femtoduino/femto-beacon/Eagle_Files/FemtoBeacon_r2.0.0/femto-beacon-picture.jpg

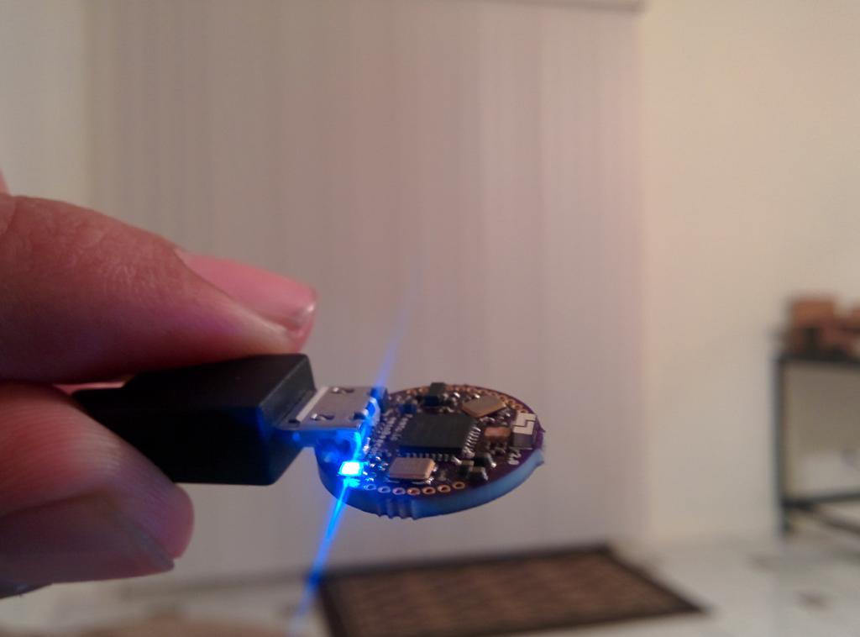
Eagle_Files/FemtoBeacon_r2.0.0/femto-beacon-picture.jpg
