femtoduino/femto-beacon/Blender3d_Files/femtoBeacon_r2.0.3_MolexAnt.png

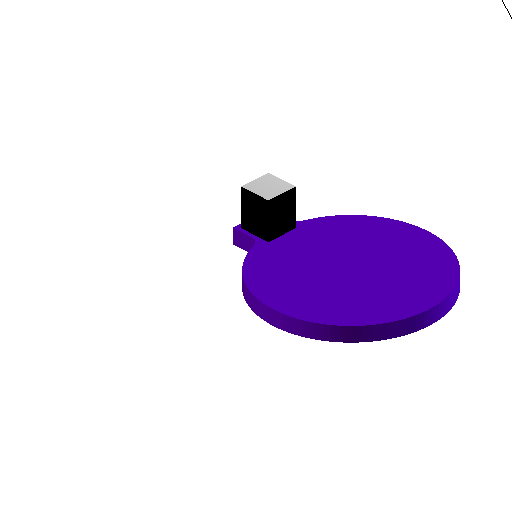
Blender3d_Files/femtoBeacon_r2.0.3_MolexAnt.png
