femtoduino/femto-beacon/Blender3d_Files/MolexAnt_Texture.png

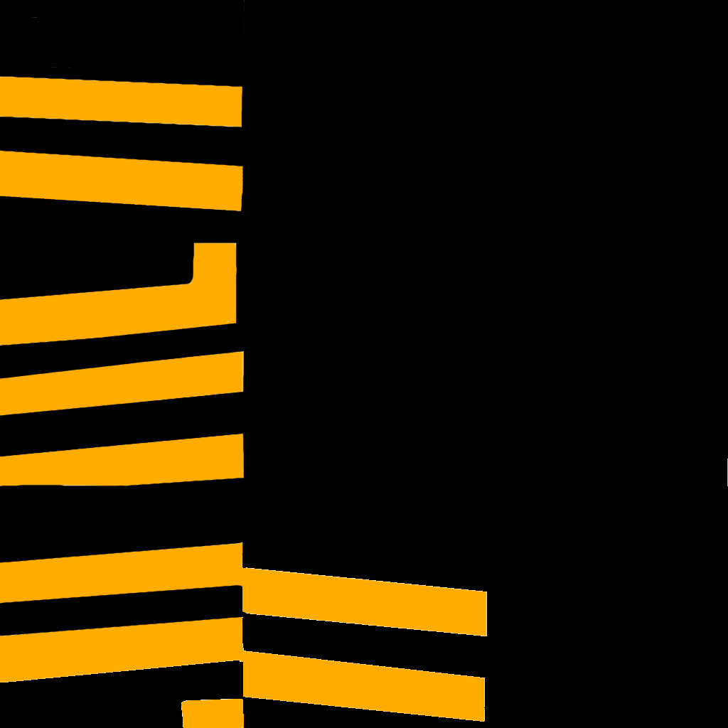
Blender3d_Files/MolexAnt_Texture.png
