femtoduino/femto-beacon/Eagle_Files/FemtoBeacon_BLE_r1.0.0/femtoBeacon_BT_art0.png

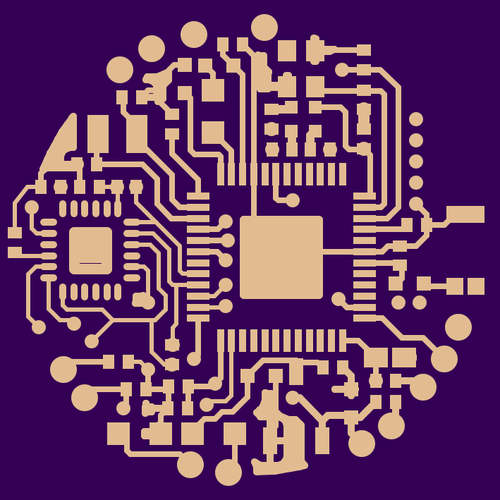
Eagle_Files/FemtoBeacon_BLE_r1.0.0/femtoBeacon_BT_art0.png
