femtoduino/femto-beacon/Eagle_Files/FemtoBeacon_BLE_r1.0.0/FemtoBeacon_coin_nRF52832_BT4.2_r1.0.0_top.png

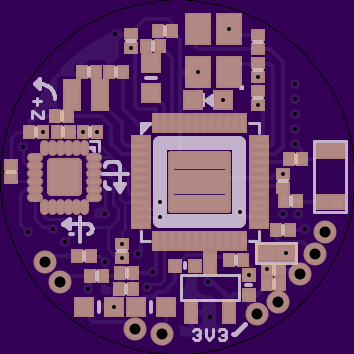
Eagle_Files/FemtoBeacon_BLE_r1.0.0/FemtoBeacon_coin_nRF52832_BT4.2_r1.0.0_top.png
