femtoduino/femto-beacon/Eagle_Files/FemtoBeacon_BT5_r1.0.0/FemtoBeacon_BT5_r1.0.1-top.png

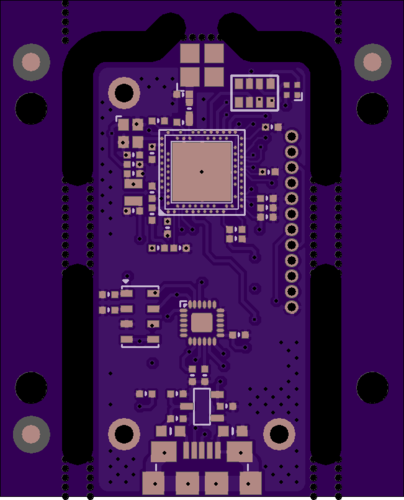
Eagle_Files/FemtoBeacon_BT5_r1.0.0/FemtoBeacon_BT5_r1.0.1-top.png
