femtoduino/femto-beacon/Eagle_Files/FemtoBeacon_r2.0.0/femtoBeacon_dongle_r2.0.6_RGB_PANELIZED-top.png

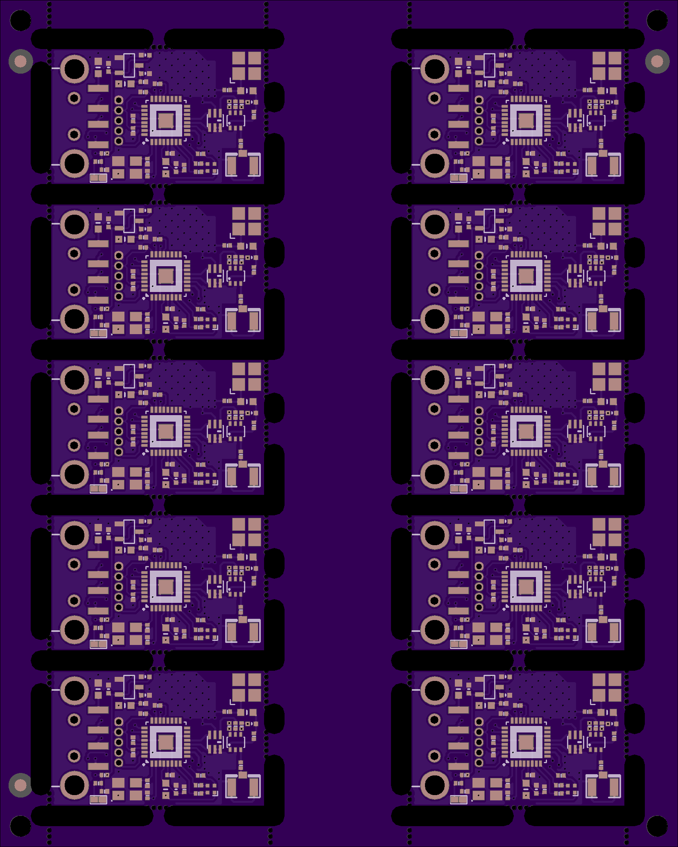
Eagle_Files/FemtoBeacon_r2.0.0/femtoBeacon_dongle_r2.0.6_RGB_PANELIZED-top.png
