femtoduino/femto-beacon/Eagle_Files/FemtoBeacon_r2.0.0/femtoBeacon_PRO_r3.0.0-top.png

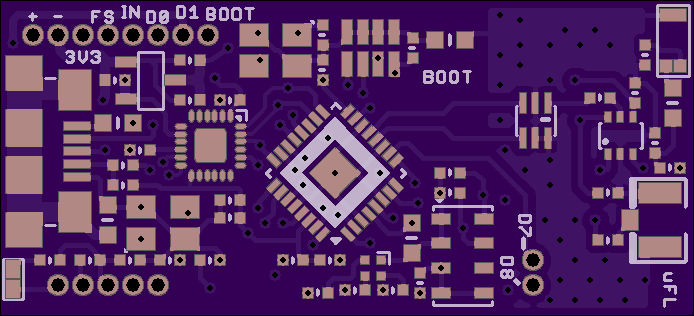
Eagle_Files/FemtoBeacon_r2.0.0/femtoBeacon_PRO_r3.0.0-top.png
