femtoduino/femto-beacon/Eagle_Files/FemtoBeacon_r2.0.0/femtoBeacon_r2.0.0-bottom.png

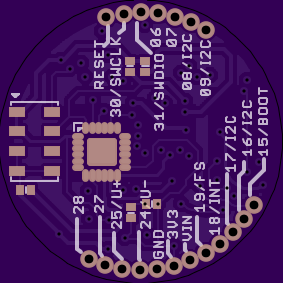
Eagle_Files/FemtoBeacon_r2.0.0/femtoBeacon_r2.0.0-bottom.png
