femtoduino/femto-beacon/Eagle_Files/FemtoBeacon_r2.0.0/femtoBeacon_r2.0.0-top.png

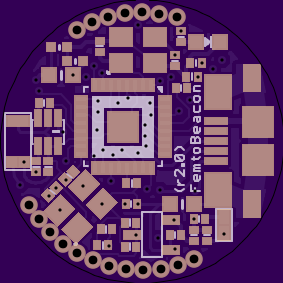
Eagle_Files/FemtoBeacon_r2.0.0/femtoBeacon_r2.0.0-top.png
