femtoduino/femto-beacon/Eagle_Files/FemtoBeacon_r2.0.0/femtoBeacon_r2.0.7_RGB_OTG_PANELIZED-top.png

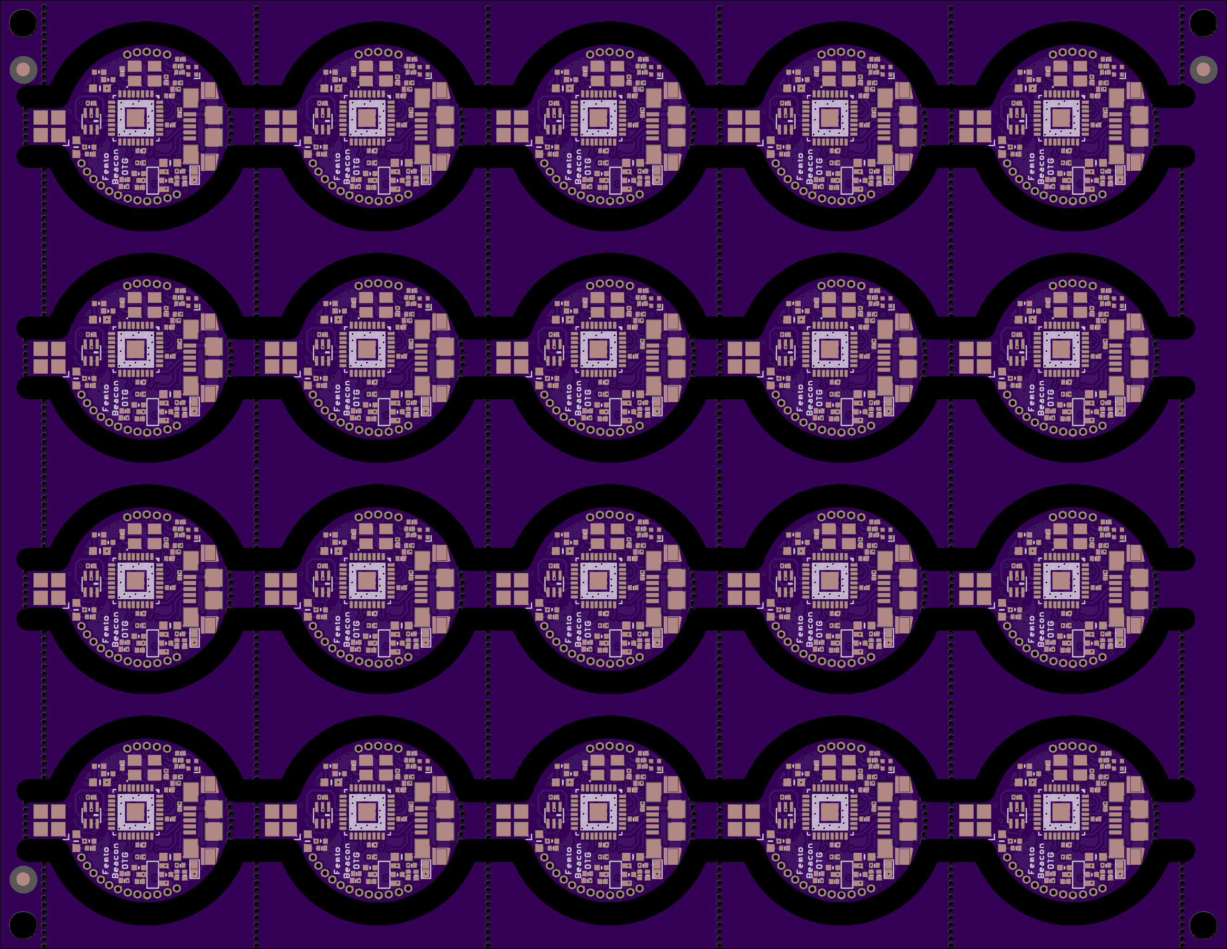
Eagle_Files/FemtoBeacon_r2.0.0/femtoBeacon_r2.0.7_RGB_OTG_PANELIZED-top.png
