femtoduino/femto-beacon/examples/sam-r21-blink/sam0/drivers/dac/docimg/dac_block_diagram_saml.gif

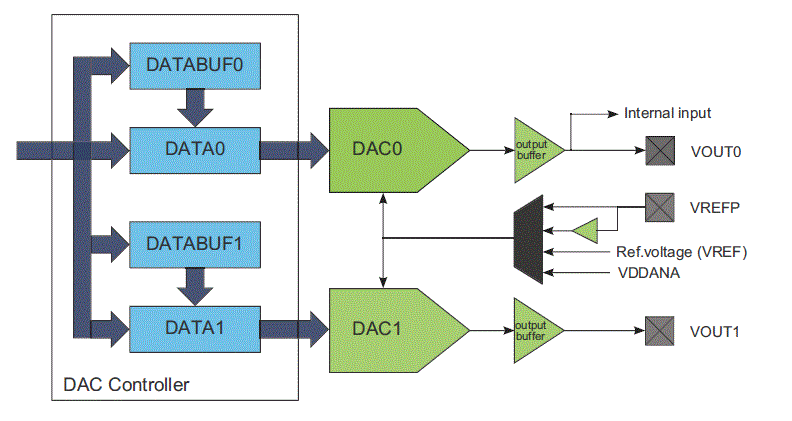
examples/sam-r21-blink/sam0/drivers/dac/docimg/dac_block_diagram_saml.gif
