femtoduino/femto-beacon/Nordic_Files/nRF52 Preview Development Kit - Hardware files 1_1_0/PCA10036-nRF52832 Bluetooth Smart,ANT,2.4GHz RF Preview Development Board 1_1_0/Production files/BOM/PCA10036_BOM.xls

Bill of material
PCB: | PCA10036
Version: | 1.1.0
Designator | Value | Description | Footprint Doc | Manufacturer | Manufacturer Part Number
Bat1 | Bat Holder CR2032 | Bat Holder CR2032 SMD | CR2032_HOLDER_SMD | Keystone | 3002
C1, C2, C11, C12 | 12pF | Capacitor, NP0, ±2% | 0402
C3 | 0.8pF | Capacitor, NP0, ±5% | 0402
C4, C5, C8, C18, C19, C21, C24, C25, C26, C27, C28, C29, C32, C34, C35, C36, C38, C39, C40, C41, C44, C45, C46, C47 | 100nF | Capacitor, X7R, ±10% | 0402
C6, C13 | N.C. | Not mounted | 0402
C7 | 100pF | Capacitor, NP0, ±5% | 0402
C9 | 4.7µF | Capacitor, X5R, ±10% | 0603
C10, C16, C17 | 1.0µF | Capacitor, X7R, ±10% | 0603
C15 | 1.2pF | Capacitor, NP0, ±0.1pF | 0402
C20, C31, C33 | 10µF | Capacitor, X5R, ±20% | 0603
C22, C23 | 18pF | Capacitor, NP0, ±5% | 0402
C30 | 10nF | Capacitor, X7R, ±10% | 0402
C37 | 10pF | Capacitor, NP0, ±2% | 0402
C42, C43 | 130pF | Capacitor, NP0, ±5% | 0402
C48, C49, C50, C51 | 1.0µF | Capacitor, X5R, ±5% | 0402
D1 | SD103ATW-7-F | Surface Mount Schottky Barrier Diode Array | SOT-363 | Diodes Incorporated | SD103ATW-7-F
D2 | PRTR5V0U2X | Ultra low capacitance double rail-to-rail ESD protection diode | SOT-143B | NXP | PRTR5V0U2X
D3, D4, D5, D6 | 1PS79SB30.115 | Diode Schottky Vf=0.38, Vr=40V, If=200mA, Ir=500nA | SOD-523 | NXP | 1PS79SB30.115
J1 | MM8130-2600 | Coaxial Connector with Switch | COAXIAL-SWF | Murata | MM8130-2600
J2 | MicroUSB-B | MicroUSB-B-SMT | FCI_10118193-0001LF | FCI | 10118193-0001LF
L1 | 3.9nH | Inductor, 170mA, ±0.1nH | 0402 | Murata | LQP15MN3N9B02D
L2 | 10µH | Inductor, 80mA, ±10% | 0603 | Taiyo Yuden | LBMF1608T100K
L3 | 15nH | Inductor, 320mA, ±5% | 0402 | Taiyo Yuden | HK100515NJ-T
LD5 | LTST-C195KGJRKT | Ultra bright AlInGaP Bi-Color LED | LED_DUAL_0606 | Lite-On Inc | LTST-C195KGJRKT
LED1, LED2, LED3, LED4 | L0603G | LED 0603, EL19-21SYGC | 0603 | Everlight | 19-21SYGC/S530-E1/TR8
P1, P3 | Socket 1x8 | Socket 1x8, 2.54mm (100mil), SMD | SOCKET_1x8_SMD | Samtec | SSM-108-F-SV-P-TR
P2 | Socket 1x6 | Socket 1x6, 2.54mm (100mil), SMD | SOCKET_1x6_SMD | Samtec | SSM-106-F-SV-P-TR
P4 | Socket 1x10 | Socket 1x10, 2.54mm (100mil), SMD | SOCKET_1x10_SMD | Samtec | SSM-110-F-SV-P-TR
P5 | Pin Hdr 2x3 | Pin Header 2x3, 2.54mm (100mil) SMD | Molex 15-91-2060 | Molex | 15-91-2060
P6 | Socket 1x9 | Socket 1x9, 2.54mm (100mil), SMD | SOCKET_1x9_SMD | Samtec | SSM-109-L-SV
P7, P9, P20 | Pin List 1x8 | Pin List 1x8, 2.54mm (100mil), SMD | LIST_1x8_SMD
P8 | Pin List 1x6 | Pin List 1x6, 2.54mm (100mil), SMD | LIST_1x6_SMD
P10 | Pin List 1x10 | Pin List 1x10, 2.54mm (100mil), SMD | LIST_1x10_SMD
P11 | Socket 2x3 | Socket 2x3, 2.54mm (100mil), SMD | SOCKET_2x3_SMD-2.54mm-bottom | Samtec | SSM-103-F-DV-P-TR
P12 | Pin List 1x9 | Pin List 1x9, 2.54mm (100mil), SMD | LIST_1x9_SMD
P13, P15 | Pin Header 2x8 | Pin Header 2x8, 2.54mm (100mil) | HDR_2x8
P14 | Pin Header 2x6 | Pin Header 2x6, 2.54mm (100mil) | HDR_2x6
P16 | Pin Header 2x10 | Pin Header 2x10, 2.54mm (100mil) | HDR_2x10
P17 | Pin Header 2x9 | Pin Header 2x9, 2.54mm (100mil) | HDR_2x9
P18, P19 | FTSH-105 | SAMTEC - CONN HEADER 10POS DUAL .05" SMD KEYING SHROUD | FTSH-105 | Samtec | FTSH-105-01-F-DV-K
P21, P22 | Pin List 1x2, Angled | Pin List 1x2, 2.54mm (100mil), Right Angled, SMD | LIST_ANG_1x2-SMD-2.54MM
P23 | Pin List 1x2, Angled | Pin List 1x2, 2.00mm, Right Angled, SMD | LIST_ANG_1x2-SMD-2.00MM
Q1, Q2 | FDG6321C | Fairchild, FDG6321C, Dual N & P Channel Digital FET | SC70-6 | Fairchild | FDG6321C
R1, R2, R3, R4, R19, R20 | 220R | Resistor, ±1%, 0.063W | 0402
R5, R8, R9, R10, R11, R12 | 10k | Resistor, ±1%, 0.063W | 0402
R6, R27, R28, R37 | N.C. | Not mounted | 0402
R7 | 47k | Resistor, ±1%, 0.063W | 0402
R13, R14 | 39R | Resistor, ±1%, 0.063W | 0402
R15, R16 | 150R | Resistor, ±1%, 0.063W | 0402
R17 | 6k8 | Resistor, ±1%, 0.063W | 0402
R18 | 1k | Resistor, ±1%, 0.063W | 0402
R21, R22, R23, R24, R29, R30 | 4k7 | Resistor, ±1%, 0.063W | 0402
R25, R26, R38 | 0R | Resistor, ±5%, 0.063W | 0402
R31, R32 | 12k | Resistor, ±1%, 0.063W | 0402
R33, R34, R35, R36 | 100k | Resistor, ±1%, 0.063W | 0402
R39 | 1M0 | Resistor, ±1%, 0.063W | 0402
R40, R41, R42, R43 | 18k | Resistor, ±1%, 0.063W | 0402
SW1, SW2, SW3, SW4, SW5 | PB SW | ALPS - SKHUALE010 - Tactile Switch, SPNO, SMD, 6.5x6.2x2.5mm | ALPS_SKHUxxx010_WO_GND | Alps | SKHUALE010
SW6 | Switch | SMD slide Switch (ON-ON) | JS202011SCQN | C&K Components | JS202011SCQN
U1 | nRF52832-QFAA | Multi-protocol Bluetooth Low Energy and 2.4GHz proprietary system-on-chip | QFN-48 | Nordic Semiconductor | nRF52832-QFAA
U2 | ATSAM3U2CA-AU | IC MCU 32bit 128kB flash 100LQFP | LQFP-100 | Atmel | ATSAM3U2CA-AU
U3 | AP7333-33SAG-7 | 300mA, Low Quiescent Current, Fast Transient Low Dropout Linear Regulator | SOT-23-3 | Diodes Incorporated | AP7333-33SAG-7
U4, U5, U6 | NX3DV2567 | Low-ohmic four-pole double-throw analog switch | XQFN-16 | NXP Semiconductors | NX3DV2567GU
U7 | PCAL6408A | 8-bit I2C-bus I/O expander with interrupt output | XQFN-16 | NXP Semiconductors | PCAL6408AHK
X1 | 32MHz | XTAL SMD 2016, 32MHz, Cl=8pF, Tol: ±10ppm, Stab: ±10ppm | XTAL_2016 | Epson Toyocom | Q22FA12800025
X2 | 32.768kHz | EPSON TOYOCOM - FC-135 32.768KHZ ±20PPM,9.0PF - CRYSTAL, SM, WATCH | XTAL_3215 | Epson Toyocom | FC-135 32.768KHZ ±20PPM,9.0PF
X3 | 12MHz | XTAL SMD 3225, 12MHz, 18pF, ±30ppm | BT-XTAL_3225 | TXC Corporation | 7M-12.000MAAJ-T
