femtoduino/femto-beacon/examples/sam-r21-blink/sam0/drivers/system/docimg/performance_level_transition.gif

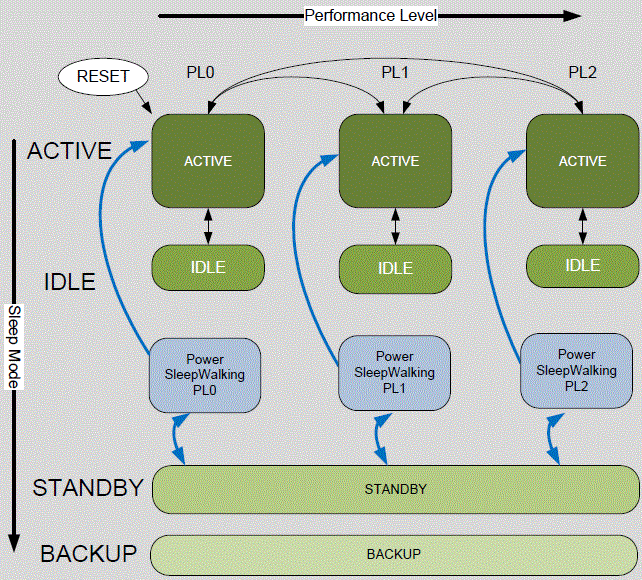
examples/sam-r21-blink/sam0/drivers/system/docimg/performance_level_transition.gif
