femtoduino/femto-beacon/Eagle_Files/FemtoBeacon_BLE_r1.0.0/femtoBeacon_board_nRF52832_BT4.2_r1.0.0.brd

## EAGLE design Eagle_Files/FemtoBeacon_BLE_r1.0.0/femtoBeacon_board_nRF52832_BT4.2_r1.0.0.brd (2018-01-04)

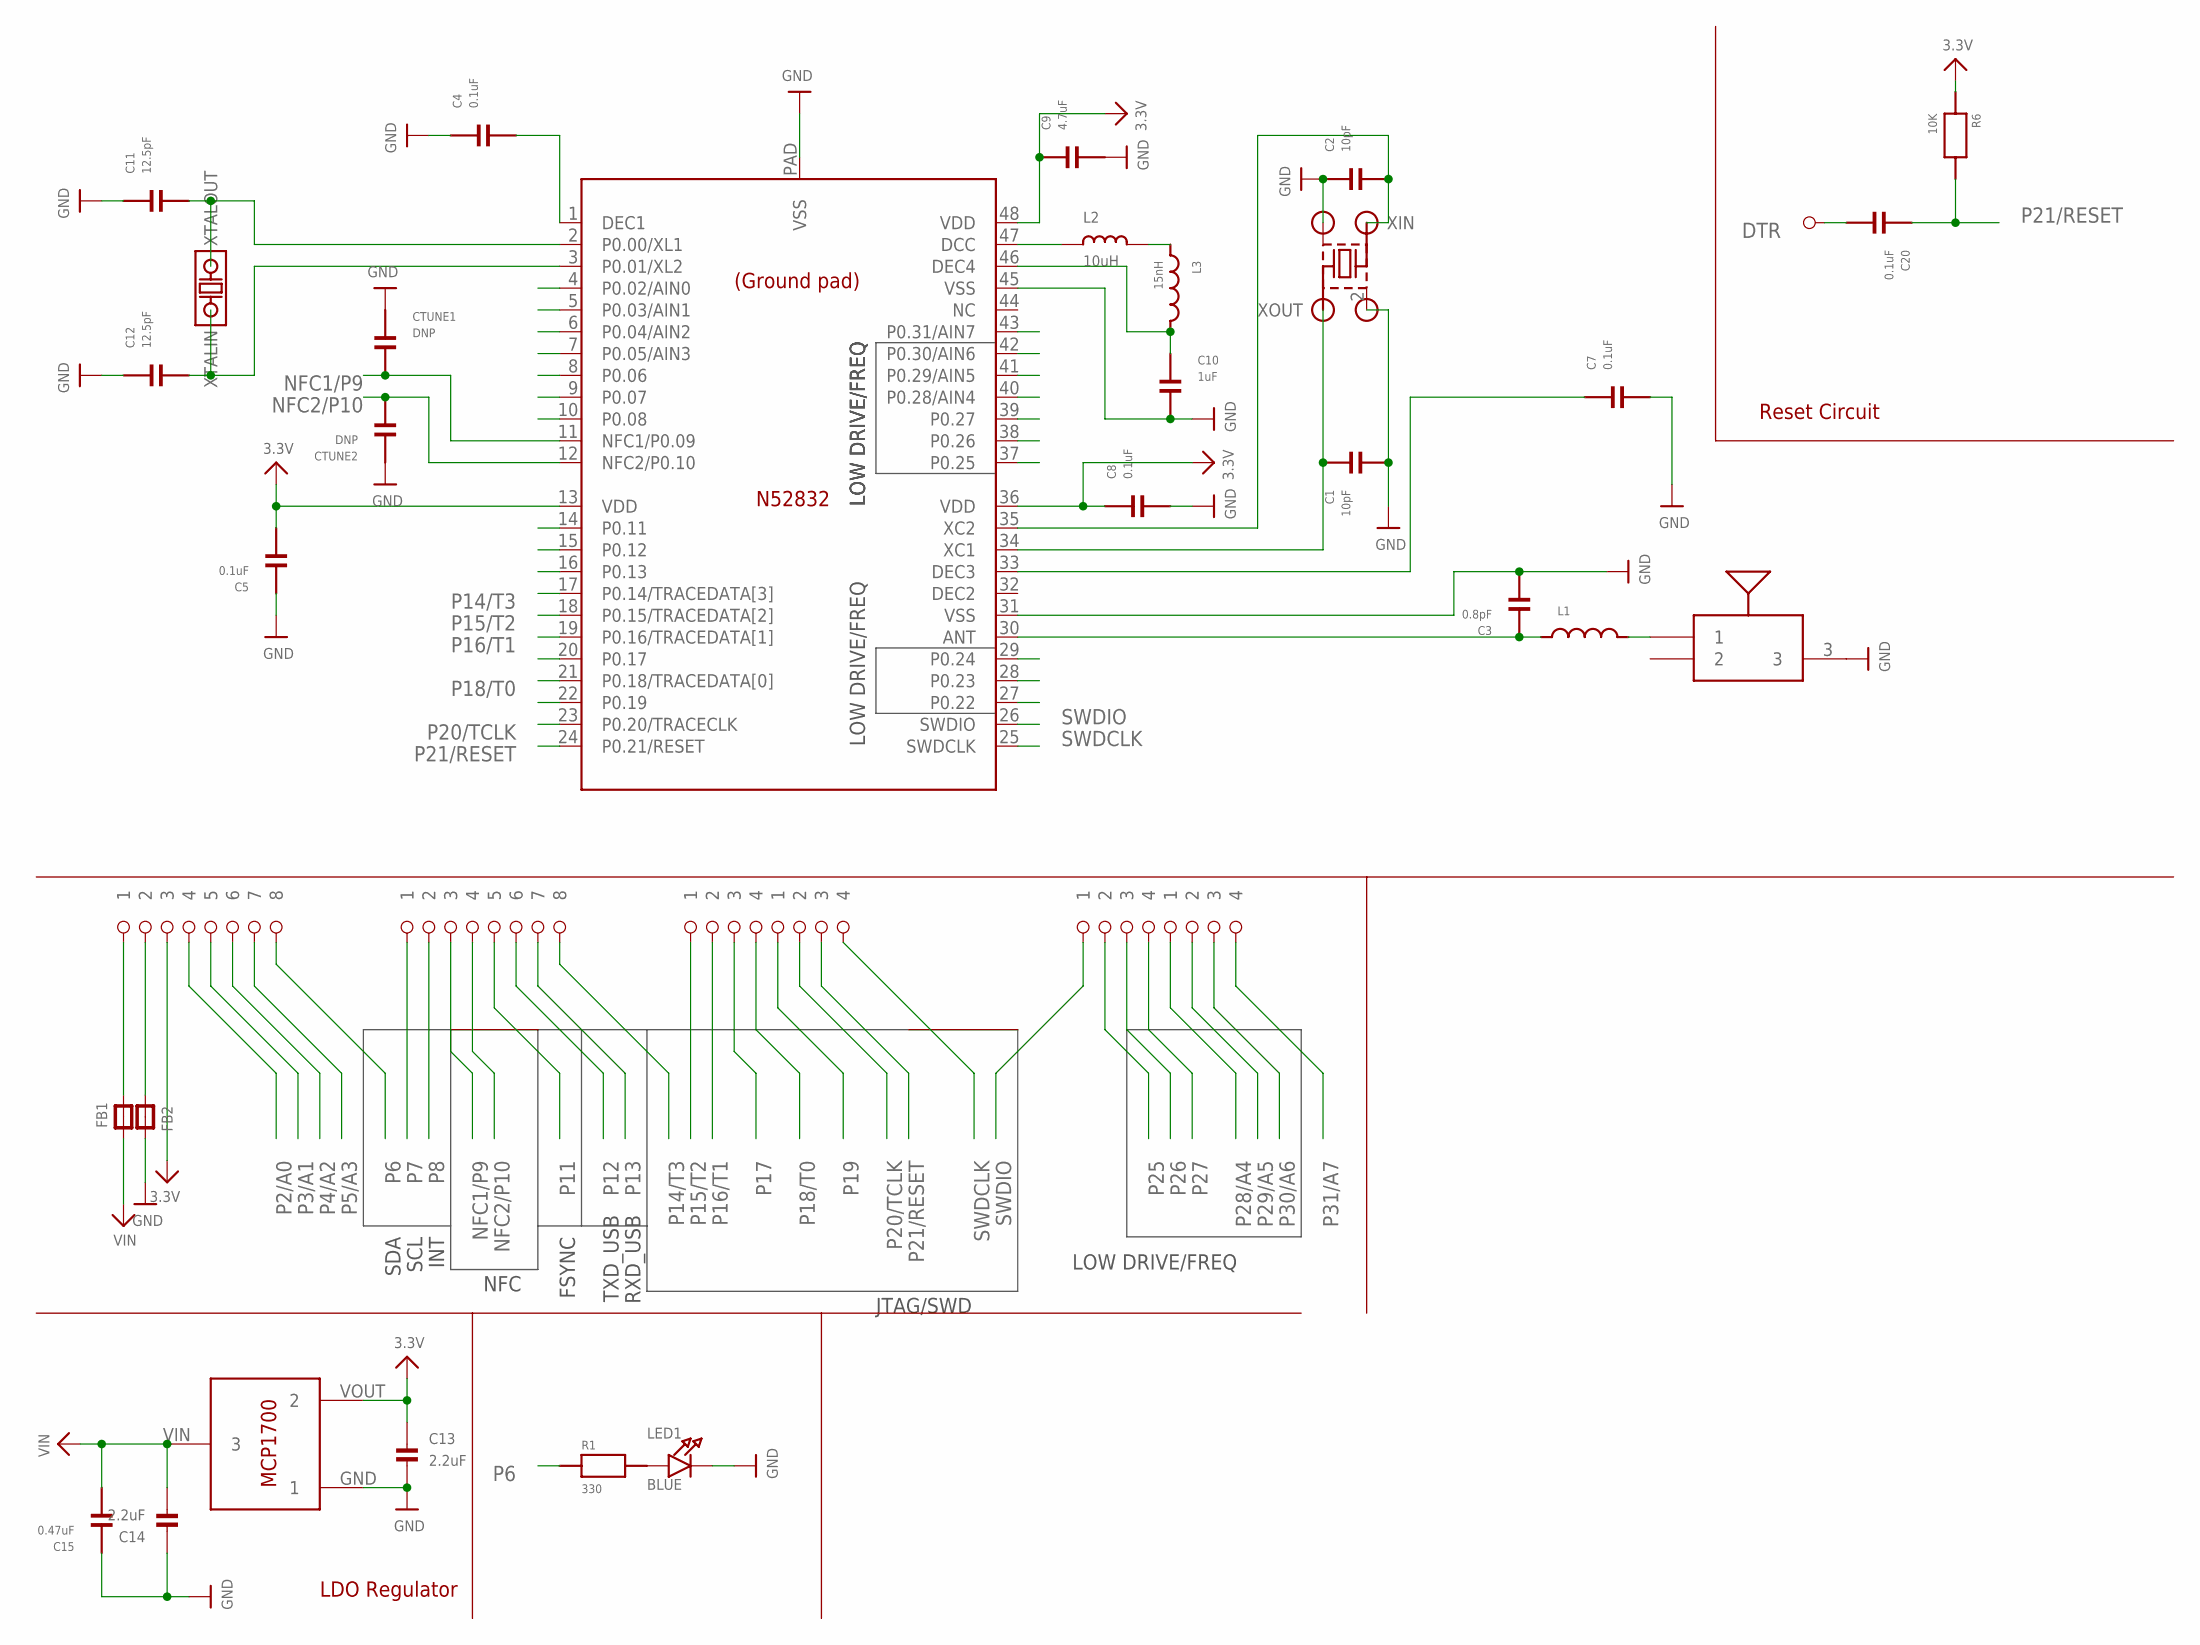
[picture p57: schematic femtoBeacon_board_nRF52832_BT4.2_r1.0.0.sch, sheet 1]

Parts:
ANTBAR: PULSE_ANT_2.4GHZ; ANT_BAR
C1, C2: 10pF; PART
C3: 0.8pF; PART
C4, C5, C7, C8, C20: 0.1uF; PART
C9: 4.7uF; PART
C10: 1uF; PART
C11, C12: 12.5pF; PART
C13, C14: 2.2uF; _0402MP
C15: 0.47uF; PART
CTUNE1, CTUNE2: DNP; PART
FB1, FB2: FERRITE_0603MP; _0603MP
IC1: NRF52832_QFN48; QFN48
L1: INDUCTOR_FIXED_0201; PART
L2: 10uH; _0603MP
L3: 15nH; PART
LED1: BLUE; CHIPLED_0603_NOOUTLINE
PIN4: 1X1_ROUND
PINS1, PINS2: 1X8_ROUND
PINS3A, PINS3B, PINS4A, PINS4B: 1X4_ROUND
R1: 330; PART
R6: 10K; PART
U$4: MCP1700T-3302E/TT
U$53: ABS06-107-32.768KHZ-T
XTAL: 32MHz; ABM11

Connections:
3.3V: C5.2, C8.1, C9.1, C13.1, IC1.13 (VDD), IC1.36 (VDD), IC1.48 (VDD), PINS1.P$3 (3), R6.1, U$4.VOUT (2); also elsewhere on the board
DTR: C20.2, PIN4.P$1
GND: ANTBAR.3, C1.2, C2.1, C3.2, C4.1, C5.1, C7.2, C8.2, C9.2, C10.2, C11.1, C12.1, C13.2, C14.1, C15.1, CTUNE1.1, CTUNE2.1, FB2.2, IC1.31 (VSS), IC1.45 (VSS), IC1.PAD (VSS), LED1.C, U$4.GND (1), XTAL.2 (GND), XTAL.4 (GND); also elsewhere on the board
unnamed: C4.2, IC1.1 (DEC1)
unnamed: L2.2, L3.1
unnamed: IC1.47 (DCC), L2.1
unnamed: C7.1, IC1.33 (DEC3)
unnamed: FB2.1, PINS1.P$2 (2)
unnamed: C10.1, IC1.46 (DEC4), L3.2
unnamed: LED1.A, R1.2
unnamed: FB1.2, PINS1.P$1 (1)
unnamed: C3.1, IC1.30 (ANT), L1.1
NFC1/P9: CTUNE1.2, IC1.11 (NFC1/P0.09), PINS2.P$3 (3)
NFC2/P10: CTUNE2.2, IC1.12 (NFC2/P0.10), PINS2.P$4 (4)
P0/XIN32: C11.2, IC1.2 (P0.00/XL1), U$53.2 (XTALOUT)
P1/XOUT32: C12.2, IC1.3 (P0.01/XL2), U$53.1 (XTALIN)
P2/A0: IC1.4 (P0.02/AIN0), PINS1.P$4 (4)
P3/A1: IC1.5 (P0.03/AIN1), PINS1.P$5 (5)
P4/A2: IC1.6 (P0.04/AIN2), PINS1.P$6 (6)
P5/A3: IC1.7 (P0.05/AIN3), PINS1.P$7 (7)
P6: IC1.8 (P0.06), PINS1.P$8 (8), R1.1; also elsewhere on the board
P7: IC1.9 (P0.07), PINS2.P$1 (1); also elsewhere on the board
P8: IC1.10 (P0.08), PINS2.P$2 (2); also elsewhere on the board
P11: IC1.14 (P0.11), PINS2.P$5 (5); also elsewhere on the board
P12: IC1.15 (P0.12), PINS2.P$6 (6)
P13: IC1.16 (P0.13), PINS2.P$7 (7)
P14/T3: IC1.17 (P0.14/TRACEDATA[3]), PINS2.P$8 (8)
P15/T2: IC1.18 (P0.15/TRACEDATA[2]), PINS3A.P$1 (1)
P16/T1: IC1.19 (P0.16/TRACEDATA[1]), PINS3A.P$2 (2)
P17: IC1.20 (P0.17), PINS3A.P$3 (3)
P18/T0: IC1.21 (P0.18/TRACEDATA[0]), PINS3A.P$4 (4)
P19: IC1.22 (P0.19), PINS3B.P$1 (1)
P20/TCLK: IC1.23 (P0.20/TRACECLK), PINS3B.P$2 (2)
P21/RESET: C20.1, IC1.24 (P0.21/RESET), PINS3B.P$3 (3), R6.2
P22: IC1.27 (P0.22)
P23: IC1.28 (P0.23)
P24: IC1.29 (P0.24)
P25: IC1.37 (P0.25), PINS4A.P$2 (2)
P26: IC1.38 (P0.26), PINS4A.P$3 (3)
P27: IC1.39 (P0.27), PINS4A.P$4 (4)
P28/A4: IC1.40 (P0.28/AIN4), PINS4B.P$1 (1)
P29/A5: IC1.41 (P0.29/AIN5), PINS4B.P$2 (2)
P30/A6: IC1.42 (P0.30/AIN6), PINS4B.P$3 (3)
P31/A7: IC1.43 (P0.31/AIN7), PINS4B.P$4 (4)
RF: ANTBAR.1, L1.2
SWDCLK: IC1.25 (SWDCLK), PINS3B.P$4 (4)
SWDIO: IC1.26 (SWDIO), PINS4A.P$1 (1)
VIN: C14.2, C15.2, FB1.1, U$4.VIN (3)
XIN: C1.1, IC1.34 (XC1), XTAL.3 (XOUT)
XOUT: C2.2, IC1.35 (XC2), XTAL.1 (XIN)

Notes on the sheet:
LOW DRIVE/FREQ
SDA
SCL
INT
FSYNC
TXD_USB
RXD_USB
Reset Circuit
LDO Regulator
JTAG/SWD
NFC
