femtoduino/femto-beacon/Eagle_Files/FemtoBeacon_BLE_r1.0.0/femtoBeacon_board_nRF52832_BT4.2_r1.0.0.brd

## EAGLE design Eagle_Files/FemtoBeacon_BLE_r1.0.0/femtoBeacon_board_nRF52832_BT4.2_r1.0.0.brd (continued)

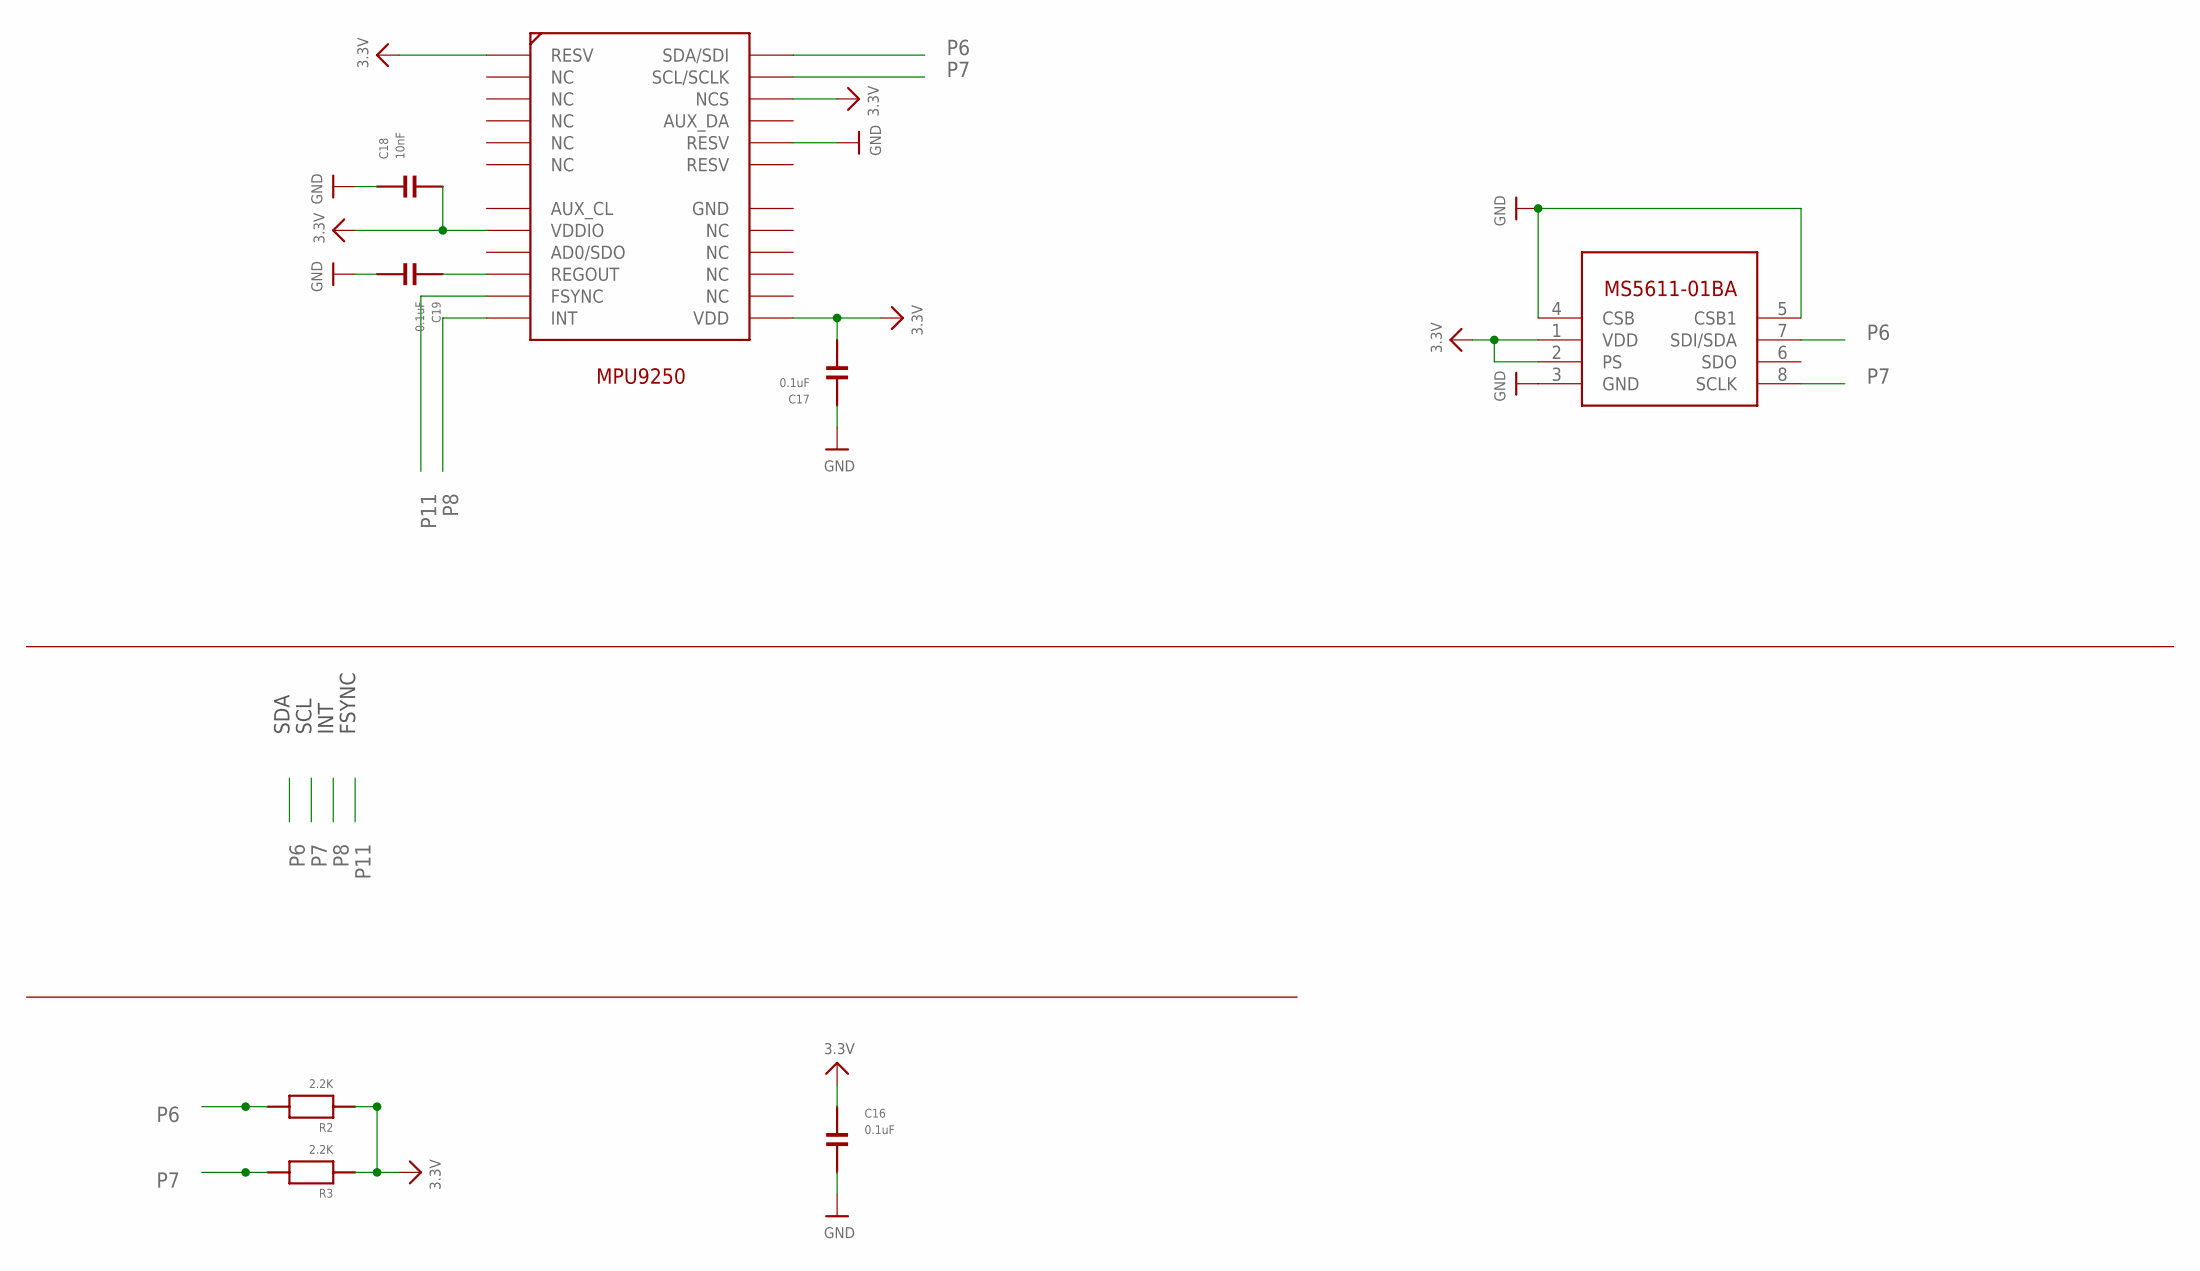
[picture p58: schematic femtoBeacon_board_nRF52832_BT4.2_r1.0.0.sch, sheet 2]

Parts:
BARO1: MS5611-01BA03
C16, C17, C19: 0.1uF; PART
C18: 10nF; PART
IMU1: MPU-9250; QFN_3X3MM
R2, R3: 2.2K; PART

Connections:
3.3V: BARO1.1 (VDD), BARO1.2 (PS), C16.1, C17.2, C18.2, IMU1.P$1 (RESV), IMU1.P$8 (VDDIO), IMU1.P$13 (VDD), IMU1.P$22 (NCS), R2.1, R3.1; also elsewhere on the board
GND: BARO1.3 (GND), BARO1.4 (CSB), BARO1.5 (CSB1), C16.2, C17.1, C18.1, C19.2, IMU1.P$20 (RESV); also elsewhere on the board
P6: BARO1.7 (SDI/SDA), IMU1.P$24 (SDA/SDI), R2.2; also elsewhere on the board
P7: BARO1.8 (SCLK), IMU1.P$23 (SCL/SCLK), R3.2; also elsewhere on the board
P8: IMU1.P$12 (INT); also elsewhere on the board
P11: IMU1.P$11 (FSYNC); also elsewhere on the board
REGOUT: C19.1, IMU1.P$10 (REGOUT)

Notes on the sheet:
MPU9250
SDA
SCL
INT
FSYNC

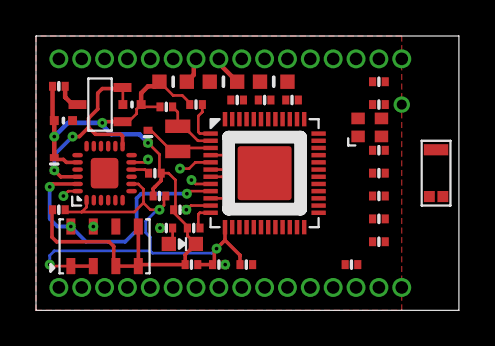
[picture p59: board femtoBeacon_board_nRF52832_BT4.2_r1.0.0.brd from above]

Board: 4 copper layers, 23.5 x 15.2 mm, 45 parts (0 on the bottom side), 48 nets.
