femtoduino/femto-beacon/Eagle_Files/FemtoBeacon_r2.0.0/femtoBeacon_dongle_r2.0.0.brd

## EAGLE design Eagle_Files/FemtoBeacon_r2.0.0/femtoBeacon_dongle_r2.0.0.brd (2017-01-18)

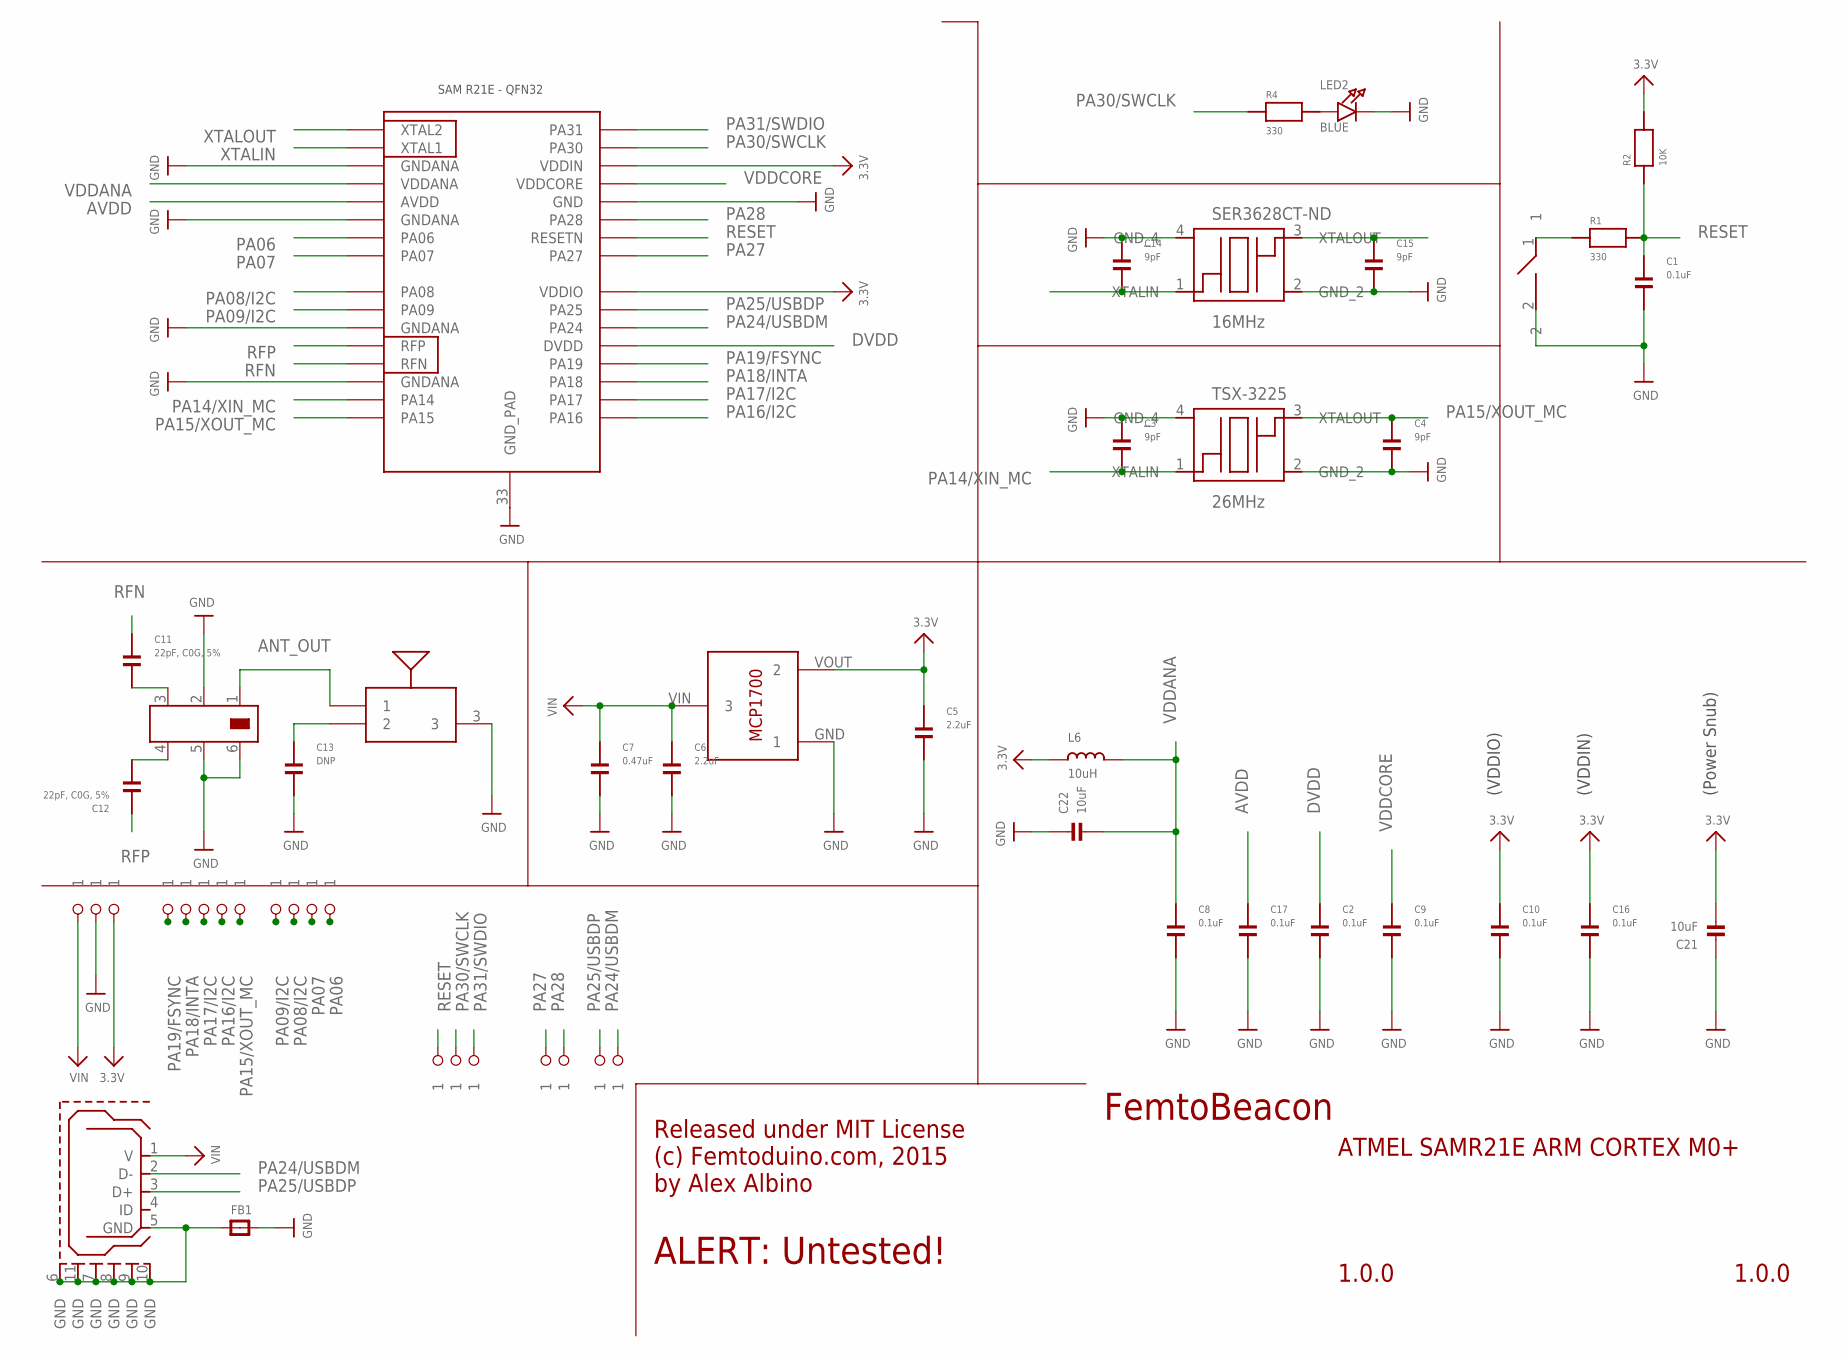
[picture p60: schematic femtoBeacon_dongle_r2.0.0.sch]

Parts:
ANT1: PULSE_ANT_2.4GHZ; ANT_BAR
BTN: DNP; SPST_SMD
C1, C8, C9, C10, C16, C17: 0.1uF; PART; DIGIKEY_PART 490-3194-1-ND
C2: 0.1uF; PART
C3, C4, C14, C15: 9pF; PART; DIGIKEY_PART 490-3194-1-ND
C5, C6: 2.2uF; PART
C7: 0.47uF; PART
C11, C12: 22pF, C0G, 5%; PART; DIGIKEY_PART 490-3194-1-ND
C13: DNP; PART; DIGIKEY_PART 490-3194-1-ND
C21, C22: 10uF; _0402MP
FB1: FERRITE_0603MP; _0603MP
L6: 10uH; _0603MP
LDO_VREG: MCP1700T-3302E/TT
LED2: BLUE; CHIPLED_0603_NOOUTLINE
R1, R4: 330; PART
R2: 10K; PART
SER3628CT-ND: 16MHz; TSX-3225
TSX-3225: 26MHz; TSX-3225
U$1, U$2, U$5, U$7, U$9, U$10, U$35, U$36, U$37, U$38, U$39, U$41, U$42, U$43, U$45, U$46, U$47, U$48, U$54: 1X1_ROUND
U$8: USB_MICROB; USB_MICROB_PACKAGE
U$12: JOHANSON_2450BM15A0015E; 0805_BALUN
U$76: ATSAMR21E18A-MUT; QFN32

Connections:
3.3V: C5.1, C10.1, C16.1, C21.2, L6.1, LDO_VREG.VOUT (2), R2.2, U$5.P$1, U$76.24 (VDDIO), U$76.30 (VDDIN)
ANT_OUT: ANT1.1, U$12.1
AVDD: C17.1, U$76.5 (AVDD)
DVDD: C2.1, U$76.21 (DVDD)
GND: ANT1.3, BTN.2, C1.2, C2.2, C3.1, C4.2, C5.2, C6.2, C7.2, C8.2, C9.2, C10.2, C13.2, C14.1, C15.2, C16.2, C17.2, C21.1, C22.1, FB1.2, LDO_VREG.GND (1), LED2.C, SER3628CT-ND.2 (GND_2), SER3628CT-ND.4 (GND_4), TSX-3225.2 (GND_2), TSX-3225.4 (GND_4), U$2.P$1, U$12.2, U$12.5, U$12.6, U$76.3 (GNDANA), U$76.6 (GNDANA), U$76.11 (GNDANA), U$76.14 (GNDANA), U$76.28 (GND), U$76.33 (GND_PAD)
unnamed: C11.2, U$12.3
unnamed: ANT1.2, C13.1
unnamed: C12.2, U$12.4
unnamed: FB1.1, U$8.5 (GND), U$8.6 (GND), U$8.7 (GND), U$8.8 (GND), U$8.9 (GND), U$8.10 (GND), U$8.11 (GND)
unnamed: LED2.A, R4.2
unnamed: BTN.1, R1.1
PA06: U$54.P$1, U$76.7 (PA06)
PA07: U$43.P$1, U$76.8 (PA07)
PA08/I2C: U$42.P$1, U$76.9 (PA08)
PA09/I2C: U$41.P$1, U$76.10 (PA09)
PA14/XIN_MC: C3.2, TSX-3225.1 (XTALIN), U$76.15 (PA14)
PA15/XOUT_MC: C4.1, TSX-3225.3 (XTALOUT), U$39.P$1, U$76.16 (PA15)
PA16/I2C: U$38.P$1, U$76.17 (PA16)
PA17/I2C: U$37.P$1, U$76.18 (PA17)
PA18/INTA: U$36.P$1, U$76.19 (PA18)
PA19/FSYNC: U$35.P$1, U$76.20 (PA19)
PA24/USBDM: U$8.2 (D-), U$9.P$1, U$76.22 (PA24)
PA25/USBDP: U$8.3 (D+), U$10.P$1, U$76.23 (PA25)
PA27: U$7.P$1, U$76.25 (PA27)
PA28: U$48.P$1, U$76.27 (PA28)
PA30/SWCLK: R4.1, U$46.P$1, U$76.31 (PA30)
PA31/SWDIO: U$47.P$1, U$76.32 (PA31)
RESET: C1.1, R1.2, R2.1, U$45.P$1, U$76.26 (RESETN)
RFN: C11.1, U$76.13 (RFN)
RFP: C12.1, U$76.12 (RFP)
VDDANA: C8.1, C22.2, L6.2, U$76.4 (VDDANA)
VDDCORE: C9.1, U$76.29 (VDDCORE)
VIN: C6.1, C7.1, LDO_VREG.VIN (3), U$1.P$1, U$8.1 (V)
XTALIN: C14.2, SER3628CT-ND.1 (XTALIN), U$76.2 (XTAL1)
XTALOUT: C15.1, SER3628CT-ND.3 (XTALOUT), U$76.1 (XTAL2)

Notes on the sheet:
FemtoBeacon
1.0.0
ATMEL SAMR21E ARM CORTEX M0+
Released under MIT License (c) Femtoduino.com, 2015 by Alex Albino
ALERT: Untested!
(Power Snub)
(VDDIO)
(VDDIN)

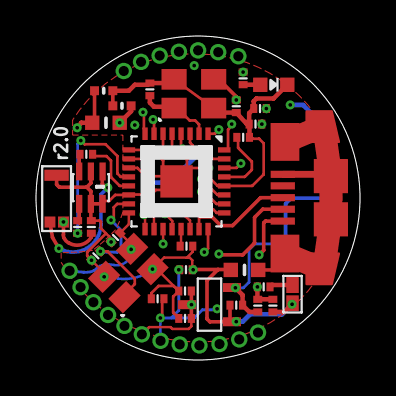
[picture p61: board femtoBeacon_dongle_r2.0.0.brd from above]

Board: 4 copper layers, 18.0 x 18.0 mm, 52 parts (0 on the bottom side), 35 nets.
