femtoduino/femto-beacon/Eagle_Files/FemtoBeacon_r2.0.0/femtoBeacon_r2.0.7_RGB_OTG_PANELIZED.brd

## EAGLE design Eagle_Files/FemtoBeacon_r2.0.0/femtoBeacon_r2.0.7_RGB_OTG_PANELIZED.brd (2018-01-12)

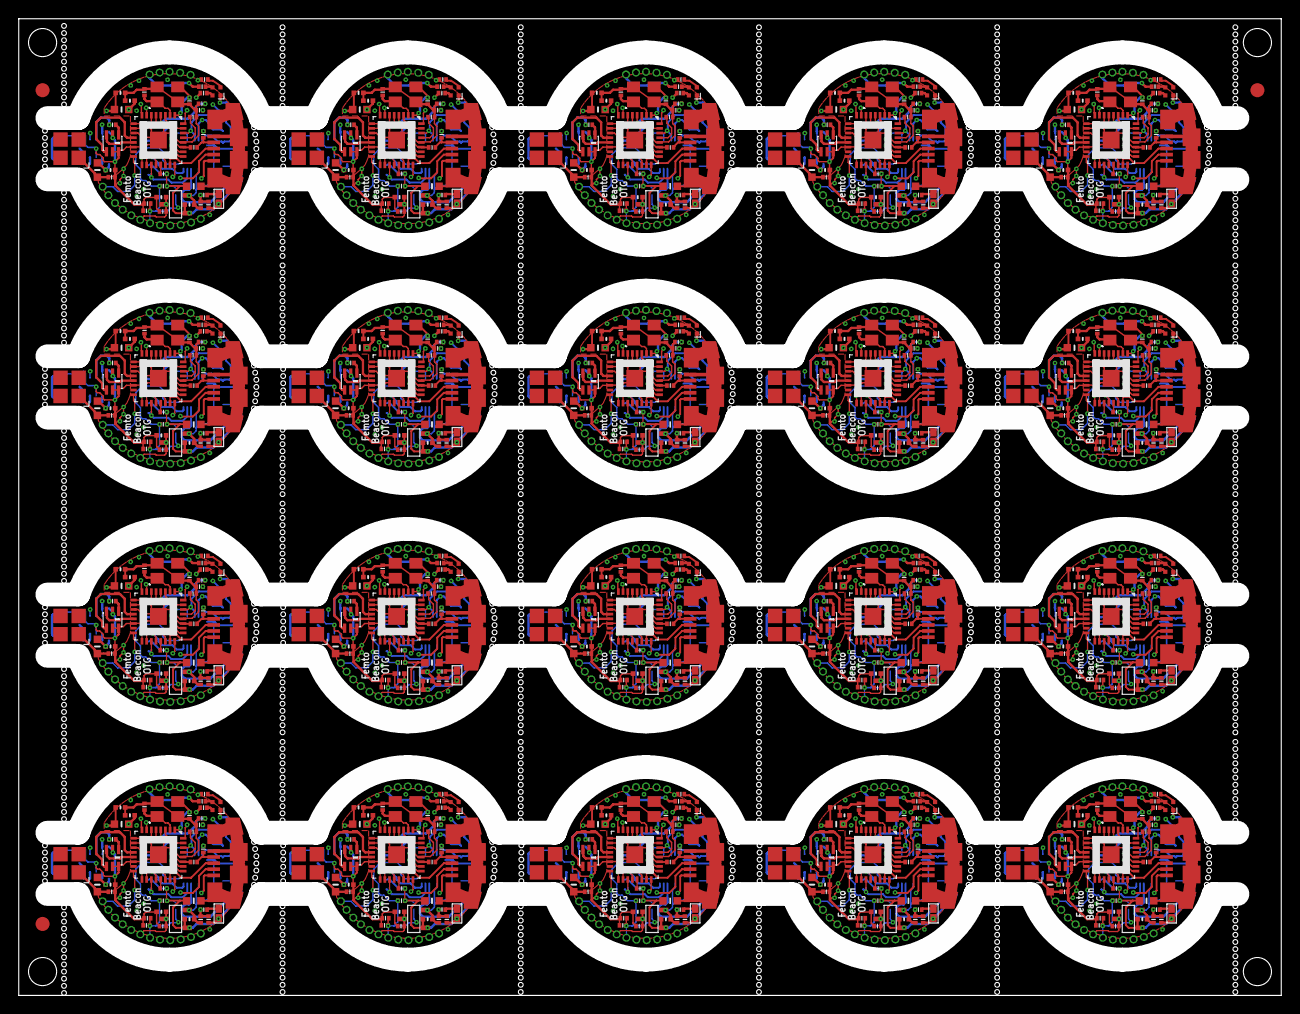
[picture p62: board femtoBeacon_r2.0.7_RGB_OTG_PANELIZED.brd from above]

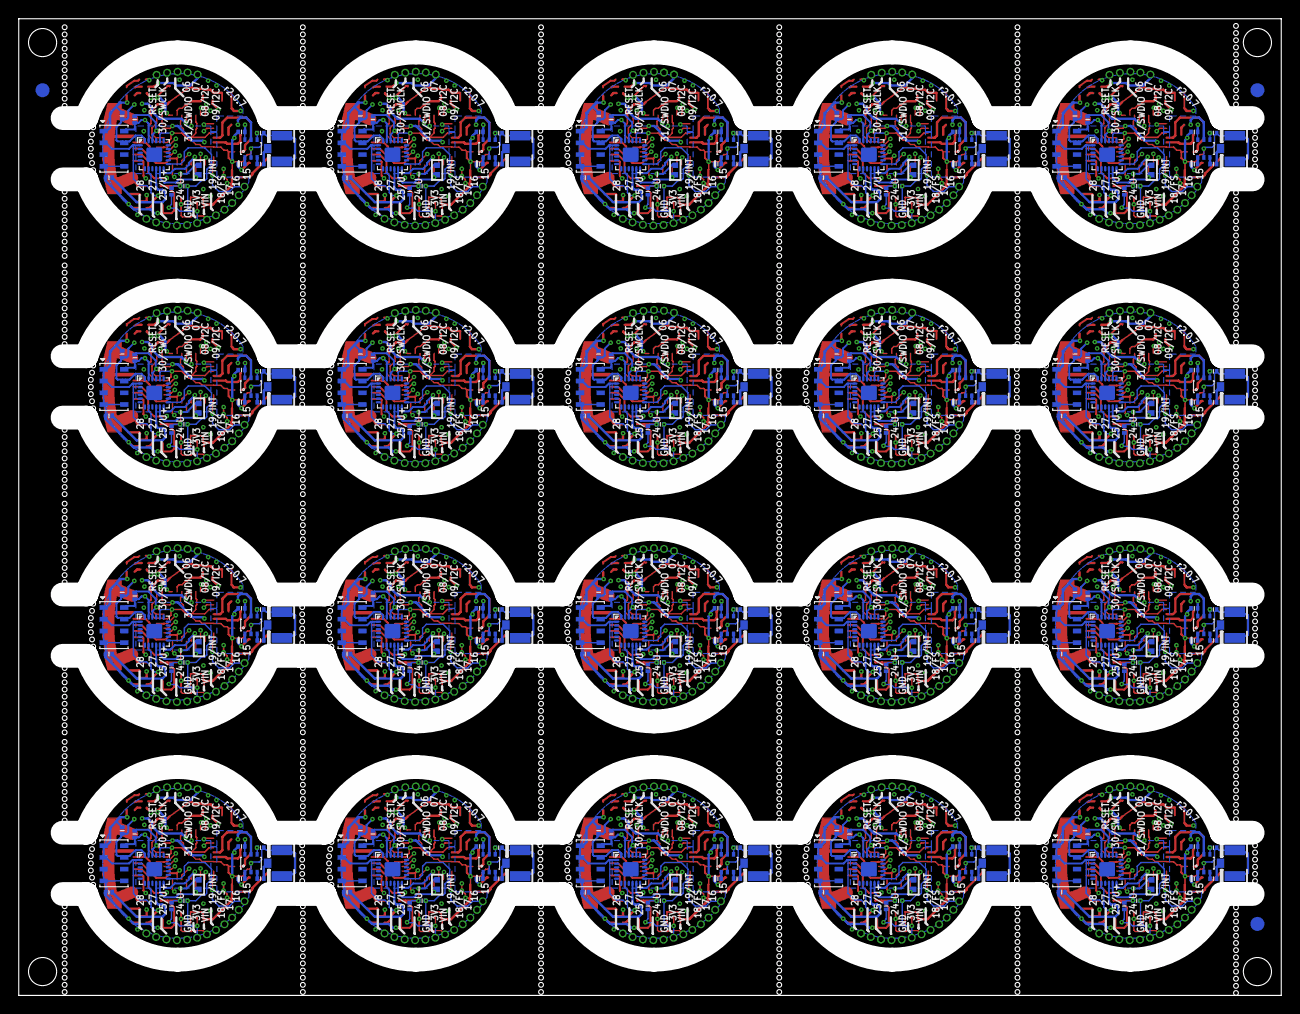
[picture p63: board femtoBeacon_r2.0.7_RGB_OTG_PANELIZED.brd from below]

Board: 4 copper layers, 134.6 x 104.1 mm, 1346 parts (283 on the bottom side), 820 nets.

Parts:
ANT_SMD, ANT_SMD1, ANT_SMD2, ANT_SMD3, ANT_SMD4, ANT_SMD5, ANT_SMD6, ANT_SMD7, ANT_SMD8, ANT_SMD9, ANT_SMD10, ANT_SMD11, ANT_SMD12, ANT_SMD13, ANT_SMD14, ANT_SMD15, ANT_SMD16, ANT_SMD17, ANT_SMD18, ANT_SMD19: 0479480001
ASWITCH, ASWITCH1, ASWITCH2, ASWITCH3, ASWITCH4, ASWITCH5, ASWITCH6, ASWITCH7, ASWITCH8, ASWITCH9, ASWITCH10, ASWITCH11, ASWITCH12, ASWITCH13, ASWITCH14, ASWITCH15, ASWITCH16, ASWITCH17, ASWITCH18, ASWITCH19: AS222-92LF
BALUN, BALUN1, BALUN2, BALUN3, BALUN4, BALUN5, BALUN6, BALUN7, BALUN8, BALUN9, BALUN10, BALUN11, BALUN12, BALUN13, BALUN14, BALUN15, BALUN16, BALUN17, BALUN18, BALUN19: JOHANSON_2450BM15A0015E; 0805_BALUN
BARO, BARO1, BARO2, BARO3, BARO4, BARO5, BARO6, BARO7, BARO8, BARO9, BARO10, BARO11, BARO12, BARO13, BARO14, BARO15, BARO16, BARO17, BARO18, BARO19: MS5611-01BA03
BTN, BTN1, BTN2, BTN3, BTN4, BTN5, BTN6, BTN7, BTN8, BTN9, BTN10, BTN11, BTN12, BTN13, BTN14, BTN15, BTN16, BTN17, BTN18, BTN19: DNP; SPST_SMD
C1, C2, C3, C4, C8, C9, C10, C16, C17, C27, C28, C29, C30, C32, C33, C34, C35, C38, C42, C43, C51, C52, C56, C57, C58, C59, C60, C63, C67, C68, C76, C77, C81, C82, C83, C84, C85, C88, C92, C93, C101, C102, C106, C107, C108, C109, C110, C113, C117, C118, C126, C127, C131, C132, C133, C134, C135, C138, C142, C143, C151, C152, C156, C157, C158, C159, C160, C163, C167, C168, C176, C177, C181, C182, C183, C184, C185, C188, C192, C193, C201, C202, C206, C207, C208, C209, C210, C213, C217, C218, C226, C227, C231, C232, C233, C234, C235, C238, C242, C243, C251, C252, C256, C257, C258, C259, C260, C263, C267, C268, C276, C277, C281, C282, C283, C284, C285, C288, C292, C293, C301, C302, C306, C307, C308, C309, C310, C313, C317, C318, C326, C327, C331, C332, C333, C334, C335, C338, C342, C343, C351, C352, C356, C357, C358, C359, C360, C363, C367, C368, C376, C377, C381, C382, C383, C384, C385, C388, C392, C393, C401, C402, C406, C407, C408, C409, C410, C413, C417, C418, C426, C427, C431, C432, C433, C434, C435, C438, C442, C443, C451, C452, C456, C457, C458, C459, C460, C463, C467, C468, C476, C477, C481, C482, C483, C484, C485, C488, C492, C493: 0.1uF; PART
C5, C6, C24, C25, C53, C54, C78, C79, C103, C104, C128, C129, C153, C154, C178, C179, C203, C204, C228, C229, C253, C254, C278, C279, C303, C304, C328, C329, C353, C354, C378, C379, C403, C404, C428, C429, C453, C454, C478, C479: 2.2uF; _0402MP
C7, C26, C55, C80, C105, C130, C155, C180, C205, C230, C255, C280, C305, C330, C355, C380, C405, C430, C455, C480: 0.47uF; PART
C11, C45, C70, C95, C120, C145, C170, C195, C220, C245, C270, C295, C320, C345, C370, C395, C420, C445, C470, C495: 1.2pF; _0402MP
C12, C18, C19, C20, C23, C46, C47, C48, C49, C50, C71, C72, C73, C74, C75, C96, C97, C98, C99, C100, C121, C122, C123, C124, C125, C146, C147, C148, C149, C150, C171, C172, C173, C174, C175, C196, C197, C198, C199, C200, C221, C222, C223, C224, C225, C246, C247, C248, C249, C250, C271, C272, C273, C274, C275, C296, C297, C298, C299, C300, C321, C322, C323, C324, C325, C346, C347, C348, C349, C350, C371, C372, C373, C374, C375, C396, C397, C398, C399, C400, C421, C422, C423, C424, C425, C446, C447, C448, C449, C450, C471, C472, C473, C474, C475, C496, C497, C498, C499, C500: 22pF; PART
C13, C44, C69, C94, C119, C144, C169, C194, C219, C244, C269, C294, C319, C344, C369, C394, C419, C444, C469, C494: DNP; PART
C14, C15, C39, C40, C64, C65, C89, C90, C114, C115, C139, C140, C164, C165, C189, C190, C214, C215, C239, C240, C264, C265, C289, C290, C314, C315, C339, C340, C364, C365, C389, C390, C414, C415, C439, C440, C464, C465, C489, C490: 9pF; PART
C21, C22, C36, C37, C61, C62, C86, C87, C111, C112, C136, C137, C161, C162, C186, C187, C211, C212, C236, C237, C261, C262, C286, C287, C311, C312, C336, C337, C361, C362, C386, C387, C411, C412, C436, C437, C461, C462, C486, C487: 10uF; _0402MP
C31, C41, C66, C91, C116, C141, C166, C191, C216, C241, C266, C291, C316, C341, C366, C391, C416, C441, C466, C491: 10nF; PART
FB1, FB2, FB3, FB4, FB5, FB6, FB7, FB8, FB9, FB10, FB11, FB12, FB13, FB14, FB15, FB16, FB17, FB18, FB19, FB20: Ferrite; _0603MP
FID1, FID2, FID3, FID4, FID5, FID6: FIDUCIAL; FIDUCIAL_1MM
IC, IC1, IC2, IC3, IC4, IC5, IC6, IC7, IC8, IC9, IC10, IC11, IC12, IC13, IC14, IC15, IC16, IC17, IC18, IC19: ATSAMR21E18A-MUT; QFN32
IMU, IMU1, IMU2, IMU3, IMU4, IMU5, IMU6, IMU7, IMU8, IMU9, IMU10, IMU11, IMU12, IMU13, IMU14, IMU15, IMU16, IMU17, IMU18, IMU19: MPU-9250; QFN_3X3MM
L1, L3, L5, L8, L10, L12, L14, L16, L18, L20, L22, L24, L26, L28, L30, L32, L34, L36, L38, L40: 1.8nH; _0603MP
L2, L4, L6, L7, L9, L11, L13, L15, L17, L19, L21, L23, L25, L27, L29, L31, L33, L35, L37, L39: 10uH; _0603MP
LDO_VREG, LDO_VREG1, LDO_VREG2, LDO_VREG3, LDO_VREG4, LDO_VREG5, LDO_VREG6, LDO_VREG7, LDO_VREG8, LDO_VREG9, LDO_VREG10, LDO_VREG11, LDO_VREG12, LDO_VREG13, LDO_VREG14, LDO_VREG15, LDO_VREG16, LDO_VREG17, LDO_VREG18, LDO_VREG19: MCP1700T-3302E/TT
R1, R4, R5, R6, R7, R11, R16, R17, R18, R19, R21, R26, R27, R28, R29, R31, R36, R37, R38, R39, R41, R46, R47, R48, R49, R51, R56, R57, R58, R59, R61, R66, R67, R68, R69, R71, R76, R77, R78, R79, R81, R86, R87, R88, R89, R91, R96, R97, R98, R99, R101, R106, R107, R108, R109, R111, R116, R117, R118, R119, R121, R126, R127, R128, R129, R131, R136, R137, R138, R139, R141, R146, R147, R148, R149, R151, R156, R157, R158, R159, R161, R166, R167, R168, R169, R171, R176, R177, R178, R179, R181, R186, R187, R188, R189, R191, R196, R197, R198, R199: 330; PART
R2, R12, R22, R32, R42, R52, R62, R72, R82, R92, R102, R112, R122, R132, R142, R152, R162, R172, R182, R192: 10K; PART
R3, R15, R25, R35, R45, R55, R65, R75, R85, R95, R105, R115, R125, R135, R145, R155, R165, R175, R185, R195: 330; _0402
R8, R9, R13, R14, R23, R24, R33, R34, R43, R44, R53, R54, R63, R64, R73, R74, R83, R84, R93, R94, R103, R104, R113, R114, R123, R124, R133, R134, R143, R144, R153, R154, R163, R164, R173, R174, R183, R184, R193, R194: 2.2K; PART
R10, R20, R30, R40, R50, R60, R70, R80, R90, R100, R110, R120, R130, R140, R150, R160, R170, R180, R190, R200: 100K; PART
RGBLED, RGBLED1, RGBLED2, RGBLED3, RGBLED4, RGBLED5, RGBLED6, RGBLED7, RGBLED8, RGBLED9, RGBLED10, RGBLED11, RGBLED12, RGBLED13, RGBLED14, RGBLED15, RGBLED16, RGBLED17, RGBLED18, RGBLED19: LRTB_R48G
U$1, U$2, U$3, U$4, U$5, U$6, U$7, U$8, U$9, U$10, U$11, U$12, U$13, U$14, U$15, U$16, U$17, U$18, U$19, U$20, U$21, U$22, U$23, U$24, U$25, U$26, U$27, U$28, U$29, U$30, U$31, U$32, U$33, U$34, U$35, U$36, U$37, U$38, U$39, U$40, U$41, U$42, U$43, U$44, U$45, U$46, U$47, U$48, U$49, U$50, U$51, U$52, U$53, U$54, U$55, U$56, U$57, U$58, U$59, U$60, U$61, U$62, U$63, U$64, U$65, U$66, U$67, U$68, U$69, U$70, U$71, U$72, U$73, U$74, U$75, U$76, U$77, U$78, U$79, U$80, U$81, U$82, U$83, U$84, U$85, U$86, U$87, U$88, U$89, U$90, U$91, U$92, U$93, U$94, U$95, U$96, U$97, U$98, U$99, U$100, U$101, U$102, U$103, U$104, U$105, U$106, U$107, U$108, U$109, U$110, U$111, U$112, U$113, U$114, U$115, U$116, U$117, U$118, U$119, U$120, U$121, U$122, U$123, U$124, U$125, U$126, U$127, U$128, U$129, U$130, U$131, U$132, U$133, U$134, U$135, U$136, U$137, U$138, U$139, U$140, U$141, U$142, U$143, U$144, U$145, U$146, U$147, U$148, U$149, U$150, U$151, U$152, U$153, U$154, U$155, U$156, U$157, U$158, U$159, U$160, U$161, U$162, U$163, U$164, U$165, U$166, U$167, U$168, U$169, U$170, U$171, U$172, U$173, U$174, U$175, U$176, U$177, U$178, U$179, U$180, U$181, U$182, U$183, U$184, U$185, U$186, U$187, U$188, U$189, U$190, U$191, U$192, U$193, U$194, U$195, U$196, U$197, U$198, U$199, U$200, U$201, U$202, U$203, U$204, U$205, U$206, U$207, U$208, U$209, U$210, U$211, U$212, U$213, U$214, U$215, U$216, U$217, U$218, U$219, U$220, U$221, U$222, U$223, U$224, U$225, U$226, U$227, U$228, U$229, U$230, U$231, U$232, U$233, U$234, U$235, U$236, U$237, U$238, U$239, U$240, U$241, U$242, U$243, U$244, U$245, U$246, U$247, U$248, U$249, U$250, U$251, U$252, U$253, U$254, U$255, U$256, U$257, U$258, U$259, U$260, U$261, U$262, U$263, U$264, U$265, U$266, U$267, U$268, U$269, U$270, U$271, U$272, U$273, U$274, U$275, U$276, U$277, U$278, U$279, U$280, U$281, U$282, U$283, U$284, U$285, U$286, U$287, U$288, U$289, U$290, U$291, U$292, U$293, U$294, U$295, U$296, U$297, U$298, U$299, U$300, U$301, U$302, U$303, U$304, U$305, U$306, U$307, U$308, U$309, U$310, U$311, U$312, U$313, U$314, U$315, U$316, U$317, U$318, U$319, U$320, U$321, U$322, U$323, U$324, U$325, U$326, U$327, U$328, U$329, U$330, U$331, U$332, U$333, U$334, U$335, U$336, U$337, U$338, U$339, U$340: 1X1_ROUND
UFLANT, UFLANT1, UFLANT2, UFLANT3, UFLANT4, UFLANT5, UFLANT6, UFLANT7, UFLANT8, UFLANT9, UFLANT10, UFLANT11, UFLANT12, UFLANT13, UFLANT14, UFLANT15, UFLANT16, UFLANT17, UFLANT18, UFLANT19: uFL; U.FL
USB, USB1, USB2, USB3, USB4, USB5, USB6, USB7, USB8, USB9, USB10, USB11, USB12, USB13, USB14, USB15, USB16, USB17, USB18, USB19: USB_MICROB; USB_MICROB_PACKAGE
XOSCRF, XOSCRF1, XOSCRF2, XOSCRF3, XOSCRF4, XOSCRF5, XOSCRF6, XOSCRF7, XOSCRF8, XOSCRF9, XOSCRF10, XOSCRF11, XOSCRF12, XOSCRF13, XOSCRF14, XOSCRF15, XOSCRF16, XOSCRF17, XOSCRF18, XOSCRF19: 16MHz; TSX-3225

Connections:
3.3V: BARO.1, BARO.2, C5.1, C10.1, C16.1, C21.2, C29.1, C30.2, C31.2, IC.24, IC.30, IMU.P$1, IMU.P$8, IMU.P$13, IMU.P$22, L6.1, LDO_VREG.VOUT, R2.2, R8.2, R9.2, R10.2, RGBLED.1, U$5.P$1
3.3V1: BARO1.1, BARO1.2, C24.1, C27.1, C34.1, C36.2, C38.1, C41.2, C42.2, IC1.24, IC1.30, IMU1.P$1, IMU1.P$8, IMU1.P$13, IMU1.P$22, L2.1, LDO_VREG1.VOUT, R12.2, R13.2, R14.2, R20.2, RGBLED1.1, U$6.P$1
3.3V2: BARO2.1, BARO2.2, C53.1, C56.1, C59.1, C61.2, C63.1, C66.2, C67.2, IC2.24, IC2.30, IMU2.P$1, IMU2.P$8, IMU2.P$13, IMU2.P$22, L4.1, LDO_VREG2.VOUT, R22.2, R23.2, R24.2, R30.2, RGBLED2.1, U$26.P$1
3.3V3: BARO3.1, BARO3.2, C78.1, C81.1, C84.1, C86.2, C88.1, C91.2, C92.2, IC3.24, IC3.30, IMU3.P$1, IMU3.P$8, IMU3.P$13, IMU3.P$22, L7.1, LDO_VREG3.VOUT, R32.2, R33.2, R34.2, R40.2, RGBLED3.1, U$53.P$1
3.3V4: BARO4.1, BARO4.2, C103.1, C106.1, C109.1, C111.2, C113.1, C116.2, C117.2, IC4.24, IC4.30, IMU4.P$1, IMU4.P$8, IMU4.P$13, IMU4.P$22, L9.1, LDO_VREG4.VOUT, R42.2, R43.2, R44.2, R50.2, RGBLED4.1, U$71.P$1
3.3V5: BARO5.1, BARO5.2, C128.1, C131.1, C134.1, C136.2, C138.1, C141.2, C142.2, IC5.24, IC5.30, IMU5.P$1, IMU5.P$8, IMU5.P$13, IMU5.P$22, L11.1, LDO_VREG5.VOUT, R52.2, R53.2, R54.2, R60.2, RGBLED5.1, U$88.P$1
3.3V6: BARO6.1, BARO6.2, C153.1, C156.1, C159.1, C161.2, C163.1, C166.2, C167.2, IC6.24, IC6.30, IMU6.P$1, IMU6.P$8, IMU6.P$13, IMU6.P$22, L13.1, LDO_VREG6.VOUT, R62.2, R63.2, R64.2, R70.2, RGBLED6.1, U$105.P$1
3.3V7: BARO7.1, BARO7.2, C178.1, C181.1, C184.1, C186.2, C188.1, C191.2, C192.2, IC7.24, IC7.30, IMU7.P$1, IMU7.P$8, IMU7.P$13, IMU7.P$22, L15.1, LDO_VREG7.VOUT, R72.2, R73.2, R74.2, R80.2, RGBLED7.1, U$122.P$1
3.3V8: BARO8.1, BARO8.2, C203.1, C206.1, C209.1, C211.2, C213.1, C216.2, C217.2, IC8.24, IC8.30, IMU8.P$1, IMU8.P$8, IMU8.P$13, IMU8.P$22, L17.1, LDO_VREG8.VOUT, R82.2, R83.2, R84.2, R90.2, RGBLED8.1, U$139.P$1
3.3V9: BARO9.1, BARO9.2, C228.1, C231.1, C234.1, C236.2, C238.1, C241.2, C242.2, IC9.24, IC9.30, IMU9.P$1, IMU9.P$8, IMU9.P$13, IMU9.P$22, L19.1, LDO_VREG9.VOUT, R92.2, R93.2, R94.2, R100.2, RGBLED9.1, U$156.P$1
3.3V10: BARO10.1, BARO10.2, C253.1, C256.1, C259.1, C261.2, C263.1, C266.2, C267.2, IC10.24, IC10.30, IMU10.P$1, IMU10.P$8, IMU10.P$13, IMU10.P$22, L21.1, LDO_VREG10.VOUT, R102.2, R103.2, R104.2, R110.2, RGBLED10.1, U$173.P$1
3.3V11: BARO11.1, BARO11.2, C278.1, C281.1, C284.1, C286.2, C288.1, C291.2, C292.2, IC11.24, IC11.30, IMU11.P$1, IMU11.P$8, IMU11.P$13, IMU11.P$22, L23.1, LDO_VREG11.VOUT, R112.2, R113.2, R114.2, R120.2, RGBLED11.1, U$190.P$1
3.3V12: BARO12.1, BARO12.2, C303.1, C306.1, C309.1, C311.2, C313.1, C316.2, C317.2, IC12.24, IC12.30, IMU12.P$1, IMU12.P$8, IMU12.P$13, IMU12.P$22, L25.1, LDO_VREG12.VOUT, R122.2, R123.2, R124.2, R130.2, RGBLED12.1, U$207.P$1
3.3V13: BARO13.1, BARO13.2, C328.1, C331.1, C334.1, C336.2, C338.1, C341.2, C342.2, IC13.24, IC13.30, IMU13.P$1, IMU13.P$8, IMU13.P$13, IMU13.P$22, L27.1, LDO_VREG13.VOUT, R132.2, R133.2, R134.2, R140.2, RGBLED13.1, U$224.P$1
3.3V14: BARO14.1, BARO14.2, C353.1, C356.1, C359.1, C361.2, C363.1, C366.2, C367.2, IC14.24, IC14.30, IMU14.P$1, IMU14.P$8, IMU14.P$13, IMU14.P$22, L29.1, LDO_VREG14.VOUT, R142.2, R143.2, R144.2, R150.2, RGBLED14.1, U$241.P$1
3.3V15: BARO15.1, BARO15.2, C378.1, C381.1, C384.1, C386.2, C388.1, C391.2, C392.2, IC15.24, IC15.30, IMU15.P$1, IMU15.P$8, IMU15.P$13, IMU15.P$22, L31.1, LDO_VREG15.VOUT, R152.2, R153.2, R154.2, R160.2, RGBLED15.1, U$258.P$1
3.3V16: BARO16.1, BARO16.2, C403.1, C406.1, C409.1, C411.2, C413.1, C416.2, C417.2, IC16.24, IC16.30, IMU16.P$1, IMU16.P$8, IMU16.P$13, IMU16.P$22, L33.1, LDO_VREG16.VOUT, R162.2, R163.2, R164.2, R170.2, RGBLED16.1, U$275.P$1
3.3V17: BARO17.1, BARO17.2, C428.1, C431.1, C434.1, C436.2, C438.1, C441.2, C442.2, IC17.24, IC17.30, IMU17.P$1, IMU17.P$8, IMU17.P$13, IMU17.P$22, L35.1, LDO_VREG17.VOUT, R172.2, R173.2, R174.2, R180.2, RGBLED17.1, U$292.P$1
3.3V18: BARO18.1, BARO18.2, C453.1, C456.1, C459.1, C461.2, C463.1, C466.2, C467.2, IC18.24, IC18.30, IMU18.P$1, IMU18.P$8, IMU18.P$13, IMU18.P$22, L37.1, LDO_VREG18.VOUT, R182.2, R183.2, R184.2, R190.2, RGBLED18.1, U$309.P$1
3.3V19: BARO19.1, BARO19.2, C478.1, C481.1, C484.1, C486.2, C488.1, C491.2, C492.2, IC19.24, IC19.30, IMU19.P$1, IMU19.P$8, IMU19.P$13, IMU19.P$22, L39.1, LDO_VREG19.VOUT, R192.2, R193.2, R194.2, R200.2, RGBLED19.1, U$326.P$1
ANT_LINE: ANT_SMD.ANT, C13.1, L1.2
ANT_LINE1: ANT_SMD1.ANT, C44.1, L3.2
ANT_LINE2: ANT_SMD2.ANT, C69.1, L5.2
ANT_LINE3: ANT_SMD3.ANT, C94.1, L8.2
ANT_LINE4: ANT_SMD4.ANT, C119.1, L10.2
ANT_LINE5: ANT_SMD5.ANT, C144.1, L12.2
ANT_LINE6: ANT_SMD6.ANT, C169.1, L14.2
ANT_LINE7: ANT_SMD7.ANT, C194.1, L16.2
ANT_LINE8: ANT_SMD8.ANT, C219.1, L18.2
ANT_LINE9: ANT_SMD9.ANT, C244.1, L20.2
ANT_LINE10: ANT_SMD10.ANT, C269.1, L22.2
ANT_LINE11: ANT_SMD11.ANT, C294.1, L24.2
ANT_LINE12: ANT_SMD12.ANT, C319.1, L26.2
ANT_LINE13: ANT_SMD13.ANT, C344.1, L28.2
ANT_LINE14: ANT_SMD14.ANT, C369.1, L30.2
ANT_LINE15: ANT_SMD15.ANT, C394.1, L32.2
ANT_LINE16: ANT_SMD16.ANT, C419.1, L34.2
ANT_LINE17: ANT_SMD17.ANT, C444.1, L36.2
ANT_LINE18: ANT_SMD18.ANT, C469.1, L38.2
ANT_LINE19: ANT_SMD19.ANT, C494.1, L40.2
ANT_OUT: BALUN.1, C12.1
ANT_OUT1: BALUN1.1, C46.1
ANT_OUT2: BALUN2.1, C71.1
ANT_OUT3: BALUN3.1, C96.1
ANT_OUT4: BALUN4.1, C121.1
ANT_OUT5: BALUN5.1, C146.1
ANT_OUT6: BALUN6.1, C171.1
ANT_OUT7: BALUN7.1, C196.1
ANT_OUT8: BALUN8.1, C221.1
ANT_OUT9: BALUN9.1, C246.1
ANT_OUT10: BALUN10.1, C271.1
ANT_OUT11: BALUN11.1, C296.1
ANT_OUT12: BALUN12.1, C321.1
ANT_OUT13: BALUN13.1, C346.1
ANT_OUT14: BALUN14.1, C371.1
ANT_OUT15: BALUN15.1, C396.1
ANT_OUT16: BALUN16.1, C421.1
ANT_OUT17: BALUN17.1, C446.1
ANT_OUT18: BALUN18.1, C471.1
ANT_OUT19: BALUN19.1, C496.1
ANT_SMD: C11.1, C23.2, L1.1
ANT_SMD1: C45.1, C50.2, L3.1
ANT_SMD2: C70.1, C75.2, L5.1
ANT_SMD3: C95.1, C100.2, L8.1
ANT_SMD4: C120.1, C125.2, L10.1
ANT_SMD5: C145.1, C150.2, L12.1
ANT_SMD6: C170.1, C175.2, L14.1
ANT_SMD7: C195.1, C200.2, L16.1
ANT_SMD8: C220.1, C225.2, L18.1
ANT_SMD9: C245.1, C250.2, L20.1
ANT_SMD10: C270.1, C275.2, L22.1
ANT_SMD11: C295.1, C300.2, L24.1
ANT_SMD12: C320.1, C325.2, L26.1
ANT_SMD13: C345.1, C350.2, L28.1
ANT_SMD14: C370.1, C375.2, L30.1
ANT_SMD15: C395.1, C400.2, L32.1
ANT_SMD16: C420.1, C425.2, L34.1
ANT_SMD17: C445.1, C450.2, L36.1
ANT_SMD18: C470.1, C475.2, L38.1
ANT_SMD19: C495.1, C500.2, L40.1
ANT_UFL: C20.1, UFLANT.3
ANT_UFL1: C49.1, UFLANT1.3
ANT_UFL2: C74.1, UFLANT2.3
ANT_UFL3: C99.1, UFLANT3.3
ANT_UFL4: C124.1, UFLANT4.3
ANT_UFL5: C149.1, UFLANT5.3
ANT_UFL6: C174.1, UFLANT6.3
ANT_UFL7: C199.1, UFLANT7.3
ANT_UFL8: C224.1, UFLANT8.3
ANT_UFL9: C249.1, UFLANT9.3
ANT_UFL10: C274.1, UFLANT10.3
ANT_UFL11: C299.1, UFLANT11.3
ANT_UFL12: C324.1, UFLANT12.3
ANT_UFL13: C349.1, UFLANT13.3
ANT_UFL14: C374.1, UFLANT14.3
ANT_UFL15: C399.1, UFLANT15.3
ANT_UFL16: C424.1, UFLANT16.3
ANT_UFL17: C449.1, UFLANT17.3
ANT_UFL18: C474.1, UFLANT18.3
ANT_UFL19: C499.1, UFLANT19.3
AVDD: C17.1, IC.5
AVDD1: C35.1, IC1.5
AVDD2: C60.1, IC2.5
AVDD3: C85.1, IC3.5
AVDD4: C110.1, IC4.5
AVDD5: C135.1, IC5.5
AVDD6: C160.1, IC6.5
AVDD7: C185.1, IC7.5
AVDD8: C210.1, IC8.5
AVDD9: C235.1, IC9.5
AVDD10: C260.1, IC10.5
AVDD11: C285.1, IC11.5
AVDD12: C310.1, IC12.5
AVDD13: C335.1, IC13.5
AVDD14: C360.1, IC14.5
AVDD15: C385.1, IC15.5
AVDD16: C410.1, IC16.5
AVDD17: C435.1, IC17.5
AVDD18: C460.1, IC18.5
AVDD19: C485.1, IC19.5
DVDD: C2.1, IC.21
DVDD1: C4.1, IC1.21
DVDD2: C52.1, IC2.21
DVDD3: C77.1, IC3.21
DVDD4: C102.1, IC4.21
DVDD5: C127.1, IC5.21
DVDD6: C152.1, IC6.21
DVDD7: C177.1, IC7.21
DVDD8: C202.1, IC8.21
DVDD9: C227.1, IC9.21
DVDD10: C252.1, IC10.21
DVDD11: C277.1, IC11.21
DVDD12: C302.1, IC12.21
DVDD13: C327.1, IC13.21
DVDD14: C352.1, IC14.21
DVDD15: C377.1, IC15.21
DVDD16: C402.1, IC16.21
DVDD17: C427.1, IC17.21
DVDD18: C452.1, IC18.21
DVDD19: C477.1, IC19.21
GND: ASWITCH.PIN2, BALUN.2, BALUN.5, BALUN.6, BARO.3, BARO.4, BARO.5, BTN.2, C1.2, C2.2, C5.2, C6.2, C7.2, C8.2, C9.2, C10.2, C11.2, C13.2, C14.1, C15.2, C16.2, C17.2, C18.1, C19.2, C21.1, C22.1, C29.2, C30.1, C31.1, C32.2, FB1.2, IC.3, IC.6, IC.11, IC.14, IC.28, IC.33, IMU.P$20, LDO_VREG.GND, R3.1, U$2.P$1, UFLANT.1, UFLANT.2, XOSCRF.2, XOSCRF.4
GND1: ASWITCH1.PIN2, BALUN1.2, BALUN1.5, BALUN1.6, BARO1.3, BARO1.4, BARO1.5, BTN1.2, C3.2, C4.2, C24.2, C25.2, C26.2, C27.2, C28.2, C33.2, C34.2, C35.2, C36.1, C37.1, C38.2, C39.1, C40.2, C41.1, C42.1, C43.2, C44.2, C45.2, C47.1, C48.2, FB2.2, IC1.3, IC1.6, IC1.11, IC1.14, IC1.28, IC1.33, IMU1.P$20, LDO_VREG1.GND, R15.1, U$4.P$1, UFLANT1.1, UFLANT1.2, XOSCRF1.2, XOSCRF1.4
GND2: ASWITCH2.PIN2, BALUN2.2, BALUN2.5, BALUN2.6, BARO2.3, BARO2.4, BARO2.5, BTN2.2, C51.2, C52.2, C53.2, C54.2, C55.2, C56.2, C57.2, C58.2, C59.2, C60.2, C61.1, C62.1, C63.2, C64.1, C65.2, C66.1, C67.1, C68.2, C69.2, C70.2, C72.1, C73.2, FB3.2, IC2.3, IC2.6, IC2.11, IC2.14, IC2.28, IC2.33, IMU2.P$20, LDO_VREG2.GND, R25.1, U$25.P$1, UFLANT2.1, UFLANT2.2, XOSCRF2.2, XOSCRF2.4
GND3: ASWITCH3.PIN2, BALUN3.2, BALUN3.5, BALUN3.6, BARO3.3, BARO3.4, BARO3.5, BTN3.2, C76.2, C77.2, C78.2, C79.2, C80.2, C81.2, C82.2, C83.2, C84.2, C85.2, C86.1, C87.1, C88.2, C89.1, C90.2, C91.1, C92.1, C93.2, C94.2, C95.2, C97.1, C98.2, FB4.2, IC3.3, IC3.6, IC3.11, IC3.14, IC3.28, IC3.33, IMU3.P$20, LDO_VREG3.GND, R35.1, U$52.P$1, UFLANT3.1, UFLANT3.2, XOSCRF3.2, XOSCRF3.4
GND4: ASWITCH4.PIN2, BALUN4.2, BALUN4.5, BALUN4.6, BARO4.3, BARO4.4, BARO4.5, BTN4.2, C101.2, C102.2, C103.2, C104.2, C105.2, C106.2, C107.2, C108.2, C109.2, C110.2, C111.1, C112.1, C113.2, C114.1, C115.2, C116.1, C117.1, C118.2, C119.2, C120.2, C122.1, C123.2, FB5.2, IC4.3, IC4.6, IC4.11, IC4.14, IC4.28, IC4.33, IMU4.P$20, LDO_VREG4.GND, R45.1, U$70.P$1, UFLANT4.1, UFLANT4.2, XOSCRF4.2, XOSCRF4.4
GND5: ASWITCH5.PIN2, BALUN5.2, BALUN5.5, BALUN5.6, BARO5.3, BARO5.4, BARO5.5, BTN5.2, C126.2, C127.2, C128.2, C129.2, C130.2, C131.2, C132.2, C133.2, C134.2, C135.2, C136.1, C137.1, C138.2, C139.1, C140.2, C141.1, C142.1, C143.2, C144.2, C145.2, C147.1, C148.2, FB6.2, IC5.3, IC5.6, IC5.11, IC5.14, IC5.28, IC5.33, IMU5.P$20, LDO_VREG5.GND, R55.1, U$87.P$1, UFLANT5.1, UFLANT5.2, XOSCRF5.2, XOSCRF5.4
GND6: ASWITCH6.PIN2, BALUN6.2, BALUN6.5, BALUN6.6, BARO6.3, BARO6.4, BARO6.5, BTN6.2, C151.2, C152.2, C153.2, C154.2, C155.2, C156.2, C157.2, C158.2, C159.2, C160.2, C161.1, C162.1, C163.2, C164.1, C165.2, C166.1, C167.1, C168.2, C169.2, C170.2, C172.1, C173.2, FB7.2, IC6.3, IC6.6, IC6.11, IC6.14, IC6.28, IC6.33, IMU6.P$20, LDO_VREG6.GND, R65.1, U$104.P$1, UFLANT6.1, UFLANT6.2, XOSCRF6.2, XOSCRF6.4
GND7: ASWITCH7.PIN2, BALUN7.2, BALUN7.5, BALUN7.6, BARO7.3, BARO7.4, BARO7.5, BTN7.2, C176.2, C177.2, C178.2, C179.2, C180.2, C181.2, C182.2, C183.2, C184.2, C185.2, C186.1, C187.1, C188.2, C189.1, C190.2, C191.1, C192.1, C193.2, C194.2, C195.2, C197.1, C198.2, FB8.2, IC7.3, IC7.6, IC7.11, IC7.14, IC7.28, IC7.33, IMU7.P$20, LDO_VREG7.GND, R75.1, U$121.P$1, UFLANT7.1, UFLANT7.2, XOSCRF7.2, XOSCRF7.4
GND8: ASWITCH8.PIN2, BALUN8.2, BALUN8.5, BALUN8.6, BARO8.3, BARO8.4, BARO8.5, BTN8.2, C201.2, C202.2, C203.2, C204.2, C205.2, C206.2, C207.2, C208.2, C209.2, C210.2, C211.1, C212.1, C213.2, C214.1, C215.2, C216.1, C217.1, C218.2, C219.2, C220.2, C222.1, C223.2, FB9.2, IC8.3, IC8.6, IC8.11, IC8.14, IC8.28, IC8.33, IMU8.P$20, LDO_VREG8.GND, R85.1, U$138.P$1, UFLANT8.1, UFLANT8.2, XOSCRF8.2, XOSCRF8.4
GND9: ASWITCH9.PIN2, BALUN9.2, BALUN9.5, BALUN9.6, BARO9.3, BARO9.4, BARO9.5, BTN9.2, C226.2, C227.2, C228.2, C229.2, C230.2, C231.2, C232.2, C233.2, C234.2, C235.2, C236.1, C237.1, C238.2, C239.1, C240.2, C241.1, C242.1, C243.2, C244.2, C245.2, C247.1, C248.2, FB10.2, IC9.3, IC9.6, IC9.11, IC9.14, IC9.28, IC9.33, IMU9.P$20, LDO_VREG9.GND, R95.1, U$155.P$1, UFLANT9.1, UFLANT9.2, XOSCRF9.2, XOSCRF9.4
GND10: ASWITCH10.PIN2, BALUN10.2, BALUN10.5, BALUN10.6, BARO10.3, BARO10.4, BARO10.5, BTN10.2, C251.2, C252.2, C253.2, C254.2, C255.2, C256.2, C257.2, C258.2, C259.2, C260.2, C261.1, C262.1, C263.2, C264.1, C265.2, C266.1, C267.1, C268.2, C269.2, C270.2, C272.1, C273.2, FB11.2, IC10.3, IC10.6, IC10.11, IC10.14, IC10.28, IC10.33, IMU10.P$20, LDO_VREG10.GND, R105.1, U$172.P$1, UFLANT10.1, UFLANT10.2, XOSCRF10.2, XOSCRF10.4
GND11: ASWITCH11.PIN2, BALUN11.2, BALUN11.5, BALUN11.6, BARO11.3, BARO11.4, BARO11.5, BTN11.2, C276.2, C277.2, C278.2, C279.2, C280.2, C281.2, C282.2, C283.2, C284.2, C285.2, C286.1, C287.1, C288.2, C289.1, C290.2, C291.1, C292.1, C293.2, C294.2, C295.2, C297.1, C298.2, FB12.2, IC11.3, IC11.6, IC11.11, IC11.14, IC11.28, IC11.33, IMU11.P$20, LDO_VREG11.GND, R115.1, U$189.P$1, UFLANT11.1, UFLANT11.2, XOSCRF11.2, XOSCRF11.4
GND12: ASWITCH12.PIN2, BALUN12.2, BALUN12.5, BALUN12.6, BARO12.3, BARO12.4, BARO12.5, BTN12.2, C301.2, C302.2, C303.2, C304.2, C305.2, C306.2, C307.2, C308.2, C309.2, C310.2, C311.1, C312.1, C313.2, C314.1, C315.2, C316.1, C317.1, C318.2, C319.2, C320.2, C322.1, C323.2, FB13.2, IC12.3, IC12.6, IC12.11, IC12.14, IC12.28, IC12.33, IMU12.P$20, LDO_VREG12.GND, R125.1, U$206.P$1, UFLANT12.1, UFLANT12.2, XOSCRF12.2, XOSCRF12.4
GND13: ASWITCH13.PIN2, BALUN13.2, BALUN13.5, BALUN13.6, BARO13.3, BARO13.4, BARO13.5, BTN13.2, C326.2, C327.2, C328.2, C329.2, C330.2, C331.2, C332.2, C333.2, C334.2, C335.2, C336.1, C337.1, C338.2, C339.1, C340.2, C341.1, C342.1, C343.2, C344.2, C345.2, C347.1, C348.2, FB14.2, IC13.3, IC13.6, IC13.11, IC13.14, IC13.28, IC13.33, IMU13.P$20, LDO_VREG13.GND, R135.1, U$223.P$1, UFLANT13.1, UFLANT13.2, XOSCRF13.2, XOSCRF13.4
GND14: ASWITCH14.PIN2, BALUN14.2, BALUN14.5, BALUN14.6, BARO14.3, BARO14.4, BARO14.5, BTN14.2, C351.2, C352.2, C353.2, C354.2, C355.2, C356.2, C357.2, C358.2, C359.2, C360.2, C361.1, C362.1, C363.2, C364.1, C365.2, C366.1, C367.1, C368.2, C369.2, C370.2, C372.1, C373.2, FB15.2, IC14.3, IC14.6, IC14.11, IC14.14, IC14.28, IC14.33, IMU14.P$20, LDO_VREG14.GND, R145.1, U$240.P$1, UFLANT14.1, UFLANT14.2, XOSCRF14.2, XOSCRF14.4
GND15: ASWITCH15.PIN2, BALUN15.2, BALUN15.5, BALUN15.6, BARO15.3, BARO15.4, BARO15.5, BTN15.2, C376.2, C377.2, C378.2, C379.2, C380.2, C381.2, C382.2, C383.2, C384.2, C385.2, C386.1, C387.1, C388.2, C389.1, C390.2, C391.1, C392.1, C393.2, C394.2, C395.2, C397.1, C398.2, FB16.2, IC15.3, IC15.6, IC15.11, IC15.14, IC15.28, IC15.33, IMU15.P$20, LDO_VREG15.GND, R155.1, U$257.P$1, UFLANT15.1, UFLANT15.2, XOSCRF15.2, XOSCRF15.4
GND16: ASWITCH16.PIN2, BALUN16.2, BALUN16.5, BALUN16.6, BARO16.3, BARO16.4, BARO16.5, BTN16.2, C401.2, C402.2, C403.2, C404.2, C405.2, C406.2, C407.2, C408.2, C409.2, C410.2, C411.1, C412.1, C413.2, C414.1, C415.2, C416.1, C417.1, C418.2, C419.2, C420.2, C422.1, C423.2, FB17.2, IC16.3, IC16.6, IC16.11, IC16.14, IC16.28, IC16.33, IMU16.P$20, LDO_VREG16.GND, R165.1, U$274.P$1, UFLANT16.1, UFLANT16.2, XOSCRF16.2, XOSCRF16.4
GND17: ASWITCH17.PIN2, BALUN17.2, BALUN17.5, BALUN17.6, BARO17.3, BARO17.4, BARO17.5, BTN17.2, C426.2, C427.2, C428.2, C429.2, C430.2, C431.2, C432.2, C433.2, C434.2, C435.2, C436.1, C437.1, C438.2, C439.1, C440.2, C441.1, C442.1, C443.2, C444.2, C445.2, C447.1, C448.2, FB18.2, IC17.3, IC17.6, IC17.11, IC17.14, IC17.28, IC17.33, IMU17.P$20, LDO_VREG17.GND, R175.1, U$291.P$1, UFLANT17.1, UFLANT17.2, XOSCRF17.2, XOSCRF17.4
GND18: ASWITCH18.PIN2, BALUN18.2, BALUN18.5, BALUN18.6, BARO18.3, BARO18.4, BARO18.5, BTN18.2, C451.2, C452.2, C453.2, C454.2, C455.2, C456.2, C457.2, C458.2, C459.2, C460.2, C461.1, C462.1, C463.2, C464.1, C465.2, C466.1, C467.1, C468.2, C469.2, C470.2, C472.1, C473.2, FB19.2, IC18.3, IC18.6, IC18.11, IC18.14, IC18.28, IC18.33, IMU18.P$20, LDO_VREG18.GND, R185.1, U$308.P$1, UFLANT18.1, UFLANT18.2, XOSCRF18.2, XOSCRF18.4
GND19: ASWITCH19.PIN2, BALUN19.2, BALUN19.5, BALUN19.6, BARO19.3, BARO19.4, BARO19.5, BTN19.2, C476.2, C477.2, C478.2, C479.2, C480.2, C481.2, C482.2, C483.2, C484.2, C485.2, C486.1, C487.1, C488.2, C489.1, C490.2, C491.1, C492.1, C493.2, C494.2, C495.2, C497.1, C498.2, FB20.2, IC19.3, IC19.6, IC19.11, IC19.14, IC19.28, IC19.33, IMU19.P$20, LDO_VREG19.GND, R195.1, U$325.P$1, UFLANT19.1, UFLANT19.2, XOSCRF19.2, XOSCRF19.4
unnamed: R5.2, R10.1, USB.4
unnamed: BTN1.1, R11.1
unnamed: C43.1, IMU1.P$10
unnamed: C32.1, IMU.P$10
unnamed: FB1.1, USB.5, USB.6, USB.7, USB.8, USB.9, USB.10, USB.11
unnamed: FB2.1, USB1.5, USB1.6, USB1.7, USB1.8, USB1.9, USB1.10, USB1.11
unnamed: R16.2, RGBLED1.2
unnamed: R6.2, RGBLED.3
unnamed: R7.2, RGBLED.4
unnamed: R17.2, RGBLED1.3
unnamed: R18.2, RGBLED1.4
unnamed: R19.2, R20.1, USB1.4
unnamed: R4.2, RGBLED.2
unnamed: BTN2.1, R21.1
unnamed: C68.1, IMU2.P$10
unnamed: FB3.1, USB2.5, USB2.6, USB2.7, USB2.8, USB2.9, USB2.10, USB2.11
unnamed: R26.2, RGBLED2.2
unnamed: R27.2, RGBLED2.3
unnamed: R28.2, RGBLED2.4
unnamed: R29.2, R30.1, USB2.4
unnamed: BTN3.1, R31.1
unnamed: C93.1, IMU3.P$10
unnamed: FB4.1, USB3.5, USB3.6, USB3.7, USB3.8, USB3.9, USB3.10, USB3.11
unnamed: R36.2, RGBLED3.2
unnamed: R37.2, RGBLED3.3
unnamed: BTN.1, R1.1
unnamed: R38.2, RGBLED3.4
unnamed: R39.2, R40.1, USB3.4
unnamed: BTN4.1, R41.1
unnamed: C118.1, IMU4.P$10
unnamed: FB5.1, USB4.5, USB4.6, USB4.7, USB4.8, USB4.9, USB4.10, USB4.11
unnamed: R46.2, RGBLED4.2
unnamed: R47.2, RGBLED4.3
unnamed: R48.2, RGBLED4.4
unnamed: R49.2, R50.1, USB4.4
unnamed: BTN5.1, R51.1
unnamed: C143.1, IMU5.P$10
unnamed: FB6.1, USB5.5, USB5.6, USB5.7, USB5.8, USB5.9, USB5.10, USB5.11
unnamed: R56.2, RGBLED5.2
unnamed: R57.2, RGBLED5.3
unnamed: R58.2, RGBLED5.4
unnamed: R59.2, R60.1, USB5.4
unnamed: BTN6.1, R61.1
unnamed: C168.1, IMU6.P$10
unnamed: FB7.1, USB6.5, USB6.6, USB6.7, USB6.8, USB6.9, USB6.10, USB6.11
unnamed: R66.2, RGBLED6.2
unnamed: R67.2, RGBLED6.3
unnamed: R68.2, RGBLED6.4
unnamed: R69.2, R70.1, USB6.4
unnamed: BTN7.1, R71.1
unnamed: C193.1, IMU7.P$10
unnamed: FB8.1, USB7.5, USB7.6, USB7.7, USB7.8, USB7.9, USB7.10, USB7.11
unnamed: R76.2, RGBLED7.2
unnamed: R77.2, RGBLED7.3
unnamed: R78.2, RGBLED7.4
unnamed: R79.2, R80.1, USB7.4
unnamed: BTN8.1, R81.1
unnamed: C218.1, IMU8.P$10
unnamed: FB9.1, USB8.5, USB8.6, USB8.7, USB8.8, USB8.9, USB8.10, USB8.11
unnamed: R86.2, RGBLED8.2
unnamed: R87.2, RGBLED8.3
unnamed: R88.2, RGBLED8.4
unnamed: R89.2, R90.1, USB8.4
unnamed: BTN9.1, R91.1
unnamed: C243.1, IMU9.P$10
unnamed: FB10.1, USB9.5, USB9.6, USB9.7, USB9.8, USB9.9, USB9.10, USB9.11
unnamed: R96.2, RGBLED9.2
unnamed: R97.2, RGBLED9.3
unnamed: R98.2, RGBLED9.4
unnamed: R99.2, R100.1, USB9.4
unnamed: BTN10.1, R101.1
unnamed: C268.1, IMU10.P$10
unnamed: FB11.1, USB10.5, USB10.6, USB10.7, USB10.8, USB10.9, USB10.10, USB10.11
unnamed: R106.2, RGBLED10.2
unnamed: R107.2, RGBLED10.3
unnamed: R108.2, RGBLED10.4
unnamed: R109.2, R110.1, USB10.4
unnamed: BTN11.1, R111.1
unnamed: C293.1, IMU11.P$10
unnamed: FB12.1, USB11.5, USB11.6, USB11.7, USB11.8, USB11.9, USB11.10, USB11.11
unnamed: R116.2, RGBLED11.2
unnamed: R117.2, RGBLED11.3
unnamed: R118.2, RGBLED11.4
unnamed: R119.2, R120.1, USB11.4
unnamed: BTN12.1, R121.1
unnamed: C318.1, IMU12.P$10
unnamed: FB13.1, USB12.5, USB12.6, USB12.7, USB12.8, USB12.9, USB12.10, USB12.11
unnamed: R126.2, RGBLED12.2
unnamed: R127.2, RGBLED12.3
unnamed: R128.2, RGBLED12.4
unnamed: R129.2, R130.1, USB12.4
unnamed: BTN13.1, R131.1
unnamed: C343.1, IMU13.P$10
unnamed: FB14.1, USB13.5, USB13.6, USB13.7, USB13.8, USB13.9, USB13.10, USB13.11
unnamed: R136.2, RGBLED13.2
unnamed: R137.2, RGBLED13.3
unnamed: R138.2, RGBLED13.4
unnamed: R139.2, R140.1, USB13.4
unnamed: BTN14.1, R141.1
unnamed: C368.1, IMU14.P$10
unnamed: FB15.1, USB14.5, USB14.6, USB14.7, USB14.8, USB14.9, USB14.10, USB14.11
unnamed: R146.2, RGBLED14.2
unnamed: R147.2, RGBLED14.3
unnamed: R148.2, RGBLED14.4
unnamed: R149.2, R150.1, USB14.4
unnamed: BTN15.1, R151.1
unnamed: C393.1, IMU15.P$10
unnamed: FB16.1, USB15.5, USB15.6, USB15.7, USB15.8, USB15.9, USB15.10, USB15.11
unnamed: R156.2, RGBLED15.2
unnamed: R157.2, RGBLED15.3
unnamed: R158.2, RGBLED15.4
unnamed: R159.2, R160.1, USB15.4
unnamed: BTN16.1, R161.1
unnamed: C418.1, IMU16.P$10
unnamed: FB17.1, USB16.5, USB16.6, USB16.7, USB16.8, USB16.9, USB16.10, USB16.11
unnamed: R166.2, RGBLED16.2
unnamed: R167.2, RGBLED16.3
unnamed: R168.2, RGBLED16.4
unnamed: R169.2, R170.1, USB16.4
unnamed: BTN17.1, R171.1
unnamed: C443.1, IMU17.P$10
unnamed: FB18.1, USB17.5, USB17.6, USB17.7, USB17.8, USB17.9, USB17.10, USB17.11
unnamed: R176.2, RGBLED17.2
unnamed: R177.2, RGBLED17.3
unnamed: R178.2, RGBLED17.4
unnamed: R179.2, R180.1, USB17.4
unnamed: BTN18.1, R181.1
unnamed: C468.1, IMU18.P$10
unnamed: FB19.1, USB18.5, USB18.6, USB18.7, USB18.8, USB18.9, USB18.10, USB18.11
unnamed: R186.2, RGBLED18.2
unnamed: R187.2, RGBLED18.3
unnamed: R188.2, RGBLED18.4
unnamed: R189.2, R190.1, USB18.4
unnamed: BTN19.1, R191.1
unnamed: C493.1, IMU19.P$10
unnamed: FB20.1, USB19.5, USB19.6, USB19.7, USB19.8, USB19.9, USB19.10, USB19.11
unnamed: R196.2, RGBLED19.2
unnamed: R197.2, RGBLED19.3
unnamed: R198.2, RGBLED19.4
unnamed: R199.2, R200.1, USB19.4
PA1: IC1.27, R19.1, U$20.P$1
PA2: IC2.27, R29.1, U$42.P$1
PA3: IC3.27, R39.1, U$65.P$1
PA4: IC4.27, R49.1, U$82.P$1
PA5: IC5.27, R59.1, U$99.P$1
PA6: IC6.27, R69.1, U$116.P$1
PA06(R): IC.7, R4.1, U$54.P$1
PA06(R)1: IC1.7, R16.1, U$21.P$1
PA06(R)2: IC2.7, R26.1, U$44.P$1
PA06(R)3: IC3.7, R36.1, U$66.P$1
PA06(R)4: IC4.7, R46.1, U$83.P$1
PA06(R)5: IC5.7, R56.1, U$100.P$1
PA06(R)6: IC6.7, R66.1, U$117.P$1
PA06(R)7: IC7.7, R76.1, U$134.P$1
PA06(R)8: IC8.7, R86.1, U$151.P$1
PA06(R)9: IC9.7, R96.1, U$168.P$1
PA06(R)10: IC10.7, R106.1, U$185.P$1
PA06(R)11: IC11.7, R116.1, U$202.P$1
PA06(R)12: IC12.7, R126.1, U$219.P$1
PA06(R)13: IC13.7, R136.1, U$236.P$1
PA06(R)14: IC14.7, R146.1, U$253.P$1
PA06(R)15: IC15.7, R156.1, U$270.P$1
PA06(R)16: IC16.7, R166.1, U$287.P$1
PA06(R)17: IC17.7, R176.1, U$304.P$1
PA06(R)18: IC18.7, R186.1, U$321.P$1
PA06(R)19: IC19.7, R196.1, U$338.P$1
PA7: IC7.27, R79.1, U$133.P$1
PA07(G): IC.8, R6.1, U$43.P$1
PA07(G)1: IC1.8, R17.1, U$15.P$1
PA07(G)2: IC2.8, R27.1, U$32.P$1
PA07(G)3: IC3.8, R37.1, U$60.P$1
PA07(G)4: IC4.8, R47.1, U$77.P$1
PA07(G)5: IC5.8, R57.1, U$94.P$1
PA07(G)6: IC6.8, R67.1, U$111.P$1
PA07(G)7: IC7.8, R77.1, U$128.P$1
PA07(G)8: IC8.8, R87.1, U$145.P$1
PA07(G)9: IC9.8, R97.1, U$162.P$1
PA07(G)10: IC10.8, R107.1, U$179.P$1
PA07(G)11: IC11.8, R117.1, U$196.P$1
PA07(G)12: IC12.8, R127.1, U$213.P$1
PA07(G)13: IC13.8, R137.1, U$230.P$1
PA07(G)14: IC14.8, R147.1, U$247.P$1
PA07(G)15: IC15.8, R157.1, U$264.P$1
PA07(G)16: IC16.8, R167.1, U$281.P$1
PA07(G)17: IC17.8, R177.1, U$298.P$1
PA07(G)18: IC18.8, R187.1, U$315.P$1
PA07(G)19: IC19.8, R197.1, U$332.P$1
PA8: IC8.27, R89.1, U$150.P$1
PA08/I2C/SDA: ASWITCH.PIN6, C19.1, IC.9
PA08/I2C/SDA1: ASWITCH1.PIN6, C48.1, IC1.9
PA08/I2C/SDA2: ASWITCH2.PIN6, C73.1, IC2.9
PA08/I2C/SDA3: ASWITCH3.PIN6, C98.1, IC3.9
PA08/I2C/SDA4: ASWITCH4.PIN6, C123.1, IC4.9
PA08/I2C/SDA5: ASWITCH5.PIN6, C148.1, IC5.9
PA08/I2C/SDA6: ASWITCH6.PIN6, C173.1, IC6.9
PA08/I2C/SDA7: ASWITCH7.PIN6, C198.1, IC7.9
PA08/I2C/SDA8: ASWITCH8.PIN6, C223.1, IC8.9
PA08/I2C/SDA9: ASWITCH9.PIN6, C248.1, IC9.9
PA08/I2C/SDA10: ASWITCH10.PIN6, C273.1, IC10.9
PA08/I2C/SDA11: ASWITCH11.PIN6, C298.1, IC11.9
PA08/I2C/SDA12: ASWITCH12.PIN6, C323.1, IC12.9
PA08/I2C/SDA13: ASWITCH13.PIN6, C348.1, IC13.9
PA08/I2C/SDA14: ASWITCH14.PIN6, C373.1, IC14.9
PA08/I2C/SDA15: ASWITCH15.PIN6, C398.1, IC15.9
PA08/I2C/SDA16: ASWITCH16.PIN6, C423.1, IC16.9
PA08/I2C/SDA17: ASWITCH17.PIN6, C448.1, IC17.9
PA08/I2C/SDA18: ASWITCH18.PIN6, C473.1, IC18.9
PA08/I2C/SDA19: ASWITCH19.PIN6, C498.1, IC19.9
PA9: IC9.27, R99.1, U$167.P$1
PA09/I2C/SCL: ASWITCH.PIN4, C18.2, IC.10
PA09/I2C/SCL1: ASWITCH1.PIN4, C47.2, IC1.10
PA09/I2C/SCL2: ASWITCH2.PIN4, C72.2, IC2.10
PA09/I2C/SCL3: ASWITCH3.PIN4, C97.2, IC3.10
PA09/I2C/SCL4: ASWITCH4.PIN4, C122.2, IC4.10
PA09/I2C/SCL5: ASWITCH5.PIN4, C147.2, IC5.10
PA09/I2C/SCL6: ASWITCH6.PIN4, C172.2, IC6.10
PA09/I2C/SCL7: ASWITCH7.PIN4, C197.2, IC7.10
PA09/I2C/SCL8: ASWITCH8.PIN4, C222.2, IC8.10
PA09/I2C/SCL9: ASWITCH9.PIN4, C247.2, IC9.10
PA09/I2C/SCL10: ASWITCH10.PIN4, C272.2, IC10.10
PA09/I2C/SCL11: ASWITCH11.PIN4, C297.2, IC11.10
PA09/I2C/SCL12: ASWITCH12.PIN4, C322.2, IC12.10
PA09/I2C/SCL13: ASWITCH13.PIN4, C347.2, IC13.10
PA09/I2C/SCL14: ASWITCH14.PIN4, C372.2, IC14.10
PA09/I2C/SCL15: ASWITCH15.PIN4, C397.2, IC15.10
PA09/I2C/SCL16: ASWITCH16.PIN4, C422.2, IC16.10
PA09/I2C/SCL17: ASWITCH17.PIN4, C447.2, IC17.10
PA09/I2C/SCL18: ASWITCH18.PIN4, C472.2, IC18.10
PA09/I2C/SCL19: ASWITCH19.PIN4, C497.2, IC19.10
PA10: IC10.27, R109.1, U$184.P$1
PA11: IC11.27, R119.1, U$201.P$1
PA12: IC12.27, R129.1, U$218.P$1
PA13: IC13.27, R139.1, U$235.P$1
PA14: IC14.27, R149.1, U$252.P$1
PA15: IC15.27, R159.1, U$269.P$1
PA15/XOUT_MC/TX: IC.16, U$39.P$1
PA15/XOUT_MC/TX1: IC1.16, U$14.P$1
PA15/XOUT_MC/TX2: IC2.16, U$31.P$1
PA15/XOUT_MC/TX3: IC3.16, U$59.P$1
PA15/XOUT_MC/TX4: IC4.16, U$76.P$1
PA15/XOUT_MC/TX5: IC5.16, U$93.P$1
PA15/XOUT_MC/TX6: IC6.16, U$110.P$1
PA15/XOUT_MC/TX7: IC7.16, U$127.P$1
PA15/XOUT_MC/TX8: IC8.16, U$144.P$1
PA15/XOUT_MC/TX9: IC9.16, U$161.P$1
PA15/XOUT_MC/TX10: IC10.16, U$178.P$1
PA15/XOUT_MC/TX11: IC11.16, U$195.P$1
PA15/XOUT_MC/TX12: IC12.16, U$212.P$1
PA15/XOUT_MC/TX13: IC13.16, U$229.P$1
PA15/XOUT_MC/TX14: IC14.16, U$246.P$1
PA15/XOUT_MC/TX15: IC15.16, U$263.P$1
PA15/XOUT_MC/TX16: IC16.16, U$280.P$1
PA15/XOUT_MC/TX17: IC17.16, U$297.P$1
PA15/XOUT_MC/TX18: IC18.16, U$314.P$1
PA15/XOUT_MC/TX19: IC19.16, U$331.P$1
PA16: IC16.27, R169.1, U$286.P$1
PA16/I2C: BARO.7, IC.17, IMU.P$24, R8.1, U$38.P$1
PA16/I2C1: BARO1.7, IC1.17, IMU1.P$24, R13.1, U$13.P$1
PA16/I2C2: BARO2.7, IC2.17, IMU2.P$24, R23.1, U$30.P$1
PA16/I2C3: BARO3.7, IC3.17, IMU3.P$24, R33.1, U$58.P$1
PA16/I2C4: BARO4.7, IC4.17, IMU4.P$24, R43.1, U$75.P$1
PA16/I2C5: BARO5.7, IC5.17, IMU5.P$24, R53.1, U$92.P$1
PA16/I2C6: BARO6.7, IC6.17, IMU6.P$24, R63.1, U$109.P$1
PA16/I2C7: BARO7.7, IC7.17, IMU7.P$24, R73.1, U$126.P$1
PA16/I2C8: BARO8.7, IC8.17, IMU8.P$24, R83.1, U$143.P$1
PA16/I2C9: BARO9.7, IC9.17, IMU9.P$24, R93.1, U$160.P$1
PA16/I2C10: BARO10.7, IC10.17, IMU10.P$24, R103.1, U$177.P$1
PA16/I2C11: BARO11.7, IC11.17, IMU11.P$24, R113.1, U$194.P$1
PA16/I2C12: BARO12.7, IC12.17, IMU12.P$24, R123.1, U$211.P$1
PA16/I2C13: BARO13.7, IC13.17, IMU13.P$24, R133.1, U$228.P$1
PA16/I2C14: BARO14.7, IC14.17, IMU14.P$24, R143.1, U$245.P$1
PA16/I2C15: BARO15.7, IC15.17, IMU15.P$24, R153.1, U$262.P$1
PA16/I2C16: BARO16.7, IC16.17, IMU16.P$24, R163.1, U$279.P$1
PA16/I2C17: BARO17.7, IC17.17, IMU17.P$24, R173.1, U$296.P$1
PA16/I2C18: BARO18.7, IC18.17, IMU18.P$24, R183.1, U$313.P$1
PA16/I2C19: BARO19.7, IC19.17, IMU19.P$24, R193.1, U$330.P$1
PA17: IC17.27, R179.1, U$303.P$1
PA17/I2C: BARO.8, IC.18, IMU.P$23, R9.1, U$37.P$1
PA17/I2C1: BARO1.8, IC1.18, IMU1.P$23, R14.1, U$12.P$1
PA17/I2C2: BARO2.8, IC2.18, IMU2.P$23, R24.1, U$29.P$1
PA17/I2C3: BARO3.8, IC3.18, IMU3.P$23, R34.1, U$57.P$1
PA17/I2C4: BARO4.8, IC4.18, IMU4.P$23, R44.1, U$74.P$1
PA17/I2C5: BARO5.8, IC5.18, IMU5.P$23, R54.1, U$91.P$1
PA17/I2C6: BARO6.8, IC6.18, IMU6.P$23, R64.1, U$108.P$1
PA17/I2C7: BARO7.8, IC7.18, IMU7.P$23, R74.1, U$125.P$1
PA17/I2C8: BARO8.8, IC8.18, IMU8.P$23, R84.1, U$142.P$1
PA17/I2C9: BARO9.8, IC9.18, IMU9.P$23, R94.1, U$159.P$1
PA17/I2C10: BARO10.8, IC10.18, IMU10.P$23, R104.1, U$176.P$1
PA17/I2C11: BARO11.8, IC11.18, IMU11.P$23, R114.1, U$193.P$1
PA17/I2C12: BARO12.8, IC12.18, IMU12.P$23, R124.1, U$210.P$1
PA17/I2C13: BARO13.8, IC13.18, IMU13.P$23, R134.1, U$227.P$1
PA17/I2C14: BARO14.8, IC14.18, IMU14.P$23, R144.1, U$244.P$1
PA17/I2C15: BARO15.8, IC15.18, IMU15.P$23, R154.1, U$261.P$1
PA17/I2C16: BARO16.8, IC16.18, IMU16.P$23, R164.1, U$278.P$1
PA17/I2C17: BARO17.8, IC17.18, IMU17.P$23, R174.1, U$295.P$1
PA17/I2C18: BARO18.8, IC18.18, IMU18.P$23, R184.1, U$312.P$1
PA17/I2C19: BARO19.8, IC19.18, IMU19.P$23, R194.1, U$329.P$1
PA18: IC18.27, R189.1, U$320.P$1
PA18/FSYNC: IC.19, IMU.P$11, R3.2, U$36.P$1
PA18/FSYNC1: IC1.19, IMU1.P$11, R15.2, U$11.P$1
PA18/FSYNC2: IC2.19, IMU2.P$11, R25.2, U$28.P$1
PA18/FSYNC3: IC3.19, IMU3.P$11, R35.2, U$56.P$1
PA18/FSYNC4: IC4.19, IMU4.P$11, R45.2, U$73.P$1
PA18/FSYNC5: IC5.19, IMU5.P$11, R55.2, U$90.P$1
PA18/FSYNC6: IC6.19, IMU6.P$11, R65.2, U$107.P$1
PA18/FSYNC7: IC7.19, IMU7.P$11, R75.2, U$124.P$1
PA18/FSYNC8: IC8.19, IMU8.P$11, R85.2, U$141.P$1
PA18/FSYNC9: IC9.19, IMU9.P$11, R95.2, U$158.P$1
PA18/FSYNC10: IC10.19, IMU10.P$11, R105.2, U$175.P$1
PA18/FSYNC11: IC11.19, IMU11.P$11, R115.2, U$192.P$1
PA18/FSYNC12: IC12.19, IMU12.P$11, R125.2, U$209.P$1
PA18/FSYNC13: IC13.19, IMU13.P$11, R135.2, U$226.P$1
PA18/FSYNC14: IC14.19, IMU14.P$11, R145.2, U$243.P$1
PA18/FSYNC15: IC15.19, IMU15.P$11, R155.2, U$260.P$1
PA18/FSYNC16: IC16.19, IMU16.P$11, R165.2, U$277.P$1
PA18/FSYNC17: IC17.19, IMU17.P$11, R175.2, U$294.P$1
PA18/FSYNC18: IC18.19, IMU18.P$11, R185.2, U$311.P$1
PA18/FSYNC19: IC19.19, IMU19.P$11, R195.2, U$328.P$1
PA19: IC19.27, R199.1, U$337.P$1
PA19/INTA: IC.20, IMU.P$12, U$35.P$1
PA19/INTA1: IC1.20, IMU1.P$12, U$8.P$1
PA19/INTA2: IC2.20, IMU2.P$12, U$27.P$1
PA19/INTA3: IC3.20, IMU3.P$12, U$55.P$1
PA19/INTA4: IC4.20, IMU4.P$12, U$72.P$1
PA19/INTA5: IC5.20, IMU5.P$12, U$89.P$1
PA19/INTA6: IC6.20, IMU6.P$12, U$106.P$1
PA19/INTA7: IC7.20, IMU7.P$12, U$123.P$1
PA19/INTA8: IC8.20, IMU8.P$12, U$140.P$1
PA19/INTA9: IC9.20, IMU9.P$12, U$157.P$1
PA19/INTA10: IC10.20, IMU10.P$12, U$174.P$1
PA19/INTA11: IC11.20, IMU11.P$12, U$191.P$1
PA19/INTA12: IC12.20, IMU12.P$12, U$208.P$1
PA19/INTA13: IC13.20, IMU13.P$12, U$225.P$1
PA19/INTA14: IC14.20, IMU14.P$12, U$242.P$1
PA19/INTA15: IC15.20, IMU15.P$12, U$259.P$1
PA19/INTA16: IC16.20, IMU16.P$12, U$276.P$1
PA19/INTA17: IC17.20, IMU17.P$12, U$293.P$1
PA19/INTA18: IC18.20, IMU18.P$12, U$310.P$1
PA19/INTA19: IC19.20, IMU19.P$12, U$327.P$1
PA24/USBDM: IC.22, U$9.P$1, USB.2
PA24/USBDM1: IC1.22, U$22.P$1, USB1.2
PA24/USBDM2: IC2.22, U$49.P$1, USB2.2
PA24/USBDM3: IC3.22, U$67.P$1, USB3.2
PA24/USBDM4: IC4.22, U$84.P$1, USB4.2
PA24/USBDM5: IC5.22, U$101.P$1, USB5.2
PA24/USBDM6: IC6.22, U$118.P$1, USB6.2
PA24/USBDM7: IC7.22, U$135.P$1, USB7.2
PA24/USBDM8: IC8.22, U$152.P$1, USB8.2
PA24/USBDM9: IC9.22, U$169.P$1, USB9.2
PA24/USBDM10: IC10.22, U$186.P$1, USB10.2
PA24/USBDM11: IC11.22, U$203.P$1, USB11.2
PA24/USBDM12: IC12.22, U$220.P$1, USB12.2
PA24/USBDM13: IC13.22, U$237.P$1, USB13.2
PA24/USBDM14: IC14.22, U$254.P$1, USB14.2
PA24/USBDM15: IC15.22, U$271.P$1, USB15.2
PA24/USBDM16: IC16.22, U$288.P$1, USB16.2
PA24/USBDM17: IC17.22, U$305.P$1, USB17.2
PA24/USBDM18: IC18.22, U$322.P$1, USB18.2
PA24/USBDM19: IC19.22, U$339.P$1, USB19.2
PA25/USBDP: IC.23, U$10.P$1, USB.3
PA25/USBDP1: IC1.23, U$23.P$1, USB1.3
PA25/USBDP2: IC2.23, U$50.P$1, USB2.3
PA25/USBDP3: IC3.23, U$68.P$1, USB3.3
PA25/USBDP4: IC4.23, U$85.P$1, USB4.3
PA25/USBDP5: IC5.23, U$102.P$1, USB5.3
PA25/USBDP6: IC6.23, U$119.P$1, USB6.3
PA25/USBDP7: IC7.23, U$136.P$1, USB7.3
PA25/USBDP8: IC8.23, U$153.P$1, USB8.3
PA25/USBDP9: IC9.23, U$170.P$1, USB9.3
PA25/USBDP10: IC10.23, U$187.P$1, USB10.3
PA25/USBDP11: IC11.23, U$204.P$1, USB11.3
PA25/USBDP12: IC12.23, U$221.P$1, USB12.3
PA25/USBDP13: IC13.23, U$238.P$1, USB13.3
PA25/USBDP14: IC14.23, U$255.P$1, USB14.3
PA25/USBDP15: IC15.23, U$272.P$1, USB15.3
PA25/USBDP16: IC16.23, U$289.P$1, USB16.3
PA25/USBDP17: IC17.23, U$306.P$1, USB17.3
PA25/USBDP18: IC18.23, U$323.P$1, USB18.3
PA25/USBDP19: IC19.23, U$340.P$1, USB19.3
PA27(B): IC.25, R7.1, U$7.P$1
PA27(B)1: IC1.25, R18.1, U$19.P$1
PA27(B)2: IC2.25, R28.1, U$41.P$1
PA27(B)3: IC3.25, R38.1, U$64.P$1
PA27(B)4: IC4.25, R48.1, U$81.P$1
PA27(B)5: IC5.25, R58.1, U$98.P$1
PA27(B)6: IC6.25, R68.1, U$115.P$1
PA27(B)7: IC7.25, R78.1, U$132.P$1
PA27(B)8: IC8.25, R88.1, U$149.P$1
PA27(B)9: IC9.25, R98.1, U$166.P$1
PA27(B)10: IC10.25, R108.1, U$183.P$1
PA27(B)11: IC11.25, R118.1, U$200.P$1
PA27(B)12: IC12.25, R128.1, U$217.P$1
PA27(B)13: IC13.25, R138.1, U$234.P$1
PA27(B)14: IC14.25, R148.1, U$251.P$1
PA27(B)15: IC15.25, R158.1, U$268.P$1
PA27(B)16: IC16.25, R168.1, U$285.P$1
PA27(B)17: IC17.25, R178.1, U$302.P$1
PA27(B)18: IC18.25, R188.1, U$319.P$1
PA27(B)19: IC19.25, R198.1, U$336.P$1
PA28: IC.27, R5.1, U$48.P$1
PA30/SWCLK: IC.31, U$46.P$1
PA30/SWCLK1: IC1.31, U$17.P$1
PA30/SWCLK2: IC2.31, U$34.P$1
PA30/SWCLK3: IC3.31, U$62.P$1
PA30/SWCLK4: IC4.31, U$79.P$1
PA30/SWCLK5: IC5.31, U$96.P$1
PA30/SWCLK6: IC6.31, U$113.P$1
PA30/SWCLK7: IC7.31, U$130.P$1
PA30/SWCLK8: IC8.31, U$147.P$1
PA30/SWCLK9: IC9.31, U$164.P$1
PA30/SWCLK10: IC10.31, U$181.P$1
PA30/SWCLK11: IC11.31, U$198.P$1
PA30/SWCLK12: IC12.31, U$215.P$1
PA30/SWCLK13: IC13.31, U$232.P$1
PA30/SWCLK14: IC14.31, U$249.P$1
PA30/SWCLK15: IC15.31, U$266.P$1
PA30/SWCLK16: IC16.31, U$283.P$1
PA30/SWCLK17: IC17.31, U$300.P$1
PA30/SWCLK18: IC18.31, U$317.P$1
PA30/SWCLK19: IC19.31, U$334.P$1
PA31/SWDIO: IC.32, U$47.P$1
PA31/SWDIO1: IC1.32, U$18.P$1
PA31/SWDIO2: IC2.32, U$40.P$1
PA31/SWDIO3: IC3.32, U$63.P$1
PA31/SWDIO4: IC4.32, U$80.P$1
PA31/SWDIO5: IC5.32, U$97.P$1
PA31/SWDIO6: IC6.32, U$114.P$1
PA31/SWDIO7: IC7.32, U$131.P$1
PA31/SWDIO8: IC8.32, U$148.P$1
PA31/SWDIO9: IC9.32, U$165.P$1
PA31/SWDIO10: IC10.32, U$182.P$1
PA31/SWDIO11: IC11.32, U$199.P$1
PA31/SWDIO12: IC12.32, U$216.P$1
PA31/SWDIO13: IC13.32, U$233.P$1
PA31/SWDIO14: IC14.32, U$250.P$1
PA31/SWDIO15: IC15.32, U$267.P$1
PA31/SWDIO16: IC16.32, U$284.P$1
PA31/SWDIO17: IC17.32, U$301.P$1
PA31/SWDIO18: IC18.32, U$318.P$1
PA31/SWDIO19: IC19.32, U$335.P$1
RESET: C1.1, IC.26, R1.2, R2.1, U$45.P$1
RESET1: C3.1, IC1.26, R11.2, R12.1, U$16.P$1
RESET2: C51.1, IC2.26, R21.2, R22.1, U$33.P$1
RESET3: C76.1, IC3.26, R31.2, R32.1, U$61.P$1
RESET4: C101.1, IC4.26, R41.2, R42.1, U$78.P$1
RESET5: C126.1, IC5.26, R51.2, R52.1, U$95.P$1
RESET6: C151.1, IC6.26, R61.2, R62.1, U$112.P$1
RESET7: C176.1, IC7.26, R71.2, R72.1, U$129.P$1
RESET8: C201.1, IC8.26, R81.2, R82.1, U$146.P$1
RESET9: C226.1, IC9.26, R91.2, R92.1, U$163.P$1
RESET10: C251.1, IC10.26, R101.2, R102.1, U$180.P$1
RESET11: C276.1, IC11.26, R111.2, R112.1, U$197.P$1
RESET12: C301.1, IC12.26, R121.2, R122.1, U$214.P$1
RESET13: C326.1, IC13.26, R131.2, R132.1, U$231.P$1
RESET14: C351.1, IC14.26, R141.2, R142.1, U$248.P$1
RESET15: C376.1, IC15.26, R151.2, R152.1, U$265.P$1
RESET16: C401.1, IC16.26, R161.2, R162.1, U$282.P$1
RESET17: C426.1, IC17.26, R171.2, R172.1, U$299.P$1
RESET18: C451.1, IC18.26, R181.2, R182.1, U$316.P$1
RESET19: C476.1, IC19.26, R191.2, R192.1, U$333.P$1
RFN: BALUN.3, IC.13
RFN1: BALUN1.3, IC1.13
RFN2: BALUN2.3, IC2.13
RFN3: BALUN3.3, IC3.13
RFN4: BALUN4.3, IC4.13
RFN5: BALUN5.3, IC5.13
RFN6: BALUN6.3, IC6.13
RFN7: BALUN7.3, IC7.13
RFN8: BALUN8.3, IC8.13
RFN9: BALUN9.3, IC9.13
RFN10: BALUN10.3, IC10.13
RFN11: BALUN11.3, IC11.13
RFN12: BALUN12.3, IC12.13
RFN13: BALUN13.3, IC13.13
RFN14: BALUN14.3, IC14.13
RFN15: BALUN15.3, IC15.13
RFN16: BALUN16.3, IC16.13
RFN17: BALUN17.3, IC17.13
RFN18: BALUN18.3, IC18.13
RFN19: BALUN19.3, IC19.13
RFP: BALUN.4, IC.12
RFP1: BALUN1.4, IC1.12
RFP2: BALUN2.4, IC2.12
RFP3: BALUN3.4, IC3.12
RFP4: BALUN4.4, IC4.12
RFP5: BALUN5.4, IC5.12
RFP6: BALUN6.4, IC6.12
RFP7: BALUN7.4, IC7.12
RFP8: BALUN8.4, IC8.12
RFP9: BALUN9.4, IC9.12
RFP10: BALUN10.4, IC10.12
RFP11: BALUN11.4, IC11.12
RFP12: BALUN12.4, IC12.12
RFP13: BALUN13.4, IC13.12
RFP14: BALUN14.4, IC14.12
RFP15: BALUN15.4, IC15.12
RFP16: BALUN16.4, IC16.12
RFP17: BALUN17.4, IC17.12
RFP18: BALUN18.4, IC18.12
RFP19: BALUN19.4, IC19.12
RFSWITCH_PIN1: ASWITCH.PIN1, C23.1
RFSWITCH_PIN2: ASWITCH1.PIN1, C50.1
RFSWITCH_PIN3: ASWITCH.PIN3, C20.2
RFSWITCH_PIN4: ASWITCH1.PIN5, C46.2
RFSWITCH_PIN5: ASWITCH.PIN5, C12.2
RFSWITCH_PIN6: ASWITCH1.PIN3, C49.2
RFSWITCH_PIN7: ASWITCH2.PIN1, C75.1
RFSWITCH_PIN8: ASWITCH2.PIN5, C71.2
RFSWITCH_PIN9: ASWITCH2.PIN3, C74.2
RFSWITCH_PIN10: ASWITCH3.PIN1, C100.1
RFSWITCH_PIN11: ASWITCH3.PIN5, C96.2
RFSWITCH_PIN12: ASWITCH3.PIN3, C99.2
RFSWITCH_PIN13: ASWITCH4.PIN1, C125.1
RFSWITCH_PIN14: ASWITCH4.PIN5, C121.2
RFSWITCH_PIN15: ASWITCH4.PIN3, C124.2
RFSWITCH_PIN16: ASWITCH5.PIN1, C150.1
RFSWITCH_PIN17: ASWITCH5.PIN5, C146.2
RFSWITCH_PIN18: ASWITCH5.PIN3, C149.2
RFSWITCH_PIN19: ASWITCH6.PIN1, C175.1
RFSWITCH_PIN20: ASWITCH6.PIN5, C171.2
RFSWITCH_PIN21: ASWITCH6.PIN3, C174.2
RFSWITCH_PIN22: ASWITCH7.PIN1, C200.1
RFSWITCH_PIN23: ASWITCH7.PIN5, C196.2
RFSWITCH_PIN24: ASWITCH7.PIN3, C199.2
RFSWITCH_PIN25: ASWITCH8.PIN1, C225.1
RFSWITCH_PIN26: ASWITCH8.PIN5, C221.2
RFSWITCH_PIN27: ASWITCH8.PIN3, C224.2
RFSWITCH_PIN28: ASWITCH9.PIN1, C250.1
RFSWITCH_PIN29: ASWITCH9.PIN5, C246.2
RFSWITCH_PIN30: ASWITCH9.PIN3, C249.2
RFSWITCH_PIN31: ASWITCH10.PIN1, C275.1
RFSWITCH_PIN32: ASWITCH10.PIN5, C271.2
RFSWITCH_PIN33: ASWITCH10.PIN3, C274.2
RFSWITCH_PIN34: ASWITCH11.PIN1, C300.1
RFSWITCH_PIN35: ASWITCH11.PIN5, C296.2
RFSWITCH_PIN36: ASWITCH11.PIN3, C299.2
RFSWITCH_PIN37: ASWITCH12.PIN1, C325.1
RFSWITCH_PIN38: ASWITCH12.PIN5, C321.2
RFSWITCH_PIN39: ASWITCH12.PIN3, C324.2
RFSWITCH_PIN40: ASWITCH13.PIN1, C350.1
RFSWITCH_PIN41: ASWITCH13.PIN5, C346.2
RFSWITCH_PIN42: ASWITCH13.PIN3, C349.2
RFSWITCH_PIN43: ASWITCH14.PIN1, C375.1
RFSWITCH_PIN44: ASWITCH14.PIN5, C371.2
RFSWITCH_PIN45: ASWITCH14.PIN3, C374.2
RFSWITCH_PIN46: ASWITCH15.PIN1, C400.1
RFSWITCH_PIN47: ASWITCH15.PIN5, C396.2
RFSWITCH_PIN48: ASWITCH15.PIN3, C399.2
RFSWITCH_PIN49: ASWITCH16.PIN1, C425.1
RFSWITCH_PIN50: ASWITCH16.PIN5, C421.2
RFSWITCH_PIN51: ASWITCH16.PIN3, C424.2
RFSWITCH_PIN52: ASWITCH17.PIN1, C450.1
RFSWITCH_PIN53: ASWITCH17.PIN5, C446.2
RFSWITCH_PIN54: ASWITCH17.PIN3, C449.2
RFSWITCH_PIN55: ASWITCH18.PIN1, C475.1
RFSWITCH_PIN56: ASWITCH18.PIN5, C471.2
RFSWITCH_PIN57: ASWITCH18.PIN3, C474.2
RFSWITCH_PIN58: ASWITCH19.PIN1, C500.1
RFSWITCH_PIN59: ASWITCH19.PIN5, C496.2
RFSWITCH_PIN60: ASWITCH19.PIN3, C499.2
VDDANA: C8.1, C22.2, IC.4, L6.2
VDDANA1: C28.1, C37.2, IC1.4, L2.2
VDDANA2: C57.1, C62.2, IC2.4, L4.2
VDDANA3: C82.1, C87.2, IC3.4, L7.2
VDDANA4: C107.1, C112.2, IC4.4, L9.2
VDDANA5: C132.1, C137.2, IC5.4, L11.2
VDDANA6: C157.1, C162.2, IC6.4, L13.2
VDDANA7: C182.1, C187.2, IC7.4, L15.2
VDDANA8: C207.1, C212.2, IC8.4, L17.2
VDDANA9: C232.1, C237.2, IC9.4, L19.2
VDDANA10: C257.1, C262.2, IC10.4, L21.2
VDDANA11: C282.1, C287.2, IC11.4, L23.2
VDDANA12: C307.1, C312.2, IC12.4, L25.2
VDDANA13: C332.1, C337.2, IC13.4, L27.2
VDDANA14: C357.1, C362.2, IC14.4, L29.2
VDDANA15: C382.1, C387.2, IC15.4, L31.2
VDDANA16: C407.1, C412.2, IC16.4, L33.2
VDDANA17: C432.1, C437.2, IC17.4, L35.2
VDDANA18: C457.1, C462.2, IC18.4, L37.2
VDDANA19: C482.1, C487.2, IC19.4, L39.2
VDDCORE: C9.1, IC.29
VDDCORE1: C33.1, IC1.29
VDDCORE2: C58.1, IC2.29
VDDCORE3: C83.1, IC3.29
VDDCORE4: C108.1, IC4.29
VDDCORE5: C133.1, IC5.29
VDDCORE6: C158.1, IC6.29
VDDCORE7: C183.1, IC7.29
VDDCORE8: C208.1, IC8.29
VDDCORE9: C233.1, IC9.29
VDDCORE10: C258.1, IC10.29
VDDCORE11: C283.1, IC11.29
VDDCORE12: C308.1, IC12.29
VDDCORE13: C333.1, IC13.29
VDDCORE14: C358.1, IC14.29
VDDCORE15: C383.1, IC15.29
VDDCORE16: C408.1, IC16.29
VDDCORE17: C433.1, IC17.29
VDDCORE18: C458.1, IC18.29
VDDCORE19: C483.1, IC19.29
VIN: C6.1, C7.1, LDO_VREG.VIN, U$1.P$1, USB.1
VIN1: C25.1, C26.1, LDO_VREG1.VIN, U$3.P$1, USB1.1
VIN2: C54.1, C55.1, LDO_VREG2.VIN, U$24.P$1, USB2.1
VIN3: C79.1, C80.1, LDO_VREG3.VIN, U$51.P$1, USB3.1
VIN4: C104.1, C105.1, LDO_VREG4.VIN, U$69.P$1, USB4.1
VIN5: C129.1, C130.1, LDO_VREG5.VIN, U$86.P$1, USB5.1
VIN6: C154.1, C155.1, LDO_VREG6.VIN, U$103.P$1, USB6.1
VIN7: C179.1, C180.1, LDO_VREG7.VIN, U$120.P$1, USB7.1
VIN8: C204.1, C205.1, LDO_VREG8.VIN, U$137.P$1, USB8.1
VIN9: C229.1, C230.1, LDO_VREG9.VIN, U$154.P$1, USB9.1
VIN10: C254.1, C255.1, LDO_VREG10.VIN, U$171.P$1, USB10.1
VIN11: C279.1, C280.1, LDO_VREG11.VIN, U$188.P$1, USB11.1
VIN12: C304.1, C305.1, LDO_VREG12.VIN, U$205.P$1, USB12.1
VIN13: C329.1, C330.1, LDO_VREG13.VIN, U$222.P$1, USB13.1
VIN14: C354.1, C355.1, LDO_VREG14.VIN, U$239.P$1, USB14.1
VIN15: C379.1, C380.1, LDO_VREG15.VIN, U$256.P$1, USB15.1
VIN16: C404.1, C405.1, LDO_VREG16.VIN, U$273.P$1, USB16.1
VIN17: C429.1, C430.1, LDO_VREG17.VIN, U$290.P$1, USB17.1
VIN18: C454.1, C455.1, LDO_VREG18.VIN, U$307.P$1, USB18.1
VIN19: C479.1, C480.1, LDO_VREG19.VIN, U$324.P$1, USB19.1
XTALIN: C14.2, IC.2, XOSCRF.1
XTALIN1: C39.2, IC1.2, XOSCRF1.1
XTALIN2: C64.2, IC2.2, XOSCRF2.1
XTALIN3: C89.2, IC3.2, XOSCRF3.1
XTALIN4: C114.2, IC4.2, XOSCRF4.1
XTALIN5: C139.2, IC5.2, XOSCRF5.1
XTALIN6: C164.2, IC6.2, XOSCRF6.1
XTALIN7: C189.2, IC7.2, XOSCRF7.1
XTALIN8: C214.2, IC8.2, XOSCRF8.1
XTALIN9: C239.2, IC9.2, XOSCRF9.1
XTALIN10: C264.2, IC10.2, XOSCRF10.1
XTALIN11: C289.2, IC11.2, XOSCRF11.1
XTALIN12: C314.2, IC12.2, XOSCRF12.1
XTALIN13: C339.2, IC13.2, XOSCRF13.1
XTALIN14: C364.2, IC14.2, XOSCRF14.1
XTALIN15: C389.2, IC15.2, XOSCRF15.1
XTALIN16: C414.2, IC16.2, XOSCRF16.1
XTALIN17: C439.2, IC17.2, XOSCRF17.1
XTALIN18: C464.2, IC18.2, XOSCRF18.1
XTALIN19: C489.2, IC19.2, XOSCRF19.1
XTALOUT: C15.1, IC.1, XOSCRF.3
XTALOUT1: C40.1, IC1.1, XOSCRF1.3
XTALOUT2: C65.1, IC2.1, XOSCRF2.3
XTALOUT3: C90.1, IC3.1, XOSCRF3.3
XTALOUT4: C115.1, IC4.1, XOSCRF4.3
XTALOUT5: C140.1, IC5.1, XOSCRF5.3
XTALOUT6: C165.1, IC6.1, XOSCRF6.3
XTALOUT7: C190.1, IC7.1, XOSCRF7.3
XTALOUT8: C215.1, IC8.1, XOSCRF8.3
XTALOUT9: C240.1, IC9.1, XOSCRF9.3
XTALOUT10: C265.1, IC10.1, XOSCRF10.3
XTALOUT11: C290.1, IC11.1, XOSCRF11.3
XTALOUT12: C315.1, IC12.1, XOSCRF12.3
XTALOUT13: C340.1, IC13.1, XOSCRF13.3
XTALOUT14: C365.1, IC14.1, XOSCRF14.3
XTALOUT15: C390.1, IC15.1, XOSCRF15.3
XTALOUT16: C415.1, IC16.1, XOSCRF16.3
XTALOUT17: C440.1, IC17.1, XOSCRF17.3
XTALOUT18: C465.1, IC18.1, XOSCRF18.3
XTALOUT19: C490.1, IC19.1, XOSCRF19.3
