femtoduino/femto-beacon/Eagle_Files/FemtoBeacon_r2.0.0/femtoBeacon_PRO_r3.0.1_single_sided_PANELIZED_1x5.brd

## EAGLE design Eagle_Files/FemtoBeacon_r2.0.0/femtoBeacon_PRO_r3.0.1_single_sided_PANELIZED_1x5.brd (2018-01-04)

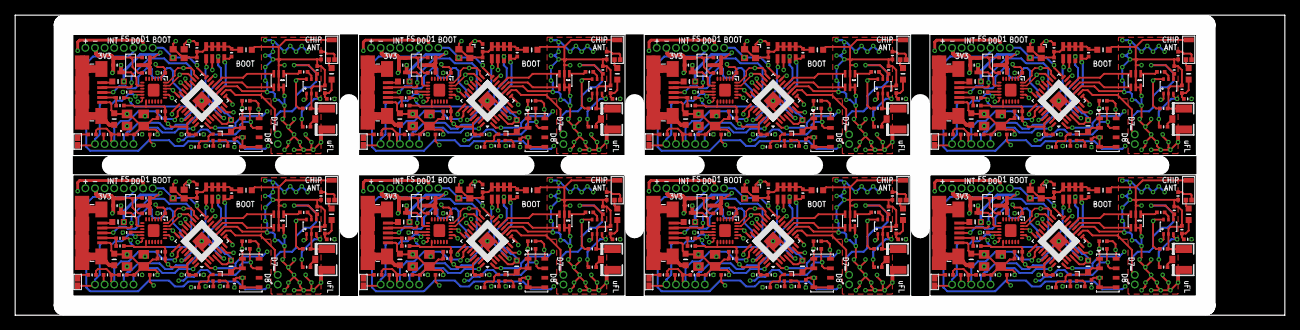
[picture p64: board femtoBeacon_PRO_r3.0.1_single_sided_PANELIZED_1x5.brd from above]

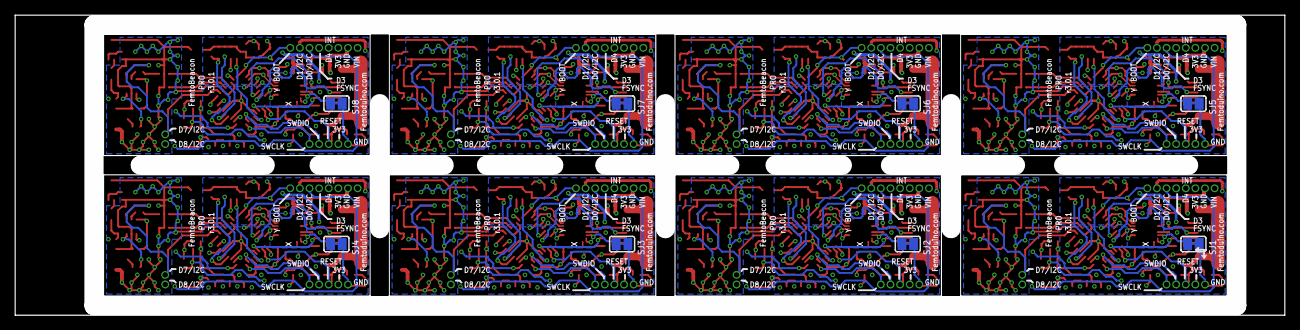
[picture p65: board femtoBeacon_PRO_r3.0.1_single_sided_PANELIZED_1x5.brd from below]

Board: 4 copper layers, 167.6 x 39.6 mm, 440 parts (8 on the bottom side), 352 nets.

Parts:
ASWITCH, ASWITCH1, ASWITCH2, ASWITCH3, ASWITCH4, ASWITCH5, ASWITCH6, ASWITCH7: AS222-92LF
BALUN, BALUN1, BALUN2, BALUN3, BALUN4, BALUN5, BALUN6, BALUN7: JOHANSON_2450BM15A0015E; 0805_BALUN
BARO, BARO1, BARO2, BARO3, BARO4, BARO5, BARO6, BARO7: MS5611-01BA03
BTN_RESET, BTN_RESET1, BTN_RESET2, BTN_RESET3, BTN_RESET4, BTN_RESET5, BTN_RESET6, BTN_RESET7: DNP; SPST_SMD
C1, C10, C16, C18, C24, C25, C28, C29, C30, C32, C39, C40, C47, C51, C52, C55, C62, C63, C70, C74, C75, C78, C85, C86, C93, C97, C98, C101, C108, C109, C116, C120, C121, C124, C131, C132, C139, C143, C144, C147, C154, C155, C162, C166, C167, C170, C177, C178: 0.1uF; _0402MP
C2, C8, C9, C11, C12, C41, C42, C43, C44, C45, C64, C65, C66, C67, C68, C87, C88, C89, C90, C91, C110, C111, C112, C113, C114, C133, C134, C135, C136, C137, C156, C157, C158, C159, C160, C179, C180, C181, C182, C183: 22pF, C0G, 5%; _0402MP
C3, C4, C33, C34, C56, C57, C79, C80, C102, C103, C125, C126, C148, C149, C171, C172: 10pF; _0402MP
C5, C6, C19, C20, C48, C49, C71, C72, C94, C95, C117, C118, C140, C141, C163, C164: 2.2uF; _0402MP
C7, C23, C50, C73, C96, C119, C142, C165: 0.47uF; _0402MP
C13, C35, C58, C81, C104, C127, C150, C173: DNP; _0402MP
C14, C15, C36, C37, C59, C60, C82, C83, C105, C106, C128, C129, C151, C152, C174, C175: 9pF; _0402MP
C17, C46, C69, C92, C115, C138, C161, C184: 1.2pF; _0402MP
C21, C22, C26, C27, C53, C54, C76, C77, C99, C100, C122, C123, C145, C146, C168, C169: 10uF; _0402MP
C31, C38, C61, C84, C107, C130, C153, C176: 10000pF; _0402MP
C_ARR, C_ARR1, C_ARR2, C_ARR3, C_ARR4, C_ARR5, C_ARR6, C_ARR7: 0.1uF; CAPACITOR_ARRAY_1206_MONO_1X4
FB1, FB2, FB3, FB4, FB5, FB6, FB7, FB8, FB9, FB10, FB11, FB12, FB13, FB14, FB15, FB16, FB17, FB18, FB19, FB20, FB21, FB22, FB23, FB24: _0603MP
IC, IC1, IC2, IC3, IC4, IC5, IC6, IC7: ATSAMR21E18A-MUT; QFN32
IMU, IMU1, IMU2, IMU3, IMU4, IMU5, IMU6, IMU7: MPU-9250; QFN_3X3MM
L1, L3, L5, L8, L10, L12, L14, L16: 1.8nH; _0603MP
L2, L4, L6, L7, L9, L11, L13, L15: 10uH; _0603MP
LDO_VREG, LDO_VREG1, LDO_VREG2, LDO_VREG3, LDO_VREG4, LDO_VREG5, LDO_VREG6, LDO_VREG7: MCP1700T-3302E/TT
R1, R3, R4, R6, R7, R10, R12, R15, R17, R18, R19, R21, R24, R26, R27, R28, R30, R33, R35, R36, R37, R39, R42, R44, R45, R46, R48, R51, R53, R54, R55, R57, R60, R62, R63, R64, R66, R69, R71, R72: 330; _0402MP
R2, R11, R20, R29, R38, R47, R56, R65: 10K; _0402MP
R5, R16, R25, R34, R43, R52, R61, R70: 100K; _0402MP
R8, R9, R13, R14, R22, R23, R31, R32, R40, R41, R49, R50, R58, R59, R67, R68: 2.2K; _0402MP
RGBLED, RGBLED1, RGBLED2, RGBLED3, RGBLED4, RGBLED5, RGBLED6, RGBLED7: LRTB_R48G
SJ1, SJ2, SJ3, SJ4, SJ5, SJ6, SJ7, SJ8: SOLDERJUMPER_CLOSEDWIRE
SMDANT, SMDANT1, SMDANT2, SMDANT3, SMDANT4, SMDANT5, SMDANT6, SMDANT7: PULSE_ANT_2.4GHZ; ANT_BAR
U$1, U$4, U$5, U$8, U$13, U$16, U$19, U$22: 1X8_ROUND
U$2, U$6, U$10, U$11, U$14, U$17, U$20, U$23: 1X5_ROUND
U$3, U$7, U$9, U$12, U$15, U$18, U$21, U$24: 1X2_ROUND
UFLANT, UFLANT1, UFLANT2, UFLANT3, UFLANT4, UFLANT5, UFLANT6, UFLANT7: U.FL
USB, USB1, USB2, USB3, USB4, USB5, USB6, USB7: USB_MICROB; USB_MICROB_PACKAGE
XTAL_BOARD, XTAL_BOARD1, XTAL_BOARD2, XTAL_BOARD3, XTAL_BOARD4, XTAL_BOARD5, XTAL_BOARD6, XTAL_BOARD7: 32MHz; FA-128
XTAL_RF, XTAL_RF1, XTAL_RF2, XTAL_RF3, XTAL_RF4, XTAL_RF5, XTAL_RF6, XTAL_RF7: 16MHz; TSX-3225

Connections:
3.3V: BARO.1, BARO.2, C5.1, C10.1, C16.1, C21.2, C29.1, C30.2, C31.2, IC.24, IC.30, IMU.P$1, IMU.P$8, IMU.P$13, IMU.P$22, L6.1, LDO_VREG.VOUT, R2.1, R5.2, R8.2, R9.2, RGBLED.1, U$5.P$3, U$10.P$2
3.3V1: BARO1.1, BARO1.2, C19.1, C24.1, C25.1, C26.2, C28.1, C38.2, C39.2, IC1.24, IC1.30, IMU1.P$1, IMU1.P$8, IMU1.P$13, IMU1.P$22, L2.1, LDO_VREG1.VOUT, R11.1, R13.2, R14.2, R16.2, RGBLED1.1, U$1.P$3, U$2.P$2
3.3V2: BARO2.1, BARO2.2, C48.1, C51.1, C52.1, C53.2, C55.1, C61.2, C62.2, IC2.24, IC2.30, IMU2.P$1, IMU2.P$8, IMU2.P$13, IMU2.P$22, L4.1, LDO_VREG2.VOUT, R20.1, R22.2, R23.2, R25.2, RGBLED2.1, U$4.P$3, U$6.P$2
3.3V3: BARO3.1, BARO3.2, C71.1, C74.1, C75.1, C76.2, C78.1, C84.2, C85.2, IC3.24, IC3.30, IMU3.P$1, IMU3.P$8, IMU3.P$13, IMU3.P$22, L7.1, LDO_VREG3.VOUT, R29.1, R31.2, R32.2, R34.2, RGBLED3.1, U$8.P$3, U$11.P$2
3.3V4: BARO4.1, BARO4.2, C94.1, C97.1, C98.1, C99.2, C101.1, C107.2, C108.2, IC4.24, IC4.30, IMU4.P$1, IMU4.P$8, IMU4.P$13, IMU4.P$22, L9.1, LDO_VREG4.VOUT, R38.1, R40.2, R41.2, R43.2, RGBLED4.1, U$13.P$3, U$14.P$2
3.3V5: BARO5.1, BARO5.2, C117.1, C120.1, C121.1, C122.2, C124.1, C130.2, C131.2, IC5.24, IC5.30, IMU5.P$1, IMU5.P$8, IMU5.P$13, IMU5.P$22, L11.1, LDO_VREG5.VOUT, R47.1, R49.2, R50.2, R52.2, RGBLED5.1, U$16.P$3, U$17.P$2
3.3V6: BARO6.1, BARO6.2, C140.1, C143.1, C144.1, C145.2, C147.1, C153.2, C154.2, IC6.24, IC6.30, IMU6.P$1, IMU6.P$8, IMU6.P$13, IMU6.P$22, L13.1, LDO_VREG6.VOUT, R56.1, R58.2, R59.2, R61.2, RGBLED6.1, U$19.P$3, U$20.P$2
3.3V7: BARO7.1, BARO7.2, C163.1, C166.1, C167.1, C168.2, C170.1, C176.2, C177.2, IC7.24, IC7.30, IMU7.P$1, IMU7.P$8, IMU7.P$13, IMU7.P$22, L15.1, LDO_VREG7.VOUT, R65.1, R67.2, R68.2, R70.2, RGBLED7.1, U$22.P$3, U$23.P$2
ANT_OUT: BALUN.1, C2.1
ANT_OUT1: BALUN1.1, C41.1
ANT_OUT2: BALUN2.1, C64.1
ANT_OUT3: BALUN3.1, C87.1
ANT_OUT4: BALUN4.1, C110.1
ANT_OUT5: BALUN5.1, C133.1
ANT_OUT6: BALUN6.1, C156.1
ANT_OUT7: BALUN7.1, C179.1
ANT_SMD: C12.2, C17.1, L1.1
ANT_SMD1: C45.2, C46.1, L3.1
ANT_SMD2: C68.2, C69.1, L5.1
ANT_SMD3: C91.2, C92.1, L8.1
ANT_SMD4: C114.2, C115.1, L10.1
ANT_SMD5: C137.2, C138.1, L12.1
ANT_SMD6: C160.2, C161.1, L14.1
ANT_SMD7: C183.2, C184.1, L16.1
ANT_UFL: C11.2, UFLANT.3
ANT_UFL1: C44.2, UFLANT1.3
ANT_UFL2: C67.2, UFLANT2.3
ANT_UFL3: C90.2, UFLANT3.3
ANT_UFL4: C113.2, UFLANT4.3
ANT_UFL5: C136.2, UFLANT5.3
ANT_UFL6: C159.2, UFLANT6.3
ANT_UFL7: C182.2, UFLANT7.3
AVDD: C_ARR.3, IC.5
AVDD1: C_ARR1.3, IC1.5
AVDD2: C_ARR2.3, IC2.5
AVDD3: C_ARR3.3, IC3.5
AVDD4: C_ARR4.3, IC4.5
AVDD5: C_ARR5.3, IC5.5
AVDD6: C_ARR6.3, IC6.5
AVDD7: C_ARR7.3, IC7.5
DVDD: C_ARR.5, IC.21
DVDD1: C_ARR1.5, IC1.21
DVDD2: C_ARR2.5, IC2.21
DVDD3: C_ARR3.5, IC3.21
DVDD4: C_ARR4.5, IC4.21
DVDD5: C_ARR5.5, IC5.21
DVDD6: C_ARR6.5, IC6.21
DVDD7: C_ARR7.5, IC7.21
GND: ASWITCH.PIN2, BALUN.2, BALUN.5, BALUN.6, BARO.3, BARO.4, BARO.5, BTN_RESET.2, C1.2, C3.1, C4.2, C5.2, C6.2, C7.2, C8.2, C9.2, C10.2, C13.2, C14.1, C15.2, C16.2, C17.2, C21.1, C22.1, C29.2, C30.1, C31.1, C32.2, C_ARR.2, C_ARR.4, C_ARR.6, C_ARR.8, FB1.2, FB3.1, FB3.2, IC.3, IC.6, IC.11, IC.14, IC.28, IC.33, IMU.P$20, LDO_VREG.GND, SJ1.1, SMDANT.3, U$5.P$2, U$10.P$1, UFLANT.1, UFLANT.2, USB.5, XTAL_BOARD.2, XTAL_BOARD.4, XTAL_RF.2, XTAL_RF.4
GND1: ASWITCH1.PIN2, BALUN1.2, BALUN1.5, BALUN1.6, BARO1.3, BARO1.4, BARO1.5, BTN_RESET1.2, C18.2, C19.2, C20.2, C23.2, C24.2, C25.2, C26.1, C27.1, C28.2, C33.1, C34.2, C35.2, C36.1, C37.2, C38.1, C39.1, C40.2, C42.2, C43.2, C46.2, C_ARR1.2, C_ARR1.4, C_ARR1.6, C_ARR1.8, FB4.2, FB6.1, FB6.2, IC1.3, IC1.6, IC1.11, IC1.14, IC1.28, IC1.33, IMU1.P$20, LDO_VREG1.GND, SJ2.1, SMDANT1.3, U$1.P$2, U$2.P$1, UFLANT1.1, UFLANT1.2, USB1.5, XTAL_BOARD1.2, XTAL_BOARD1.4, XTAL_RF1.2, XTAL_RF1.4
GND2: ASWITCH2.PIN2, BALUN2.2, BALUN2.5, BALUN2.6, BARO2.3, BARO2.4, BARO2.5, BTN_RESET2.2, C47.2, C48.2, C49.2, C50.2, C51.2, C52.2, C53.1, C54.1, C55.2, C56.1, C57.2, C58.2, C59.1, C60.2, C61.1, C62.1, C63.2, C65.2, C66.2, C69.2, C_ARR2.2, C_ARR2.4, C_ARR2.6, C_ARR2.8, FB7.2, FB9.1, FB9.2, IC2.3, IC2.6, IC2.11, IC2.14, IC2.28, IC2.33, IMU2.P$20, LDO_VREG2.GND, SJ3.1, SMDANT2.3, U$4.P$2, U$6.P$1, UFLANT2.1, UFLANT2.2, USB2.5, XTAL_BOARD2.2, XTAL_BOARD2.4, XTAL_RF2.2, XTAL_RF2.4
GND3: ASWITCH3.PIN2, BALUN3.2, BALUN3.5, BALUN3.6, BARO3.3, BARO3.4, BARO3.5, BTN_RESET3.2, C70.2, C71.2, C72.2, C73.2, C74.2, C75.2, C76.1, C77.1, C78.2, C79.1, C80.2, C81.2, C82.1, C83.2, C84.1, C85.1, C86.2, C88.2, C89.2, C92.2, C_ARR3.2, C_ARR3.4, C_ARR3.6, C_ARR3.8, FB10.2, FB12.1, FB12.2, IC3.3, IC3.6, IC3.11, IC3.14, IC3.28, IC3.33, IMU3.P$20, LDO_VREG3.GND, SJ4.1, SMDANT3.3, U$8.P$2, U$11.P$1, UFLANT3.1, UFLANT3.2, USB3.5, XTAL_BOARD3.2, XTAL_BOARD3.4, XTAL_RF3.2, XTAL_RF3.4
GND4: ASWITCH4.PIN2, BALUN4.2, BALUN4.5, BALUN4.6, BARO4.3, BARO4.4, BARO4.5, BTN_RESET4.2, C93.2, C94.2, C95.2, C96.2, C97.2, C98.2, C99.1, C100.1, C101.2, C102.1, C103.2, C104.2, C105.1, C106.2, C107.1, C108.1, C109.2, C111.2, C112.2, C115.2, C_ARR4.2, C_ARR4.4, C_ARR4.6, C_ARR4.8, FB13.2, FB15.1, FB15.2, IC4.3, IC4.6, IC4.11, IC4.14, IC4.28, IC4.33, IMU4.P$20, LDO_VREG4.GND, SJ5.1, SMDANT4.3, U$13.P$2, U$14.P$1, UFLANT4.1, UFLANT4.2, USB4.5, XTAL_BOARD4.2, XTAL_BOARD4.4, XTAL_RF4.2, XTAL_RF4.4
GND5: ASWITCH5.PIN2, BALUN5.2, BALUN5.5, BALUN5.6, BARO5.3, BARO5.4, BARO5.5, BTN_RESET5.2, C116.2, C117.2, C118.2, C119.2, C120.2, C121.2, C122.1, C123.1, C124.2, C125.1, C126.2, C127.2, C128.1, C129.2, C130.1, C131.1, C132.2, C134.2, C135.2, C138.2, C_ARR5.2, C_ARR5.4, C_ARR5.6, C_ARR5.8, FB16.2, FB18.1, FB18.2, IC5.3, IC5.6, IC5.11, IC5.14, IC5.28, IC5.33, IMU5.P$20, LDO_VREG5.GND, SJ6.1, SMDANT5.3, U$16.P$2, U$17.P$1, UFLANT5.1, UFLANT5.2, USB5.5, XTAL_BOARD5.2, XTAL_BOARD5.4, XTAL_RF5.2, XTAL_RF5.4
GND6: ASWITCH6.PIN2, BALUN6.2, BALUN6.5, BALUN6.6, BARO6.3, BARO6.4, BARO6.5, BTN_RESET6.2, C139.2, C140.2, C141.2, C142.2, C143.2, C144.2, C145.1, C146.1, C147.2, C148.1, C149.2, C150.2, C151.1, C152.2, C153.1, C154.1, C155.2, C157.2, C158.2, C161.2, C_ARR6.2, C_ARR6.4, C_ARR6.6, C_ARR6.8, FB19.2, FB21.1, FB21.2, IC6.3, IC6.6, IC6.11, IC6.14, IC6.28, IC6.33, IMU6.P$20, LDO_VREG6.GND, SJ7.1, SMDANT6.3, U$19.P$2, U$20.P$1, UFLANT6.1, UFLANT6.2, USB6.5, XTAL_BOARD6.2, XTAL_BOARD6.4, XTAL_RF6.2, XTAL_RF6.4
GND7: ASWITCH7.PIN2, BALUN7.2, BALUN7.5, BALUN7.6, BARO7.3, BARO7.4, BARO7.5, BTN_RESET7.2, C162.2, C163.2, C164.2, C165.2, C166.2, C167.2, C168.1, C169.1, C170.2, C171.1, C172.2, C173.2, C174.1, C175.2, C176.1, C177.1, C178.2, C180.2, C181.2, C184.2, C_ARR7.2, C_ARR7.4, C_ARR7.6, C_ARR7.8, FB22.2, FB24.1, FB24.2, IC7.3, IC7.6, IC7.11, IC7.14, IC7.28, IC7.33, IMU7.P$20, LDO_VREG7.GND, SJ8.1, SMDANT7.3, U$22.P$2, U$23.P$1, UFLANT7.1, UFLANT7.2, USB7.5, XTAL_BOARD7.2, XTAL_BOARD7.4, XTAL_RF7.2, XTAL_RF7.4
unnamed: L1.2, SMDANT.1
unnamed: C13.1, SMDANT.2
unnamed: ASWITCH.PIN5, C2.2
unnamed: C32.1, IMU.P$10
unnamed: FB1.1, USB.6, USB.7, USB.8, USB.9, USB.10, USB.11
unnamed: R3.1, R5.1, USB.4
unnamed: FB2.1, USB.1
unnamed: R6.2, RGBLED.3
unnamed: R7.2, RGBLED.4
unnamed: ASWITCH.PIN3, C11.1
unnamed: ASWITCH.PIN1, C12.1
unnamed: BTN_RESET1.1, R10.1
unnamed: R4.2, RGBLED.2
unnamed: R12.2, RGBLED1.2
unnamed: C35.1, SMDANT1.2
unnamed: C40.1, IMU1.P$10
unnamed: FB4.1, USB1.6, USB1.7, USB1.8, USB1.9, USB1.10, USB1.11
unnamed: R15.1, R16.1, USB1.4
unnamed: R17.2, RGBLED1.3
unnamed: R18.2, RGBLED1.4
unnamed: FB5.1, USB1.1
unnamed: ASWITCH1.PIN3, C44.1
unnamed: ASWITCH1.PIN1, C45.1
unnamed: ASWITCH1.PIN5, C41.2
unnamed: L3.2, SMDANT1.1
unnamed: BTN_RESET.1, R1.1
unnamed: BTN_RESET2.1, R19.1
unnamed: R21.2, RGBLED2.2
unnamed: C58.1, SMDANT2.2
unnamed: C63.1, IMU2.P$10
unnamed: FB7.1, USB2.6, USB2.7, USB2.8, USB2.9, USB2.10, USB2.11
unnamed: R24.1, R25.1, USB2.4
unnamed: R26.2, RGBLED2.3
unnamed: R27.2, RGBLED2.4
unnamed: FB8.1, USB2.1
unnamed: ASWITCH2.PIN3, C67.1
unnamed: ASWITCH2.PIN1, C68.1
unnamed: ASWITCH2.PIN5, C64.2
unnamed: L5.2, SMDANT2.1
unnamed: BTN_RESET3.1, R28.1
unnamed: R30.2, RGBLED3.2
unnamed: C81.1, SMDANT3.2
unnamed: C86.1, IMU3.P$10
unnamed: FB10.1, USB3.6, USB3.7, USB3.8, USB3.9, USB3.10, USB3.11
unnamed: R33.1, R34.1, USB3.4
unnamed: R35.2, RGBLED3.3
unnamed: R36.2, RGBLED3.4
unnamed: FB11.1, USB3.1
unnamed: ASWITCH3.PIN3, C90.1
unnamed: ASWITCH3.PIN1, C91.1
unnamed: ASWITCH3.PIN5, C87.2
unnamed: L8.2, SMDANT3.1
unnamed: BTN_RESET4.1, R37.1
unnamed: R39.2, RGBLED4.2
unnamed: C104.1, SMDANT4.2
unnamed: C109.1, IMU4.P$10
unnamed: FB13.1, USB4.6, USB4.7, USB4.8, USB4.9, USB4.10, USB4.11
unnamed: R42.1, R43.1, USB4.4
unnamed: R44.2, RGBLED4.3
unnamed: R45.2, RGBLED4.4
unnamed: FB14.1, USB4.1
unnamed: ASWITCH4.PIN3, C113.1
unnamed: ASWITCH4.PIN1, C114.1
unnamed: ASWITCH4.PIN5, C110.2
unnamed: L10.2, SMDANT4.1
unnamed: BTN_RESET5.1, R46.1
unnamed: R48.2, RGBLED5.2
unnamed: C127.1, SMDANT5.2
unnamed: C132.1, IMU5.P$10
unnamed: FB16.1, USB5.6, USB5.7, USB5.8, USB5.9, USB5.10, USB5.11
unnamed: R51.1, R52.1, USB5.4
unnamed: R53.2, RGBLED5.3
unnamed: R54.2, RGBLED5.4
unnamed: FB17.1, USB5.1
unnamed: ASWITCH5.PIN3, C136.1
unnamed: ASWITCH5.PIN1, C137.1
unnamed: ASWITCH5.PIN5, C133.2
unnamed: L12.2, SMDANT5.1
unnamed: BTN_RESET6.1, R55.1
unnamed: R57.2, RGBLED6.2
unnamed: C150.1, SMDANT6.2
unnamed: C155.1, IMU6.P$10
unnamed: FB19.1, USB6.6, USB6.7, USB6.8, USB6.9, USB6.10, USB6.11
unnamed: R60.1, R61.1, USB6.4
unnamed: R62.2, RGBLED6.3
unnamed: R63.2, RGBLED6.4
unnamed: FB20.1, USB6.1
unnamed: ASWITCH6.PIN3, C159.1
unnamed: ASWITCH6.PIN1, C160.1
unnamed: ASWITCH6.PIN5, C156.2
unnamed: L14.2, SMDANT6.1
unnamed: BTN_RESET7.1, R64.1
unnamed: R66.2, RGBLED7.2
unnamed: C173.1, SMDANT7.2
unnamed: C178.1, IMU7.P$10
unnamed: FB22.1, USB7.6, USB7.7, USB7.8, USB7.9, USB7.10, USB7.11
unnamed: R69.1, R70.1, USB7.4
unnamed: R71.2, RGBLED7.3
unnamed: R72.2, RGBLED7.4
unnamed: FB23.1, USB7.1
unnamed: ASWITCH7.PIN3, C182.1
unnamed: ASWITCH7.PIN1, C183.1
unnamed: ASWITCH7.PIN5, C179.2
unnamed: L16.2, SMDANT7.1
PA1: IC1.27, R15.2
PA2: IC2.27, R24.2
PA3: IC3.27, R33.2
PA4: IC4.27, R42.2
PA5: IC5.27, R51.2
PA6: IC6.27, R60.2
PA06(R): IC.7, R4.1
PA06(R)1: IC1.7, R12.1
PA06(R)2: IC2.7, R21.1
PA06(R)3: IC3.7, R30.1
PA06(R)4: IC4.7, R39.1
PA06(R)5: IC5.7, R48.1
PA06(R)6: IC6.7, R57.1
PA06(R)7: IC7.7, R66.1
PA7: IC7.27, R69.2
PA07(G): IC.8, R6.1
PA07(G)1: IC1.8, R17.1
PA07(G)2: IC2.8, R26.1
PA07(G)3: IC3.8, R35.1
PA07(G)4: IC4.8, R44.1
PA07(G)5: IC5.8, R53.1
PA07(G)6: IC6.8, R62.1
PA07(G)7: IC7.8, R71.1
PA08/I2C: ASWITCH.PIN6, C9.1, IC.9, U$9.P$2
PA08/I2C1: ASWITCH1.PIN6, C43.1, IC1.9, U$3.P$2
PA08/I2C2: ASWITCH2.PIN6, C66.1, IC2.9, U$7.P$2
PA08/I2C3: ASWITCH3.PIN6, C89.1, IC3.9, U$12.P$2
PA08/I2C4: ASWITCH4.PIN6, C112.1, IC4.9, U$15.P$2
PA08/I2C5: ASWITCH5.PIN6, C135.1, IC5.9, U$18.P$2
PA08/I2C6: ASWITCH6.PIN6, C158.1, IC6.9, U$21.P$2
PA08/I2C7: ASWITCH7.PIN6, C181.1, IC7.9, U$24.P$2
PA09/I2C: ASWITCH.PIN4, C8.1, IC.10, U$9.P$1
PA09/I2C1: ASWITCH1.PIN4, C42.1, IC1.10, U$3.P$1
PA09/I2C2: ASWITCH2.PIN4, C65.1, IC2.10, U$7.P$1
PA09/I2C3: ASWITCH3.PIN4, C88.1, IC3.10, U$12.P$1
PA09/I2C4: ASWITCH4.PIN4, C111.1, IC4.10, U$15.P$1
PA09/I2C5: ASWITCH5.PIN4, C134.1, IC5.10, U$18.P$1
PA09/I2C6: ASWITCH6.PIN4, C157.1, IC6.10, U$21.P$1
PA09/I2C7: ASWITCH7.PIN4, C180.1, IC7.10, U$24.P$1
PA14/XIN_MC: C3.2, IC.15, XTAL_BOARD.1
PA14/XIN_MC1: C33.2, IC1.15, XTAL_BOARD1.1
PA14/XIN_MC2: C56.2, IC2.15, XTAL_BOARD2.1
PA14/XIN_MC3: C79.2, IC3.15, XTAL_BOARD3.1
PA14/XIN_MC4: C102.2, IC4.15, XTAL_BOARD4.1
PA14/XIN_MC5: C125.2, IC5.15, XTAL_BOARD5.1
PA14/XIN_MC6: C148.2, IC6.15, XTAL_BOARD6.1
PA14/XIN_MC7: C171.2, IC7.15, XTAL_BOARD7.1
PA15/XOUT_MC: C4.1, IC.16, U$5.P$8, XTAL_BOARD.3
PA15/XOUT_MC1: C34.1, IC1.16, U$1.P$8, XTAL_BOARD1.3
PA15/XOUT_MC2: C57.1, IC2.16, U$4.P$8, XTAL_BOARD2.3
PA15/XOUT_MC3: C80.1, IC3.16, U$8.P$8, XTAL_BOARD3.3
PA15/XOUT_MC4: C103.1, IC4.16, U$13.P$8, XTAL_BOARD4.3
PA15/XOUT_MC5: C126.1, IC5.16, U$16.P$8, XTAL_BOARD5.3
PA15/XOUT_MC6: C149.1, IC6.16, U$19.P$8, XTAL_BOARD6.3
PA15/XOUT_MC7: C172.1, IC7.16, U$22.P$8, XTAL_BOARD7.3
PA16/I2C: BARO.7, IC.17, IMU.P$24, R8.1, U$5.P$7
PA16/I2C1: BARO1.7, IC1.17, IMU1.P$24, R13.1, U$1.P$7
PA16/I2C2: BARO2.7, IC2.17, IMU2.P$24, R22.1, U$4.P$7
PA16/I2C3: BARO3.7, IC3.17, IMU3.P$24, R31.1, U$8.P$7
PA16/I2C4: BARO4.7, IC4.17, IMU4.P$24, R40.1, U$13.P$7
PA16/I2C5: BARO5.7, IC5.17, IMU5.P$24, R49.1, U$16.P$7
PA16/I2C6: BARO6.7, IC6.17, IMU6.P$24, R58.1, U$19.P$7
PA16/I2C7: BARO7.7, IC7.17, IMU7.P$24, R67.1, U$22.P$7
PA17/I2C: BARO.8, IC.18, IMU.P$23, R9.1, U$5.P$6
PA17/I2C1: BARO1.8, IC1.18, IMU1.P$23, R14.1, U$1.P$6
PA17/I2C2: BARO2.8, IC2.18, IMU2.P$23, R23.1, U$4.P$6
PA17/I2C3: BARO3.8, IC3.18, IMU3.P$23, R32.1, U$8.P$6
PA17/I2C4: BARO4.8, IC4.18, IMU4.P$23, R41.1, U$13.P$6
PA17/I2C5: BARO5.8, IC5.18, IMU5.P$23, R50.1, U$16.P$6
PA17/I2C6: BARO6.8, IC6.18, IMU6.P$23, R59.1, U$19.P$6
PA17/I2C7: BARO7.8, IC7.18, IMU7.P$23, R68.1, U$22.P$6
PA18/FSYNC: IC.19, IMU.P$11, SJ1.2, U$5.P$5
PA18/FSYNC1: IC1.19, IMU1.P$11, SJ2.2, U$1.P$5
PA18/FSYNC2: IC2.19, IMU2.P$11, SJ3.2, U$4.P$5
PA18/FSYNC3: IC3.19, IMU3.P$11, SJ4.2, U$8.P$5
PA18/FSYNC4: IC4.19, IMU4.P$11, SJ5.2, U$13.P$5
PA18/FSYNC5: IC5.19, IMU5.P$11, SJ6.2, U$16.P$5
PA18/FSYNC6: IC6.19, IMU6.P$11, SJ7.2, U$19.P$5
PA18/FSYNC7: IC7.19, IMU7.P$11, SJ8.2, U$22.P$5
PA19/INT: IC.20, IMU.P$12, U$5.P$4
PA19/INT1: IC1.20, IMU1.P$12, U$1.P$4
PA19/INT2: IC2.20, IMU2.P$12, U$4.P$4
PA19/INT3: IC3.20, IMU3.P$12, U$8.P$4
PA19/INT4: IC4.20, IMU4.P$12, U$13.P$4
PA19/INT5: IC5.20, IMU5.P$12, U$16.P$4
PA19/INT6: IC6.20, IMU6.P$12, U$19.P$4
PA19/INT7: IC7.20, IMU7.P$12, U$22.P$4
PA24/USBDM: IC.22, USB.2
PA24/USBDM1: IC1.22, USB1.2
PA24/USBDM2: IC2.22, USB2.2
PA24/USBDM3: IC3.22, USB3.2
PA24/USBDM4: IC4.22, USB4.2
PA24/USBDM5: IC5.22, USB5.2
PA24/USBDM6: IC6.22, USB6.2
PA24/USBDM7: IC7.22, USB7.2
PA25/USBDP: IC.23, USB.3
PA25/USBDP1: IC1.23, USB1.3
PA25/USBDP2: IC2.23, USB2.3
PA25/USBDP3: IC3.23, USB3.3
PA25/USBDP4: IC4.23, USB4.3
PA25/USBDP5: IC5.23, USB5.3
PA25/USBDP6: IC6.23, USB6.3
PA25/USBDP7: IC7.23, USB7.3
PA27(B): IC.25, R7.1
PA27(B)1: IC1.25, R18.1
PA27(B)2: IC2.25, R27.1
PA27(B)3: IC3.25, R36.1
PA27(B)4: IC4.25, R45.1
PA27(B)5: IC5.25, R54.1
PA27(B)6: IC6.25, R63.1
PA27(B)7: IC7.25, R72.1
PA28: IC.27, R3.2
PA30/SWCLK: IC.31, U$10.P$4
PA30/SWCLK1: IC1.31, U$2.P$4
PA30/SWCLK2: IC2.31, U$6.P$4
PA30/SWCLK3: IC3.31, U$11.P$4
PA30/SWCLK4: IC4.31, U$14.P$4
PA30/SWCLK5: IC5.31, U$17.P$4
PA30/SWCLK6: IC6.31, U$20.P$4
PA30/SWCLK7: IC7.31, U$23.P$4
PA31/SWDIO: IC.32, U$10.P$5
PA31/SWDIO1: IC1.32, U$2.P$5
PA31/SWDIO2: IC2.32, U$6.P$5
PA31/SWDIO3: IC3.32, U$11.P$5
PA31/SWDIO4: IC4.32, U$14.P$5
PA31/SWDIO5: IC5.32, U$17.P$5
PA31/SWDIO6: IC6.32, U$20.P$5
PA31/SWDIO7: IC7.32, U$23.P$5
RESET: C1.1, IC.26, R1.2, R2.2, U$10.P$3
RESET1: C18.1, IC1.26, R10.2, R11.2, U$2.P$3
RESET2: C47.1, IC2.26, R19.2, R20.2, U$6.P$3
RESET3: C70.1, IC3.26, R28.2, R29.2, U$11.P$3
RESET4: C93.1, IC4.26, R37.2, R38.2, U$14.P$3
RESET5: C116.1, IC5.26, R46.2, R47.2, U$17.P$3
RESET6: C139.1, IC6.26, R55.2, R56.2, U$20.P$3
RESET7: C162.1, IC7.26, R64.2, R65.2, U$23.P$3
RFN: BALUN.3, IC.13
RFN1: BALUN1.3, IC1.13
RFN2: BALUN2.3, IC2.13
RFN3: BALUN3.3, IC3.13
RFN4: BALUN4.3, IC4.13
RFN5: BALUN5.3, IC5.13
RFN6: BALUN6.3, IC6.13
RFN7: BALUN7.3, IC7.13
RFP: BALUN.4, IC.12
RFP1: BALUN1.4, IC1.12
RFP2: BALUN2.4, IC2.12
RFP3: BALUN3.4, IC3.12
RFP4: BALUN4.4, IC4.12
RFP5: BALUN5.4, IC5.12
RFP6: BALUN6.4, IC6.12
RFP7: BALUN7.4, IC7.12
VDDANA: C22.2, C_ARR.1, IC.4, L6.2
VDDANA1: C27.2, C_ARR1.1, IC1.4, L2.2
VDDANA2: C54.2, C_ARR2.1, IC2.4, L4.2
VDDANA3: C77.2, C_ARR3.1, IC3.4, L7.2
VDDANA4: C100.2, C_ARR4.1, IC4.4, L9.2
VDDANA5: C123.2, C_ARR5.1, IC5.4, L11.2
VDDANA6: C146.2, C_ARR6.1, IC6.4, L13.2
VDDANA7: C169.2, C_ARR7.1, IC7.4, L15.2
VDDCORE: C_ARR.7, IC.29
VDDCORE1: C_ARR1.7, IC1.29
VDDCORE2: C_ARR2.7, IC2.29
VDDCORE3: C_ARR3.7, IC3.29
VDDCORE4: C_ARR4.7, IC4.29
VDDCORE5: C_ARR5.7, IC5.29
VDDCORE6: C_ARR6.7, IC6.29
VDDCORE7: C_ARR7.7, IC7.29
VIN: C6.1, C7.1, FB2.2, LDO_VREG.VIN, U$5.P$1
VIN1: C20.1, C23.1, FB5.2, LDO_VREG1.VIN, U$1.P$1
VIN2: C49.1, C50.1, FB8.2, LDO_VREG2.VIN, U$4.P$1
VIN3: C72.1, C73.1, FB11.2, LDO_VREG3.VIN, U$8.P$1
VIN4: C95.1, C96.1, FB14.2, LDO_VREG4.VIN, U$13.P$1
VIN5: C118.1, C119.1, FB17.2, LDO_VREG5.VIN, U$16.P$1
VIN6: C141.1, C142.1, FB20.2, LDO_VREG6.VIN, U$19.P$1
VIN7: C164.1, C165.1, FB23.2, LDO_VREG7.VIN, U$22.P$1
XTALIN: C14.2, IC.2, XTAL_RF.1
XTALIN1: C36.2, IC1.2, XTAL_RF1.1
XTALIN2: C59.2, IC2.2, XTAL_RF2.1
XTALIN3: C82.2, IC3.2, XTAL_RF3.1
XTALIN4: C105.2, IC4.2, XTAL_RF4.1
XTALIN5: C128.2, IC5.2, XTAL_RF5.1
XTALIN6: C151.2, IC6.2, XTAL_RF6.1
XTALIN7: C174.2, IC7.2, XTAL_RF7.1
XTALOUT: C15.1, IC.1, XTAL_RF.3
XTALOUT1: C37.1, IC1.1, XTAL_RF1.3
XTALOUT2: C60.1, IC2.1, XTAL_RF2.3
XTALOUT3: C83.1, IC3.1, XTAL_RF3.3
XTALOUT4: C106.1, IC4.1, XTAL_RF4.3
XTALOUT5: C129.1, IC5.1, XTAL_RF5.3
XTALOUT6: C152.1, IC6.1, XTAL_RF6.3
XTALOUT7: C175.1, IC7.1, XTAL_RF7.3
