femtoduino/femto-beacon/Eagle_Files/FemtoBeacon_r2.0.0/femtoBeacon_r2.0.1_PANELIZED_5x10.brd

## EAGLE design Eagle_Files/FemtoBeacon_r2.0.0/femtoBeacon_r2.0.1_PANELIZED_5x10.brd (2018-01-04)

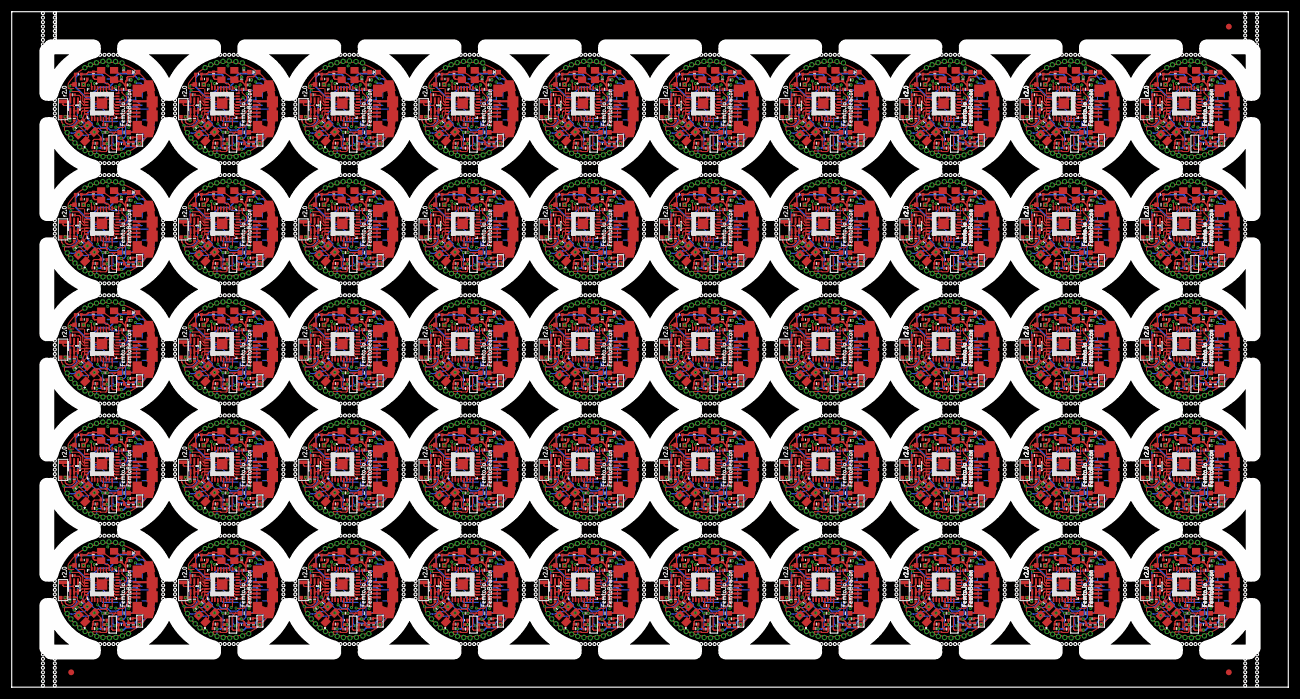
[picture p66: board femtoBeacon_r2.0.1_PANELIZED_5x10.brd from above]

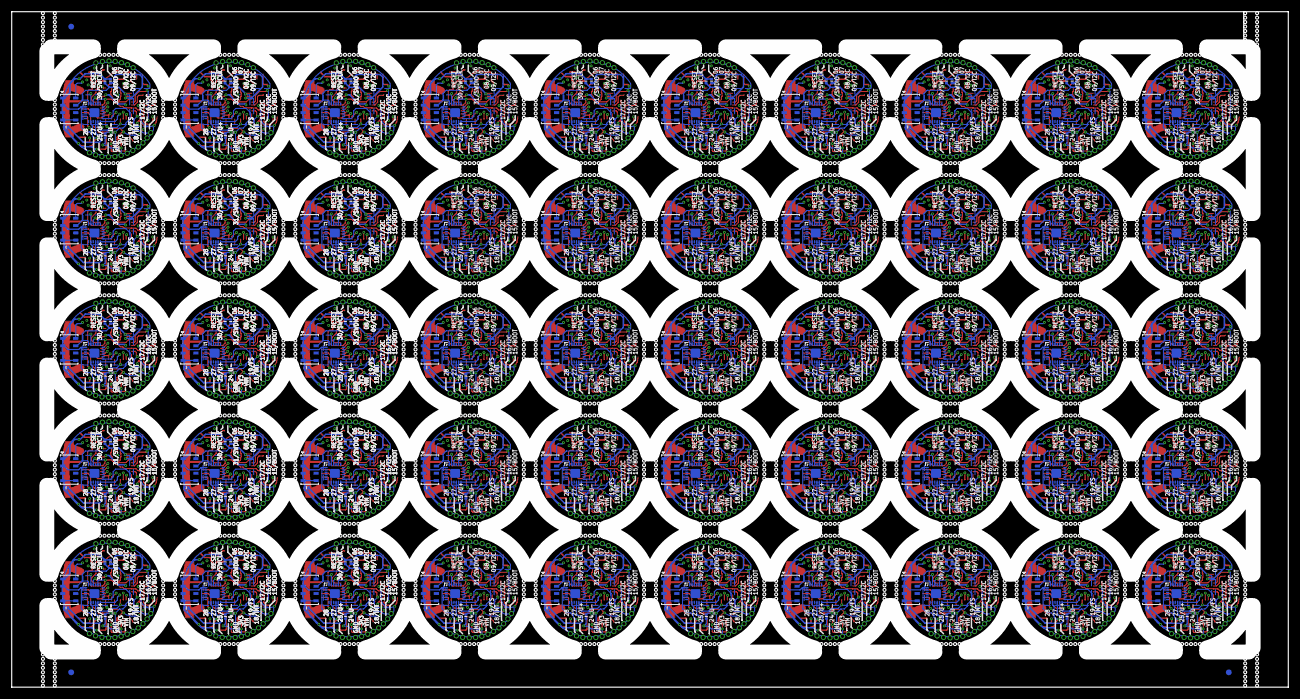
[picture p67: board femtoBeacon_r2.0.1_PANELIZED_5x10.brd from below]

Board: 4 copper layers, 218.1 x 115.4 mm, 3006 parts (353 on the bottom side), 1260 nets.

Parts:
ANT, ANT1, ANT2, ANT3, ANT4, ANT5, ANT6, ANT7, ANT8, ANT9, ANT10, ANT11, ANT12, ANT13, ANT14, ANT15, ANT16, ANT17, ANT18, ANT19, ANT20, ANT21, ANT22, ANT23, ANT24, ANT25, ANT26, ANT27, ANT28, ANT29, ANT30, ANT31, ANT32, ANT33, ANT34, ANT35, ANT36, ANT37, ANT38, ANT39, ANT40, ANT41, ANT42, ANT43, ANT44, ANT45, ANT46, ANT47, ANT48, ANT49: PULSE_ANT_2.4GHZ; ANT_BAR
BAL, BAL1, BAL2, BAL3, BAL4, BAL5, BAL6, BAL7, BAL8, BAL9, BAL10, BAL11, BAL12, BAL13, BAL14, BAL15, BAL16, BAL17, BAL18, BAL19, BAL20, BAL21, BAL22, BAL23, BAL24, BAL25, BAL26, BAL27, BAL28, BAL29, BAL30, BAL31, BAL32, BAL33, BAL34, BAL35, BAL36, BAL37, BAL38, BAL39, BAL40, BAL41, BAL42, BAL43, BAL44, BAL45, BAL46, BAL47, BAL48, BAL49: JOHANSON_2450BM15A0015E; 0805_BALUN
BARO, BARO1, BARO2, BARO3, BARO4, BARO5, BARO6, BARO7, BARO8, BARO9, BARO10, BARO11, BARO12, BARO13, BARO14, BARO15, BARO16, BARO17, BARO18, BARO19, BARO20, BARO21, BARO22, BARO23, BARO24, BARO25, BARO26, BARO27, BARO28, BARO29, BARO30, BARO31, BARO32, BARO33, BARO34, BARO35, BARO36, BARO37, BARO38, BARO39, BARO40, BARO41, BARO42, BARO43, BARO44, BARO45, BARO46, BARO47, BARO48, BARO49: MS5611-01BA03
BTN, BTN1, BTN2, BTN3, BTN4, BTN5, BTN6, BTN7, BTN8, BTN9, BTN10, BTN11, BTN12, BTN13, BTN14, BTN15, BTN16, BTN17, BTN18, BTN19, BTN20, BTN21, BTN22, BTN23, BTN24, BTN25, BTN26, BTN27, BTN28, BTN29, BTN30, BTN31, BTN32, BTN33, BTN34, BTN35, BTN36, BTN37, BTN38, BTN39, BTN40, BTN41, BTN42, BTN43, BTN44, BTN45, BTN46, BTN47, BTN48, BTN49: DNP; SPST_SMD
C1, C2, C8, C9, C10, C16, C17, C18, C19, C25, C26, C27, C28, C29, C30, C32, C33, C36, C45, C46, C47, C48, C52, C53, C54, C55, C56, C59, C68, C69, C70, C71, C75, C76, C77, C78, C79, C82, C91, C92, C93, C94, C98, C99, C100, C101, C102, C105, C114, C115, C116, C117, C121, C122, C123, C124, C125, C128, C137, C138, C139, C140, C144, C145, C146, C147, C148, C151, C160, C161, C162, C163, C167, C168, C169, C170, C171, C174, C183, C184, C185, C186, C190, C191, C192, C193, C194, C197, C206, C207, C208, C209, C213, C214, C215, C216, C217, C220, C229, C230, C231, C232, C236, C237, C238, C239, C240, C243, C252, C253, C254, C255, C259, C260, C261, C262, C263, C266, C275, C276, C277, C278, C282, C283, C284, C285, C286, C289, C298, C299, C300, C301, C305, C306, C307, C308, C309, C312, C321, C322, C323, C324, C328, C329, C330, C331, C332, C335, C344, C345, C346, C347, C351, C352, C353, C354, C355, C358, C367, C368, C369, C370, C374, C375, C376, C377, C378, C381, C390, C391, C392, C393, C397, C398, C399, C400, C401, C404, C413, C414, C415, C416, C420, C421, C422, C423, C424, C427, C436, C437, C438, C439, C443, C444, C445, C446, C447, C450, C459, C460, C461, C462, C466, C467, C468, C469, C470, C473, C482, C483, C484, C485, C489, C490, C491, C492, C493, C496, C505, C506, C507, C508, C512, C513, C514, C515, C516, C519, C528, C529, C530, C531, C535, C536, C537, C538, C539, C542, C551, C552, C553, C554, C558, C559, C560, C561, C562, C565, C574, C575, C576, C577, C581, C582, C583, C584, C585, C588, C597, C598, C599, C600, C604, C605, C606, C607, C608, C611, C620, C621, C622, C623, C627, C628, C629, C630, C631, C634, C643, C644, C645, C646, C650, C651, C652, C653, C654, C657, C666, C667, C668, C669, C673, C674, C675, C676, C677, C680, C689, C690, C691, C692, C696, C697, C698, C699, C700, C703, C712, C713, C714, C715, C719, C720, C721, C722, C723, C726, C735, C736, C737, C738, C742, C743, C744, C745, C746, C749, C758, C759, C760, C761, C765, C766, C767, C768, C769, C772, C781, C782, C783, C784, C788, C789, C790, C791, C792, C795, C804, C805, C806, C807, C811, C812, C813, C814, C815, C818, C827, C828, C829, C830, C834, C835, C836, C837, C838, C841, C850, C851, C852, C853, C857, C858, C859, C860, C861, C864, C873, C874, C875, C876, C880, C881, C882, C883, C884, C887, C896, C897, C898, C899, C903, C904, C905, C906, C907, C910, C919, C920, C921, C922, C926, C927, C928, C929, C930, C933, C942, C943, C944, C945, C949, C950, C951, C952, C953, C956, C965, C966, C967, C968, C972, C973, C974, C975, C976, C979, C988, C989, C990, C991, C995, C996, C997, C998, C999, C1002, C1011, C1012, C1013, C1014, C1018, C1019, C1020, C1021, C1022, C1025, C1034, C1035, C1036, C1037, C1041, C1042, C1043, C1044, C1045, C1048, C1057, C1058, C1059, C1060, C1064, C1065, C1066, C1067, C1068, C1071, C1080, C1081, C1082, C1083, C1087, C1088, C1089, C1090, C1091, C1094, C1103, C1104, C1105, C1106, C1110, C1111, C1112, C1113, C1114, C1117, C1126, C1127, C1128, C1129, C1133, C1134, C1135, C1136, C1137, C1140, C1149, C1150: 0.1uF; PART
C3, C4, C37, C38, C60, C61, C83, C84, C106, C107, C129, C130, C152, C153, C175, C176, C198, C199, C221, C222, C244, C245, C267, C268, C290, C291, C313, C314, C336, C337, C359, C360, C382, C383, C405, C406, C428, C429, C451, C452, C474, C475, C497, C498, C520, C521, C543, C544, C566, C567, C589, C590, C612, C613, C635, C636, C658, C659, C681, C682, C704, C705, C727, C728, C750, C751, C773, C774, C796, C797, C819, C820, C842, C843, C865, C866, C888, C889, C911, C912, C934, C935, C957, C958, C980, C981, C1003, C1004, C1026, C1027, C1049, C1050, C1072, C1073, C1095, C1096, C1118, C1119, C1141, C1142: 10pF; PART
C5, C6, C20, C23, C49, C50, C72, C73, C95, C96, C118, C119, C141, C142, C164, C165, C187, C188, C210, C211, C233, C234, C256, C257, C279, C280, C302, C303, C325, C326, C348, C349, C371, C372, C394, C395, C417, C418, C440, C441, C463, C464, C486, C487, C509, C510, C532, C533, C555, C556, C578, C579, C601, C602, C624, C625, C647, C648, C670, C671, C693, C694, C716, C717, C739, C740, C762, C763, C785, C786, C808, C809, C831, C832, C854, C855, C877, C878, C900, C901, C923, C924, C946, C947, C969, C970, C992, C993, C1015, C1016, C1038, C1039, C1061, C1062, C1084, C1085, C1107, C1108, C1130, C1131: 2.2uF; _0402MP
C7, C24, C51, C74, C97, C120, C143, C166, C189, C212, C235, C258, C281, C304, C327, C350, C373, C396, C419, C442, C465, C488, C511, C534, C557, C580, C603, C626, C649, C672, C695, C718, C741, C764, C787, C810, C833, C856, C879, C902, C925, C948, C971, C994, C1017, C1040, C1063, C1086, C1109, C1132: 0.47uF; PART
C11, C12, C39, C40, C62, C63, C85, C86, C108, C109, C131, C132, C154, C155, C177, C178, C200, C201, C223, C224, C246, C247, C269, C270, C292, C293, C315, C316, C338, C339, C361, C362, C384, C385, C407, C408, C430, C431, C453, C454, C476, C477, C499, C500, C522, C523, C545, C546, C568, C569, C591, C592, C614, C615, C637, C638, C660, C661, C683, C684, C706, C707, C729, C730, C752, C753, C775, C776, C798, C799, C821, C822, C844, C845, C867, C868, C890, C891, C913, C914, C936, C937, C959, C960, C982, C983, C1005, C1006, C1028, C1029, C1051, C1052, C1074, C1075, C1097, C1098, C1120, C1121, C1143, C1144: 22pF, C0G, 5%; PART
C13, C41, C64, C87, C110, C133, C156, C179, C202, C225, C248, C271, C294, C317, C340, C363, C386, C409, C432, C455, C478, C501, C524, C547, C570, C593, C616, C639, C662, C685, C708, C731, C754, C777, C800, C823, C846, C869, C892, C915, C938, C961, C984, C1007, C1030, C1053, C1076, C1099, C1122, C1145: DNP; PART
C14, C15, C42, C43, C65, C66, C88, C89, C111, C112, C134, C135, C157, C158, C180, C181, C203, C204, C226, C227, C249, C250, C272, C273, C295, C296, C318, C319, C341, C342, C364, C365, C387, C388, C410, C411, C433, C434, C456, C457, C479, C480, C502, C503, C525, C526, C548, C549, C571, C572, C594, C595, C617, C618, C640, C641, C663, C664, C686, C687, C709, C710, C732, C733, C755, C756, C778, C779, C801, C802, C824, C825, C847, C848, C870, C871, C893, C894, C916, C917, C939, C940, C962, C963, C985, C986, C1008, C1009, C1031, C1032, C1054, C1055, C1077, C1078, C1100, C1101, C1123, C1124, C1146, C1147: 9pF; PART
C21, C22, C34, C35, C57, C58, C80, C81, C103, C104, C126, C127, C149, C150, C172, C173, C195, C196, C218, C219, C241, C242, C264, C265, C287, C288, C310, C311, C333, C334, C356, C357, C379, C380, C402, C403, C425, C426, C448, C449, C471, C472, C494, C495, C517, C518, C540, C541, C563, C564, C586, C587, C609, C610, C632, C633, C655, C656, C678, C679, C701, C702, C724, C725, C747, C748, C770, C771, C793, C794, C816, C817, C839, C840, C862, C863, C885, C886, C908, C909, C931, C932, C954, C955, C977, C978, C1000, C1001, C1023, C1024, C1046, C1047, C1069, C1070, C1092, C1093, C1115, C1116, C1138, C1139: 10uF; _0402MP
C31, C44, C67, C90, C113, C136, C159, C182, C205, C228, C251, C274, C297, C320, C343, C366, C389, C412, C435, C458, C481, C504, C527, C550, C573, C596, C619, C642, C665, C688, C711, C734, C757, C780, C803, C826, C849, C872, C895, C918, C941, C964, C987, C1010, C1033, C1056, C1079, C1102, C1125, C1148: 10nF; PART
FB1, FB2, FB3, FB4, FB5, FB6, FB7, FB8, FB9, FB10, FB11, FB12, FB13, FB14, FB15, FB16, FB17, FB18, FB19, FB20, FB21, FB22, FB23, FB24, FB25, FB26, FB27, FB28, FB29, FB30, FB31, FB32, FB33, FB34, FB35, FB36, FB37, FB38, FB39, FB40, FB41, FB42, FB43, FB44, FB45, FB46, FB47, FB48, FB49, FB50: _0603MP
FID1, FID2, FID3, FID4, FID5, FID6: FIDUCIAL_1MM
IC, IC1, IC2, IC3, IC4, IC5, IC6, IC7, IC8, IC9, IC10, IC11, IC12, IC13, IC14, IC15, IC16, IC17, IC18, IC19, IC20, IC21, IC22, IC23, IC24, IC25, IC26, IC27, IC28, IC29, IC30, IC31, IC32, IC33, IC34, IC35, IC36, IC37, IC38, IC39, IC40, IC41, IC42, IC43, IC44, IC45, IC46, IC47, IC48, IC49: ATSAMR21E18A-MUT; QFN32
IMU, IMU1, IMU2, IMU3, IMU4, IMU5, IMU6, IMU7, IMU8, IMU9, IMU10, IMU11, IMU12, IMU13, IMU14, IMU15, IMU16, IMU17, IMU18, IMU19, IMU20, IMU21, IMU22, IMU23, IMU24, IMU25, IMU26, IMU27, IMU28, IMU29, IMU30, IMU31, IMU32, IMU33, IMU34, IMU35, IMU36, IMU37, IMU38, IMU39, IMU40, IMU41, IMU42, IMU43, IMU44, IMU45, IMU46, IMU47, IMU48, IMU49: MPU-9250; QFN_3X3MM
L1, L2, L3, L4, L5, L6, L7, L8, L9, L10, L11, L12, L13, L14, L15, L16, L17, L18, L19, L20, L21, L22, L23, L24, L25, L26, L27, L28, L29, L30, L31, L32, L33, L34, L35, L36, L37, L38, L39, L40, L41, L42, L43, L44, L45, L46, L47, L48, L49, L50: 10uH; _0603MP
LDO_VREG, LDO_VREG1, LDO_VREG2, LDO_VREG3, LDO_VREG4, LDO_VREG5, LDO_VREG6, LDO_VREG7, LDO_VREG8, LDO_VREG9, LDO_VREG10, LDO_VREG11, LDO_VREG12, LDO_VREG13, LDO_VREG14, LDO_VREG15, LDO_VREG16, LDO_VREG17, LDO_VREG18, LDO_VREG19, LDO_VREG20, LDO_VREG21, LDO_VREG22, LDO_VREG23, LDO_VREG24, LDO_VREG25, LDO_VREG26, LDO_VREG27, LDO_VREG28, LDO_VREG29, LDO_VREG30, LDO_VREG31, LDO_VREG32, LDO_VREG33, LDO_VREG34, LDO_VREG35, LDO_VREG36, LDO_VREG37, LDO_VREG38, LDO_VREG39, LDO_VREG40, LDO_VREG41, LDO_VREG42, LDO_VREG43, LDO_VREG44, LDO_VREG45, LDO_VREG46, LDO_VREG47, LDO_VREG48, LDO_VREG49: MCP1700T-3302E/TT
LED, LED1, LED2, LED3, LED4, LED5, LED6, LED7, LED8, LED9, LED10, LED11, LED12, LED13, LED14, LED15, LED16, LED17, LED18, LED19, LED20, LED21, LED22, LED23, LED24, LED25, LED26, LED27, LED28, LED29, LED30, LED31, LED32, LED33, LED34, LED35, LED36, LED37, LED38, LED39, LED40, LED41, LED42, LED43, LED44, LED45, LED46, LED47, LED48, LED49: BLUE; CHIPLED_0603_NOOUTLINE
R1, R3, R4, R6, R11, R13, R16, R18, R21, R23, R26, R28, R31, R33, R36, R38, R41, R43, R46, R48, R51, R53, R56, R58, R61, R63, R66, R68, R71, R73, R76, R78, R81, R83, R86, R88, R91, R93, R96, R98, R101, R103, R106, R108, R111, R113, R116, R118, R121, R123, R126, R128, R131, R133, R136, R138, R141, R143, R146, R148, R151, R153, R156, R158, R161, R163, R166, R168, R171, R173, R176, R178, R181, R183, R186, R188, R191, R193, R196, R198, R201, R203, R206, R208, R211, R213, R216, R218, R221, R223, R226, R228, R231, R233, R236, R238, R241, R243, R246, R248: 330; PART
R2, R5, R12, R17, R22, R27, R32, R37, R42, R47, R52, R57, R62, R67, R72, R77, R82, R87, R92, R97, R102, R107, R112, R117, R122, R127, R132, R137, R142, R147, R152, R157, R162, R167, R172, R177, R182, R187, R192, R197, R202, R207, R212, R217, R222, R227, R232, R237, R242, R247: 10K; PART
R7, R8, R9, R10, R14, R15, R19, R20, R24, R25, R29, R30, R34, R35, R39, R40, R44, R45, R49, R50, R54, R55, R59, R60, R64, R65, R69, R70, R74, R75, R79, R80, R84, R85, R89, R90, R94, R95, R99, R100, R104, R105, R109, R110, R114, R115, R119, R120, R124, R125, R129, R130, R134, R135, R139, R140, R144, R145, R149, R150, R154, R155, R159, R160, R164, R165, R169, R170, R174, R175, R179, R180, R184, R185, R189, R190, R194, R195, R199, R200, R204, R205, R209, R210, R214, R215, R219, R220, R224, R225, R229, R230, R234, R235, R239, R240, R244, R245, R249, R250: 2.2K; PART
U$1, U$2, U$3, U$4, U$5, U$6, U$7, U$8, U$9, U$10, U$11, U$12, U$13, U$14, U$15, U$16, U$17, U$18, U$19, U$20, U$21, U$22, U$23, U$24, U$25, U$26, U$27, U$28, U$29, U$30, U$31, U$32, U$33, U$34, U$35, U$36, U$37, U$38, U$39, U$40, U$41, U$42, U$43, U$44, U$45, U$46, U$47, U$48, U$49, U$50, U$51, U$52, U$53, U$54, U$55, U$56, U$57, U$58, U$59, U$60, U$61, U$62, U$63, U$64, U$65, U$66, U$67, U$68, U$69, U$70, U$71, U$72, U$73, U$74, U$75, U$76, U$77, U$78, U$79, U$80, U$81, U$82, U$83, U$84, U$85, U$86, U$87, U$88, U$89, U$90, U$91, U$92, U$93, U$94, U$95, U$96, U$97, U$98, U$99, U$100, U$101, U$102, U$103, U$104, U$105, U$106, U$107, U$108, U$109, U$110, U$111, U$112, U$113, U$114, U$115, U$116, U$117, U$118, U$119, U$120, U$121, U$122, U$123, U$124, U$125, U$126, U$127, U$128, U$129, U$130, U$131, U$132, U$133, U$134, U$135, U$136, U$137, U$138, U$139, U$140, U$141, U$142, U$143, U$144, U$145, U$146, U$147, U$148, U$149, U$150, U$151, U$152, U$153, U$154, U$155, U$156, U$157, U$158, U$159, U$160, U$161, U$162, U$163, U$164, U$165, U$166, U$167, U$168, U$169, U$170, U$171, U$172, U$173, U$174, U$175, U$176, U$177, U$178, U$179, U$180, U$181, U$182, U$183, U$184, U$185, U$186, U$187, U$188, U$189, U$190, U$191, U$192, U$193, U$194, U$195, U$196, U$197, U$198, U$199, U$200, U$201, U$202, U$203, U$204, U$205, U$206, U$207, U$208, U$209, U$210, U$211, U$212, U$213, U$214, U$215, U$216, U$217, U$218, U$219, U$220, U$221, U$222, U$223, U$224, U$225, U$226, U$227, U$228, U$229, U$230, U$231, U$232, U$233, U$234, U$235, U$236, U$237, U$238, U$239, U$240, U$241, U$242, U$243, U$244, U$245, U$246, U$247, U$248, U$249, U$250, U$251, U$252, U$253, U$254, U$255, U$256, U$257, U$258, U$259, U$260, U$261, U$262, U$263, U$264, U$265, U$266, U$267, U$268, U$269, U$270, U$271, U$272, U$273, U$274, U$275, U$276, U$277, U$278, U$279, U$280, U$281, U$282, U$283, U$284, U$285, U$286, U$287, U$288, U$289, U$290, U$291, U$292, U$293, U$294, U$295, U$296, U$297, U$298, U$299, U$300, U$301, U$302, U$303, U$304, U$305, U$306, U$307, U$308, U$309, U$310, U$311, U$312, U$313, U$314, U$315, U$316, U$317, U$318, U$319, U$320, U$321, U$322, U$323, U$324, U$325, U$326, U$327, U$328, U$329, U$330, U$331, U$332, U$333, U$334, U$335, U$336, U$337, U$338, U$339, U$340, U$341, U$342, U$343, U$344, U$345, U$346, U$347, U$348, U$349, U$350, U$351, U$352, U$353, U$354, U$355, U$356, U$357, U$358, U$359, U$360, U$361, U$362, U$363, U$364, U$365, U$366, U$367, U$368, U$369, U$370, U$371, U$372, U$373, U$374, U$375, U$376, U$377, U$378, U$379, U$380, U$381, U$382, U$383, U$384, U$385, U$386, U$387, U$388, U$389, U$390, U$391, U$392, U$393, U$394, U$395, U$396, U$397, U$398, U$399, U$400, U$401, U$402, U$403, U$404, U$405, U$406, U$407, U$408, U$409, U$410, U$411, U$412, U$413, U$414, U$415, U$416, U$417, U$418, U$419, U$420, U$421, U$422, U$423, U$424, U$425, U$426, U$427, U$428, U$429, U$430, U$431, U$432, U$433, U$434, U$435, U$436, U$437, U$438, U$439, U$440, U$441, U$442, U$443, U$444, U$445, U$446, U$447, U$448, U$449, U$450, U$451, U$452, U$453, U$454, U$455, U$456, U$457, U$458, U$459, U$460, U$461, U$462, U$463, U$464, U$465, U$466, U$467, U$468, U$469, U$470, U$471, U$472, U$473, U$474, U$475, U$476, U$477, U$478, U$479, U$480, U$481, U$482, U$483, U$484, U$485, U$486, U$487, U$488, U$489, U$490, U$491, U$492, U$493, U$494, U$495, U$496, U$497, U$498, U$499, U$500, U$501, U$502, U$503, U$504, U$505, U$506, U$507, U$508, U$509, U$510, U$511, U$512, U$513, U$514, U$515, U$516, U$517, U$518, U$519, U$520, U$521, U$522, U$523, U$524, U$525, U$526, U$527, U$528, U$529, U$530, U$531, U$532, U$533, U$534, U$535, U$536, U$537, U$538, U$539, U$540, U$541, U$542, U$543, U$544, U$545, U$546, U$547, U$548, U$549, U$550, U$551, U$552, U$553, U$554, U$555, U$556, U$557, U$558, U$559, U$560, U$561, U$562, U$563, U$564, U$565, U$566, U$567, U$568, U$569, U$570, U$571, U$572, U$573, U$574, U$575, U$576, U$577, U$578, U$579, U$580, U$581, U$582, U$583, U$584, U$585, U$586, U$587, U$588, U$589, U$590, U$591, U$592, U$593, U$594, U$595, U$596, U$597, U$598, U$599, U$600, U$601, U$602, U$603, U$604, U$605, U$606, U$607, U$608, U$609, U$610, U$611, U$612, U$613, U$614, U$615, U$616, U$617, U$618, U$619, U$620, U$621, U$622, U$623, U$624, U$625, U$626, U$627, U$628, U$629, U$630, U$631, U$632, U$633, U$634, U$635, U$636, U$637, U$638, U$639, U$640, U$641, U$642, U$643, U$644, U$645, U$646, U$647, U$648, U$649, U$650, U$651, U$652, U$653, U$654, U$655, U$656, U$657, U$658, U$659, U$660, U$661, U$662, U$663, U$664, U$665, U$666, U$667, U$668, U$669, U$670, U$671, U$672, U$673, U$674, U$675, U$676, U$677, U$678, U$679, U$680, U$681, U$682, U$683, U$684, U$685, U$686, U$687, U$688, U$689, U$690, U$691, U$692, U$693, U$694, U$695, U$696, U$697, U$698, U$699, U$700, U$701, U$702, U$703, U$704, U$705, U$706, U$707, U$708, U$709, U$710, U$711, U$712, U$713, U$714, U$715, U$716, U$717, U$718, U$719, U$720, U$721, U$722, U$723, U$724, U$725, U$726, U$727, U$728, U$729, U$730, U$731, U$732, U$733, U$734, U$735, U$736, U$737, U$738, U$739, U$740, U$741, U$742, U$743, U$744, U$745, U$746, U$747, U$748, U$749, U$750, U$751, U$752, U$753, U$754, U$755, U$756, U$757, U$758, U$759, U$760, U$761, U$762, U$763, U$764, U$765, U$766, U$767, U$768, U$769, U$770, U$771, U$772, U$773, U$774, U$775, U$776, U$777, U$778, U$779, U$780, U$781, U$782, U$783, U$784, U$785, U$786, U$787, U$788, U$789, U$790, U$791, U$792, U$793, U$794, U$795, U$796, U$797, U$798, U$799, U$800, U$801, U$802, U$803, U$804, U$805, U$806, U$807, U$808, U$809, U$810, U$811, U$812, U$813, U$814, U$815, U$816, U$817, U$818, U$819, U$820, U$821, U$822, U$823, U$824, U$825, U$826, U$827, U$828, U$829, U$830, U$831, U$832, U$833, U$834, U$835, U$836, U$837, U$838, U$839, U$840, U$841, U$842, U$843, U$844, U$845, U$846, U$847, U$848, U$849, U$850, U$851, U$852, U$853, U$854, U$855, U$856, U$857, U$858, U$859, U$860, U$861, U$862, U$863, U$864, U$865, U$866, U$867, U$868, U$869, U$870, U$871, U$872, U$873, U$874, U$875, U$876, U$877, U$878, U$879, U$880, U$881, U$882, U$883, U$884, U$885, U$886, U$887, U$888, U$889, U$890, U$891, U$892, U$893, U$894, U$895, U$896, U$897, U$898, U$899, U$900, U$901, U$902, U$903, U$904, U$905, U$906, U$907, U$908, U$909, U$910, U$911, U$912, U$913, U$914, U$915, U$916, U$917, U$918, U$919, U$920, U$921, U$922, U$923, U$924, U$925, U$926, U$927, U$928, U$929, U$930, U$931, U$932, U$933, U$934, U$935, U$936, U$937, U$938, U$939, U$940, U$941, U$942, U$943, U$944, U$945, U$946, U$947, U$948, U$949, U$950: 1X1_ROUND
USB, USB1, USB2, USB3, USB4, USB5, USB6, USB7, USB8, USB9, USB10, USB11, USB12, USB13, USB14, USB15, USB16, USB17, USB18, USB19, USB20, USB21, USB22, USB23, USB24, USB25, USB26, USB27, USB28, USB29, USB30, USB31, USB32, USB33, USB34, USB35, USB36, USB37, USB38, USB39, USB40, USB41, USB42, USB43, USB44, USB45, USB46, USB47, USB48, USB49: USB_MICROB; USB_MICROB_PACKAGE
XOSC, XOSC1, XOSC2, XOSC3, XOSC4, XOSC5, XOSC6, XOSC7, XOSC8, XOSC9, XOSC10, XOSC11, XOSC12, XOSC13, XOSC14, XOSC15, XOSC16, XOSC17, XOSC18, XOSC19, XOSC20, XOSC21, XOSC22, XOSC23, XOSC24, XOSC25, XOSC26, XOSC27, XOSC28, XOSC29, XOSC30, XOSC31, XOSC32, XOSC33, XOSC34, XOSC35, XOSC36, XOSC37, XOSC38, XOSC39, XOSC40, XOSC41, XOSC42, XOSC43, XOSC44, XOSC45, XOSC46, XOSC47, XOSC48, XOSC49: 12MHz; TSX-3225
XOSCRF, XOSCRF1, XOSCRF2, XOSCRF3, XOSCRF4, XOSCRF5, XOSCRF6, XOSCRF7, XOSCRF8, XOSCRF9, XOSCRF10, XOSCRF11, XOSCRF12, XOSCRF13, XOSCRF14, XOSCRF15, XOSCRF16, XOSCRF17, XOSCRF18, XOSCRF19, XOSCRF20, XOSCRF21, XOSCRF22, XOSCRF23, XOSCRF24, XOSCRF25, XOSCRF26, XOSCRF27, XOSCRF28, XOSCRF29, XOSCRF30, XOSCRF31, XOSCRF32, XOSCRF33, XOSCRF34, XOSCRF35, XOSCRF36, XOSCRF37, XOSCRF38, XOSCRF39, XOSCRF40, XOSCRF41, XOSCRF42, XOSCRF43, XOSCRF44, XOSCRF45, XOSCRF46, XOSCRF47, XOSCRF48, XOSCRF49: 16MHz; TSX-3225

Connections:
3.3V: BARO.1, BARO.2, C5.1, C10.1, C16.1, C21.2, C29.1, C30.2, C31.2, IC.24, IC.30, IMU.P$1, IMU.P$8, IMU.P$13, IMU.P$22, L6.1, LDO_VREG.VOUT, R2.2, R8.2, R9.2, U$5.P$1
3.3V1: BARO1.1, BARO1.2, C20.1, C25.1, C28.1, C34.2, C36.1, C44.2, C45.2, IC1.24, IC1.30, IMU1.P$1, IMU1.P$8, IMU1.P$13, IMU1.P$22, L1.1, LDO_VREG1.VOUT, R5.2, R7.2, R10.2, U$6.P$1
3.3V2: BARO2.1, BARO2.2, C49.1, C52.1, C55.1, C57.2, C59.1, C67.2, C68.2, IC2.24, IC2.30, IMU2.P$1, IMU2.P$8, IMU2.P$13, IMU2.P$22, L2.1, LDO_VREG2.VOUT, R12.2, R14.2, R15.2, U$28.P$1
3.3V3: BARO3.1, BARO3.2, C72.1, C75.1, C78.1, C80.2, C82.1, C90.2, C91.2, IC3.24, IC3.30, IMU3.P$1, IMU3.P$8, IMU3.P$13, IMU3.P$22, L3.1, LDO_VREG3.VOUT, R17.2, R19.2, R20.2, U$60.P$1
3.3V4: BARO4.1, BARO4.2, C95.1, C98.1, C101.1, C103.2, C105.1, C113.2, C114.2, IC4.24, IC4.30, IMU4.P$1, IMU4.P$8, IMU4.P$13, IMU4.P$22, L4.1, LDO_VREG4.VOUT, R22.2, R24.2, R25.2, U$79.P$1
3.3V5: BARO5.1, BARO5.2, C118.1, C121.1, C124.1, C126.2, C128.1, C136.2, C137.2, IC5.24, IC5.30, IMU5.P$1, IMU5.P$8, IMU5.P$13, IMU5.P$22, L5.1, LDO_VREG5.VOUT, R27.2, R29.2, R30.2, U$98.P$1
3.3V6: BARO6.1, BARO6.2, C141.1, C144.1, C147.1, C149.2, C151.1, C159.2, C160.2, IC6.24, IC6.30, IMU6.P$1, IMU6.P$8, IMU6.P$13, IMU6.P$22, L7.1, LDO_VREG6.VOUT, R32.2, R34.2, R35.2, U$117.P$1
3.3V7: BARO7.1, BARO7.2, C164.1, C167.1, C170.1, C172.2, C174.1, C182.2, C183.2, IC7.24, IC7.30, IMU7.P$1, IMU7.P$8, IMU7.P$13, IMU7.P$22, L8.1, LDO_VREG7.VOUT, R37.2, R39.2, R40.2, U$136.P$1
3.3V8: BARO8.1, BARO8.2, C187.1, C190.1, C193.1, C195.2, C197.1, C205.2, C206.2, IC8.24, IC8.30, IMU8.P$1, IMU8.P$8, IMU8.P$13, IMU8.P$22, L9.1, LDO_VREG8.VOUT, R42.2, R44.2, R45.2, U$155.P$1
3.3V9: BARO9.1, BARO9.2, C210.1, C213.1, C216.1, C218.2, C220.1, C228.2, C229.2, IC9.24, IC9.30, IMU9.P$1, IMU9.P$8, IMU9.P$13, IMU9.P$22, L10.1, LDO_VREG9.VOUT, R47.2, R49.2, R50.2, U$174.P$1
3.3V10: BARO10.1, BARO10.2, C233.1, C236.1, C239.1, C241.2, C243.1, C251.2, C252.2, IC10.24, IC10.30, IMU10.P$1, IMU10.P$8, IMU10.P$13, IMU10.P$22, L11.1, LDO_VREG10.VOUT, R52.2, R54.2, R55.2, U$193.P$1
3.3V11: BARO11.1, BARO11.2, C256.1, C259.1, C262.1, C264.2, C266.1, C274.2, C275.2, IC11.24, IC11.30, IMU11.P$1, IMU11.P$8, IMU11.P$13, IMU11.P$22, L12.1, LDO_VREG11.VOUT, R57.2, R59.2, R60.2, U$212.P$1
3.3V12: BARO12.1, BARO12.2, C279.1, C282.1, C285.1, C287.2, C289.1, C297.2, C298.2, IC12.24, IC12.30, IMU12.P$1, IMU12.P$8, IMU12.P$13, IMU12.P$22, L13.1, LDO_VREG12.VOUT, R62.2, R64.2, R65.2, U$231.P$1
3.3V13: BARO13.1, BARO13.2, C302.1, C305.1, C308.1, C310.2, C312.1, C320.2, C321.2, IC13.24, IC13.30, IMU13.P$1, IMU13.P$8, IMU13.P$13, IMU13.P$22, L14.1, LDO_VREG13.VOUT, R67.2, R69.2, R70.2, U$250.P$1
3.3V14: BARO14.1, BARO14.2, C325.1, C328.1, C331.1, C333.2, C335.1, C343.2, C344.2, IC14.24, IC14.30, IMU14.P$1, IMU14.P$8, IMU14.P$13, IMU14.P$22, L15.1, LDO_VREG14.VOUT, R72.2, R74.2, R75.2, U$269.P$1
3.3V15: BARO15.1, BARO15.2, C348.1, C351.1, C354.1, C356.2, C358.1, C366.2, C367.2, IC15.24, IC15.30, IMU15.P$1, IMU15.P$8, IMU15.P$13, IMU15.P$22, L16.1, LDO_VREG15.VOUT, R77.2, R79.2, R80.2, U$288.P$1
3.3V16: BARO16.1, BARO16.2, C371.1, C374.1, C377.1, C379.2, C381.1, C389.2, C390.2, IC16.24, IC16.30, IMU16.P$1, IMU16.P$8, IMU16.P$13, IMU16.P$22, L17.1, LDO_VREG16.VOUT, R82.2, R84.2, R85.2, U$307.P$1
3.3V17: BARO17.1, BARO17.2, C394.1, C397.1, C400.1, C402.2, C404.1, C412.2, C413.2, IC17.24, IC17.30, IMU17.P$1, IMU17.P$8, IMU17.P$13, IMU17.P$22, L18.1, LDO_VREG17.VOUT, R87.2, R89.2, R90.2, U$326.P$1
3.3V18: BARO18.1, BARO18.2, C417.1, C420.1, C423.1, C425.2, C427.1, C435.2, C436.2, IC18.24, IC18.30, IMU18.P$1, IMU18.P$8, IMU18.P$13, IMU18.P$22, L19.1, LDO_VREG18.VOUT, R92.2, R94.2, R95.2, U$345.P$1
3.3V19: BARO19.1, BARO19.2, C440.1, C443.1, C446.1, C448.2, C450.1, C458.2, C459.2, IC19.24, IC19.30, IMU19.P$1, IMU19.P$8, IMU19.P$13, IMU19.P$22, L20.1, LDO_VREG19.VOUT, R97.2, R99.2, R100.2, U$364.P$1
3.3V20: BARO20.1, BARO20.2, C463.1, C466.1, C469.1, C471.2, C473.1, C481.2, C482.2, IC20.24, IC20.30, IMU20.P$1, IMU20.P$8, IMU20.P$13, IMU20.P$22, L21.1, LDO_VREG20.VOUT, R102.2, R104.2, R105.2, U$383.P$1
3.3V21: BARO21.1, BARO21.2, C486.1, C489.1, C492.1, C494.2, C496.1, C504.2, C505.2, IC21.24, IC21.30, IMU21.P$1, IMU21.P$8, IMU21.P$13, IMU21.P$22, L22.1, LDO_VREG21.VOUT, R107.2, R109.2, R110.2, U$402.P$1
3.3V22: BARO22.1, BARO22.2, C509.1, C512.1, C515.1, C517.2, C519.1, C527.2, C528.2, IC22.24, IC22.30, IMU22.P$1, IMU22.P$8, IMU22.P$13, IMU22.P$22, L23.1, LDO_VREG22.VOUT, R112.2, R114.2, R115.2, U$421.P$1
3.3V23: BARO23.1, BARO23.2, C532.1, C535.1, C538.1, C540.2, C542.1, C550.2, C551.2, IC23.24, IC23.30, IMU23.P$1, IMU23.P$8, IMU23.P$13, IMU23.P$22, L24.1, LDO_VREG23.VOUT, R117.2, R119.2, R120.2, U$440.P$1
3.3V24: BARO24.1, BARO24.2, C555.1, C558.1, C561.1, C563.2, C565.1, C573.2, C574.2, IC24.24, IC24.30, IMU24.P$1, IMU24.P$8, IMU24.P$13, IMU24.P$22, L25.1, LDO_VREG24.VOUT, R122.2, R124.2, R125.2, U$459.P$1
3.3V25: BARO25.1, BARO25.2, C578.1, C581.1, C584.1, C586.2, C588.1, C596.2, C597.2, IC25.24, IC25.30, IMU25.P$1, IMU25.P$8, IMU25.P$13, IMU25.P$22, L26.1, LDO_VREG25.VOUT, R127.2, R129.2, R130.2, U$478.P$1
3.3V26: BARO26.1, BARO26.2, C601.1, C604.1, C607.1, C609.2, C611.1, C619.2, C620.2, IC26.24, IC26.30, IMU26.P$1, IMU26.P$8, IMU26.P$13, IMU26.P$22, L27.1, LDO_VREG26.VOUT, R132.2, R134.2, R135.2, U$497.P$1
3.3V27: BARO27.1, BARO27.2, C624.1, C627.1, C630.1, C632.2, C634.1, C642.2, C643.2, IC27.24, IC27.30, IMU27.P$1, IMU27.P$8, IMU27.P$13, IMU27.P$22, L28.1, LDO_VREG27.VOUT, R137.2, R139.2, R140.2, U$516.P$1
3.3V28: BARO28.1, BARO28.2, C647.1, C650.1, C653.1, C655.2, C657.1, C665.2, C666.2, IC28.24, IC28.30, IMU28.P$1, IMU28.P$8, IMU28.P$13, IMU28.P$22, L29.1, LDO_VREG28.VOUT, R142.2, R144.2, R145.2, U$535.P$1
3.3V29: BARO29.1, BARO29.2, C670.1, C673.1, C676.1, C678.2, C680.1, C688.2, C689.2, IC29.24, IC29.30, IMU29.P$1, IMU29.P$8, IMU29.P$13, IMU29.P$22, L30.1, LDO_VREG29.VOUT, R147.2, R149.2, R150.2, U$554.P$1
3.3V30: BARO30.1, BARO30.2, C693.1, C696.1, C699.1, C701.2, C703.1, C711.2, C712.2, IC30.24, IC30.30, IMU30.P$1, IMU30.P$8, IMU30.P$13, IMU30.P$22, L31.1, LDO_VREG30.VOUT, R152.2, R154.2, R155.2, U$573.P$1
3.3V31: BARO31.1, BARO31.2, C716.1, C719.1, C722.1, C724.2, C726.1, C734.2, C735.2, IC31.24, IC31.30, IMU31.P$1, IMU31.P$8, IMU31.P$13, IMU31.P$22, L32.1, LDO_VREG31.VOUT, R157.2, R159.2, R160.2, U$592.P$1
3.3V32: BARO32.1, BARO32.2, C739.1, C742.1, C745.1, C747.2, C749.1, C757.2, C758.2, IC32.24, IC32.30, IMU32.P$1, IMU32.P$8, IMU32.P$13, IMU32.P$22, L33.1, LDO_VREG32.VOUT, R162.2, R164.2, R165.2, U$611.P$1
3.3V33: BARO33.1, BARO33.2, C762.1, C765.1, C768.1, C770.2, C772.1, C780.2, C781.2, IC33.24, IC33.30, IMU33.P$1, IMU33.P$8, IMU33.P$13, IMU33.P$22, L34.1, LDO_VREG33.VOUT, R167.2, R169.2, R170.2, U$630.P$1
3.3V34: BARO34.1, BARO34.2, C785.1, C788.1, C791.1, C793.2, C795.1, C803.2, C804.2, IC34.24, IC34.30, IMU34.P$1, IMU34.P$8, IMU34.P$13, IMU34.P$22, L35.1, LDO_VREG34.VOUT, R172.2, R174.2, R175.2, U$649.P$1
ANT_OUT: ANT.1, BAL.1
ANT_OUT1: ANT1.1, BAL1.1
ANT_OUT2: ANT2.1, BAL2.1
ANT_OUT3: ANT3.1, BAL3.1
ANT_OUT4: ANT4.1, BAL4.1
ANT_OUT5: ANT5.1, BAL5.1
ANT_OUT6: ANT6.1, BAL6.1
ANT_OUT7: ANT7.1, BAL7.1
ANT_OUT8: ANT8.1, BAL8.1
ANT_OUT9: ANT9.1, BAL9.1
ANT_OUT10: ANT10.1, BAL10.1
ANT_OUT11: ANT11.1, BAL11.1
ANT_OUT12: ANT12.1, BAL12.1
ANT_OUT13: ANT13.1, BAL13.1
ANT_OUT14: ANT14.1, BAL14.1
ANT_OUT15: ANT15.1, BAL15.1
ANT_OUT16: ANT16.1, BAL16.1
ANT_OUT17: ANT17.1, BAL17.1
ANT_OUT18: ANT18.1, BAL18.1
ANT_OUT19: ANT19.1, BAL19.1
ANT_OUT20: ANT20.1, BAL20.1
ANT_OUT21: ANT21.1, BAL21.1
ANT_OUT22: ANT22.1, BAL22.1
ANT_OUT23: ANT23.1, BAL23.1
ANT_OUT24: ANT24.1, BAL24.1
ANT_OUT25: ANT25.1, BAL25.1
ANT_OUT26: ANT26.1, BAL26.1
ANT_OUT27: ANT27.1, BAL27.1
ANT_OUT28: ANT28.1, BAL28.1
ANT_OUT29: ANT29.1, BAL29.1
ANT_OUT30: ANT30.1, BAL30.1
ANT_OUT31: ANT31.1, BAL31.1
ANT_OUT32: ANT32.1, BAL32.1
ANT_OUT33: ANT33.1, BAL33.1
ANT_OUT34: ANT34.1, BAL34.1
AVDD: C17.1, IC.5
AVDD1: C33.1, IC1.5
AVDD2: C56.1, IC2.5
AVDD3: C79.1, IC3.5
AVDD4: C102.1, IC4.5
AVDD5: C125.1, IC5.5
AVDD6: C148.1, IC6.5
AVDD7: C171.1, IC7.5
AVDD8: C194.1, IC8.5
AVDD9: C217.1, IC9.5
AVDD10: C240.1, IC10.5
AVDD11: C263.1, IC11.5
AVDD12: C286.1, IC12.5
AVDD13: C309.1, IC13.5
AVDD14: C332.1, IC14.5
AVDD15: C355.1, IC15.5
AVDD16: C378.1, IC16.5
AVDD17: C401.1, IC17.5
AVDD18: C424.1, IC18.5
AVDD19: C447.1, IC19.5
AVDD20: C470.1, IC20.5
AVDD21: C493.1, IC21.5
AVDD22: C516.1, IC22.5
AVDD23: C539.1, IC23.5
AVDD24: C562.1, IC24.5
AVDD25: C585.1, IC25.5
AVDD26: C608.1, IC26.5
AVDD27: C631.1, IC27.5
AVDD28: C654.1, IC28.5
AVDD29: C677.1, IC29.5
AVDD30: C700.1, IC30.5
AVDD31: C723.1, IC31.5
AVDD32: C746.1, IC32.5
AVDD33: C769.1, IC33.5
AVDD34: C792.1, IC34.5
DVDD: C2.1, IC.21
DVDD1: C19.1, IC1.21
DVDD2: C48.1, IC2.21
DVDD3: C71.1, IC3.21
DVDD4: C94.1, IC4.21
DVDD5: C117.1, IC5.21
DVDD6: C140.1, IC6.21
DVDD7: C163.1, IC7.21
DVDD8: C186.1, IC8.21
DVDD9: C209.1, IC9.21
DVDD10: C232.1, IC10.21
DVDD11: C255.1, IC11.21
DVDD12: C278.1, IC12.21
DVDD13: C301.1, IC13.21
DVDD14: C324.1, IC14.21
DVDD15: C347.1, IC15.21
DVDD16: C370.1, IC16.21
DVDD17: C393.1, IC17.21
DVDD18: C416.1, IC18.21
DVDD19: C439.1, IC19.21
DVDD20: C462.1, IC20.21
DVDD21: C485.1, IC21.21
DVDD22: C508.1, IC22.21
DVDD23: C531.1, IC23.21
DVDD24: C554.1, IC24.21
DVDD25: C577.1, IC25.21
DVDD26: C600.1, IC26.21
DVDD27: C623.1, IC27.21
DVDD28: C646.1, IC28.21
DVDD29: C669.1, IC29.21
DVDD30: C692.1, IC30.21
DVDD31: C715.1, IC31.21
DVDD32: C738.1, IC32.21
DVDD33: C761.1, IC33.21
DVDD34: C784.1, IC34.21
GND: ANT.3, BAL.2, BAL.5, BAL.6, BARO.3, BARO.4, BARO.5, BTN.2, C1.2, C2.2, C3.1, C4.2, C5.2, C6.2, C7.2, C8.2, C9.2, C10.2, C13.2, C14.1, C15.2, C16.2, C17.2, C21.1, C22.1, C29.2, C30.1, C31.1, C32.2, FB1.2, IC.3, IC.6, IC.11, IC.14, IC.28, IC.33, IMU.P$20, LDO_VREG.GND, LED.C, U$2.P$1, XOSC.2, XOSC.4, XOSCRF.2, XOSCRF.4
GND1: ANT1.3, BAL1.2, BAL1.5, BAL1.6, BARO1.3, BARO1.4, BARO1.5, BTN1.2, C18.2, C19.2, C20.2, C23.2, C24.2, C25.2, C26.2, C27.2, C28.2, C33.2, C34.1, C35.1, C36.2, C37.1, C38.2, C41.2, C42.1, C43.2, C44.1, C45.1, C46.2, FB2.2, IC1.3, IC1.6, IC1.11, IC1.14, IC1.28, IC1.33, IMU1.P$20, LDO_VREG1.GND, LED1.C, U$4.P$1, XOSC1.2, XOSC1.4, XOSCRF1.2, XOSCRF1.4
GND2: ANT2.3, BAL2.2, BAL2.5, BAL2.6, BARO2.3, BARO2.4, BARO2.5, BTN2.2, C47.2, C48.2, C49.2, C50.2, C51.2, C52.2, C53.2, C54.2, C55.2, C56.2, C57.1, C58.1, C59.2, C60.1, C61.2, C64.2, C65.1, C66.2, C67.1, C68.1, C69.2, FB3.2, IC2.3, IC2.6, IC2.11, IC2.14, IC2.28, IC2.33, IMU2.P$20, LDO_VREG2.GND, LED2.C, U$27.P$1, XOSC2.2, XOSC2.4, XOSCRF2.2, XOSCRF2.4
GND3: ANT3.3, BAL3.2, BAL3.5, BAL3.6, BARO3.3, BARO3.4, BARO3.5, BTN3.2, C70.2, C71.2, C72.2, C73.2, C74.2, C75.2, C76.2, C77.2, C78.2, C79.2, C80.1, C81.1, C82.2, C83.1, C84.2, C87.2, C88.1, C89.2, C90.1, C91.1, C92.2, FB4.2, IC3.3, IC3.6, IC3.11, IC3.14, IC3.28, IC3.33, IMU3.P$20, LDO_VREG3.GND, LED3.C, U$59.P$1, XOSC3.2, XOSC3.4, XOSCRF3.2, XOSCRF3.4
GND4: ANT4.3, BAL4.2, BAL4.5, BAL4.6, BARO4.3, BARO4.4, BARO4.5, BTN4.2, C93.2, C94.2, C95.2, C96.2, C97.2, C98.2, C99.2, C100.2, C101.2, C102.2, C103.1, C104.1, C105.2, C106.1, C107.2, C110.2, C111.1, C112.2, C113.1, C114.1, C115.2, FB5.2, IC4.3, IC4.6, IC4.11, IC4.14, IC4.28, IC4.33, IMU4.P$20, LDO_VREG4.GND, LED4.C, U$78.P$1, XOSC4.2, XOSC4.4, XOSCRF4.2, XOSCRF4.4
GND5: ANT5.3, BAL5.2, BAL5.5, BAL5.6, BARO5.3, BARO5.4, BARO5.5, BTN5.2, C116.2, C117.2, C118.2, C119.2, C120.2, C121.2, C122.2, C123.2, C124.2, C125.2, C126.1, C127.1, C128.2, C129.1, C130.2, C133.2, C134.1, C135.2, C136.1, C137.1, C138.2, FB6.2, IC5.3, IC5.6, IC5.11, IC5.14, IC5.28, IC5.33, IMU5.P$20, LDO_VREG5.GND, LED5.C, U$97.P$1, XOSC5.2, XOSC5.4, XOSCRF5.2, XOSCRF5.4
GND6: ANT6.3, BAL6.2, BAL6.5, BAL6.6, BARO6.3, BARO6.4, BARO6.5, BTN6.2, C139.2, C140.2, C141.2, C142.2, C143.2, C144.2, C145.2, C146.2, C147.2, C148.2, C149.1, C150.1, C151.2, C152.1, C153.2, C156.2, C157.1, C158.2, C159.1, C160.1, C161.2, FB7.2, IC6.3, IC6.6, IC6.11, IC6.14, IC6.28, IC6.33, IMU6.P$20, LDO_VREG6.GND, LED6.C, U$116.P$1, XOSC6.2, XOSC6.4, XOSCRF6.2, XOSCRF6.4
GND7: ANT7.3, BAL7.2, BAL7.5, BAL7.6, BARO7.3, BARO7.4, BARO7.5, BTN7.2, C162.2, C163.2, C164.2, C165.2, C166.2, C167.2, C168.2, C169.2, C170.2, C171.2, C172.1, C173.1, C174.2, C175.1, C176.2, C179.2, C180.1, C181.2, C182.1, C183.1, C184.2, FB8.2, IC7.3, IC7.6, IC7.11, IC7.14, IC7.28, IC7.33, IMU7.P$20, LDO_VREG7.GND, LED7.C, U$135.P$1, XOSC7.2, XOSC7.4, XOSCRF7.2, XOSCRF7.4
GND8: ANT8.3, BAL8.2, BAL8.5, BAL8.6, BARO8.3, BARO8.4, BARO8.5, BTN8.2, C185.2, C186.2, C187.2, C188.2, C189.2, C190.2, C191.2, C192.2, C193.2, C194.2, C195.1, C196.1, C197.2, C198.1, C199.2, C202.2, C203.1, C204.2, C205.1, C206.1, C207.2, FB9.2, IC8.3, IC8.6, IC8.11, IC8.14, IC8.28, IC8.33, IMU8.P$20, LDO_VREG8.GND, LED8.C, U$154.P$1, XOSC8.2, XOSC8.4, XOSCRF8.2, XOSCRF8.4
GND9: ANT9.3, BAL9.2, BAL9.5, BAL9.6, BARO9.3, BARO9.4, BARO9.5, BTN9.2, C208.2, C209.2, C210.2, C211.2, C212.2, C213.2, C214.2, C215.2, C216.2, C217.2, C218.1, C219.1, C220.2, C221.1, C222.2, C225.2, C226.1, C227.2, C228.1, C229.1, C230.2, FB10.2, IC9.3, IC9.6, IC9.11, IC9.14, IC9.28, IC9.33, IMU9.P$20, LDO_VREG9.GND, LED9.C, U$173.P$1, XOSC9.2, XOSC9.4, XOSCRF9.2, XOSCRF9.4
GND10: ANT10.3, BAL10.2, BAL10.5, BAL10.6, BARO10.3, BARO10.4, BARO10.5, BTN10.2, C231.2, C232.2, C233.2, C234.2, C235.2, C236.2, C237.2, C238.2, C239.2, C240.2, C241.1, C242.1, C243.2, C244.1, C245.2, C248.2, C249.1, C250.2, C251.1, C252.1, C253.2, FB11.2, IC10.3, IC10.6, IC10.11, IC10.14, IC10.28, IC10.33, IMU10.P$20, LDO_VREG10.GND, LED10.C, U$192.P$1, XOSC10.2, XOSC10.4, XOSCRF10.2, XOSCRF10.4
GND11: ANT11.3, BAL11.2, BAL11.5, BAL11.6, BARO11.3, BARO11.4, BARO11.5, BTN11.2, C254.2, C255.2, C256.2, C257.2, C258.2, C259.2, C260.2, C261.2, C262.2, C263.2, C264.1, C265.1, C266.2, C267.1, C268.2, C271.2, C272.1, C273.2, C274.1, C275.1, C276.2, FB12.2, IC11.3, IC11.6, IC11.11, IC11.14, IC11.28, IC11.33, IMU11.P$20, LDO_VREG11.GND, LED11.C, U$211.P$1, XOSC11.2, XOSC11.4, XOSCRF11.2, XOSCRF11.4
GND12: ANT12.3, BAL12.2, BAL12.5, BAL12.6, BARO12.3, BARO12.4, BARO12.5, BTN12.2, C277.2, C278.2, C279.2, C280.2, C281.2, C282.2, C283.2, C284.2, C285.2, C286.2, C287.1, C288.1, C289.2, C290.1, C291.2, C294.2, C295.1, C296.2, C297.1, C298.1, C299.2, FB13.2, IC12.3, IC12.6, IC12.11, IC12.14, IC12.28, IC12.33, IMU12.P$20, LDO_VREG12.GND, LED12.C, U$230.P$1, XOSC12.2, XOSC12.4, XOSCRF12.2, XOSCRF12.4
GND13: ANT13.3, BAL13.2, BAL13.5, BAL13.6, BARO13.3, BARO13.4, BARO13.5, BTN13.2, C300.2, C301.2, C302.2, C303.2, C304.2, C305.2, C306.2, C307.2, C308.2, C309.2, C310.1, C311.1, C312.2, C313.1, C314.2, C317.2, C318.1, C319.2, C320.1, C321.1, C322.2, FB14.2, IC13.3, IC13.6, IC13.11, IC13.14, IC13.28, IC13.33, IMU13.P$20, LDO_VREG13.GND, LED13.C, U$249.P$1, XOSC13.2, XOSC13.4, XOSCRF13.2, XOSCRF13.4
GND14: ANT14.3, BAL14.2, BAL14.5, BAL14.6, BARO14.3, BARO14.4, BARO14.5, BTN14.2, C323.2, C324.2, C325.2, C326.2, C327.2, C328.2, C329.2, C330.2, C331.2, C332.2, C333.1, C334.1, C335.2, C336.1, C337.2, C340.2, C341.1, C342.2, C343.1, C344.1, C345.2, FB15.2, IC14.3, IC14.6, IC14.11, IC14.14, IC14.28, IC14.33, IMU14.P$20, LDO_VREG14.GND, LED14.C, U$268.P$1, XOSC14.2, XOSC14.4, XOSCRF14.2, XOSCRF14.4
GND15: ANT15.3, BAL15.2, BAL15.5, BAL15.6, BARO15.3, BARO15.4, BARO15.5, BTN15.2, C346.2, C347.2, C348.2, C349.2, C350.2, C351.2, C352.2, C353.2, C354.2, C355.2, C356.1, C357.1, C358.2, C359.1, C360.2, C363.2, C364.1, C365.2, C366.1, C367.1, C368.2, FB16.2, IC15.3, IC15.6, IC15.11, IC15.14, IC15.28, IC15.33, IMU15.P$20, LDO_VREG15.GND, LED15.C, U$287.P$1, XOSC15.2, XOSC15.4, XOSCRF15.2, XOSCRF15.4
GND16: ANT16.3, BAL16.2, BAL16.5, BAL16.6, BARO16.3, BARO16.4, BARO16.5, BTN16.2, C369.2, C370.2, C371.2, C372.2, C373.2, C374.2, C375.2, C376.2, C377.2, C378.2, C379.1, C380.1, C381.2, C382.1, C383.2, C386.2, C387.1, C388.2, C389.1, C390.1, C391.2, FB17.2, IC16.3, IC16.6, IC16.11, IC16.14, IC16.28, IC16.33, IMU16.P$20, LDO_VREG16.GND, LED16.C, U$306.P$1, XOSC16.2, XOSC16.4, XOSCRF16.2, XOSCRF16.4
GND17: ANT17.3, BAL17.2, BAL17.5, BAL17.6, BARO17.3, BARO17.4, BARO17.5, BTN17.2, C392.2, C393.2, C394.2, C395.2, C396.2, C397.2, C398.2, C399.2, C400.2, C401.2, C402.1, C403.1, C404.2, C405.1, C406.2, C409.2, C410.1, C411.2, C412.1, C413.1, C414.2, FB18.2, IC17.3, IC17.6, IC17.11, IC17.14, IC17.28, IC17.33, IMU17.P$20, LDO_VREG17.GND, LED17.C, U$325.P$1, XOSC17.2, XOSC17.4, XOSCRF17.2, XOSCRF17.4
GND18: ANT18.3, BAL18.2, BAL18.5, BAL18.6, BARO18.3, BARO18.4, BARO18.5, BTN18.2, C415.2, C416.2, C417.2, C418.2, C419.2, C420.2, C421.2, C422.2, C423.2, C424.2, C425.1, C426.1, C427.2, C428.1, C429.2, C432.2, C433.1, C434.2, C435.1, C436.1, C437.2, FB19.2, IC18.3, IC18.6, IC18.11, IC18.14, IC18.28, IC18.33, IMU18.P$20, LDO_VREG18.GND, LED18.C, U$344.P$1, XOSC18.2, XOSC18.4, XOSCRF18.2, XOSCRF18.4
GND19: ANT19.3, BAL19.2, BAL19.5, BAL19.6, BARO19.3, BARO19.4, BARO19.5, BTN19.2, C438.2, C439.2, C440.2, C441.2, C442.2, C443.2, C444.2, C445.2, C446.2, C447.2, C448.1, C449.1, C450.2, C451.1, C452.2, C455.2, C456.1, C457.2, C458.1, C459.1, C460.2, FB20.2, IC19.3, IC19.6, IC19.11, IC19.14, IC19.28, IC19.33, IMU19.P$20, LDO_VREG19.GND, LED19.C, U$363.P$1, XOSC19.2, XOSC19.4, XOSCRF19.2, XOSCRF19.4
GND20: ANT20.3, BAL20.2, BAL20.5, BAL20.6, BARO20.3, BARO20.4, BARO20.5, BTN20.2, C461.2, C462.2, C463.2, C464.2, C465.2, C466.2, C467.2, C468.2, C469.2, C470.2, C471.1, C472.1, C473.2, C474.1, C475.2, C478.2, C479.1, C480.2, C481.1, C482.1, C483.2, FB21.2, IC20.3, IC20.6, IC20.11, IC20.14, IC20.28, IC20.33, IMU20.P$20, LDO_VREG20.GND, LED20.C, U$382.P$1, XOSC20.2, XOSC20.4, XOSCRF20.2, XOSCRF20.4
GND21: ANT21.3, BAL21.2, BAL21.5, BAL21.6, BARO21.3, BARO21.4, BARO21.5, BTN21.2, C484.2, C485.2, C486.2, C487.2, C488.2, C489.2, C490.2, C491.2, C492.2, C493.2, C494.1, C495.1, C496.2, C497.1, C498.2, C501.2, C502.1, C503.2, C504.1, C505.1, C506.2, FB22.2, IC21.3, IC21.6, IC21.11, IC21.14, IC21.28, IC21.33, IMU21.P$20, LDO_VREG21.GND, LED21.C, U$401.P$1, XOSC21.2, XOSC21.4, XOSCRF21.2, XOSCRF21.4
GND22: ANT22.3, BAL22.2, BAL22.5, BAL22.6, BARO22.3, BARO22.4, BARO22.5, BTN22.2, C507.2, C508.2, C509.2, C510.2, C511.2, C512.2, C513.2, C514.2, C515.2, C516.2, C517.1, C518.1, C519.2, C520.1, C521.2, C524.2, C525.1, C526.2, C527.1, C528.1, C529.2, FB23.2, IC22.3, IC22.6, IC22.11, IC22.14, IC22.28, IC22.33, IMU22.P$20, LDO_VREG22.GND, LED22.C, U$420.P$1, XOSC22.2, XOSC22.4, XOSCRF22.2, XOSCRF22.4
GND23: ANT23.3, BAL23.2, BAL23.5, BAL23.6, BARO23.3, BARO23.4, BARO23.5, BTN23.2, C530.2, C531.2, C532.2, C533.2, C534.2, C535.2, C536.2, C537.2, C538.2, C539.2, C540.1, C541.1, C542.2, C543.1, C544.2, C547.2, C548.1, C549.2, C550.1, C551.1, C552.2, FB24.2, IC23.3, IC23.6, IC23.11, IC23.14, IC23.28, IC23.33, IMU23.P$20, LDO_VREG23.GND, LED23.C, U$439.P$1, XOSC23.2, XOSC23.4, XOSCRF23.2, XOSCRF23.4
GND24: ANT24.3, BAL24.2, BAL24.5, BAL24.6, BARO24.3, BARO24.4, BARO24.5, BTN24.2, C553.2, C554.2, C555.2, C556.2, C557.2, C558.2, C559.2, C560.2, C561.2, C562.2, C563.1, C564.1, C565.2, C566.1, C567.2, C570.2, C571.1, C572.2, C573.1, C574.1, C575.2, FB25.2, IC24.3, IC24.6, IC24.11, IC24.14, IC24.28, IC24.33, IMU24.P$20, LDO_VREG24.GND, LED24.C, U$458.P$1, XOSC24.2, XOSC24.4, XOSCRF24.2, XOSCRF24.4
GND25: ANT25.3, BAL25.2, BAL25.5, BAL25.6, BARO25.3, BARO25.4, BARO25.5, BTN25.2, C576.2, C577.2, C578.2, C579.2, C580.2, C581.2, C582.2, C583.2, C584.2, C585.2, C586.1, C587.1, C588.2, C589.1, C590.2, C593.2, C594.1, C595.2, C596.1, C597.1, C598.2, FB26.2, IC25.3, IC25.6, IC25.11, IC25.14, IC25.28, IC25.33, IMU25.P$20, LDO_VREG25.GND, LED25.C, U$477.P$1, XOSC25.2, XOSC25.4, XOSCRF25.2, XOSCRF25.4
GND26: ANT26.3, BAL26.2, BAL26.5, BAL26.6, BARO26.3, BARO26.4, BARO26.5, BTN26.2, C599.2, C600.2, C601.2, C602.2, C603.2, C604.2, C605.2, C606.2, C607.2, C608.2, C609.1, C610.1, C611.2, C612.1, C613.2, C616.2, C617.1, C618.2, C619.1, C620.1, C621.2, FB27.2, IC26.3, IC26.6, IC26.11, IC26.14, IC26.28, IC26.33, IMU26.P$20, LDO_VREG26.GND, LED26.C, U$496.P$1, XOSC26.2, XOSC26.4, XOSCRF26.2, XOSCRF26.4
GND27: ANT27.3, BAL27.2, BAL27.5, BAL27.6, BARO27.3, BARO27.4, BARO27.5, BTN27.2, C622.2, C623.2, C624.2, C625.2, C626.2, C627.2, C628.2, C629.2, C630.2, C631.2, C632.1, C633.1, C634.2, C635.1, C636.2, C639.2, C640.1, C641.2, C642.1, C643.1, C644.2, FB28.2, IC27.3, IC27.6, IC27.11, IC27.14, IC27.28, IC27.33, IMU27.P$20, LDO_VREG27.GND, LED27.C, U$515.P$1, XOSC27.2, XOSC27.4, XOSCRF27.2, XOSCRF27.4
GND28: ANT28.3, BAL28.2, BAL28.5, BAL28.6, BARO28.3, BARO28.4, BARO28.5, BTN28.2, C645.2, C646.2, C647.2, C648.2, C649.2, C650.2, C651.2, C652.2, C653.2, C654.2, C655.1, C656.1, C657.2, C658.1, C659.2, C662.2, C663.1, C664.2, C665.1, C666.1, C667.2, FB29.2, IC28.3, IC28.6, IC28.11, IC28.14, IC28.28, IC28.33, IMU28.P$20, LDO_VREG28.GND, LED28.C, U$534.P$1, XOSC28.2, XOSC28.4, XOSCRF28.2, XOSCRF28.4
GND29: ANT29.3, BAL29.2, BAL29.5, BAL29.6, BARO29.3, BARO29.4, BARO29.5, BTN29.2, C668.2, C669.2, C670.2, C671.2, C672.2, C673.2, C674.2, C675.2, C676.2, C677.2, C678.1, C679.1, C680.2, C681.1, C682.2, C685.2, C686.1, C687.2, C688.1, C689.1, C690.2, FB30.2, IC29.3, IC29.6, IC29.11, IC29.14, IC29.28, IC29.33, IMU29.P$20, LDO_VREG29.GND, LED29.C, U$553.P$1, XOSC29.2, XOSC29.4, XOSCRF29.2, XOSCRF29.4
GND30: ANT30.3, BAL30.2, BAL30.5, BAL30.6, BARO30.3, BARO30.4, BARO30.5, BTN30.2, C691.2, C692.2, C693.2, C694.2, C695.2, C696.2, C697.2, C698.2, C699.2, C700.2, C701.1, C702.1, C703.2, C704.1, C705.2, C708.2, C709.1, C710.2, C711.1, C712.1, C713.2, FB31.2, IC30.3, IC30.6, IC30.11, IC30.14, IC30.28, IC30.33, IMU30.P$20, LDO_VREG30.GND, LED30.C, U$572.P$1, XOSC30.2, XOSC30.4, XOSCRF30.2, XOSCRF30.4
GND31: ANT31.3, BAL31.2, BAL31.5, BAL31.6, BARO31.3, BARO31.4, BARO31.5, BTN31.2, C714.2, C715.2, C716.2, C717.2, C718.2, C719.2, C720.2, C721.2, C722.2, C723.2, C724.1, C725.1, C726.2, C727.1, C728.2, C731.2, C732.1, C733.2, C734.1, C735.1, C736.2, FB32.2, IC31.3, IC31.6, IC31.11, IC31.14, IC31.28, IC31.33, IMU31.P$20, LDO_VREG31.GND, LED31.C, U$591.P$1, XOSC31.2, XOSC31.4, XOSCRF31.2, XOSCRF31.4
GND32: ANT32.3, BAL32.2, BAL32.5, BAL32.6, BARO32.3, BARO32.4, BARO32.5, BTN32.2, C737.2, C738.2, C739.2, C740.2, C741.2, C742.2, C743.2, C744.2, C745.2, C746.2, C747.1, C748.1, C749.2, C750.1, C751.2, C754.2, C755.1, C756.2, C757.1, C758.1, C759.2, FB33.2, IC32.3, IC32.6, IC32.11, IC32.14, IC32.28, IC32.33, IMU32.P$20, LDO_VREG32.GND, LED32.C, U$610.P$1, XOSC32.2, XOSC32.4, XOSCRF32.2, XOSCRF32.4
GND33: ANT33.3, BAL33.2, BAL33.5, BAL33.6, BARO33.3, BARO33.4, BARO33.5, BTN33.2, C760.2, C761.2, C762.2, C763.2, C764.2, C765.2, C766.2, C767.2, C768.2, C769.2, C770.1, C771.1, C772.2, C773.1, C774.2, C777.2, C778.1, C779.2, C780.1, C781.1, C782.2, FB34.2, IC33.3, IC33.6, IC33.11, IC33.14, IC33.28, IC33.33, IMU33.P$20, LDO_VREG33.GND, LED33.C, U$629.P$1, XOSC33.2, XOSC33.4, XOSCRF33.2, XOSCRF33.4
GND34: ANT34.3, BAL34.2, BAL34.5, BAL34.6, BARO34.3, BARO34.4, BARO34.5, BTN34.2, C783.2, C784.2, C785.2, C786.2, C787.2, C788.2, C789.2, C790.2, C791.2, C792.2, C793.1, C794.1, C795.2, C796.1, C797.2, C800.2, C801.1, C802.2, C803.1, C804.1, C805.2, FB35.2, IC34.3, IC34.6, IC34.11, IC34.14, IC34.28, IC34.33, IMU34.P$20, LDO_VREG34.GND, LED34.C, U$648.P$1, XOSC34.2, XOSC34.4, XOSCRF34.2, XOSCRF34.4
unnamed: BAL.3, C11.2
unnamed: ANT.2, C13.1
unnamed: BAL.4, C12.2
unnamed: C32.1, IMU.P$10
unnamed: FB1.1, USB.5, USB.6, USB.7, USB.8, USB.9, USB.10, USB.11
unnamed: BTN1.1, R3.1
unnamed: LED1.A, R6.2
unnamed: BAL1.3, C39.2
unnamed: BAL1.4, C40.2
unnamed: ANT1.2, C41.1
unnamed: C46.1, IMU1.P$10
unnamed: LED.A, R4.2
unnamed: FB2.1, USB1.5, USB1.6, USB1.7, USB1.8, USB1.9, USB1.10, USB1.11
unnamed: BTN2.1, R11.1
unnamed: LED2.A, R13.2
unnamed: BAL2.3, C62.2
unnamed: BAL2.4, C63.2
unnamed: ANT2.2, C64.1
unnamed: C69.1, IMU2.P$10
unnamed: FB3.1, USB2.5, USB2.6, USB2.7, USB2.8, USB2.9, USB2.10, USB2.11
unnamed: BTN3.1, R16.1
unnamed: LED3.A, R18.2
unnamed: BTN.1, R1.1
unnamed: BAL3.3, C85.2
unnamed: BAL3.4, C86.2
unnamed: ANT3.2, C87.1
unnamed: C92.1, IMU3.P$10
unnamed: FB4.1, USB3.5, USB3.6, USB3.7, USB3.8, USB3.9, USB3.10, USB3.11
unnamed: BTN4.1, R21.1
unnamed: LED4.A, R23.2
unnamed: BAL4.3, C108.2
unnamed: BAL4.4, C109.2
unnamed: ANT4.2, C110.1
unnamed: C115.1, IMU4.P$10
unnamed: FB5.1, USB4.5, USB4.6, USB4.7, USB4.8, USB4.9, USB4.10, USB4.11
unnamed: BTN5.1, R26.1
unnamed: LED5.A, R28.2
unnamed: BAL5.3, C131.2
unnamed: BAL5.4, C132.2
unnamed: ANT5.2, C133.1
unnamed: C138.1, IMU5.P$10
unnamed: FB6.1, USB5.5, USB5.6, USB5.7, USB5.8, USB5.9, USB5.10, USB5.11
unnamed: BTN6.1, R31.1
unnamed: LED6.A, R33.2
unnamed: BAL6.3, C154.2
unnamed: BAL6.4, C155.2
unnamed: ANT6.2, C156.1
unnamed: C161.1, IMU6.P$10
unnamed: FB7.1, USB6.5, USB6.6, USB6.7, USB6.8, USB6.9, USB6.10, USB6.11
unnamed: BTN7.1, R36.1
unnamed: LED7.A, R38.2
unnamed: BAL7.3, C177.2
unnamed: BAL7.4, C178.2
unnamed: ANT7.2, C179.1
unnamed: C184.1, IMU7.P$10
unnamed: FB8.1, USB7.5, USB7.6, USB7.7, USB7.8, USB7.9, USB7.10, USB7.11
unnamed: BTN8.1, R41.1
unnamed: LED8.A, R43.2
unnamed: BAL8.3, C200.2
unnamed: BAL8.4, C201.2
unnamed: ANT8.2, C202.1
unnamed: C207.1, IMU8.P$10
unnamed: FB9.1, USB8.5, USB8.6, USB8.7, USB8.8, USB8.9, USB8.10, USB8.11
unnamed: BTN9.1, R46.1
unnamed: LED9.A, R48.2
unnamed: BAL9.3, C223.2
unnamed: BAL9.4, C224.2
unnamed: ANT9.2, C225.1
unnamed: C230.1, IMU9.P$10
unnamed: FB10.1, USB9.5, USB9.6, USB9.7, USB9.8, USB9.9, USB9.10, USB9.11
unnamed: BTN10.1, R51.1
unnamed: LED10.A, R53.2
unnamed: BAL10.3, C246.2
unnamed: BAL10.4, C247.2
unnamed: ANT10.2, C248.1
unnamed: C253.1, IMU10.P$10
unnamed: FB11.1, USB10.5, USB10.6, USB10.7, USB10.8, USB10.9, USB10.10, USB10.11
unnamed: BTN11.1, R56.1
unnamed: LED11.A, R58.2
unnamed: BAL11.3, C269.2
unnamed: BAL11.4, C270.2
unnamed: ANT11.2, C271.1
unnamed: C276.1, IMU11.P$10
unnamed: FB12.1, USB11.5, USB11.6, USB11.7, USB11.8, USB11.9, USB11.10, USB11.11
unnamed: BTN12.1, R61.1
unnamed: LED12.A, R63.2
unnamed: BAL12.3, C292.2
unnamed: BAL12.4, C293.2
unnamed: ANT12.2, C294.1
unnamed: C299.1, IMU12.P$10
unnamed: FB13.1, USB12.5, USB12.6, USB12.7, USB12.8, USB12.9, USB12.10, USB12.11
unnamed: BTN13.1, R66.1
unnamed: LED13.A, R68.2
unnamed: BAL13.3, C315.2
unnamed: BAL13.4, C316.2
unnamed: ANT13.2, C317.1
unnamed: C322.1, IMU13.P$10
unnamed: FB14.1, USB13.5, USB13.6, USB13.7, USB13.8, USB13.9, USB13.10, USB13.11
unnamed: BTN14.1, R71.1
unnamed: LED14.A, R73.2
unnamed: BAL14.3, C338.2
unnamed: BAL14.4, C339.2
unnamed: ANT14.2, C340.1
unnamed: C345.1, IMU14.P$10
unnamed: FB15.1, USB14.5, USB14.6, USB14.7, USB14.8, USB14.9, USB14.10, USB14.11
unnamed: BTN15.1, R76.1
unnamed: LED15.A, R78.2
unnamed: BAL15.3, C361.2
unnamed: BAL15.4, C362.2
unnamed: ANT15.2, C363.1
unnamed: C368.1, IMU15.P$10
unnamed: FB16.1, USB15.5, USB15.6, USB15.7, USB15.8, USB15.9, USB15.10, USB15.11
unnamed: BTN16.1, R81.1
unnamed: LED16.A, R83.2
unnamed: BAL16.3, C384.2
unnamed: BAL16.4, C385.2
unnamed: ANT16.2, C386.1
unnamed: C391.1, IMU16.P$10
unnamed: FB17.1, USB16.5, USB16.6, USB16.7, USB16.8, USB16.9, USB16.10, USB16.11
unnamed: BTN17.1, R86.1
unnamed: LED17.A, R88.2
unnamed: BAL17.3, C407.2
unnamed: BAL17.4, C408.2
unnamed: ANT17.2, C409.1
unnamed: C414.1, IMU17.P$10
unnamed: FB18.1, USB17.5, USB17.6, USB17.7, USB17.8, USB17.9, USB17.10, USB17.11
unnamed: BTN18.1, R91.1
unnamed: LED18.A, R93.2
unnamed: BAL18.3, C430.2
unnamed: BAL18.4, C431.2
unnamed: ANT18.2, C432.1
unnamed: C437.1, IMU18.P$10
unnamed: FB19.1, USB18.5, USB18.6, USB18.7, USB18.8, USB18.9, USB18.10, USB18.11
unnamed: BTN19.1, R96.1
unnamed: LED19.A, R98.2
unnamed: BAL19.3, C453.2
unnamed: BAL19.4, C454.2
unnamed: ANT19.2, C455.1
unnamed: C460.1, IMU19.P$10
unnamed: FB20.1, USB19.5, USB19.6, USB19.7, USB19.8, USB19.9, USB19.10, USB19.11
unnamed: BTN20.1, R101.1
unnamed: LED20.A, R103.2
unnamed: BAL20.3, C476.2
unnamed: BAL20.4, C477.2
unnamed: ANT20.2, C478.1
unnamed: C483.1, IMU20.P$10
unnamed: FB21.1, USB20.5, USB20.6, USB20.7, USB20.8, USB20.9, USB20.10, USB20.11
unnamed: BTN21.1, R106.1
unnamed: LED21.A, R108.2
unnamed: BAL21.3, C499.2
unnamed: BAL21.4, C500.2
unnamed: ANT21.2, C501.1
unnamed: C506.1, IMU21.P$10
unnamed: FB22.1, USB21.5, USB21.6, USB21.7, USB21.8, USB21.9, USB21.10, USB21.11
unnamed: BTN22.1, R111.1
unnamed: LED22.A, R113.2
unnamed: BAL22.3, C522.2
unnamed: BAL22.4, C523.2
unnamed: ANT22.2, C524.1
unnamed: C529.1, IMU22.P$10
unnamed: FB23.1, USB22.5, USB22.6, USB22.7, USB22.8, USB22.9, USB22.10, USB22.11
unnamed: BTN23.1, R116.1
unnamed: LED23.A, R118.2
unnamed: BAL23.3, C545.2
unnamed: BAL23.4, C546.2
unnamed: ANT23.2, C547.1
unnamed: C552.1, IMU23.P$10
unnamed: FB24.1, USB23.5, USB23.6, USB23.7, USB23.8, USB23.9, USB23.10, USB23.11
unnamed: BTN24.1, R121.1
unnamed: LED24.A, R123.2
unnamed: BAL24.3, C568.2
unnamed: BAL24.4, C569.2
unnamed: ANT24.2, C570.1
unnamed: C575.1, IMU24.P$10
unnamed: FB25.1, USB24.5, USB24.6, USB24.7, USB24.8, USB24.9, USB24.10, USB24.11
unnamed: BTN25.1, R126.1
unnamed: LED25.A, R128.2
unnamed: BAL25.3, C591.2
unnamed: BAL25.4, C592.2
unnamed: ANT25.2, C593.1
unnamed: C598.1, IMU25.P$10
unnamed: FB26.1, USB25.5, USB25.6, USB25.7, USB25.8, USB25.9, USB25.10, USB25.11
unnamed: BTN26.1, R131.1
unnamed: LED26.A, R133.2
unnamed: BAL26.3, C614.2
unnamed: BAL26.4, C615.2
unnamed: ANT26.2, C616.1
unnamed: C621.1, IMU26.P$10
unnamed: FB27.1, USB26.5, USB26.6, USB26.7, USB26.8, USB26.9, USB26.10, USB26.11
unnamed: BTN27.1, R136.1
unnamed: LED27.A, R138.2
unnamed: BAL27.3, C637.2
unnamed: BAL27.4, C638.2
unnamed: ANT27.2, C639.1
unnamed: C644.1, IMU27.P$10
unnamed: FB28.1, USB27.5, USB27.6, USB27.7, USB27.8, USB27.9, USB27.10, USB27.11
unnamed: BTN28.1, R141.1
unnamed: LED28.A, R143.2
unnamed: BAL28.3, C660.2
unnamed: BAL28.4, C661.2
unnamed: ANT28.2, C662.1
unnamed: C667.1, IMU28.P$10
unnamed: FB29.1, USB28.5, USB28.6, USB28.7, USB28.8, USB28.9, USB28.10, USB28.11
unnamed: BTN29.1, R146.1
unnamed: LED29.A, R148.2
unnamed: BAL29.3, C683.2
unnamed: BAL29.4, C684.2
unnamed: ANT29.2, C685.1
unnamed: C690.1, IMU29.P$10
unnamed: FB30.1, USB29.5, USB29.6, USB29.7, USB29.8, USB29.9, USB29.10, USB29.11
unnamed: BTN30.1, R151.1
unnamed: LED30.A, R153.2
unnamed: BAL30.3, C706.2
unnamed: BAL30.4, C707.2
unnamed: ANT30.2, C708.1
unnamed: C713.1, IMU30.P$10
unnamed: FB31.1, USB30.5, USB30.6, USB30.7, USB30.8, USB30.9, USB30.10, USB30.11
unnamed: BTN31.1, R156.1
unnamed: LED31.A, R158.2
unnamed: BAL31.3, C729.2
unnamed: BAL31.4, C730.2
unnamed: ANT31.2, C731.1
unnamed: C736.1, IMU31.P$10
unnamed: FB32.1, USB31.5, USB31.6, USB31.7, USB31.8, USB31.9, USB31.10, USB31.11
unnamed: BTN32.1, R161.1
unnamed: LED32.A, R163.2
unnamed: BAL32.3, C752.2
unnamed: BAL32.4, C753.2
unnamed: ANT32.2, C754.1
unnamed: C759.1, IMU32.P$10
unnamed: FB33.1, USB32.5, USB32.6, USB32.7, USB32.8, USB32.9, USB32.10, USB32.11
unnamed: BTN33.1, R166.1
unnamed: LED33.A, R168.2
unnamed: BAL33.3, C775.2
unnamed: BAL33.4, C776.2
unnamed: ANT33.2, C777.1
unnamed: C782.1, IMU33.P$10
unnamed: FB34.1, USB33.5, USB33.6, USB33.7, USB33.8, USB33.9, USB33.10, USB33.11
unnamed: BTN34.1, R171.1
unnamed: LED34.A, R173.2
unnamed: BAL34.3, C798.2
unnamed: BAL34.4, C799.2
unnamed: ANT34.2, C800.1
unnamed: C805.1, IMU34.P$10
unnamed: FB35.1, USB34.5, USB34.6, USB34.7, USB34.8, USB34.9, USB34.10, USB34.11
PA1: IC1.25, U$21.P$1
PA2: IC1.27, U$22.P$1
PA3: IC2.25, U$52.P$1
PA4: IC2.27, U$53.P$1
PA5: IC3.25, U$72.P$1
PA6: IC3.27, U$73.P$1
PA06/A0: IC.7, U$54.P$1
PA06/A1: IC1.7, U$23.P$1
PA06/A2: IC2.7, U$55.P$1
PA06/A3: IC3.7, U$74.P$1
PA06/A4: IC4.7, U$93.P$1
PA06/A5: IC5.7, U$112.P$1
PA06/A6: IC6.7, U$131.P$1
PA06/A7: IC7.7, U$150.P$1
PA06/A8: IC8.7, U$169.P$1
PA06/A9: IC9.7, U$188.P$1
PA06/A10: IC10.7, U$207.P$1
PA06/A11: IC11.7, U$226.P$1
PA06/A12: IC12.7, U$245.P$1
PA06/A13: IC13.7, U$264.P$1
PA06/A14: IC14.7, U$283.P$1
PA06/A15: IC15.7, U$302.P$1
PA06/A16: IC16.7, U$321.P$1
PA06/A17: IC17.7, U$340.P$1
PA06/A18: IC18.7, U$359.P$1
PA06/A19: IC19.7, U$378.P$1
PA06/A20: IC20.7, U$397.P$1
PA06/A21: IC21.7, U$416.P$1
PA06/A22: IC22.7, U$435.P$1
PA06/A23: IC23.7, U$454.P$1
PA06/A24: IC24.7, U$473.P$1
PA06/A25: IC25.7, U$492.P$1
PA06/A26: IC26.7, U$511.P$1
PA06/A27: IC27.7, U$530.P$1
PA06/A28: IC28.7, U$549.P$1
PA06/A29: IC29.7, U$568.P$1
PA06/A30: IC30.7, U$587.P$1
PA06/A31: IC31.7, U$606.P$1
PA06/A32: IC32.7, U$625.P$1
PA06/A33: IC33.7, U$644.P$1
PA06/A34: IC34.7, U$663.P$1
PA7: IC4.25, U$91.P$1
PA07/A1: IC.8, U$43.P$1
PA07/A2: IC1.8, U$17.P$1
PA07/A3: IC2.8, U$44.P$1
PA07/A4: IC3.8, U$68.P$1
PA07/A5: IC4.8, U$87.P$1
PA07/A6: IC5.8, U$106.P$1
PA07/A7: IC6.8, U$125.P$1
PA07/A8: IC7.8, U$144.P$1
PA07/A9: IC8.8, U$163.P$1
PA07/A10: IC9.8, U$182.P$1
PA07/A11: IC10.8, U$201.P$1
PA07/A12: IC11.8, U$220.P$1
PA07/A13: IC12.8, U$239.P$1
PA07/A14: IC13.8, U$258.P$1
PA07/A15: IC14.8, U$277.P$1
PA07/A16: IC15.8, U$296.P$1
PA07/A17: IC16.8, U$315.P$1
PA07/A18: IC17.8, U$334.P$1
PA07/A19: IC18.8, U$353.P$1
PA07/A20: IC19.8, U$372.P$1
PA07/A21: IC20.8, U$391.P$1
PA07/A22: IC21.8, U$410.P$1
PA07/A23: IC22.8, U$429.P$1
PA07/A24: IC23.8, U$448.P$1
PA07/A25: IC24.8, U$467.P$1
PA07/A26: IC25.8, U$486.P$1
PA07/A27: IC26.8, U$505.P$1
PA07/A28: IC27.8, U$524.P$1
PA07/A29: IC28.8, U$543.P$1
PA07/A30: IC29.8, U$562.P$1
PA07/A31: IC30.8, U$581.P$1
PA07/A32: IC31.8, U$600.P$1
PA07/A33: IC32.8, U$619.P$1
PA07/A34: IC33.8, U$638.P$1
PA07/A35: IC34.8, U$657.P$1
PA8: IC4.27, U$92.P$1
PA08/I2C/SDA: BARO.7, IC.9, IMU.P$24, R8.1, U$42.P$1
PA08/I2C/SDA1: BARO1.7, IC1.9, IMU1.P$24, R7.1, U$16.P$1
PA08/I2C/SDA2: BARO2.7, IC2.9, IMU2.P$24, R14.1, U$40.P$1
PA08/I2C/SDA3: BARO3.7, IC3.9, IMU3.P$24, R19.1, U$67.P$1
PA08/I2C/SDA4: BARO4.7, IC4.9, IMU4.P$24, R24.1, U$86.P$1
PA08/I2C/SDA5: BARO5.7, IC5.9, IMU5.P$24, R29.1, U$105.P$1
PA08/I2C/SDA6: BARO6.7, IC6.9, IMU6.P$24, R34.1, U$124.P$1
PA08/I2C/SDA7: BARO7.7, IC7.9, IMU7.P$24, R39.1, U$143.P$1
PA08/I2C/SDA8: BARO8.7, IC8.9, IMU8.P$24, R44.1, U$162.P$1
PA08/I2C/SDA9: BARO9.7, IC9.9, IMU9.P$24, R49.1, U$181.P$1
PA08/I2C/SDA10: BARO10.7, IC10.9, IMU10.P$24, R54.1, U$200.P$1
PA08/I2C/SDA11: BARO11.7, IC11.9, IMU11.P$24, R59.1, U$219.P$1
PA08/I2C/SDA12: BARO12.7, IC12.9, IMU12.P$24, R64.1, U$238.P$1
PA08/I2C/SDA13: BARO13.7, IC13.9, IMU13.P$24, R69.1, U$257.P$1
PA08/I2C/SDA14: BARO14.7, IC14.9, IMU14.P$24, R74.1, U$276.P$1
PA08/I2C/SDA15: BARO15.7, IC15.9, IMU15.P$24, R79.1, U$295.P$1
PA08/I2C/SDA16: BARO16.7, IC16.9, IMU16.P$24, R84.1, U$314.P$1
PA08/I2C/SDA17: BARO17.7, IC17.9, IMU17.P$24, R89.1, U$333.P$1
PA08/I2C/SDA18: BARO18.7, IC18.9, IMU18.P$24, R94.1, U$352.P$1
PA08/I2C/SDA19: BARO19.7, IC19.9, IMU19.P$24, R99.1, U$371.P$1
PA08/I2C/SDA20: BARO20.7, IC20.9, IMU20.P$24, R104.1, U$390.P$1
PA08/I2C/SDA21: BARO21.7, IC21.9, IMU21.P$24, R109.1, U$409.P$1
PA08/I2C/SDA22: BARO22.7, IC22.9, IMU22.P$24, R114.1, U$428.P$1
PA08/I2C/SDA23: BARO23.7, IC23.9, IMU23.P$24, R119.1, U$447.P$1
PA08/I2C/SDA24: BARO24.7, IC24.9, IMU24.P$24, R124.1, U$466.P$1
PA08/I2C/SDA25: BARO25.7, IC25.9, IMU25.P$24, R129.1, U$485.P$1
PA08/I2C/SDA26: BARO26.7, IC26.9, IMU26.P$24, R134.1, U$504.P$1
PA08/I2C/SDA27: BARO27.7, IC27.9, IMU27.P$24, R139.1, U$523.P$1
PA08/I2C/SDA28: BARO28.7, IC28.9, IMU28.P$24, R144.1, U$542.P$1
PA08/I2C/SDA29: BARO29.7, IC29.9, IMU29.P$24, R149.1, U$561.P$1
PA08/I2C/SDA30: BARO30.7, IC30.9, IMU30.P$24, R154.1, U$580.P$1
PA08/I2C/SDA31: BARO31.7, IC31.9, IMU31.P$24, R159.1, U$599.P$1
PA08/I2C/SDA32: BARO32.7, IC32.9, IMU32.P$24, R164.1, U$618.P$1
PA08/I2C/SDA33: BARO33.7, IC33.9, IMU33.P$24, R169.1, U$637.P$1
PA08/I2C/SDA34: BARO34.7, IC34.9, IMU34.P$24, R174.1, U$656.P$1
PA9: IC5.25, U$110.P$1
PA09/I2C/SCL: BARO.8, IC.10, IMU.P$23, R9.1, U$41.P$1
PA09/I2C/SCL1: BARO1.8, IC1.10, IMU1.P$23, R10.1, U$15.P$1
PA09/I2C/SCL2: BARO2.8, IC2.10, IMU2.P$23, R15.1, U$34.P$1
PA09/I2C/SCL3: BARO3.8, IC3.10, IMU3.P$23, R20.1, U$66.P$1
PA09/I2C/SCL4: BARO4.8, IC4.10, IMU4.P$23, R25.1, U$85.P$1
PA09/I2C/SCL5: BARO5.8, IC5.10, IMU5.P$23, R30.1, U$104.P$1
PA09/I2C/SCL6: BARO6.8, IC6.10, IMU6.P$23, R35.1, U$123.P$1
PA09/I2C/SCL7: BARO7.8, IC7.10, IMU7.P$23, R40.1, U$142.P$1
PA09/I2C/SCL8: BARO8.8, IC8.10, IMU8.P$23, R45.1, U$161.P$1
PA09/I2C/SCL9: BARO9.8, IC9.10, IMU9.P$23, R50.1, U$180.P$1
PA09/I2C/SCL10: BARO10.8, IC10.10, IMU10.P$23, R55.1, U$199.P$1
PA09/I2C/SCL11: BARO11.8, IC11.10, IMU11.P$23, R60.1, U$218.P$1
PA09/I2C/SCL12: BARO12.8, IC12.10, IMU12.P$23, R65.1, U$237.P$1
PA09/I2C/SCL13: BARO13.8, IC13.10, IMU13.P$23, R70.1, U$256.P$1
PA09/I2C/SCL14: BARO14.8, IC14.10, IMU14.P$23, R75.1, U$275.P$1
PA09/I2C/SCL15: BARO15.8, IC15.10, IMU15.P$23, R80.1, U$294.P$1
PA09/I2C/SCL16: BARO16.8, IC16.10, IMU16.P$23, R85.1, U$313.P$1
PA09/I2C/SCL17: BARO17.8, IC17.10, IMU17.P$23, R90.1, U$332.P$1
PA09/I2C/SCL18: BARO18.8, IC18.10, IMU18.P$23, R95.1, U$351.P$1
PA09/I2C/SCL19: BARO19.8, IC19.10, IMU19.P$23, R100.1, U$370.P$1
PA09/I2C/SCL20: BARO20.8, IC20.10, IMU20.P$23, R105.1, U$389.P$1
PA09/I2C/SCL21: BARO21.8, IC21.10, IMU21.P$23, R110.1, U$408.P$1
PA09/I2C/SCL22: BARO22.8, IC22.10, IMU22.P$23, R115.1, U$427.P$1
PA09/I2C/SCL23: BARO23.8, IC23.10, IMU23.P$23, R120.1, U$446.P$1
PA09/I2C/SCL24: BARO24.8, IC24.10, IMU24.P$23, R125.1, U$465.P$1
PA09/I2C/SCL25: BARO25.8, IC25.10, IMU25.P$23, R130.1, U$484.P$1
PA09/I2C/SCL26: BARO26.8, IC26.10, IMU26.P$23, R135.1, U$503.P$1
PA09/I2C/SCL27: BARO27.8, IC27.10, IMU27.P$23, R140.1, U$522.P$1
PA09/I2C/SCL28: BARO28.8, IC28.10, IMU28.P$23, R145.1, U$541.P$1
PA09/I2C/SCL29: BARO29.8, IC29.10, IMU29.P$23, R150.1, U$560.P$1
PA09/I2C/SCL30: BARO30.8, IC30.10, IMU30.P$23, R155.1, U$579.P$1
PA09/I2C/SCL31: BARO31.8, IC31.10, IMU31.P$23, R160.1, U$598.P$1
PA09/I2C/SCL32: BARO32.8, IC32.10, IMU32.P$23, R165.1, U$617.P$1
PA09/I2C/SCL33: BARO33.8, IC33.10, IMU33.P$23, R170.1, U$636.P$1
PA09/I2C/SCL34: BARO34.8, IC34.10, IMU34.P$23, R175.1, U$655.P$1
PA10: IC5.27, U$111.P$1
PA11: IC6.25, U$129.P$1
PA12: IC6.27, U$130.P$1
PA13: IC7.25, U$148.P$1
PA14: IC7.27, U$149.P$1
PA14/XIN_MC/RX: C3.2, IC.15, XOSC.1
PA14/XIN_MC/RX1: C37.2, IC1.15, XOSC1.1
PA14/XIN_MC/RX2: C60.2, IC2.15, XOSC2.1
PA14/XIN_MC/RX3: C83.2, IC3.15, XOSC3.1
PA14/XIN_MC/RX4: C106.2, IC4.15, XOSC4.1
PA14/XIN_MC/RX5: C129.2, IC5.15, XOSC5.1
PA14/XIN_MC/RX6: C152.2, IC6.15, XOSC6.1
PA14/XIN_MC/RX7: C175.2, IC7.15, XOSC7.1
PA14/XIN_MC/RX8: C198.2, IC8.15, XOSC8.1
PA14/XIN_MC/RX9: C221.2, IC9.15, XOSC9.1
PA14/XIN_MC/RX10: C244.2, IC10.15, XOSC10.1
PA14/XIN_MC/RX11: C267.2, IC11.15, XOSC11.1
PA14/XIN_MC/RX12: C290.2, IC12.15, XOSC12.1
PA14/XIN_MC/RX13: C313.2, IC13.15, XOSC13.1
PA14/XIN_MC/RX14: C336.2, IC14.15, XOSC14.1
PA14/XIN_MC/RX15: C359.2, IC15.15, XOSC15.1
PA14/XIN_MC/RX16: C382.2, IC16.15, XOSC16.1
PA14/XIN_MC/RX17: C405.2, IC17.15, XOSC17.1
PA14/XIN_MC/RX18: C428.2, IC18.15, XOSC18.1
PA14/XIN_MC/RX19: C451.2, IC19.15, XOSC19.1
PA14/XIN_MC/RX20: C474.2, IC20.15, XOSC20.1
PA14/XIN_MC/RX21: C497.2, IC21.15, XOSC21.1
PA14/XIN_MC/RX22: C520.2, IC22.15, XOSC22.1
PA14/XIN_MC/RX23: C543.2, IC23.15, XOSC23.1
PA14/XIN_MC/RX24: C566.2, IC24.15, XOSC24.1
PA14/XIN_MC/RX25: C589.2, IC25.15, XOSC25.1
PA14/XIN_MC/RX26: C612.2, IC26.15, XOSC26.1
PA14/XIN_MC/RX27: C635.2, IC27.15, XOSC27.1
PA14/XIN_MC/RX28: C658.2, IC28.15, XOSC28.1
PA14/XIN_MC/RX29: C681.2, IC29.15, XOSC29.1
PA14/XIN_MC/RX30: C704.2, IC30.15, XOSC30.1
PA14/XIN_MC/RX31: C727.2, IC31.15, XOSC31.1
PA14/XIN_MC/RX32: C750.2, IC32.15, XOSC32.1
PA14/XIN_MC/RX33: C773.2, IC33.15, XOSC33.1
PA14/XIN_MC/RX34: C796.2, IC34.15, XOSC34.1
PA15: IC8.25, U$167.P$1
PA15/XOUT_MC/TX: C4.1, IC.16, U$39.P$1, XOSC.3
PA15/XOUT_MC/TX1: C38.1, IC1.16, U$14.P$1, XOSC1.3
PA15/XOUT_MC/TX2: C61.1, IC2.16, U$33.P$1, XOSC2.3
PA15/XOUT_MC/TX3: C84.1, IC3.16, U$65.P$1, XOSC3.3
PA15/XOUT_MC/TX4: C107.1, IC4.16, U$84.P$1, XOSC4.3
PA15/XOUT_MC/TX5: C130.1, IC5.16, U$103.P$1, XOSC5.3
PA15/XOUT_MC/TX6: C153.1, IC6.16, U$122.P$1, XOSC6.3
PA15/XOUT_MC/TX7: C176.1, IC7.16, U$141.P$1, XOSC7.3
PA15/XOUT_MC/TX8: C199.1, IC8.16, U$160.P$1, XOSC8.3
PA15/XOUT_MC/TX9: C222.1, IC9.16, U$179.P$1, XOSC9.3
PA15/XOUT_MC/TX10: C245.1, IC10.16, U$198.P$1, XOSC10.3
PA15/XOUT_MC/TX11: C268.1, IC11.16, U$217.P$1, XOSC11.3
PA15/XOUT_MC/TX12: C291.1, IC12.16, U$236.P$1, XOSC12.3
PA15/XOUT_MC/TX13: C314.1, IC13.16, U$255.P$1, XOSC13.3
PA15/XOUT_MC/TX14: C337.1, IC14.16, U$274.P$1, XOSC14.3
PA15/XOUT_MC/TX15: C360.1, IC15.16, U$293.P$1, XOSC15.3
PA15/XOUT_MC/TX16: C383.1, IC16.16, U$312.P$1, XOSC16.3
PA15/XOUT_MC/TX17: C406.1, IC17.16, U$331.P$1, XOSC17.3
PA15/XOUT_MC/TX18: C429.1, IC18.16, U$350.P$1, XOSC18.3
PA15/XOUT_MC/TX19: C452.1, IC19.16, U$369.P$1, XOSC19.3
PA15/XOUT_MC/TX20: C475.1, IC20.16, U$388.P$1, XOSC20.3
PA15/XOUT_MC/TX21: C498.1, IC21.16, U$407.P$1, XOSC21.3
PA15/XOUT_MC/TX22: C521.1, IC22.16, U$426.P$1, XOSC22.3
PA15/XOUT_MC/TX23: C544.1, IC23.16, U$445.P$1, XOSC23.3
PA15/XOUT_MC/TX24: C567.1, IC24.16, U$464.P$1, XOSC24.3
PA15/XOUT_MC/TX25: C590.1, IC25.16, U$483.P$1, XOSC25.3
PA15/XOUT_MC/TX26: C613.1, IC26.16, U$502.P$1, XOSC26.3
PA15/XOUT_MC/TX27: C636.1, IC27.16, U$521.P$1, XOSC27.3
PA15/XOUT_MC/TX28: C659.1, IC28.16, U$540.P$1, XOSC28.3
PA15/XOUT_MC/TX29: C682.1, IC29.16, U$559.P$1, XOSC29.3
PA15/XOUT_MC/TX30: C705.1, IC30.16, U$578.P$1, XOSC30.3
PA15/XOUT_MC/TX31: C728.1, IC31.16, U$597.P$1, XOSC31.3
PA15/XOUT_MC/TX32: C751.1, IC32.16, U$616.P$1, XOSC32.3
PA15/XOUT_MC/TX33: C774.1, IC33.16, U$635.P$1, XOSC33.3
PA15/XOUT_MC/TX34: C797.1, IC34.16, U$654.P$1, XOSC34.3
PA16: IC8.27, U$168.P$1
PA16/I2C: IC.17, U$38.P$1
PA16/I2C1: IC1.17, U$13.P$1
PA16/I2C2: IC2.17, U$32.P$1
PA16/I2C3: IC3.17, U$64.P$1
PA16/I2C4: IC4.17, U$83.P$1
PA16/I2C5: IC5.17, U$102.P$1
PA16/I2C6: IC6.17, U$121.P$1
PA16/I2C7: IC7.17, U$140.P$1
PA16/I2C8: IC8.17, U$159.P$1
PA16/I2C9: IC9.17, U$178.P$1
PA16/I2C10: IC10.17, U$197.P$1
PA16/I2C11: IC11.17, U$216.P$1
PA16/I2C12: IC12.17, U$235.P$1
PA16/I2C13: IC13.17, U$254.P$1
PA16/I2C14: IC14.17, U$273.P$1
PA16/I2C15: IC15.17, U$292.P$1
PA16/I2C16: IC16.17, U$311.P$1
PA16/I2C17: IC17.17, U$330.P$1
PA16/I2C18: IC18.17, U$349.P$1
PA16/I2C19: IC19.17, U$368.P$1
PA16/I2C20: IC20.17, U$387.P$1
PA16/I2C21: IC21.17, U$406.P$1
PA16/I2C22: IC22.17, U$425.P$1
PA16/I2C23: IC23.17, U$444.P$1
PA16/I2C24: IC24.17, U$463.P$1
PA16/I2C25: IC25.17, U$482.P$1
PA16/I2C26: IC26.17, U$501.P$1
PA16/I2C27: IC27.17, U$520.P$1
PA16/I2C28: IC28.17, U$539.P$1
PA16/I2C29: IC29.17, U$558.P$1
PA16/I2C30: IC30.17, U$577.P$1
PA16/I2C31: IC31.17, U$596.P$1
PA16/I2C32: IC32.17, U$615.P$1
PA16/I2C33: IC33.17, U$634.P$1
PA16/I2C34: IC34.17, U$653.P$1
PA17: IC9.25, U$186.P$1
PA17/I2C: IC.18, U$37.P$1
PA17/I2C1: IC1.18, U$12.P$1
PA17/I2C2: IC2.18, U$31.P$1
PA17/I2C3: IC3.18, U$63.P$1
PA17/I2C4: IC4.18, U$82.P$1
PA17/I2C5: IC5.18, U$101.P$1
PA17/I2C6: IC6.18, U$120.P$1
PA17/I2C7: IC7.18, U$139.P$1
PA17/I2C8: IC8.18, U$158.P$1
PA17/I2C9: IC9.18, U$177.P$1
PA17/I2C10: IC10.18, U$196.P$1
PA17/I2C11: IC11.18, U$215.P$1
PA17/I2C12: IC12.18, U$234.P$1
PA17/I2C13: IC13.18, U$253.P$1
PA17/I2C14: IC14.18, U$272.P$1
PA17/I2C15: IC15.18, U$291.P$1
PA17/I2C16: IC16.18, U$310.P$1
PA17/I2C17: IC17.18, U$329.P$1
PA17/I2C18: IC18.18, U$348.P$1
PA17/I2C19: IC19.18, U$367.P$1
PA17/I2C20: IC20.18, U$386.P$1
PA17/I2C21: IC21.18, U$405.P$1
PA17/I2C22: IC22.18, U$424.P$1
PA17/I2C23: IC23.18, U$443.P$1
PA17/I2C24: IC24.18, U$462.P$1
PA17/I2C25: IC25.18, U$481.P$1
PA17/I2C26: IC26.18, U$500.P$1
PA17/I2C27: IC27.18, U$519.P$1
PA17/I2C28: IC28.18, U$538.P$1
PA17/I2C29: IC29.18, U$557.P$1
PA17/I2C30: IC30.18, U$576.P$1
PA17/I2C31: IC31.18, U$595.P$1
PA17/I2C32: IC32.18, U$614.P$1
PA17/I2C33: IC33.18, U$633.P$1
PA17/I2C34: IC34.18, U$652.P$1
PA18: IC9.27, U$187.P$1
PA18/INTA: IC.19, IMU.P$11, U$36.P$1
PA18/INTA1: IC1.19, IMU1.P$11, U$11.P$1
PA18/INTA2: IC2.19, IMU2.P$11, U$30.P$1
PA18/INTA3: IC3.19, IMU3.P$11, U$62.P$1
PA18/INTA4: IC4.19, IMU4.P$11, U$81.P$1
PA18/INTA5: IC5.19, IMU5.P$11, U$100.P$1
PA18/INTA6: IC6.19, IMU6.P$11, U$119.P$1
PA18/INTA7: IC7.19, IMU7.P$11, U$138.P$1
PA18/INTA8: IC8.19, IMU8.P$11, U$157.P$1
PA18/INTA9: IC9.19, IMU9.P$11, U$176.P$1
PA18/INTA10: IC10.19, IMU10.P$11, U$195.P$1
PA18/INTA11: IC11.19, IMU11.P$11, U$214.P$1
PA18/INTA12: IC12.19, IMU12.P$11, U$233.P$1
PA18/INTA13: IC13.19, IMU13.P$11, U$252.P$1
PA18/INTA14: IC14.19, IMU14.P$11, U$271.P$1
PA18/INTA15: IC15.19, IMU15.P$11, U$290.P$1
PA18/INTA16: IC16.19, IMU16.P$11, U$309.P$1
PA18/INTA17: IC17.19, IMU17.P$11, U$328.P$1
PA18/INTA18: IC18.19, IMU18.P$11, U$347.P$1
PA18/INTA19: IC19.19, IMU19.P$11, U$366.P$1
PA18/INTA20: IC20.19, IMU20.P$11, U$385.P$1
PA18/INTA21: IC21.19, IMU21.P$11, U$404.P$1
PA18/INTA22: IC22.19, IMU22.P$11, U$423.P$1
PA18/INTA23: IC23.19, IMU23.P$11, U$442.P$1
PA18/INTA24: IC24.19, IMU24.P$11, U$461.P$1
PA18/INTA25: IC25.19, IMU25.P$11, U$480.P$1
PA18/INTA26: IC26.19, IMU26.P$11, U$499.P$1
PA18/INTA27: IC27.19, IMU27.P$11, U$518.P$1
PA18/INTA28: IC28.19, IMU28.P$11, U$537.P$1
PA18/INTA29: IC29.19, IMU29.P$11, U$556.P$1
PA18/INTA30: IC30.19, IMU30.P$11, U$575.P$1
PA18/INTA31: IC31.19, IMU31.P$11, U$594.P$1
PA18/INTA32: IC32.19, IMU32.P$11, U$613.P$1
PA18/INTA33: IC33.19, IMU33.P$11, U$632.P$1
PA18/INTA34: IC34.19, IMU34.P$11, U$651.P$1
PA19: IC10.25, U$205.P$1
PA19/FSYNC: IC.20, IMU.P$12, U$35.P$1
PA19/FSYNC1: IC1.20, IMU1.P$12, U$8.P$1
PA19/FSYNC2: IC2.20, IMU2.P$12, U$29.P$1
PA19/FSYNC3: IC3.20, IMU3.P$12, U$61.P$1
PA19/FSYNC4: IC4.20, IMU4.P$12, U$80.P$1
PA19/FSYNC5: IC5.20, IMU5.P$12, U$99.P$1
PA19/FSYNC6: IC6.20, IMU6.P$12, U$118.P$1
PA19/FSYNC7: IC7.20, IMU7.P$12, U$137.P$1
PA19/FSYNC8: IC8.20, IMU8.P$12, U$156.P$1
PA19/FSYNC9: IC9.20, IMU9.P$12, U$175.P$1
PA19/FSYNC10: IC10.20, IMU10.P$12, U$194.P$1
PA19/FSYNC11: IC11.20, IMU11.P$12, U$213.P$1
PA19/FSYNC12: IC12.20, IMU12.P$12, U$232.P$1
PA19/FSYNC13: IC13.20, IMU13.P$12, U$251.P$1
PA19/FSYNC14: IC14.20, IMU14.P$12, U$270.P$1
PA19/FSYNC15: IC15.20, IMU15.P$12, U$289.P$1
PA19/FSYNC16: IC16.20, IMU16.P$12, U$308.P$1
PA19/FSYNC17: IC17.20, IMU17.P$12, U$327.P$1
PA19/FSYNC18: IC18.20, IMU18.P$12, U$346.P$1
PA19/FSYNC19: IC19.20, IMU19.P$12, U$365.P$1
PA19/FSYNC20: IC20.20, IMU20.P$12, U$384.P$1
PA19/FSYNC21: IC21.20, IMU21.P$12, U$403.P$1
PA19/FSYNC22: IC22.20, IMU22.P$12, U$422.P$1
PA19/FSYNC23: IC23.20, IMU23.P$12, U$441.P$1
PA19/FSYNC24: IC24.20, IMU24.P$12, U$460.P$1
PA19/FSYNC25: IC25.20, IMU25.P$12, U$479.P$1
PA19/FSYNC26: IC26.20, IMU26.P$12, U$498.P$1
PA19/FSYNC27: IC27.20, IMU27.P$12, U$517.P$1
PA19/FSYNC28: IC28.20, IMU28.P$12, U$536.P$1
PA19/FSYNC29: IC29.20, IMU29.P$12, U$555.P$1
PA19/FSYNC30: IC30.20, IMU30.P$12, U$574.P$1
PA19/FSYNC31: IC31.20, IMU31.P$12, U$593.P$1
PA19/FSYNC32: IC32.20, IMU32.P$12, U$612.P$1
PA19/FSYNC33: IC33.20, IMU33.P$12, U$631.P$1
PA19/FSYNC34: IC34.20, IMU34.P$12, U$650.P$1
PA20: IC10.27, U$206.P$1
PA21: IC11.25, U$224.P$1
PA22: IC11.27, U$225.P$1
PA23: IC12.25, U$243.P$1
PA24: IC12.27, U$244.P$1
PA24/USBDM: IC.22, U$9.P$1, USB.2
PA24/USBDM1: IC1.22, U$24.P$1, USB1.2
PA24/USBDM2: IC2.22, U$56.P$1, USB2.2
PA24/USBDM3: IC3.22, U$75.P$1, USB3.2
PA24/USBDM4: IC4.22, U$94.P$1, USB4.2
PA24/USBDM5: IC5.22, U$113.P$1, USB5.2
PA24/USBDM6: IC6.22, U$132.P$1, USB6.2
PA24/USBDM7: IC7.22, U$151.P$1, USB7.2
PA24/USBDM8: IC8.22, U$170.P$1, USB8.2
PA24/USBDM9: IC9.22, U$189.P$1, USB9.2
PA24/USBDM10: IC10.22, U$208.P$1, USB10.2
PA24/USBDM11: IC11.22, U$227.P$1, USB11.2
PA24/USBDM12: IC12.22, U$246.P$1, USB12.2
PA24/USBDM13: IC13.22, U$265.P$1, USB13.2
PA24/USBDM14: IC14.22, U$284.P$1, USB14.2
PA24/USBDM15: IC15.22, U$303.P$1, USB15.2
PA24/USBDM16: IC16.22, U$322.P$1, USB16.2
PA24/USBDM17: IC17.22, U$341.P$1, USB17.2
PA24/USBDM18: IC18.22, U$360.P$1, USB18.2
PA24/USBDM19: IC19.22, U$379.P$1, USB19.2
PA24/USBDM20: IC20.22, U$398.P$1, USB20.2
PA24/USBDM21: IC21.22, U$417.P$1, USB21.2
PA24/USBDM22: IC22.22, U$436.P$1, USB22.2
PA24/USBDM23: IC23.22, U$455.P$1, USB23.2
PA24/USBDM24: IC24.22, U$474.P$1, USB24.2
PA24/USBDM25: IC25.22, U$493.P$1, USB25.2
PA24/USBDM26: IC26.22, U$512.P$1, USB26.2
PA24/USBDM27: IC27.22, U$531.P$1, USB27.2
PA24/USBDM28: IC28.22, U$550.P$1, USB28.2
PA24/USBDM29: IC29.22, U$569.P$1, USB29.2
PA24/USBDM30: IC30.22, U$588.P$1, USB30.2
PA24/USBDM31: IC31.22, U$607.P$1, USB31.2
PA24/USBDM32: IC32.22, U$626.P$1, USB32.2
PA24/USBDM33: IC33.22, U$645.P$1, USB33.2
PA24/USBDM34: IC34.22, U$664.P$1, USB34.2
PA25: IC13.25, U$262.P$1
PA25/USBDP: IC.23, U$10.P$1, USB.3
PA25/USBDP1: IC1.23, U$25.P$1, USB1.3
PA25/USBDP2: IC2.23, U$57.P$1, USB2.3
PA25/USBDP3: IC3.23, U$76.P$1, USB3.3
PA25/USBDP4: IC4.23, U$95.P$1, USB4.3
PA25/USBDP5: IC5.23, U$114.P$1, USB5.3
PA25/USBDP6: IC6.23, U$133.P$1, USB6.3
PA25/USBDP7: IC7.23, U$152.P$1, USB7.3
PA25/USBDP8: IC8.23, U$171.P$1, USB8.3
PA25/USBDP9: IC9.23, U$190.P$1, USB9.3
PA25/USBDP10: IC10.23, U$209.P$1, USB10.3
PA25/USBDP11: IC11.23, U$228.P$1, USB11.3
PA25/USBDP12: IC12.23, U$247.P$1, USB12.3
PA25/USBDP13: IC13.23, U$266.P$1, USB13.3
PA25/USBDP14: IC14.23, U$285.P$1, USB14.3
PA25/USBDP15: IC15.23, U$304.P$1, USB15.3
PA25/USBDP16: IC16.23, U$323.P$1, USB16.3
PA25/USBDP17: IC17.23, U$342.P$1, USB17.3
PA25/USBDP18: IC18.23, U$361.P$1, USB18.3
PA25/USBDP19: IC19.23, U$380.P$1, USB19.3
PA25/USBDP20: IC20.23, U$399.P$1, USB20.3
PA25/USBDP21: IC21.23, U$418.P$1, USB21.3
PA25/USBDP22: IC22.23, U$437.P$1, USB22.3
PA25/USBDP23: IC23.23, U$456.P$1, USB23.3
PA25/USBDP24: IC24.23, U$475.P$1, USB24.3
PA25/USBDP25: IC25.23, U$494.P$1, USB25.3
PA25/USBDP26: IC26.23, U$513.P$1, USB26.3
PA25/USBDP27: IC27.23, U$532.P$1, USB27.3
PA25/USBDP28: IC28.23, U$551.P$1, USB28.3
PA25/USBDP29: IC29.23, U$570.P$1, USB29.3
PA25/USBDP30: IC30.23, U$589.P$1, USB30.3
PA25/USBDP31: IC31.23, U$608.P$1, USB31.3
PA25/USBDP32: IC32.23, U$627.P$1, USB32.3
PA25/USBDP33: IC33.23, U$646.P$1, USB33.3
PA25/USBDP34: IC34.23, U$665.P$1, USB34.3
PA26: IC13.27, U$263.P$1
PA27: IC.25, U$7.P$1
PA28: IC.27, U$48.P$1
PA29: IC14.25, U$281.P$1
PA30: IC14.27, U$282.P$1
PA30/SWCLK: IC.31, R4.1, U$46.P$1
PA30/SWCLK1: IC1.31, R6.1, U$19.P$1
PA30/SWCLK2: IC2.31, R13.1, U$50.P$1
PA30/SWCLK3: IC3.31, R18.1, U$70.P$1
PA30/SWCLK4: IC4.31, R23.1, U$89.P$1
PA30/SWCLK5: IC5.31, R28.1, U$108.P$1
PA30/SWCLK6: IC6.31, R33.1, U$127.P$1
PA30/SWCLK7: IC7.31, R38.1, U$146.P$1
PA30/SWCLK8: IC8.31, R43.1, U$165.P$1
PA30/SWCLK9: IC9.31, R48.1, U$184.P$1
PA30/SWCLK10: IC10.31, R53.1, U$203.P$1
PA30/SWCLK11: IC11.31, R58.1, U$222.P$1
PA30/SWCLK12: IC12.31, R63.1, U$241.P$1
PA30/SWCLK13: IC13.31, R68.1, U$260.P$1
PA30/SWCLK14: IC14.31, R73.1, U$279.P$1
PA30/SWCLK15: IC15.31, R78.1, U$298.P$1
PA30/SWCLK16: IC16.31, R83.1, U$317.P$1
PA30/SWCLK17: IC17.31, R88.1, U$336.P$1
PA30/SWCLK18: IC18.31, R93.1, U$355.P$1
PA30/SWCLK19: IC19.31, R98.1, U$374.P$1
PA30/SWCLK20: IC20.31, R103.1, U$393.P$1
PA30/SWCLK21: IC21.31, R108.1, U$412.P$1
PA30/SWCLK22: IC22.31, R113.1, U$431.P$1
PA30/SWCLK23: IC23.31, R118.1, U$450.P$1
PA30/SWCLK24: IC24.31, R123.1, U$469.P$1
PA30/SWCLK25: IC25.31, R128.1, U$488.P$1
PA30/SWCLK26: IC26.31, R133.1, U$507.P$1
PA30/SWCLK27: IC27.31, R138.1, U$526.P$1
PA30/SWCLK28: IC28.31, R143.1, U$545.P$1
PA30/SWCLK29: IC29.31, R148.1, U$564.P$1
PA30/SWCLK30: IC30.31, R153.1, U$583.P$1
PA30/SWCLK31: IC31.31, R158.1, U$602.P$1
PA30/SWCLK32: IC32.31, R163.1, U$621.P$1
PA30/SWCLK33: IC33.31, R168.1, U$640.P$1
PA30/SWCLK34: IC34.31, R173.1, U$659.P$1
PA31: IC15.25, U$300.P$1
PA31/SWDIO: IC.32, U$47.P$1
PA31/SWDIO1: IC1.32, U$20.P$1
PA31/SWDIO2: IC2.32, U$51.P$1
PA31/SWDIO3: IC3.32, U$71.P$1
PA31/SWDIO4: IC4.32, U$90.P$1
PA31/SWDIO5: IC5.32, U$109.P$1
PA31/SWDIO6: IC6.32, U$128.P$1
PA31/SWDIO7: IC7.32, U$147.P$1
PA31/SWDIO8: IC8.32, U$166.P$1
PA31/SWDIO9: IC9.32, U$185.P$1
PA31/SWDIO10: IC10.32, U$204.P$1
PA31/SWDIO11: IC11.32, U$223.P$1
PA31/SWDIO12: IC12.32, U$242.P$1
PA31/SWDIO13: IC13.32, U$261.P$1
PA31/SWDIO14: IC14.32, U$280.P$1
PA31/SWDIO15: IC15.32, U$299.P$1
PA31/SWDIO16: IC16.32, U$318.P$1
PA31/SWDIO17: IC17.32, U$337.P$1
PA31/SWDIO18: IC18.32, U$356.P$1
PA31/SWDIO19: IC19.32, U$375.P$1
PA31/SWDIO20: IC20.32, U$394.P$1
PA31/SWDIO21: IC21.32, U$413.P$1
PA31/SWDIO22: IC22.32, U$432.P$1
PA31/SWDIO23: IC23.32, U$451.P$1
PA31/SWDIO24: IC24.32, U$470.P$1
PA31/SWDIO25: IC25.32, U$489.P$1
PA31/SWDIO26: IC26.32, U$508.P$1
PA31/SWDIO27: IC27.32, U$527.P$1
PA31/SWDIO28: IC28.32, U$546.P$1
PA31/SWDIO29: IC29.32, U$565.P$1
PA31/SWDIO30: IC30.32, U$584.P$1
PA31/SWDIO31: IC31.32, U$603.P$1
PA31/SWDIO32: IC32.32, U$622.P$1
PA31/SWDIO33: IC33.32, U$641.P$1
PA31/SWDIO34: IC34.32, U$660.P$1
PA32: IC15.27, U$301.P$1
PA33: IC16.25, U$319.P$1
PA34: IC16.27, U$320.P$1
PA35: IC17.25, U$338.P$1
PA36: IC17.27, U$339.P$1
PA37: IC18.25, U$357.P$1
PA38: IC18.27, U$358.P$1
PA39: IC19.25, U$376.P$1
PA40: IC19.27, U$377.P$1
PA41: IC20.25, U$395.P$1
PA42: IC20.27, U$396.P$1
PA43: IC21.25, U$414.P$1
PA44: IC21.27, U$415.P$1
PA45: IC22.25, U$433.P$1
PA46: IC22.27, U$434.P$1
PA47: IC23.25, U$452.P$1
PA48: IC23.27, U$453.P$1
PA49: IC24.25, U$471.P$1
PA50: IC24.27, U$472.P$1
PA51: IC25.25, U$490.P$1
PA52: IC25.27, U$491.P$1
PA53: IC26.25, U$509.P$1
PA54: IC26.27, U$510.P$1
PA55: IC27.25, U$528.P$1
PA56: IC27.27, U$529.P$1
PA57: IC28.25, U$547.P$1
PA58: IC28.27, U$548.P$1
PA59: IC29.25, U$566.P$1
PA60: IC29.27, U$567.P$1
PA61: IC30.25, U$585.P$1
PA62: IC30.27, U$586.P$1
PA63: IC31.25, U$604.P$1
PA64: IC31.27, U$605.P$1
PA65: IC32.25, U$623.P$1
PA66: IC32.27, U$624.P$1
PA67: IC33.25, U$642.P$1
PA68: IC33.27, U$643.P$1
PA69: IC34.25, U$661.P$1
PA70: IC34.27, U$662.P$1
RESET: C1.1, IC.26, R1.2, R2.1, U$45.P$1
RESET1: C18.1, IC1.26, R3.2, R5.1, U$18.P$1
RESET2: C47.1, IC2.26, R11.2, R12.1, U$49.P$1
RESET3: C70.1, IC3.26, R16.2, R17.1, U$69.P$1
RESET4: C93.1, IC4.26, R21.2, R22.1, U$88.P$1
RESET5: C116.1, IC5.26, R26.2, R27.1, U$107.P$1
RESET6: C139.1, IC6.26, R31.2, R32.1, U$126.P$1
RESET7: C162.1, IC7.26, R36.2, R37.1, U$145.P$1
RESET8: C185.1, IC8.26, R41.2, R42.1, U$164.P$1
RESET9: C208.1, IC9.26, R46.2, R47.1, U$183.P$1
RESET10: C231.1, IC10.26, R51.2, R52.1, U$202.P$1
RESET11: C254.1, IC11.26, R56.2, R57.1, U$221.P$1
RESET12: C277.1, IC12.26, R61.2, R62.1, U$240.P$1
RESET13: C300.1, IC13.26, R66.2, R67.1, U$259.P$1
RESET14: C323.1, IC14.26, R71.2, R72.1, U$278.P$1
RESET15: C346.1, IC15.26, R76.2, R77.1, U$297.P$1
RESET16: C369.1, IC16.26, R81.2, R82.1, U$316.P$1
RESET17: C392.1, IC17.26, R86.2, R87.1, U$335.P$1
RESET18: C415.1, IC18.26, R91.2, R92.1, U$354.P$1
RESET19: C438.1, IC19.26, R96.2, R97.1, U$373.P$1
RESET20: C461.1, IC20.26, R101.2, R102.1, U$392.P$1
RESET21: C484.1, IC21.26, R106.2, R107.1, U$411.P$1
RESET22: C507.1, IC22.26, R111.2, R112.1, U$430.P$1
RESET23: C530.1, IC23.26, R116.2, R117.1, U$449.P$1
RESET24: C553.1, IC24.26, R121.2, R122.1, U$468.P$1
RESET25: C576.1, IC25.26, R126.2, R127.1, U$487.P$1
RESET26: C599.1, IC26.26, R131.2, R132.1, U$506.P$1
RESET27: C622.1, IC27.26, R136.2, R137.1, U$525.P$1
RESET28: C645.1, IC28.26, R141.2, R142.1, U$544.P$1
RESET29: C668.1, IC29.26, R146.2, R147.1, U$563.P$1
RESET30: C691.1, IC30.26, R151.2, R152.1, U$582.P$1
RESET31: C714.1, IC31.26, R156.2, R157.1, U$601.P$1
RESET32: C737.1, IC32.26, R161.2, R162.1, U$620.P$1
RESET33: C760.1, IC33.26, R166.2, R167.1, U$639.P$1
RESET34: C783.1, IC34.26, R171.2, R172.1, U$658.P$1
RFN: C11.1, IC.13
RFN1: C39.1, IC1.13
RFN2: C62.1, IC2.13
RFN3: C85.1, IC3.13
RFN4: C108.1, IC4.13
RFN5: C131.1, IC5.13
RFN6: C154.1, IC6.13
RFN7: C177.1, IC7.13
RFN8: C200.1, IC8.13
RFN9: C223.1, IC9.13
RFN10: C246.1, IC10.13
RFN11: C269.1, IC11.13
RFN12: C292.1, IC12.13
RFN13: C315.1, IC13.13
RFN14: C338.1, IC14.13
RFN15: C361.1, IC15.13
RFN16: C384.1, IC16.13
RFN17: C407.1, IC17.13
RFN18: C430.1, IC18.13
RFN19: C453.1, IC19.13
RFN20: C476.1, IC20.13
RFN21: C499.1, IC21.13
RFN22: C522.1, IC22.13
RFN23: C545.1, IC23.13
RFN24: C568.1, IC24.13
RFN25: C591.1, IC25.13
RFN26: C614.1, IC26.13
RFN27: C637.1, IC27.13
RFN28: C660.1, IC28.13
RFN29: C683.1, IC29.13
RFN30: C706.1, IC30.13
RFN31: C729.1, IC31.13
RFN32: C752.1, IC32.13
RFN33: C775.1, IC33.13
RFN34: C798.1, IC34.13
RFP: C12.1, IC.12
RFP1: C40.1, IC1.12
RFP2: C63.1, IC2.12
RFP3: C86.1, IC3.12
RFP4: C109.1, IC4.12
RFP5: C132.1, IC5.12
RFP6: C155.1, IC6.12
RFP7: C178.1, IC7.12
RFP8: C201.1, IC8.12
RFP9: C224.1, IC9.12
RFP10: C247.1, IC10.12
RFP11: C270.1, IC11.12
RFP12: C293.1, IC12.12
RFP13: C316.1, IC13.12
RFP14: C339.1, IC14.12
RFP15: C362.1, IC15.12
RFP16: C385.1, IC16.12
RFP17: C408.1, IC17.12
RFP18: C431.1, IC18.12
RFP19: C454.1, IC19.12
RFP20: C477.1, IC20.12
RFP21: C500.1, IC21.12
RFP22: C523.1, IC22.12
RFP23: C546.1, IC23.12
RFP24: C569.1, IC24.12
RFP25: C592.1, IC25.12
RFP26: C615.1, IC26.12
RFP27: C638.1, IC27.12
RFP28: C661.1, IC28.12
RFP29: C684.1, IC29.12
RFP30: C707.1, IC30.12
RFP31: C730.1, IC31.12
RFP32: C753.1, IC32.12
RFP33: C776.1, IC33.12
RFP34: C799.1, IC34.12
VDDANA: C8.1, C22.2, IC.4, L6.2
VDDANA1: C26.1, C35.2, IC1.4, L1.2
VDDANA2: C53.1, C58.2, IC2.4, L2.2
VDDANA3: C76.1, C81.2, IC3.4, L3.2
VDDANA4: C99.1, C104.2, IC4.4, L4.2
VDDANA5: C122.1, C127.2, IC5.4, L5.2
VDDANA6: C145.1, C150.2, IC6.4, L7.2
VDDANA7: C168.1, C173.2, IC7.4, L8.2
VDDANA8: C191.1, C196.2, IC8.4, L9.2
VDDANA9: C214.1, C219.2, IC9.4, L10.2
VDDANA10: C237.1, C242.2, IC10.4, L11.2
VDDANA11: C260.1, C265.2, IC11.4, L12.2
VDDANA12: C283.1, C288.2, IC12.4, L13.2
VDDANA13: C306.1, C311.2, IC13.4, L14.2
VDDANA14: C329.1, C334.2, IC14.4, L15.2
VDDANA15: C352.1, C357.2, IC15.4, L16.2
VDDANA16: C375.1, C380.2, IC16.4, L17.2
VDDANA17: C398.1, C403.2, IC17.4, L18.2
VDDANA18: C421.1, C426.2, IC18.4, L19.2
VDDANA19: C444.1, C449.2, IC19.4, L20.2
VDDANA20: C467.1, C472.2, IC20.4, L21.2
VDDANA21: C490.1, C495.2, IC21.4, L22.2
VDDANA22: C513.1, C518.2, IC22.4, L23.2
VDDANA23: C536.1, C541.2, IC23.4, L24.2
VDDANA24: C559.1, C564.2, IC24.4, L25.2
VDDANA25: C582.1, C587.2, IC25.4, L26.2
VDDANA26: C605.1, C610.2, IC26.4, L27.2
VDDANA27: C628.1, C633.2, IC27.4, L28.2
VDDANA28: C651.1, C656.2, IC28.4, L29.2
VDDANA29: C674.1, C679.2, IC29.4, L30.2
VDDANA30: C697.1, C702.2, IC30.4, L31.2
VDDANA31: C720.1, C725.2, IC31.4, L32.2
VDDANA32: C743.1, C748.2, IC32.4, L33.2
VDDANA33: C766.1, C771.2, IC33.4, L34.2
VDDANA34: C789.1, C794.2, IC34.4, L35.2
VDDCORE: C9.1, IC.29
VDDCORE1: C27.1, IC1.29
VDDCORE2: C54.1, IC2.29
VDDCORE3: C77.1, IC3.29
VDDCORE4: C100.1, IC4.29
VDDCORE5: C123.1, IC5.29
VDDCORE6: C146.1, IC6.29
VDDCORE7: C169.1, IC7.29
VDDCORE8: C192.1, IC8.29
VDDCORE9: C215.1, IC9.29
VDDCORE10: C238.1, IC10.29
VDDCORE11: C261.1, IC11.29
VDDCORE12: C284.1, IC12.29
VDDCORE13: C307.1, IC13.29
VDDCORE14: C330.1, IC14.29
VDDCORE15: C353.1, IC15.29
VDDCORE16: C376.1, IC16.29
VDDCORE17: C399.1, IC17.29
VDDCORE18: C422.1, IC18.29
VDDCORE19: C445.1, IC19.29
VDDCORE20: C468.1, IC20.29
VDDCORE21: C491.1, IC21.29
VDDCORE22: C514.1, IC22.29
VDDCORE23: C537.1, IC23.29
VDDCORE24: C560.1, IC24.29
VDDCORE25: C583.1, IC25.29
VDDCORE26: C606.1, IC26.29
VDDCORE27: C629.1, IC27.29
VDDCORE28: C652.1, IC28.29
VDDCORE29: C675.1, IC29.29
VDDCORE30: C698.1, IC30.29
VDDCORE31: C721.1, IC31.29
VDDCORE32: C744.1, IC32.29
VDDCORE33: C767.1, IC33.29
VDDCORE34: C790.1, IC34.29
VIN: C6.1, C7.1, LDO_VREG.VIN, U$1.P$1, USB.1
VIN1: C23.1, C24.1, LDO_VREG1.VIN, U$3.P$1, USB1.1
VIN2: C50.1, C51.1, LDO_VREG2.VIN, U$26.P$1, USB2.1
VIN3: C73.1, C74.1, LDO_VREG3.VIN, U$58.P$1, USB3.1
VIN4: C96.1, C97.1, LDO_VREG4.VIN, U$77.P$1, USB4.1
VIN5: C119.1, C120.1, LDO_VREG5.VIN, U$96.P$1, USB5.1
VIN6: C142.1, C143.1, LDO_VREG6.VIN, U$115.P$1, USB6.1
VIN7: C165.1, C166.1, LDO_VREG7.VIN, U$134.P$1, USB7.1
VIN8: C188.1, C189.1, LDO_VREG8.VIN, U$153.P$1, USB8.1
VIN9: C211.1, C212.1, LDO_VREG9.VIN, U$172.P$1, USB9.1
VIN10: C234.1, C235.1, LDO_VREG10.VIN, U$191.P$1, USB10.1
VIN11: C257.1, C258.1, LDO_VREG11.VIN, U$210.P$1, USB11.1
VIN12: C280.1, C281.1, LDO_VREG12.VIN, U$229.P$1, USB12.1
VIN13: C303.1, C304.1, LDO_VREG13.VIN, U$248.P$1, USB13.1
VIN14: C326.1, C327.1, LDO_VREG14.VIN, U$267.P$1, USB14.1
VIN15: C349.1, C350.1, LDO_VREG15.VIN, U$286.P$1, USB15.1
VIN16: C372.1, C373.1, LDO_VREG16.VIN, U$305.P$1, USB16.1
VIN17: C395.1, C396.1, LDO_VREG17.VIN, U$324.P$1, USB17.1
VIN18: C418.1, C419.1, LDO_VREG18.VIN, U$343.P$1, USB18.1
VIN19: C441.1, C442.1, LDO_VREG19.VIN, U$362.P$1, USB19.1
VIN20: C464.1, C465.1, LDO_VREG20.VIN, U$381.P$1, USB20.1
VIN21: C487.1, C488.1, LDO_VREG21.VIN, U$400.P$1, USB21.1
VIN22: C510.1, C511.1, LDO_VREG22.VIN, U$419.P$1, USB22.1
VIN23: C533.1, C534.1, LDO_VREG23.VIN, U$438.P$1, USB23.1
VIN24: C556.1, C557.1, LDO_VREG24.VIN, U$457.P$1, USB24.1
VIN25: C579.1, C580.1, LDO_VREG25.VIN, U$476.P$1, USB25.1
VIN26: C602.1, C603.1, LDO_VREG26.VIN, U$495.P$1, USB26.1
VIN27: C625.1, C626.1, LDO_VREG27.VIN, U$514.P$1, USB27.1
VIN28: C648.1, C649.1, LDO_VREG28.VIN, U$533.P$1, USB28.1
VIN29: C671.1, C672.1, LDO_VREG29.VIN, U$552.P$1, USB29.1
VIN30: C694.1, C695.1, LDO_VREG30.VIN, U$571.P$1, USB30.1
VIN31: C717.1, C718.1, LDO_VREG31.VIN, U$590.P$1, USB31.1
VIN32: C740.1, C741.1, LDO_VREG32.VIN, U$609.P$1, USB32.1
VIN33: C763.1, C764.1, LDO_VREG33.VIN, U$628.P$1, USB33.1
VIN34: C786.1, C787.1, LDO_VREG34.VIN, U$647.P$1, USB34.1
XTALIN: C14.2, IC.2, XOSCRF.1
XTALIN1: C42.2, IC1.2, XOSCRF1.1
XTALIN2: C65.2, IC2.2, XOSCRF2.1
XTALIN3: C88.2, IC3.2, XOSCRF3.1
XTALIN4: C111.2, IC4.2, XOSCRF4.1
XTALIN5: C134.2, IC5.2, XOSCRF5.1
XTALIN6: C157.2, IC6.2, XOSCRF6.1
XTALIN7: C180.2, IC7.2, XOSCRF7.1
XTALIN8: C203.2, IC8.2, XOSCRF8.1
XTALIN9: C226.2, IC9.2, XOSCRF9.1
XTALIN10: C249.2, IC10.2, XOSCRF10.1
XTALIN11: C272.2, IC11.2, XOSCRF11.1
XTALIN12: C295.2, IC12.2, XOSCRF12.1
XTALIN13: C318.2, IC13.2, XOSCRF13.1
XTALIN14: C341.2, IC14.2, XOSCRF14.1
XTALIN15: C364.2, IC15.2, XOSCRF15.1
XTALIN16: C387.2, IC16.2, XOSCRF16.1
XTALIN17: C410.2, IC17.2, XOSCRF17.1
XTALIN18: C433.2, IC18.2, XOSCRF18.1
XTALIN19: C456.2, IC19.2, XOSCRF19.1
XTALIN20: C479.2, IC20.2, XOSCRF20.1
XTALIN21: C502.2, IC21.2, XOSCRF21.1
XTALIN22: C525.2, IC22.2, XOSCRF22.1
XTALIN23: C548.2, IC23.2, XOSCRF23.1
XTALIN24: C571.2, IC24.2, XOSCRF24.1
XTALIN25: C594.2, IC25.2, XOSCRF25.1
XTALIN26: C617.2, IC26.2, XOSCRF26.1
XTALIN27: C640.2, IC27.2, XOSCRF27.1
XTALIN28: C663.2, IC28.2, XOSCRF28.1
XTALIN29: C686.2, IC29.2, XOSCRF29.1
XTALIN30: C709.2, IC30.2, XOSCRF30.1
XTALIN31: C732.2, IC31.2, XOSCRF31.1
XTALIN32: C755.2, IC32.2, XOSCRF32.1
XTALIN33: C778.2, IC33.2, XOSCRF33.1
XTALIN34: C801.2, IC34.2, XOSCRF34.1
XTALOUT: C15.1, IC.1, XOSCRF.3
XTALOUT1: C43.1, IC1.1, XOSCRF1.3
XTALOUT2: C66.1, IC2.1, XOSCRF2.3
XTALOUT3: C89.1, IC3.1, XOSCRF3.3
XTALOUT4: C112.1, IC4.1, XOSCRF4.3
XTALOUT5: C135.1, IC5.1, XOSCRF5.3
XTALOUT6: C158.1, IC6.1, XOSCRF6.3
XTALOUT7: C181.1, IC7.1, XOSCRF7.3
XTALOUT8: C204.1, IC8.1, XOSCRF8.3
XTALOUT9: C227.1, IC9.1, XOSCRF9.3
XTALOUT10: C250.1, IC10.1, XOSCRF10.3
XTALOUT11: C273.1, IC11.1, XOSCRF11.3
XTALOUT12: C296.1, IC12.1, XOSCRF12.3
XTALOUT13: C319.1, IC13.1, XOSCRF13.3
XTALOUT14: C342.1, IC14.1, XOSCRF14.3
XTALOUT15: C365.1, IC15.1, XOSCRF15.3
XTALOUT16: C388.1, IC16.1, XOSCRF16.3
XTALOUT17: C411.1, IC17.1, XOSCRF17.3
XTALOUT18: C434.1, IC18.1, XOSCRF18.3
XTALOUT19: C457.1, IC19.1, XOSCRF19.3
XTALOUT20: C480.1, IC20.1, XOSCRF20.3
XTALOUT21: C503.1, IC21.1, XOSCRF21.3
XTALOUT22: C526.1, IC22.1, XOSCRF22.3
XTALOUT23: C549.1, IC23.1, XOSCRF23.3
XTALOUT24: C572.1, IC24.1, XOSCRF24.3
XTALOUT25: C595.1, IC25.1, XOSCRF25.3
XTALOUT26: C618.1, IC26.1, XOSCRF26.3
XTALOUT27: C641.1, IC27.1, XOSCRF27.3
XTALOUT28: C664.1, IC28.1, XOSCRF28.3
XTALOUT29: C687.1, IC29.1, XOSCRF29.3
XTALOUT30: C710.1, IC30.1, XOSCRF30.3
XTALOUT31: C733.1, IC31.1, XOSCRF31.3
XTALOUT32: C756.1, IC32.1, XOSCRF32.3
XTALOUT33: C779.1, IC33.1, XOSCRF33.3
XTALOUT34: C802.1, IC34.1, XOSCRF34.3
