femtoduino/femto-beacon/Eagle_Files/FemtoBeacon_r2.0.0/femtoBeacon_dongle_r2.0.3_PANELIZED.brd

## EAGLE design Eagle_Files/FemtoBeacon_r2.0.0/femtoBeacon_dongle_r2.0.3_PANELIZED.brd (2018-01-04)

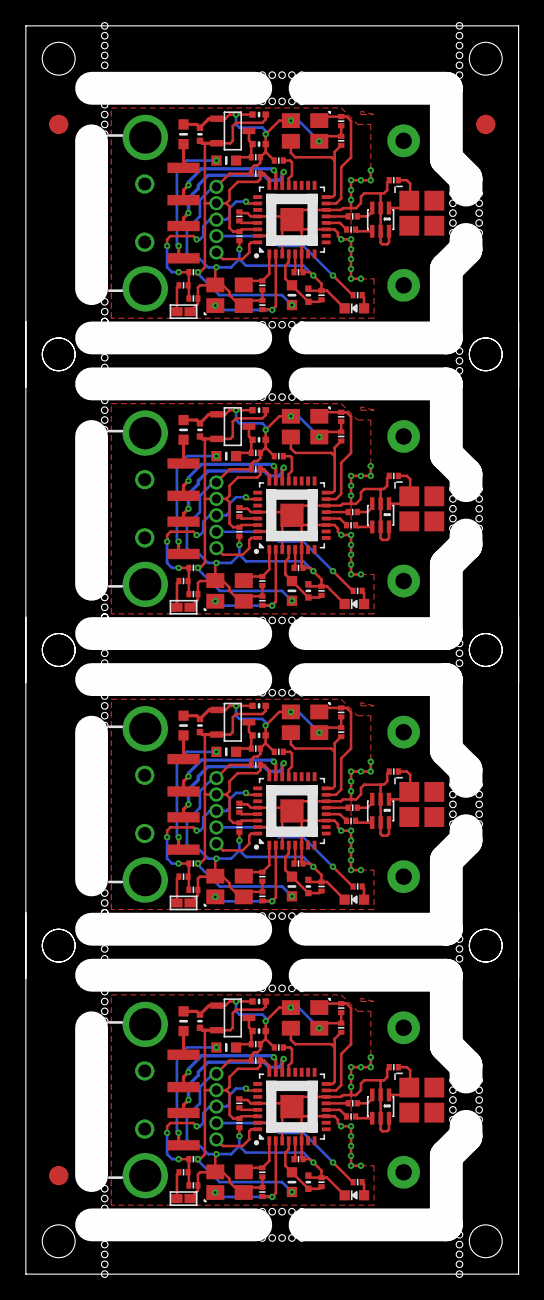
[picture p68: board femtoBeacon_dongle_r2.0.3_PANELIZED.brd from above]

Board: 4 copper layers, 38.1 x 96.5 mm, 143 parts (0 on the bottom side), 100 nets.

Parts:
BTN, BTN1, BTN2, BTN3: DNP; SPST_SMD
C1, C2, C8, C9, C10, C16, C17, C18, C19, C27, C28, C29, C37, C38, C39, C40, C46, C47, C48, C56, C57, C58, C59, C65, C66, C67, C75, C76: 0.1uF; PART
C3, C4, C32, C33, C51, C52, C70, C71: 10pF; PART
C5, C6, C34, C35, C53, C54, C72, C73: 2.2uF; _0402MP
C7, C36, C55, C74: 0.47uF; PART
C11, C12, C20, C23, C41, C42, C60, C61: 22pF, C0G, 5%; PART
C13, C24, C43, C62: DNP; PART
C14, C15, C25, C26, C44, C45, C63, C64: 9pF; PART
C21, C22, C30, C31, C49, C50, C68, C69: 10uF; _0402MP
CN1, CN2, CN3, CN4: USB_A-SMT
FB1, FB2, FB3, FB4, FB5, FB6, FB7, FB8: _0603MP
FID1, FID2, FID3: FIDUCIAL; FIDUCIAL_1MM
L1, L2, L3, L6: 10uH; _0603MP
LDO_VREG, LDO_VREG1, LDO_VREG2, LDO_VREG3: MCP1700T-3302E/TT
LED, LED1, LED2, LED3: BLUE; CHIPLED_0603_NOOUTLINE
R1, R3, R4, R6, R7, R9, R10, R12: 330; PART
R2, R5, R8, R11: 10K; PART
U$1, U$4, U$9, U$14: 1X5_ROUND
U$2, U$7, U$11, U$12: JOHANSON_2450BM15A0015E; 0805_BALUN
U$3, U$8, U$13, U$76: ATSAMR21E18A-MUT; QFN32
U$5, U$6, U$10, U$15: 0479480001
XOSC, XOSC1, XOSC2, XOSC3: 12MHz; TSX-3225
XOSCRF, XOSCRF1, XOSCRF2, XOSCRF3: 16MHz; TSX-3225

Connections:
3.3V: C5.1, C10.1, C16.1, C21.2, L6.1, LDO_VREG.VOUT, R2.2, U$1.P$2, U$76.24, U$76.30
3.3V1: C19.1, C27.1, C30.2, C34.1, L1.1, LDO_VREG1.VOUT, R5.2, U$3.24, U$3.30, U$4.P$2
3.3V2: C40.1, C46.1, C49.2, C53.1, L2.1, LDO_VREG2.VOUT, R8.2, U$8.24, U$8.30, U$9.P$2
3.3V3: C59.1, C65.1, C68.2, C72.1, L3.1, LDO_VREG3.VOUT, R11.2, U$13.24, U$13.30, U$14.P$2
ANT_OUT: C13.1, U$6.ANT, U$12.1
ANT_OUT1: C24.1, U$2.1, U$5.ANT
ANT_OUT2: C43.1, U$7.1, U$10.ANT
ANT_OUT3: C62.1, U$11.1, U$15.ANT
AVDD: C17.1, U$76.5
AVDD1: C28.1, U$3.5
AVDD2: C47.1, U$8.5
AVDD3: C66.1, U$13.5
DVDD: C2.1, U$76.21
DVDD1: C29.1, U$3.21
DVDD2: C48.1, U$8.21
DVDD3: C67.1, U$13.21
GND: BTN.2, C1.2, C2.2, C3.1, C4.2, C5.2, C6.2, C7.2, C8.2, C9.2, C10.2, C13.2, C14.1, C15.2, C16.2, C17.2, C21.1, C22.1, FB1.2, LDO_VREG.GND, LED.C, U$1.P$1, U$12.2, U$12.5, U$12.6, U$76.3, U$76.6, U$76.11, U$76.14, U$76.28, U$76.33, XOSC.2, XOSC.4, XOSCRF.2, XOSCRF.4
GND1: BTN1.2, C18.2, C19.2, C24.2, C25.1, C26.2, C27.2, C28.2, C29.2, C30.1, C31.1, C32.1, C33.2, C34.2, C35.2, C36.2, C37.2, C38.2, FB3.2, LDO_VREG1.GND, LED1.C, U$2.2, U$2.5, U$2.6, U$3.3, U$3.6, U$3.11, U$3.14, U$3.28, U$3.33, U$4.P$1, XOSC1.2, XOSC1.4, XOSCRF1.2, XOSCRF1.4
GND2: BTN2.2, C39.2, C40.2, C43.2, C44.1, C45.2, C46.2, C47.2, C48.2, C49.1, C50.1, C51.1, C52.2, C53.2, C54.2, C55.2, C56.2, C57.2, FB5.2, LDO_VREG2.GND, LED2.C, U$7.2, U$7.5, U$7.6, U$8.3, U$8.6, U$8.11, U$8.14, U$8.28, U$8.33, U$9.P$1, XOSC2.2, XOSC2.4, XOSCRF2.2, XOSCRF2.4
GND3: BTN3.2, C58.2, C59.2, C62.2, C63.1, C64.2, C65.2, C66.2, C67.2, C68.1, C69.1, C70.1, C71.2, C72.2, C73.2, C74.2, C75.2, C76.2, FB7.2, LDO_VREG3.GND, LED3.C, U$11.2, U$11.5, U$11.6, U$13.3, U$13.6, U$13.11, U$13.14, U$13.28, U$13.33, U$14.P$1, XOSC3.2, XOSC3.4, XOSCRF3.2, XOSCRF3.4
unnamed: C11.2, U$12.3
unnamed: BTN1.1, R3.1
unnamed: C12.2, U$12.4
unnamed: CN1.VBUS, FB2.1
unnamed: CN1.GND, FB1.1
unnamed: LED1.A, R6.2
unnamed: C20.2, U$2.3
unnamed: C23.2, U$2.4
unnamed: LED.A, R4.2
unnamed: CN2.GND, FB3.1
unnamed: CN2.VBUS, FB4.1
unnamed: BTN2.1, R7.1
unnamed: LED2.A, R9.2
unnamed: C41.2, U$7.3
unnamed: C42.2, U$7.4
unnamed: CN3.GND, FB5.1
unnamed: CN3.VBUS, FB6.1
unnamed: BTN.1, R1.1
unnamed: BTN3.1, R10.1
unnamed: LED3.A, R12.2
unnamed: C60.2, U$11.3
unnamed: C61.2, U$11.4
unnamed: CN4.GND, FB7.1
unnamed: CN4.VBUS, FB8.1
PA14/XIN_MC/RX: C3.2, U$76.15, XOSC.1
PA14/XIN_MC/RX1: C32.2, U$3.15, XOSC1.1
PA14/XIN_MC/RX2: C51.2, U$8.15, XOSC2.1
PA14/XIN_MC/RX3: C70.2, U$13.15, XOSC3.1
PA15/XOUT_MC/TX: C4.1, U$76.16, XOSC.3
PA15/XOUT_MC/TX1: C33.1, U$3.16, XOSC1.3
PA15/XOUT_MC/TX2: C52.1, U$8.16, XOSC2.3
PA15/XOUT_MC/TX3: C71.1, U$13.16, XOSC3.3
PA24/USBDM: CN1.D-, U$76.22
PA24/USBDM1: CN2.D-, U$3.22
PA24/USBDM2: CN3.D-, U$8.22
PA24/USBDM3: CN4.D-, U$13.22
PA25/USBDP: CN1.D+, U$76.23
PA25/USBDP1: CN2.D+, U$3.23
PA25/USBDP2: CN3.D+, U$8.23
PA25/USBDP3: CN4.D+, U$13.23
PA30/SWCLK: R4.1, U$1.P$4, U$76.31
PA30/SWCLK1: R6.1, U$3.31, U$4.P$4
PA30/SWCLK2: R9.1, U$8.31, U$9.P$4
PA30/SWCLK3: R12.1, U$13.31, U$14.P$4
PA31/SWDIO: U$1.P$5, U$76.32
PA31/SWDIO1: U$3.32, U$4.P$5
PA31/SWDIO2: U$8.32, U$9.P$5
PA31/SWDIO3: U$13.32, U$14.P$5
RESET: C1.1, R1.2, R2.1, U$1.P$3, U$76.26
RESET1: C18.1, R3.2, R5.1, U$3.26, U$4.P$3
RESET2: C39.1, R7.2, R8.1, U$8.26, U$9.P$3
RESET3: C58.1, R10.2, R11.1, U$13.26, U$14.P$3
RFN: C11.1, U$76.13
RFN1: C20.1, U$3.13
RFN2: C41.1, U$8.13
RFN3: C60.1, U$13.13
RFP: C12.1, U$76.12
RFP1: C23.1, U$3.12
RFP2: C42.1, U$8.12
RFP3: C61.1, U$13.12
VDDANA: C8.1, C22.2, L6.2, U$76.4
VDDANA1: C31.2, C37.1, L1.2, U$3.4
VDDANA2: C50.2, C56.1, L2.2, U$8.4
VDDANA3: C69.2, C75.1, L3.2, U$13.4
VDDCORE: C9.1, U$76.29
VDDCORE1: C38.1, U$3.29
VDDCORE2: C57.1, U$8.29
VDDCORE3: C76.1, U$13.29
VIN: C6.1, C7.1, FB2.2, LDO_VREG.VIN
VIN1: C35.1, C36.1, FB4.2, LDO_VREG1.VIN
VIN2: C54.1, C55.1, FB6.2, LDO_VREG2.VIN
VIN3: C73.1, C74.1, FB8.2, LDO_VREG3.VIN
XTALIN: C14.2, U$76.2, XOSCRF.1
XTALIN1: C25.2, U$3.2, XOSCRF1.1
XTALIN2: C44.2, U$8.2, XOSCRF2.1
XTALIN3: C63.2, U$13.2, XOSCRF3.1
XTALOUT: C15.1, U$76.1, XOSCRF.3
XTALOUT1: C26.1, U$3.1, XOSCRF1.3
XTALOUT2: C45.1, U$8.1, XOSCRF2.3
XTALOUT3: C64.1, U$13.1, XOSCRF3.3
