femtoduino/femto-beacon/Eagle_Files/FemtoBeacon_r2.0.0/femtoBeacon_dongle_r2.0.1_PANELIZED.brd

## EAGLE design Eagle_Files/FemtoBeacon_r2.0.0/femtoBeacon_dongle_r2.0.1_PANELIZED.brd (2018-01-04)

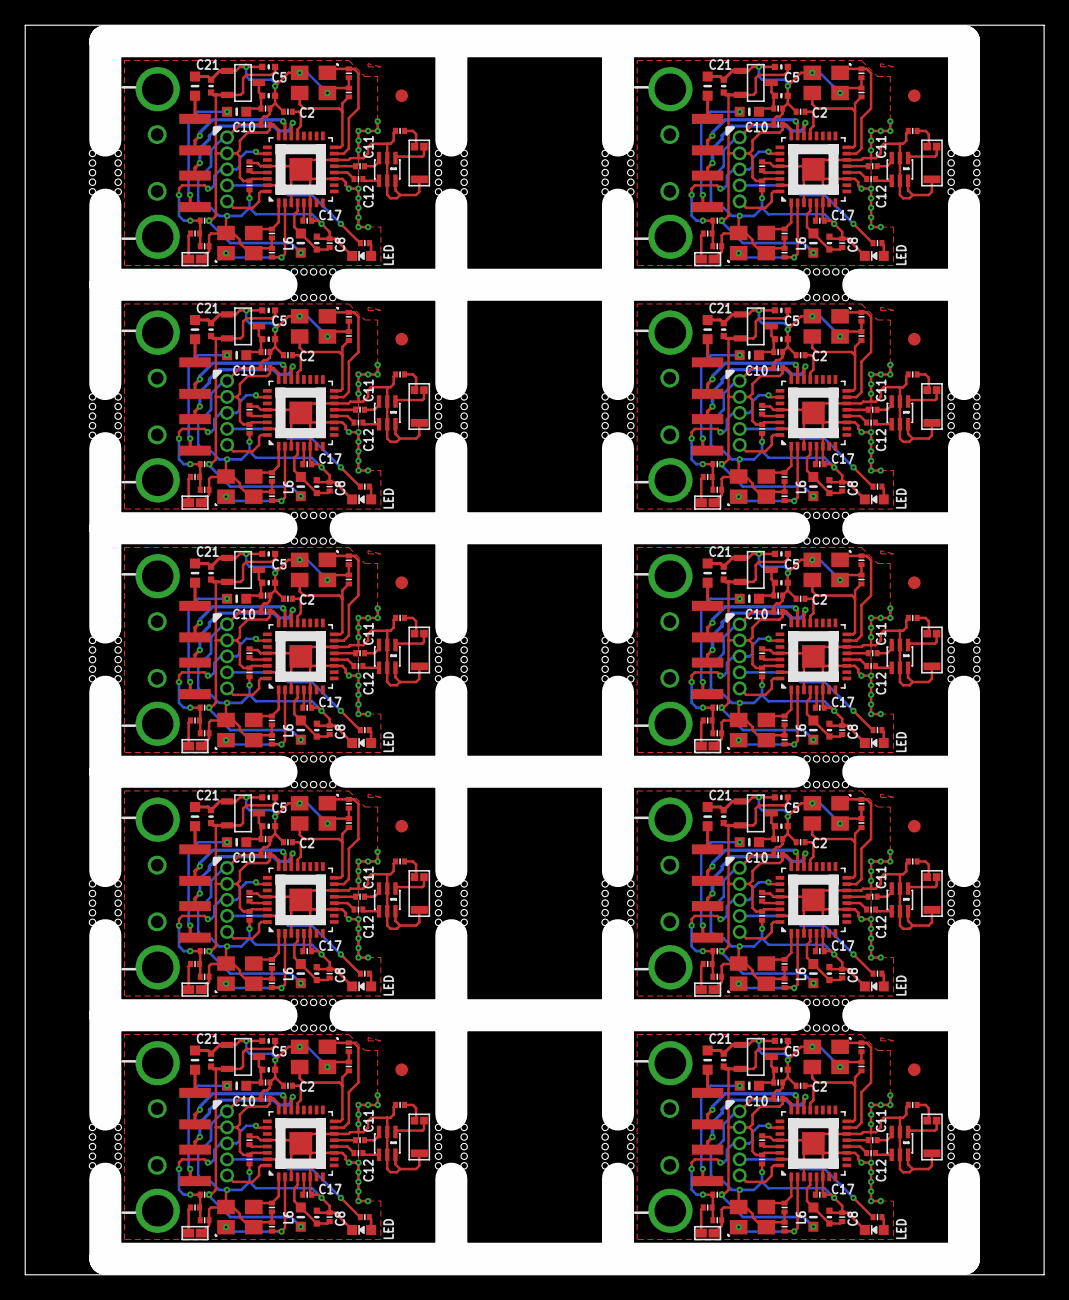
[picture p69: board femtoBeacon_dongle_r2.0.1_PANELIZED.brd from above]

Board: 2 copper layers, 80.8 x 99.1 mm, 360 parts (0 on the bottom side), 260 nets.

Parts:
ANT1, ANT2, ANT3, ANT4, ANT5, ANT6, ANT7, ANT8, ANT9, ANT10: PULSE_ANT_2.4GHZ; ANT_BAR
BTN, BTN1, BTN2, BTN3, BTN4, BTN5, BTN6, BTN7, BTN8, BTN9: DNP; SPST_SMD
C1, C2, C8, C9, C10, C16, C17, C18, C19, C27, C28, C29, C37, C38, C39, C40, C46, C47, C48, C56, C57, C58, C59, C65, C66, C67, C75, C76, C77, C78, C84, C85, C86, C94, C95, C96, C97, C103, C104, C105, C113, C114, C115, C116, C122, C123, C124, C132, C133, C134, C135, C141, C142, C143, C151, C152, C153, C154, C160, C161, C162, C170, C171, C172, C173, C179, C180, C181, C189, C190: 0.1uF; PART
C3, C4, C32, C33, C51, C52, C70, C71, C89, C90, C108, C109, C127, C128, C146, C147, C165, C166, C184, C185: 10pF; PART
C5, C6, C34, C35, C53, C54, C72, C73, C91, C92, C110, C111, C129, C130, C148, C149, C167, C168, C186, C187: 2.2uF; _0402MP
C7, C36, C55, C74, C93, C112, C131, C150, C169, C188: 0.47uF; PART
C11, C12, C20, C23, C41, C42, C60, C61, C79, C80, C98, C99, C117, C118, C136, C137, C155, C156, C174, C175: 22pF, C0G, 5%; PART
C13, C24, C43, C62, C81, C100, C119, C138, C157, C176: DNP; PART
C14, C15, C25, C26, C44, C45, C63, C64, C82, C83, C101, C102, C120, C121, C139, C140, C158, C159, C177, C178: 9pF; PART
C21, C22, C30, C31, C49, C50, C68, C69, C87, C88, C106, C107, C125, C126, C144, C145, C163, C164, C182, C183: 10uF; _0402MP
CN1, CN2, CN3, CN4, CN5, CN6, CN7, CN8, CN9, CN10: USB_A-SMT
FB1, FB2, FB3, FB4, FB5, FB6, FB7, FB8, FB9, FB10, FB11, FB12, FB13, FB14, FB15, FB16, FB17, FB18, FB19, FB20: _0603MP
FID1, FID2, FID3, FID4, FID5, FID6, FID7, FID8, FID9, FID10: FIDUCIAL; FIDUCIAL_1MM
L1, L2, L3, L4, L5, L6, L7, L8, L9, L10: 10uH; _0603MP
LDO_VREG, LDO_VREG1, LDO_VREG2, LDO_VREG3, LDO_VREG4, LDO_VREG5, LDO_VREG6, LDO_VREG7, LDO_VREG8, LDO_VREG9: MCP1700T-3302E/TT
LED, LED1, LED2, LED3, LED4, LED5, LED6, LED7, LED8, LED9: BLUE; CHIPLED_0603_NOOUTLINE
R1, R3, R4, R6, R7, R9, R10, R12, R13, R15, R16, R18, R19, R21, R22, R24, R25, R27, R28, R30: 330; PART
R2, R5, R8, R11, R14, R17, R20, R23, R26, R29: 10K; PART
U$1, U$4, U$7, U$10, U$14, U$17, U$20, U$23, U$26, U$29: 1X5_ROUND
U$2, U$5, U$8, U$11, U$12, U$15, U$18, U$21, U$24, U$27: JOHANSON_2450BM15A0015E; 0805_BALUN
U$3, U$6, U$9, U$13, U$16, U$19, U$22, U$25, U$28, U$76: ATSAMR21E18A-MUT; QFN32
XOSC, XOSC1, XOSC2, XOSC3, XOSC4, XOSC5, XOSC6, XOSC7, XOSC8, XOSC9: 12MHz; TSX-3225
XOSCRF, XOSCRF1, XOSCRF2, XOSCRF3, XOSCRF4, XOSCRF5, XOSCRF6, XOSCRF7, XOSCRF8, XOSCRF9: 16MHz; TSX-3225

Connections:
3.3V: C5.1, C10.1, C16.1, C21.2, L6.1, LDO_VREG.VOUT, R2.2, U$1.P$2, U$76.24, U$76.30
3.3V1: C19.1, C27.1, C30.2, C34.1, L1.1, LDO_VREG1.VOUT, R5.2, U$3.24, U$3.30, U$4.P$2
3.3V2: C40.1, C46.1, C49.2, C53.1, L2.1, LDO_VREG2.VOUT, R8.2, U$6.24, U$6.30, U$7.P$2
3.3V3: C59.1, C65.1, C68.2, C72.1, L3.1, LDO_VREG3.VOUT, R11.2, U$9.24, U$9.30, U$10.P$2
3.3V4: C78.1, C84.1, C87.2, C91.1, L4.1, LDO_VREG4.VOUT, R14.2, U$13.24, U$13.30, U$14.P$2
3.3V5: C97.1, C103.1, C106.2, C110.1, L5.1, LDO_VREG5.VOUT, R17.2, U$16.24, U$16.30, U$17.P$2
3.3V6: C116.1, C122.1, C125.2, C129.1, L7.1, LDO_VREG6.VOUT, R20.2, U$19.24, U$19.30, U$20.P$2
3.3V7: C135.1, C141.1, C144.2, C148.1, L8.1, LDO_VREG7.VOUT, R23.2, U$22.24, U$22.30, U$23.P$2
3.3V8: C154.1, C160.1, C163.2, C167.1, L9.1, LDO_VREG8.VOUT, R26.2, U$25.24, U$25.30, U$26.P$2
3.3V9: C173.1, C179.1, C182.2, C186.1, L10.1, LDO_VREG9.VOUT, R29.2, U$28.24, U$28.30, U$29.P$2
ANT_OUT: ANT1.1, U$12.1
ANT_OUT1: ANT2.1, U$2.1
ANT_OUT2: ANT3.1, U$5.1
ANT_OUT3: ANT4.1, U$8.1
ANT_OUT4: ANT5.1, U$11.1
ANT_OUT5: ANT6.1, U$15.1
ANT_OUT6: ANT7.1, U$18.1
ANT_OUT7: ANT8.1, U$21.1
ANT_OUT8: ANT9.1, U$24.1
ANT_OUT9: ANT10.1, U$27.1
AVDD: C17.1, U$76.5
AVDD1: C28.1, U$3.5
AVDD2: C47.1, U$6.5
AVDD3: C66.1, U$9.5
AVDD4: C85.1, U$13.5
AVDD5: C104.1, U$16.5
AVDD6: C123.1, U$19.5
AVDD7: C142.1, U$22.5
AVDD8: C161.1, U$25.5
AVDD9: C180.1, U$28.5
DVDD: C2.1, U$76.21
DVDD1: C29.1, U$3.21
DVDD2: C48.1, U$6.21
DVDD3: C67.1, U$9.21
DVDD4: C86.1, U$13.21
DVDD5: C105.1, U$16.21
DVDD6: C124.1, U$19.21
DVDD7: C143.1, U$22.21
DVDD8: C162.1, U$25.21
DVDD9: C181.1, U$28.21
GND: ANT1.3, BTN.2, C1.2, C2.2, C3.1, C4.2, C5.2, C6.2, C7.2, C8.2, C9.2, C10.2, C13.2, C14.1, C15.2, C16.2, C17.2, C21.1, C22.1, FB1.2, LDO_VREG.GND, LED.C, U$1.P$1, U$12.2, U$12.5, U$12.6, U$76.3, U$76.6, U$76.11, U$76.14, U$76.28, U$76.33, XOSC.2, XOSC.4, XOSCRF.2, XOSCRF.4
GND1: ANT2.3, BTN1.2, C18.2, C19.2, C24.2, C25.1, C26.2, C27.2, C28.2, C29.2, C30.1, C31.1, C32.1, C33.2, C34.2, C35.2, C36.2, C37.2, C38.2, FB3.2, LDO_VREG1.GND, LED1.C, U$2.2, U$2.5, U$2.6, U$3.3, U$3.6, U$3.11, U$3.14, U$3.28, U$3.33, U$4.P$1, XOSC1.2, XOSC1.4, XOSCRF1.2, XOSCRF1.4
GND2: ANT3.3, BTN2.2, C39.2, C40.2, C43.2, C44.1, C45.2, C46.2, C47.2, C48.2, C49.1, C50.1, C51.1, C52.2, C53.2, C54.2, C55.2, C56.2, C57.2, FB5.2, LDO_VREG2.GND, LED2.C, U$5.2, U$5.5, U$5.6, U$6.3, U$6.6, U$6.11, U$6.14, U$6.28, U$6.33, U$7.P$1, XOSC2.2, XOSC2.4, XOSCRF2.2, XOSCRF2.4
GND3: ANT4.3, BTN3.2, C58.2, C59.2, C62.2, C63.1, C64.2, C65.2, C66.2, C67.2, C68.1, C69.1, C70.1, C71.2, C72.2, C73.2, C74.2, C75.2, C76.2, FB7.2, LDO_VREG3.GND, LED3.C, U$8.2, U$8.5, U$8.6, U$9.3, U$9.6, U$9.11, U$9.14, U$9.28, U$9.33, U$10.P$1, XOSC3.2, XOSC3.4, XOSCRF3.2, XOSCRF3.4
GND4: ANT5.3, BTN4.2, C77.2, C78.2, C81.2, C82.1, C83.2, C84.2, C85.2, C86.2, C87.1, C88.1, C89.1, C90.2, C91.2, C92.2, C93.2, C94.2, C95.2, FB9.2, LDO_VREG4.GND, LED4.C, U$11.2, U$11.5, U$11.6, U$13.3, U$13.6, U$13.11, U$13.14, U$13.28, U$13.33, U$14.P$1, XOSC4.2, XOSC4.4, XOSCRF4.2, XOSCRF4.4
GND5: ANT6.3, BTN5.2, C96.2, C97.2, C100.2, C101.1, C102.2, C103.2, C104.2, C105.2, C106.1, C107.1, C108.1, C109.2, C110.2, C111.2, C112.2, C113.2, C114.2, FB11.2, LDO_VREG5.GND, LED5.C, U$15.2, U$15.5, U$15.6, U$16.3, U$16.6, U$16.11, U$16.14, U$16.28, U$16.33, U$17.P$1, XOSC5.2, XOSC5.4, XOSCRF5.2, XOSCRF5.4
GND6: ANT7.3, BTN6.2, C115.2, C116.2, C119.2, C120.1, C121.2, C122.2, C123.2, C124.2, C125.1, C126.1, C127.1, C128.2, C129.2, C130.2, C131.2, C132.2, C133.2, FB13.2, LDO_VREG6.GND, LED6.C, U$18.2, U$18.5, U$18.6, U$19.3, U$19.6, U$19.11, U$19.14, U$19.28, U$19.33, U$20.P$1, XOSC6.2, XOSC6.4, XOSCRF6.2, XOSCRF6.4
GND7: ANT8.3, BTN7.2, C134.2, C135.2, C138.2, C139.1, C140.2, C141.2, C142.2, C143.2, C144.1, C145.1, C146.1, C147.2, C148.2, C149.2, C150.2, C151.2, C152.2, FB15.2, LDO_VREG7.GND, LED7.C, U$21.2, U$21.5, U$21.6, U$22.3, U$22.6, U$22.11, U$22.14, U$22.28, U$22.33, U$23.P$1, XOSC7.2, XOSC7.4, XOSCRF7.2, XOSCRF7.4
GND8: ANT9.3, BTN8.2, C153.2, C154.2, C157.2, C158.1, C159.2, C160.2, C161.2, C162.2, C163.1, C164.1, C165.1, C166.2, C167.2, C168.2, C169.2, C170.2, C171.2, FB17.2, LDO_VREG8.GND, LED8.C, U$24.2, U$24.5, U$24.6, U$25.3, U$25.6, U$25.11, U$25.14, U$25.28, U$25.33, U$26.P$1, XOSC8.2, XOSC8.4, XOSCRF8.2, XOSCRF8.4
GND9: ANT10.3, BTN9.2, C172.2, C173.2, C176.2, C177.1, C178.2, C179.2, C180.2, C181.2, C182.1, C183.1, C184.1, C185.2, C186.2, C187.2, C188.2, C189.2, C190.2, FB19.2, LDO_VREG9.GND, LED9.C, U$27.2, U$27.5, U$27.6, U$28.3, U$28.6, U$28.11, U$28.14, U$28.28, U$28.33, U$29.P$1, XOSC9.2, XOSC9.4, XOSCRF9.2, XOSCRF9.4
unnamed: C11.2, U$12.3
unnamed: ANT1.2, C13.1
unnamed: C12.2, U$12.4
unnamed: CN1.VBUS, FB2.1
unnamed: CN1.GND, FB1.1
unnamed: BTN1.1, R3.1
unnamed: LED1.A, R6.2
unnamed: C20.2, U$2.3
unnamed: LED.A, R4.2
unnamed: C23.2, U$2.4
unnamed: ANT2.2, C24.1
unnamed: CN2.GND, FB3.1
unnamed: CN2.VBUS, FB4.1
unnamed: BTN2.1, R7.1
unnamed: LED2.A, R9.2
unnamed: C41.2, U$5.3
unnamed: C42.2, U$5.4
unnamed: BTN.1, R1.1
unnamed: ANT3.2, C43.1
unnamed: CN3.GND, FB5.1
unnamed: CN3.VBUS, FB6.1
unnamed: BTN3.1, R10.1
unnamed: LED3.A, R12.2
unnamed: C60.2, U$8.3
unnamed: C61.2, U$8.4
unnamed: ANT4.2, C62.1
unnamed: CN4.GND, FB7.1
unnamed: CN4.VBUS, FB8.1
unnamed: BTN4.1, R13.1
unnamed: LED4.A, R15.2
unnamed: C79.2, U$11.3
unnamed: C80.2, U$11.4
unnamed: ANT5.2, C81.1
unnamed: CN5.GND, FB9.1
unnamed: CN5.VBUS, FB10.1
unnamed: BTN5.1, R16.1
unnamed: LED5.A, R18.2
unnamed: C98.2, U$15.3
unnamed: C99.2, U$15.4
unnamed: ANT6.2, C100.1
unnamed: CN6.GND, FB11.1
unnamed: CN6.VBUS, FB12.1
unnamed: BTN6.1, R19.1
unnamed: LED6.A, R21.2
unnamed: C117.2, U$18.3
unnamed: C118.2, U$18.4
unnamed: ANT7.2, C119.1
unnamed: CN7.GND, FB13.1
unnamed: CN7.VBUS, FB14.1
unnamed: BTN7.1, R22.1
unnamed: LED7.A, R24.2
unnamed: C136.2, U$21.3
unnamed: C137.2, U$21.4
unnamed: ANT8.2, C138.1
unnamed: CN8.GND, FB15.1
unnamed: CN8.VBUS, FB16.1
unnamed: BTN8.1, R25.1
unnamed: LED8.A, R27.2
unnamed: C155.2, U$24.3
unnamed: C156.2, U$24.4
unnamed: ANT9.2, C157.1
unnamed: CN9.GND, FB17.1
unnamed: CN9.VBUS, FB18.1
unnamed: BTN9.1, R28.1
unnamed: LED9.A, R30.2
unnamed: C174.2, U$27.3
unnamed: C175.2, U$27.4
unnamed: ANT10.2, C176.1
unnamed: CN10.GND, FB19.1
unnamed: CN10.VBUS, FB20.1
PA14/XIN_MC/RX: C3.2, U$76.15, XOSC.1
PA14/XIN_MC/RX1: C32.2, U$3.15, XOSC1.1
PA14/XIN_MC/RX2: C51.2, U$6.15, XOSC2.1
PA14/XIN_MC/RX3: C70.2, U$9.15, XOSC3.1
PA14/XIN_MC/RX4: C89.2, U$13.15, XOSC4.1
PA14/XIN_MC/RX5: C108.2, U$16.15, XOSC5.1
PA14/XIN_MC/RX6: C127.2, U$19.15, XOSC6.1
PA14/XIN_MC/RX7: C146.2, U$22.15, XOSC7.1
PA14/XIN_MC/RX8: C165.2, U$25.15, XOSC8.1
PA14/XIN_MC/RX9: C184.2, U$28.15, XOSC9.1
PA15/XOUT_MC/TX: C4.1, U$76.16, XOSC.3
PA15/XOUT_MC/TX1: C33.1, U$3.16, XOSC1.3
PA15/XOUT_MC/TX2: C52.1, U$6.16, XOSC2.3
PA15/XOUT_MC/TX3: C71.1, U$9.16, XOSC3.3
PA15/XOUT_MC/TX4: C90.1, U$13.16, XOSC4.3
PA15/XOUT_MC/TX5: C109.1, U$16.16, XOSC5.3
PA15/XOUT_MC/TX6: C128.1, U$19.16, XOSC6.3
PA15/XOUT_MC/TX7: C147.1, U$22.16, XOSC7.3
PA15/XOUT_MC/TX8: C166.1, U$25.16, XOSC8.3
PA15/XOUT_MC/TX9: C185.1, U$28.16, XOSC9.3
PA24/USBDM: CN1.D-, U$76.22
PA24/USBDM1: CN2.D-, U$3.22
PA24/USBDM2: CN3.D-, U$6.22
PA24/USBDM3: CN4.D-, U$9.22
PA24/USBDM4: CN5.D-, U$13.22
PA24/USBDM5: CN6.D-, U$16.22
PA24/USBDM6: CN7.D-, U$19.22
PA24/USBDM7: CN8.D-, U$22.22
PA24/USBDM8: CN9.D-, U$25.22
PA24/USBDM9: CN10.D-, U$28.22
PA25/USBDP: CN1.D+, U$76.23
PA25/USBDP1: CN2.D+, U$3.23
PA25/USBDP2: CN3.D+, U$6.23
PA25/USBDP3: CN4.D+, U$9.23
PA25/USBDP4: CN5.D+, U$13.23
PA25/USBDP5: CN6.D+, U$16.23
PA25/USBDP6: CN7.D+, U$19.23
PA25/USBDP7: CN8.D+, U$22.23
PA25/USBDP8: CN9.D+, U$25.23
PA25/USBDP9: CN10.D+, U$28.23
PA30/SWCLK: R4.1, U$1.P$4, U$76.31
PA30/SWCLK1: R6.1, U$3.31, U$4.P$4
PA30/SWCLK2: R9.1, U$6.31, U$7.P$4
PA30/SWCLK3: R12.1, U$9.31, U$10.P$4
PA30/SWCLK4: R15.1, U$13.31, U$14.P$4
PA30/SWCLK5: R18.1, U$16.31, U$17.P$4
PA30/SWCLK6: R21.1, U$19.31, U$20.P$4
PA30/SWCLK7: R24.1, U$22.31, U$23.P$4
PA30/SWCLK8: R27.1, U$25.31, U$26.P$4
PA30/SWCLK9: R30.1, U$28.31, U$29.P$4
PA31/SWDIO: U$1.P$5, U$76.32
PA31/SWDIO1: U$3.32, U$4.P$5
PA31/SWDIO2: U$6.32, U$7.P$5
PA31/SWDIO3: U$9.32, U$10.P$5
PA31/SWDIO4: U$13.32, U$14.P$5
PA31/SWDIO5: U$16.32, U$17.P$5
PA31/SWDIO6: U$19.32, U$20.P$5
PA31/SWDIO7: U$22.32, U$23.P$5
PA31/SWDIO8: U$25.32, U$26.P$5
PA31/SWDIO9: U$28.32, U$29.P$5
RESET: C1.1, R1.2, R2.1, U$1.P$3, U$76.26
RESET1: C18.1, R3.2, R5.1, U$3.26, U$4.P$3
RESET2: C39.1, R7.2, R8.1, U$6.26, U$7.P$3
RESET3: C58.1, R10.2, R11.1, U$9.26, U$10.P$3
RESET4: C77.1, R13.2, R14.1, U$13.26, U$14.P$3
RESET5: C96.1, R16.2, R17.1, U$16.26, U$17.P$3
RESET6: C115.1, R19.2, R20.1, U$19.26, U$20.P$3
RESET7: C134.1, R22.2, R23.1, U$22.26, U$23.P$3
RESET8: C153.1, R25.2, R26.1, U$25.26, U$26.P$3
RESET9: C172.1, R28.2, R29.1, U$28.26, U$29.P$3
RFN: C11.1, U$76.13
RFN1: C20.1, U$3.13
RFN2: C41.1, U$6.13
RFN3: C60.1, U$9.13
RFN4: C79.1, U$13.13
RFN5: C98.1, U$16.13
RFN6: C117.1, U$19.13
RFN7: C136.1, U$22.13
RFN8: C155.1, U$25.13
RFN9: C174.1, U$28.13
RFP: C12.1, U$76.12
RFP1: C23.1, U$3.12
RFP2: C42.1, U$6.12
RFP3: C61.1, U$9.12
RFP4: C80.1, U$13.12
RFP5: C99.1, U$16.12
RFP6: C118.1, U$19.12
RFP7: C137.1, U$22.12
RFP8: C156.1, U$25.12
RFP9: C175.1, U$28.12
VDDANA: C8.1, C22.2, L6.2, U$76.4
VDDANA1: C31.2, C37.1, L1.2, U$3.4
VDDANA2: C50.2, C56.1, L2.2, U$6.4
VDDANA3: C69.2, C75.1, L3.2, U$9.4
VDDANA4: C88.2, C94.1, L4.2, U$13.4
VDDANA5: C107.2, C113.1, L5.2, U$16.4
VDDANA6: C126.2, C132.1, L7.2, U$19.4
VDDANA7: C145.2, C151.1, L8.2, U$22.4
VDDANA8: C164.2, C170.1, L9.2, U$25.4
VDDANA9: C183.2, C189.1, L10.2, U$28.4
VDDCORE: C9.1, U$76.29
VDDCORE1: C38.1, U$3.29
VDDCORE2: C57.1, U$6.29
VDDCORE3: C76.1, U$9.29
VDDCORE4: C95.1, U$13.29
VDDCORE5: C114.1, U$16.29
VDDCORE6: C133.1, U$19.29
VDDCORE7: C152.1, U$22.29
VDDCORE8: C171.1, U$25.29
VDDCORE9: C190.1, U$28.29
VIN: C6.1, C7.1, FB2.2, LDO_VREG.VIN
VIN1: C35.1, C36.1, FB4.2, LDO_VREG1.VIN
VIN2: C54.1, C55.1, FB6.2, LDO_VREG2.VIN
VIN3: C73.1, C74.1, FB8.2, LDO_VREG3.VIN
VIN4: C92.1, C93.1, FB10.2, LDO_VREG4.VIN
VIN5: C111.1, C112.1, FB12.2, LDO_VREG5.VIN
VIN6: C130.1, C131.1, FB14.2, LDO_VREG6.VIN
VIN7: C149.1, C150.1, FB16.2, LDO_VREG7.VIN
VIN8: C168.1, C169.1, FB18.2, LDO_VREG8.VIN
VIN9: C187.1, C188.1, FB20.2, LDO_VREG9.VIN
XTALIN: C14.2, U$76.2, XOSCRF.1
XTALIN1: C25.2, U$3.2, XOSCRF1.1
XTALIN2: C44.2, U$6.2, XOSCRF2.1
XTALIN3: C63.2, U$9.2, XOSCRF3.1
XTALIN4: C82.2, U$13.2, XOSCRF4.1
XTALIN5: C101.2, U$16.2, XOSCRF5.1
XTALIN6: C120.2, U$19.2, XOSCRF6.1
XTALIN7: C139.2, U$22.2, XOSCRF7.1
XTALIN8: C158.2, U$25.2, XOSCRF8.1
XTALIN9: C177.2, U$28.2, XOSCRF9.1
XTALOUT: C15.1, U$76.1, XOSCRF.3
XTALOUT1: C26.1, U$3.1, XOSCRF1.3
XTALOUT2: C45.1, U$6.1, XOSCRF2.3
XTALOUT3: C64.1, U$9.1, XOSCRF3.3
XTALOUT4: C83.1, U$13.1, XOSCRF4.3
XTALOUT5: C102.1, U$16.1, XOSCRF5.3
XTALOUT6: C121.1, U$19.1, XOSCRF6.3
XTALOUT7: C140.1, U$22.1, XOSCRF7.3
XTALOUT8: C159.1, U$25.1, XOSCRF8.3
XTALOUT9: C178.1, U$28.1, XOSCRF9.3
