femtoduino/femto-beacon/Eagle_Files/FemtoBeacon_r2.0.0/FemtoBeacon_dongle_r2.0.6_RGB_PANELIZED/femtoBeacon_dongle_r2.0.6_RGB_PANELIZED.brd

## EAGLE design Eagle_Files/FemtoBeacon_r2.0.0/FemtoBeacon_dongle_r2.0.6_RGB_PANELIZED/femtoBeacon_dongle_r2.0.6_RGB_PANELIZED.brd (2018-01-04)

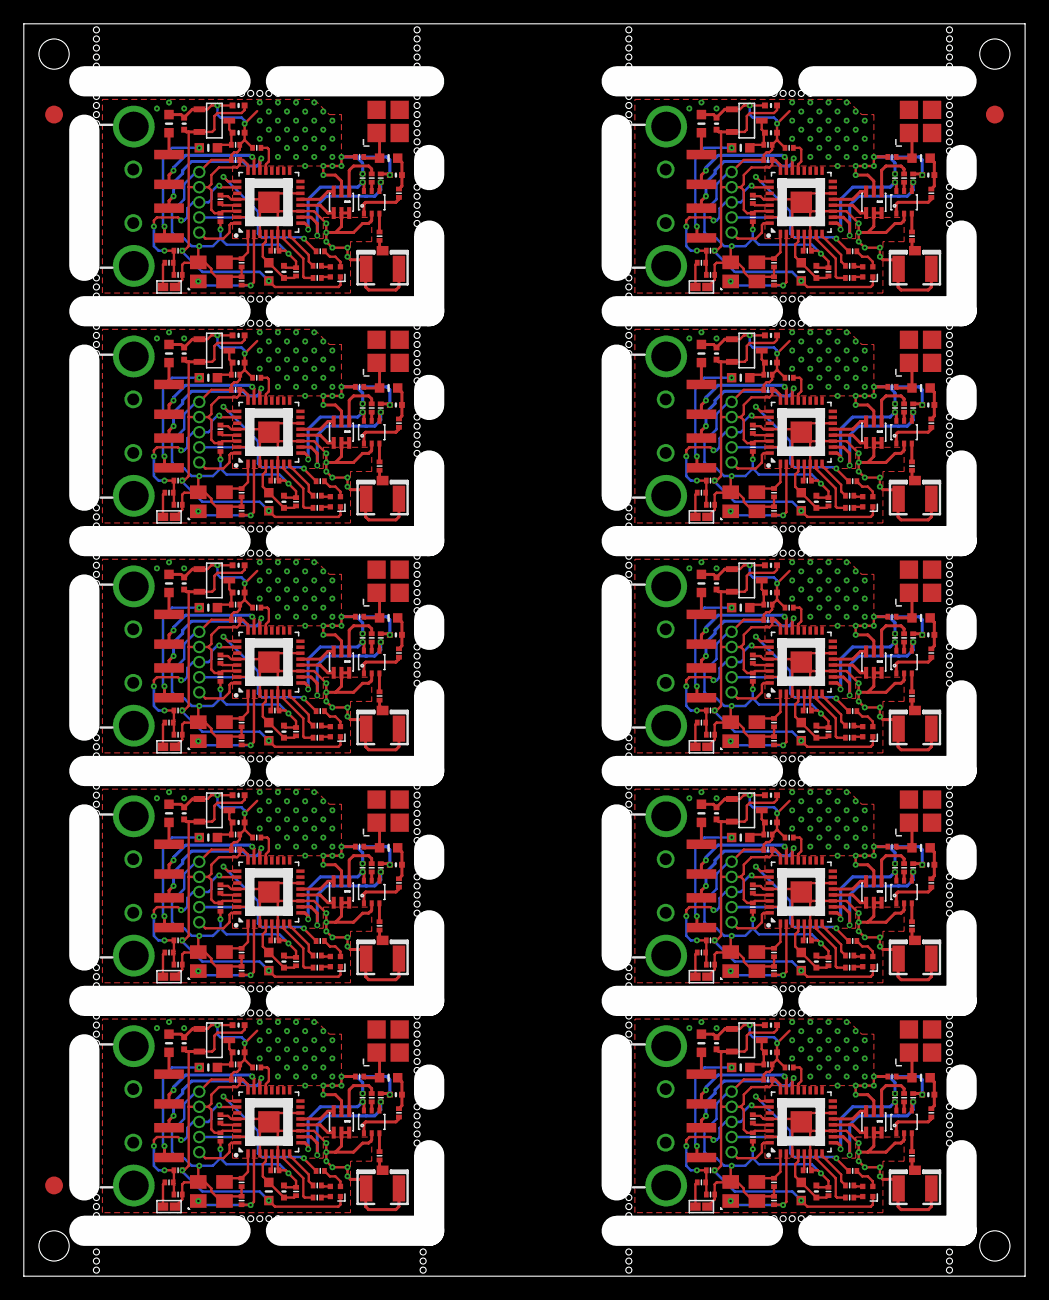
[picture p70: board femtoBeacon_dongle_r2.0.6_RGB_PANELIZED.brd from above]

Board: 2 copper layers, 84.1 x 105.2 mm, 413 parts (0 on the bottom side), 340 nets.

Parts:
ASWITCH, ASWITCH1, ASWITCH2, ASWITCH3, ASWITCH4, ASWITCH5, ASWITCH6, ASWITCH7, ASWITCH8, ASWITCH9: AS222-92LF
BTN, BTN1, BTN2, BTN3, BTN4, BTN5, BTN6, BTN7, BTN8, BTN9: DNP; SPST_SMD
C1, C2, C3, C4, C8, C9, C10, C16, C17, C27, C28, C29, C35, C36, C43, C44, C48, C49, C50, C56, C57, C64, C65, C69, C70, C71, C77, C78, C85, C86, C90, C91, C92, C98, C99, C106, C107, C111, C112, C113, C119, C120, C127, C128, C132, C133, C134, C140, C141, C148, C149, C153, C154, C155, C161, C162, C169, C170, C174, C175, C176, C182, C183, C190, C191, C195, C196, C197, C203, C204: 0.1uF; PART
C5, C6, C32, C33, C53, C54, C74, C75, C95, C96, C116, C117, C137, C138, C158, C159, C179, C180, C200, C201: 2.2uF; _0402MP
C7, C34, C55, C76, C97, C118, C139, C160, C181, C202: 0.47uF; PART
C11, C42, C63, C84, C105, C126, C147, C168, C189, C210: 1.2pF; _0402MP
C12, C13, C45, C66, C87, C108, C129, C150, C171, C192: DNP; PART
C14, C15, C25, C26, C46, C47, C67, C68, C88, C89, C109, C110, C130, C131, C151, C152, C172, C173, C193, C194: 9pF; PART
C18, C19, C20, C23, C24, C37, C38, C39, C40, C41, C58, C59, C60, C61, C62, C79, C80, C81, C82, C83, C100, C101, C102, C103, C104, C121, C122, C123, C124, C125, C142, C143, C144, C145, C146, C163, C164, C165, C166, C167, C184, C185, C186, C187, C188, C205, C206, C207, C208, C209: 22pF; PART
C21, C22, C30, C31, C51, C52, C72, C73, C93, C94, C114, C115, C135, C136, C156, C157, C177, C178, C198, C199: 10uF; _0402MP
CN1, CN2, CN3, CN4, CN5, CN6, CN7, CN8, CN9, CN10: USB_A-SMT
FB1, FB2, FB3, FB4, FB5, FB6, FB7, FB8, FB9, FB10, FB11, FB12, FB13, FB14, FB15, FB16, FB17, FB18, FB19, FB20: _0603MP
FID1, FID2, FID3: FIDUCIAL; FIDUCIAL_1MM
L1, L3, L5, L8, L10, L12, L14, L16, L18, L20: 1.8nH; _0603MP
L2, L4, L6, L7, L9, L11, L13, L15, L17, L19: 10uH; _0603MP
LDO_VREG, LDO_VREG1, LDO_VREG2, LDO_VREG3, LDO_VREG4, LDO_VREG5, LDO_VREG6, LDO_VREG7, LDO_VREG8, LDO_VREG9: MCP1700T-3302E/TT
R1, R3, R4, R6, R7, R8, R9, R10, R11, R13, R14, R15, R16, R18, R19, R20, R21, R23, R24, R25, R26, R28, R29, R30, R31, R33, R34, R35, R36, R38, R39, R40, R41, R43, R44, R45, R46, R48, R49, R50: 330; PART
R2, R5, R12, R17, R22, R27, R32, R37, R42, R47: 10K; PART
RGBLED, RGBLED1, RGBLED2, RGBLED3, RGBLED4, RGBLED5, RGBLED6, RGBLED7, RGBLED8, RGBLED9: LRTB_R48G
U$1, U$4, U$9, U$14, U$18, U$22, U$26, U$30, U$34, U$38: 1X5_ROUND
U$2, U$7, U$11, U$12, U$16, U$20, U$24, U$28, U$32, U$36: JOHANSON_2450BM15A0015E; 0805_BALUN
U$3, U$8, U$13, U$17, U$21, U$25, U$29, U$33, U$37, U$76: ATSAMR21E18A-MUT; QFN32
U$5, U$6, U$10, U$15, U$19, U$23, U$27, U$31, U$35, U$39: 0479480001
UFLANT, UFLANT1, UFLANT2, UFLANT3, UFLANT4, UFLANT5, UFLANT6, UFLANT7, UFLANT8, UFLANT9: uFL; U.FL
XOSCRF, XOSCRF1, XOSCRF2, XOSCRF3, XOSCRF4, XOSCRF5, XOSCRF6, XOSCRF7, XOSCRF8, XOSCRF9: 16MHz; TSX-3225

Connections:
3.3V: C5.1, C10.1, C16.1, C21.2, L6.1, LDO_VREG.VOUT, R2.2, RGBLED.1, U$1.P$2, U$76.24, U$76.30
3.3V1: C4.1, C27.1, C30.2, C32.1, L2.1, LDO_VREG1.VOUT, R5.2, RGBLED1.1, U$3.24, U$3.30, U$4.P$2
3.3V2: C44.1, C48.1, C51.2, C53.1, L4.1, LDO_VREG2.VOUT, R12.2, RGBLED2.1, U$8.24, U$8.30, U$9.P$2
3.3V3: C65.1, C69.1, C72.2, C74.1, L7.1, LDO_VREG3.VOUT, R17.2, RGBLED3.1, U$13.24, U$13.30, U$14.P$2
3.3V4: C86.1, C90.1, C93.2, C95.1, L9.1, LDO_VREG4.VOUT, R22.2, RGBLED4.1, U$17.24, U$17.30, U$18.P$2
3.3V5: C107.1, C111.1, C114.2, C116.1, L11.1, LDO_VREG5.VOUT, R27.2, RGBLED5.1, U$21.24, U$21.30, U$22.P$2
3.3V6: C128.1, C132.1, C135.2, C137.1, L13.1, LDO_VREG6.VOUT, R32.2, RGBLED6.1, U$25.24, U$25.30, U$26.P$2
3.3V7: C149.1, C153.1, C156.2, C158.1, L15.1, LDO_VREG7.VOUT, R37.2, RGBLED7.1, U$29.24, U$29.30, U$30.P$2
3.3V8: C170.1, C174.1, C177.2, C179.1, L17.1, LDO_VREG8.VOUT, R42.2, RGBLED8.1, U$33.24, U$33.30, U$34.P$2
3.3V9: C191.1, C195.1, C198.2, C200.1, L19.1, LDO_VREG9.VOUT, R47.2, RGBLED9.1, U$37.24, U$37.30, U$38.P$2
ANT_LINE: C13.1, L1.1, U$6.ANT
ANT_LINE1: C12.1, L3.1, U$5.ANT
ANT_LINE2: C45.1, L5.1, U$10.ANT
ANT_LINE3: C66.1, L8.1, U$15.ANT
ANT_LINE4: C87.1, L10.1, U$19.ANT
ANT_LINE5: C108.1, L12.1, U$23.ANT
ANT_LINE6: C129.1, L14.1, U$27.ANT
ANT_LINE7: C150.1, L16.1, U$31.ANT
ANT_LINE8: C171.1, L18.1, U$35.ANT
ANT_LINE9: C192.1, L20.1, U$39.ANT
ANT_OUT: C18.1, U$12.1
ANT_OUT1: C37.1, U$2.1
ANT_OUT2: C58.1, U$7.1
ANT_OUT3: C79.1, U$11.1
ANT_OUT4: C100.1, U$16.1
ANT_OUT5: C121.1, U$20.1
ANT_OUT6: C142.1, U$24.1
ANT_OUT7: C163.1, U$28.1
ANT_OUT8: C184.1, U$32.1
ANT_OUT9: C205.1, U$36.1
ANT_SMD: C11.1, C24.2, L1.2
ANT_SMD1: C41.2, C42.1, L3.2
ANT_SMD2: C62.2, C63.1, L5.2
ANT_SMD3: C83.2, C84.1, L8.2
ANT_SMD4: C104.2, C105.1, L10.2
ANT_SMD5: C125.2, C126.1, L12.2
ANT_SMD6: C146.2, C147.1, L14.2
ANT_SMD7: C167.2, C168.1, L16.2
ANT_SMD8: C188.2, C189.1, L18.2
ANT_SMD9: C209.2, C210.1, L20.2
ANT_UFL: C23.1, UFLANT.3
ANT_UFL1: C40.1, UFLANT1.3
ANT_UFL2: C61.1, UFLANT2.3
ANT_UFL3: C82.1, UFLANT3.3
ANT_UFL4: C103.1, UFLANT4.3
ANT_UFL5: C124.1, UFLANT5.3
ANT_UFL6: C145.1, UFLANT6.3
ANT_UFL7: C166.1, UFLANT7.3
ANT_UFL8: C187.1, UFLANT8.3
ANT_UFL9: C208.1, UFLANT9.3
AVDD: C17.1, U$76.5
AVDD1: C28.1, U$3.5
AVDD2: C49.1, U$8.5
AVDD3: C70.1, U$13.5
AVDD4: C91.1, U$17.5
AVDD5: C112.1, U$21.5
AVDD6: C133.1, U$25.5
AVDD7: C154.1, U$29.5
AVDD8: C175.1, U$33.5
AVDD9: C196.1, U$37.5
DVDD: C2.1, U$76.21
DVDD1: C29.1, U$3.21
DVDD2: C50.1, U$8.21
DVDD3: C71.1, U$13.21
DVDD4: C92.1, U$17.21
DVDD5: C113.1, U$21.21
DVDD6: C134.1, U$25.21
DVDD7: C155.1, U$29.21
DVDD8: C176.1, U$33.21
DVDD9: C197.1, U$37.21
GND: ASWITCH.PIN2, BTN.2, C1.2, C2.2, C5.2, C6.2, C7.2, C8.2, C9.2, C10.2, C11.2, C13.2, C14.1, C15.2, C16.2, C17.2, C19.1, C20.2, C21.1, C22.1, FB1.2, LDO_VREG.GND, U$1.P$1, U$12.2, U$12.5, U$12.6, U$76.3, U$76.6, U$76.11, U$76.14, U$76.28, U$76.33, UFLANT.1, UFLANT.2, XOSCRF.2, XOSCRF.4
GND1: ASWITCH1.PIN2, BTN1.2, C3.2, C4.2, C12.2, C25.1, C26.2, C27.2, C28.2, C29.2, C30.1, C31.1, C32.2, C33.2, C34.2, C35.2, C36.2, C38.1, C39.2, C42.2, FB3.2, LDO_VREG1.GND, U$2.2, U$2.5, U$2.6, U$3.3, U$3.6, U$3.11, U$3.14, U$3.28, U$3.33, U$4.P$1, UFLANT1.1, UFLANT1.2, XOSCRF1.2, XOSCRF1.4
GND2: ASWITCH2.PIN2, BTN2.2, C43.2, C44.2, C45.2, C46.1, C47.2, C48.2, C49.2, C50.2, C51.1, C52.1, C53.2, C54.2, C55.2, C56.2, C57.2, C59.1, C60.2, C63.2, FB5.2, LDO_VREG2.GND, U$7.2, U$7.5, U$7.6, U$8.3, U$8.6, U$8.11, U$8.14, U$8.28, U$8.33, U$9.P$1, UFLANT2.1, UFLANT2.2, XOSCRF2.2, XOSCRF2.4
GND3: ASWITCH3.PIN2, BTN3.2, C64.2, C65.2, C66.2, C67.1, C68.2, C69.2, C70.2, C71.2, C72.1, C73.1, C74.2, C75.2, C76.2, C77.2, C78.2, C80.1, C81.2, C84.2, FB7.2, LDO_VREG3.GND, U$11.2, U$11.5, U$11.6, U$13.3, U$13.6, U$13.11, U$13.14, U$13.28, U$13.33, U$14.P$1, UFLANT3.1, UFLANT3.2, XOSCRF3.2, XOSCRF3.4
GND4: ASWITCH4.PIN2, BTN4.2, C85.2, C86.2, C87.2, C88.1, C89.2, C90.2, C91.2, C92.2, C93.1, C94.1, C95.2, C96.2, C97.2, C98.2, C99.2, C101.1, C102.2, C105.2, FB9.2, LDO_VREG4.GND, U$16.2, U$16.5, U$16.6, U$17.3, U$17.6, U$17.11, U$17.14, U$17.28, U$17.33, U$18.P$1, UFLANT4.1, UFLANT4.2, XOSCRF4.2, XOSCRF4.4
GND5: ASWITCH5.PIN2, BTN5.2, C106.2, C107.2, C108.2, C109.1, C110.2, C111.2, C112.2, C113.2, C114.1, C115.1, C116.2, C117.2, C118.2, C119.2, C120.2, C122.1, C123.2, C126.2, FB11.2, LDO_VREG5.GND, U$20.2, U$20.5, U$20.6, U$21.3, U$21.6, U$21.11, U$21.14, U$21.28, U$21.33, U$22.P$1, UFLANT5.1, UFLANT5.2, XOSCRF5.2, XOSCRF5.4
GND6: ASWITCH6.PIN2, BTN6.2, C127.2, C128.2, C129.2, C130.1, C131.2, C132.2, C133.2, C134.2, C135.1, C136.1, C137.2, C138.2, C139.2, C140.2, C141.2, C143.1, C144.2, C147.2, FB13.2, LDO_VREG6.GND, U$24.2, U$24.5, U$24.6, U$25.3, U$25.6, U$25.11, U$25.14, U$25.28, U$25.33, U$26.P$1, UFLANT6.1, UFLANT6.2, XOSCRF6.2, XOSCRF6.4
GND7: ASWITCH7.PIN2, BTN7.2, C148.2, C149.2, C150.2, C151.1, C152.2, C153.2, C154.2, C155.2, C156.1, C157.1, C158.2, C159.2, C160.2, C161.2, C162.2, C164.1, C165.2, C168.2, FB15.2, LDO_VREG7.GND, U$28.2, U$28.5, U$28.6, U$29.3, U$29.6, U$29.11, U$29.14, U$29.28, U$29.33, U$30.P$1, UFLANT7.1, UFLANT7.2, XOSCRF7.2, XOSCRF7.4
GND8: ASWITCH8.PIN2, BTN8.2, C169.2, C170.2, C171.2, C172.1, C173.2, C174.2, C175.2, C176.2, C177.1, C178.1, C179.2, C180.2, C181.2, C182.2, C183.2, C185.1, C186.2, C189.2, FB17.2, LDO_VREG8.GND, U$32.2, U$32.5, U$32.6, U$33.3, U$33.6, U$33.11, U$33.14, U$33.28, U$33.33, U$34.P$1, UFLANT8.1, UFLANT8.2, XOSCRF8.2, XOSCRF8.4
GND9: ASWITCH9.PIN2, BTN9.2, C190.2, C191.2, C192.2, C193.1, C194.2, C195.2, C196.2, C197.2, C198.1, C199.1, C200.2, C201.2, C202.2, C203.2, C204.2, C206.1, C207.2, C210.2, FB19.2, LDO_VREG9.GND, U$36.2, U$36.5, U$36.6, U$37.3, U$37.6, U$37.11, U$37.14, U$37.28, U$37.33, U$38.P$1, UFLANT9.1, UFLANT9.2, XOSCRF9.2, XOSCRF9.4
unnamed: BTN1.1, R3.1
unnamed: R6.2, RGBLED.3
unnamed: CN2.GND, FB3.1
unnamed: CN1.VBUS, FB2.1
unnamed: CN1.GND, FB1.1
unnamed: CN2.VBUS, FB4.1
unnamed: R8.2, RGBLED1.2
unnamed: R9.2, RGBLED1.3
unnamed: R10.2, RGBLED1.4
unnamed: R7.2, RGBLED.4
unnamed: BTN2.1, R11.1
unnamed: CN3.GND, FB5.1
unnamed: R4.2, RGBLED.2
unnamed: CN3.VBUS, FB6.1
unnamed: R13.2, RGBLED2.2
unnamed: R14.2, RGBLED2.3
unnamed: R15.2, RGBLED2.4
unnamed: BTN3.1, R16.1
unnamed: CN4.GND, FB7.1
unnamed: CN4.VBUS, FB8.1
unnamed: R18.2, RGBLED3.2
unnamed: R19.2, RGBLED3.3
unnamed: R20.2, RGBLED3.4
unnamed: BTN4.1, R21.1
unnamed: CN5.GND, FB9.1
unnamed: BTN.1, R1.1
unnamed: CN5.VBUS, FB10.1
unnamed: R23.2, RGBLED4.2
unnamed: R24.2, RGBLED4.3
unnamed: R25.2, RGBLED4.4
unnamed: BTN5.1, R26.1
unnamed: CN6.GND, FB11.1
unnamed: CN6.VBUS, FB12.1
unnamed: R28.2, RGBLED5.2
unnamed: R29.2, RGBLED5.3
unnamed: R30.2, RGBLED5.4
unnamed: BTN6.1, R31.1
unnamed: CN7.GND, FB13.1
unnamed: CN7.VBUS, FB14.1
unnamed: R33.2, RGBLED6.2
unnamed: R34.2, RGBLED6.3
unnamed: R35.2, RGBLED6.4
unnamed: BTN7.1, R36.1
unnamed: CN8.GND, FB15.1
unnamed: CN8.VBUS, FB16.1
unnamed: R38.2, RGBLED7.2
unnamed: R39.2, RGBLED7.3
unnamed: R40.2, RGBLED7.4
unnamed: BTN8.1, R41.1
unnamed: CN9.GND, FB17.1
unnamed: CN9.VBUS, FB18.1
unnamed: R43.2, RGBLED8.2
unnamed: R44.2, RGBLED8.3
unnamed: R45.2, RGBLED8.4
unnamed: BTN9.1, R46.1
unnamed: CN10.GND, FB19.1
unnamed: CN10.VBUS, FB20.1
unnamed: R48.2, RGBLED9.2
unnamed: R49.2, RGBLED9.3
unnamed: R50.2, RGBLED9.4
PA06(R): R4.1, U$76.7
PA06(R)1: R8.1, U$3.7
PA06(R)2: R13.1, U$8.7
PA06(R)3: R18.1, U$13.7
PA06(R)4: R23.1, U$17.7
PA06(R)5: R28.1, U$21.7
PA06(R)6: R33.1, U$25.7
PA06(R)7: R38.1, U$29.7
PA06(R)8: R43.1, U$33.7
PA06(R)9: R48.1, U$37.7
PA07(G): R6.1, U$76.8
PA07(G)1: R9.1, U$3.8
PA07(G)2: R14.1, U$8.8
PA07(G)3: R19.1, U$13.8
PA07(G)4: R24.1, U$17.8
PA07(G)5: R29.1, U$21.8
PA07(G)6: R34.1, U$25.8
PA07(G)7: R39.1, U$29.8
PA07(G)8: R44.1, U$33.8
PA07(G)9: R49.1, U$37.8
PA08/I2C/SDA: ASWITCH.PIN6, C20.1, U$76.9
PA08/I2C/SDA1: ASWITCH1.PIN6, C39.1, U$3.9
PA08/I2C/SDA2: ASWITCH2.PIN6, C60.1, U$8.9
PA08/I2C/SDA3: ASWITCH3.PIN6, C81.1, U$13.9
PA08/I2C/SDA4: ASWITCH4.PIN6, C102.1, U$17.9
PA08/I2C/SDA5: ASWITCH5.PIN6, C123.1, U$21.9
PA08/I2C/SDA6: ASWITCH6.PIN6, C144.1, U$25.9
PA08/I2C/SDA7: ASWITCH7.PIN6, C165.1, U$29.9
PA08/I2C/SDA8: ASWITCH8.PIN6, C186.1, U$33.9
PA08/I2C/SDA9: ASWITCH9.PIN6, C207.1, U$37.9
PA09/I2C/SCL: ASWITCH.PIN4, C19.2, U$76.10
PA09/I2C/SCL1: ASWITCH1.PIN4, C38.2, U$3.10
PA09/I2C/SCL2: ASWITCH2.PIN4, C59.2, U$8.10
PA09/I2C/SCL3: ASWITCH3.PIN4, C80.2, U$13.10
PA09/I2C/SCL4: ASWITCH4.PIN4, C101.2, U$17.10
PA09/I2C/SCL5: ASWITCH5.PIN4, C122.2, U$21.10
PA09/I2C/SCL6: ASWITCH6.PIN4, C143.2, U$25.10
PA09/I2C/SCL7: ASWITCH7.PIN4, C164.2, U$29.10
PA09/I2C/SCL8: ASWITCH8.PIN4, C185.2, U$33.10
PA09/I2C/SCL9: ASWITCH9.PIN4, C206.2, U$37.10
PA24/USBDM: CN1.D-, U$76.22
PA24/USBDM1: CN2.D-, U$3.22
PA24/USBDM2: CN3.D-, U$8.22
PA24/USBDM3: CN4.D-, U$13.22
PA24/USBDM4: CN5.D-, U$17.22
PA24/USBDM5: CN6.D-, U$21.22
PA24/USBDM6: CN7.D-, U$25.22
PA24/USBDM7: CN8.D-, U$29.22
PA24/USBDM8: CN9.D-, U$33.22
PA24/USBDM9: CN10.D-, U$37.22
PA25/USBDP: CN1.D+, U$76.23
PA25/USBDP1: CN2.D+, U$3.23
PA25/USBDP2: CN3.D+, U$8.23
PA25/USBDP3: CN4.D+, U$13.23
PA25/USBDP4: CN5.D+, U$17.23
PA25/USBDP5: CN6.D+, U$21.23
PA25/USBDP6: CN7.D+, U$25.23
PA25/USBDP7: CN8.D+, U$29.23
PA25/USBDP8: CN9.D+, U$33.23
PA25/USBDP9: CN10.D+, U$37.23
PA27(B): R7.1, U$76.25
PA27(B)1: R10.1, U$3.25
PA27(B)2: R15.1, U$8.25
PA27(B)3: R20.1, U$13.25
PA27(B)4: R25.1, U$17.25
PA27(B)5: R30.1, U$21.25
PA27(B)6: R35.1, U$25.25
PA27(B)7: R40.1, U$29.25
PA27(B)8: R45.1, U$33.25
PA27(B)9: R50.1, U$37.25
PA30/SWCLK: U$1.P$4, U$76.31
PA30/SWCLK1: U$3.31, U$4.P$4
PA30/SWCLK2: U$8.31, U$9.P$4
PA30/SWCLK3: U$13.31, U$14.P$4
PA30/SWCLK4: U$17.31, U$18.P$4
PA30/SWCLK5: U$21.31, U$22.P$4
PA30/SWCLK6: U$25.31, U$26.P$4
PA30/SWCLK7: U$29.31, U$30.P$4
PA30/SWCLK8: U$33.31, U$34.P$4
PA30/SWCLK9: U$37.31, U$38.P$4
PA31/SWDIO: U$1.P$5, U$76.32
PA31/SWDIO1: U$3.32, U$4.P$5
PA31/SWDIO2: U$8.32, U$9.P$5
PA31/SWDIO3: U$13.32, U$14.P$5
PA31/SWDIO4: U$17.32, U$18.P$5
PA31/SWDIO5: U$21.32, U$22.P$5
PA31/SWDIO6: U$25.32, U$26.P$5
PA31/SWDIO7: U$29.32, U$30.P$5
PA31/SWDIO8: U$33.32, U$34.P$5
PA31/SWDIO9: U$37.32, U$38.P$5
RESET: C1.1, R1.2, R2.1, U$1.P$3, U$76.26
RESET1: C3.1, R3.2, R5.1, U$3.26, U$4.P$3
RESET2: C43.1, R11.2, R12.1, U$8.26, U$9.P$3
RESET3: C64.1, R16.2, R17.1, U$13.26, U$14.P$3
RESET4: C85.1, R21.2, R22.1, U$17.26, U$18.P$3
RESET5: C106.1, R26.2, R27.1, U$21.26, U$22.P$3
RESET6: C127.1, R31.2, R32.1, U$25.26, U$26.P$3
RESET7: C148.1, R36.2, R37.1, U$29.26, U$30.P$3
RESET8: C169.1, R41.2, R42.1, U$33.26, U$34.P$3
RESET9: C190.1, R46.2, R47.1, U$37.26, U$38.P$3
RFN: U$12.3, U$76.13
RFN1: U$2.3, U$3.13
RFN2: U$7.3, U$8.13
RFN3: U$11.3, U$13.13
RFN4: U$16.3, U$17.13
RFN5: U$20.3, U$21.13
RFN6: U$24.3, U$25.13
RFN7: U$28.3, U$29.13
RFN8: U$32.3, U$33.13
RFN9: U$36.3, U$37.13
RFP: U$12.4, U$76.12
RFP1: U$2.4, U$3.12
RFP2: U$7.4, U$8.12
RFP3: U$11.4, U$13.12
RFP4: U$16.4, U$17.12
RFP5: U$20.4, U$21.12
RFP6: U$24.4, U$25.12
RFP7: U$28.4, U$29.12
RFP8: U$32.4, U$33.12
RFP9: U$36.4, U$37.12
RFSWITCH_PIN1: ASWITCH.PIN1, C24.1
RFSWITCH_PIN2: ASWITCH1.PIN1, C41.1
RFSWITCH_PIN3: ASWITCH.PIN3, C23.2
RFSWITCH_PIN4: ASWITCH1.PIN5, C37.2
RFSWITCH_PIN5: ASWITCH.PIN5, C18.2
RFSWITCH_PIN6: ASWITCH1.PIN3, C40.2
RFSWITCH_PIN7: ASWITCH2.PIN1, C62.1
RFSWITCH_PIN8: ASWITCH2.PIN5, C58.2
RFSWITCH_PIN9: ASWITCH2.PIN3, C61.2
RFSWITCH_PIN10: ASWITCH3.PIN1, C83.1
RFSWITCH_PIN11: ASWITCH3.PIN5, C79.2
RFSWITCH_PIN12: ASWITCH3.PIN3, C82.2
RFSWITCH_PIN13: ASWITCH4.PIN1, C104.1
RFSWITCH_PIN14: ASWITCH4.PIN5, C100.2
RFSWITCH_PIN15: ASWITCH4.PIN3, C103.2
RFSWITCH_PIN16: ASWITCH5.PIN1, C125.1
RFSWITCH_PIN17: ASWITCH5.PIN5, C121.2
RFSWITCH_PIN18: ASWITCH5.PIN3, C124.2
RFSWITCH_PIN19: ASWITCH6.PIN1, C146.1
RFSWITCH_PIN20: ASWITCH6.PIN5, C142.2
RFSWITCH_PIN21: ASWITCH6.PIN3, C145.2
RFSWITCH_PIN22: ASWITCH7.PIN1, C167.1
RFSWITCH_PIN23: ASWITCH7.PIN5, C163.2
RFSWITCH_PIN24: ASWITCH7.PIN3, C166.2
RFSWITCH_PIN25: ASWITCH8.PIN1, C188.1
RFSWITCH_PIN26: ASWITCH8.PIN5, C184.2
RFSWITCH_PIN27: ASWITCH8.PIN3, C187.2
RFSWITCH_PIN28: ASWITCH9.PIN1, C209.1
RFSWITCH_PIN29: ASWITCH9.PIN5, C205.2
RFSWITCH_PIN30: ASWITCH9.PIN3, C208.2
VDDANA: C8.1, C22.2, L6.2, U$76.4
VDDANA1: C31.2, C35.1, L2.2, U$3.4
VDDANA2: C52.2, C56.1, L4.2, U$8.4
VDDANA3: C73.2, C77.1, L7.2, U$13.4
VDDANA4: C94.2, C98.1, L9.2, U$17.4
VDDANA5: C115.2, C119.1, L11.2, U$21.4
VDDANA6: C136.2, C140.1, L13.2, U$25.4
VDDANA7: C157.2, C161.1, L15.2, U$29.4
VDDANA8: C178.2, C182.1, L17.2, U$33.4
VDDANA9: C199.2, C203.1, L19.2, U$37.4
VDDCORE: C9.1, U$76.29
VDDCORE1: C36.1, U$3.29
VDDCORE2: C57.1, U$8.29
VDDCORE3: C78.1, U$13.29
VDDCORE4: C99.1, U$17.29
VDDCORE5: C120.1, U$21.29
VDDCORE6: C141.1, U$25.29
VDDCORE7: C162.1, U$29.29
VDDCORE8: C183.1, U$33.29
VDDCORE9: C204.1, U$37.29
VIN: C6.1, C7.1, FB2.2, LDO_VREG.VIN
VIN1: C33.1, C34.1, FB4.2, LDO_VREG1.VIN
VIN2: C54.1, C55.1, FB6.2, LDO_VREG2.VIN
VIN3: C75.1, C76.1, FB8.2, LDO_VREG3.VIN
VIN4: C96.1, C97.1, FB10.2, LDO_VREG4.VIN
VIN5: C117.1, C118.1, FB12.2, LDO_VREG5.VIN
VIN6: C138.1, C139.1, FB14.2, LDO_VREG6.VIN
VIN7: C159.1, C160.1, FB16.2, LDO_VREG7.VIN
VIN8: C180.1, C181.1, FB18.2, LDO_VREG8.VIN
VIN9: C201.1, C202.1, FB20.2, LDO_VREG9.VIN
XTALIN: C14.2, U$76.2, XOSCRF.1
XTALIN1: C25.2, U$3.2, XOSCRF1.1
XTALIN2: C46.2, U$8.2, XOSCRF2.1
XTALIN3: C67.2, U$13.2, XOSCRF3.1
XTALIN4: C88.2, U$17.2, XOSCRF4.1
XTALIN5: C109.2, U$21.2, XOSCRF5.1
XTALIN6: C130.2, U$25.2, XOSCRF6.1
XTALIN7: C151.2, U$29.2, XOSCRF7.1
XTALIN8: C172.2, U$33.2, XOSCRF8.1
XTALIN9: C193.2, U$37.2, XOSCRF9.1
XTALOUT: C15.1, U$76.1, XOSCRF.3
XTALOUT1: C26.1, U$3.1, XOSCRF1.3
XTALOUT2: C47.1, U$8.1, XOSCRF2.3
XTALOUT3: C68.1, U$13.1, XOSCRF3.3
XTALOUT4: C89.1, U$17.1, XOSCRF4.3
XTALOUT5: C110.1, U$21.1, XOSCRF5.3
XTALOUT6: C131.1, U$25.1, XOSCRF6.3
XTALOUT7: C152.1, U$29.1, XOSCRF7.3
XTALOUT8: C173.1, U$33.1, XOSCRF8.3
XTALOUT9: C194.1, U$37.1, XOSCRF9.3
