femtoduino/femto-beacon/Eagle_Files/FemtoBeacon_r2.0.0/panelized_oshpark_femtoBeacon_r2.0.0.brd

## EAGLE design Eagle_Files/FemtoBeacon_r2.0.0/panelized_oshpark_femtoBeacon_r2.0.0.brd (2017-01-18)

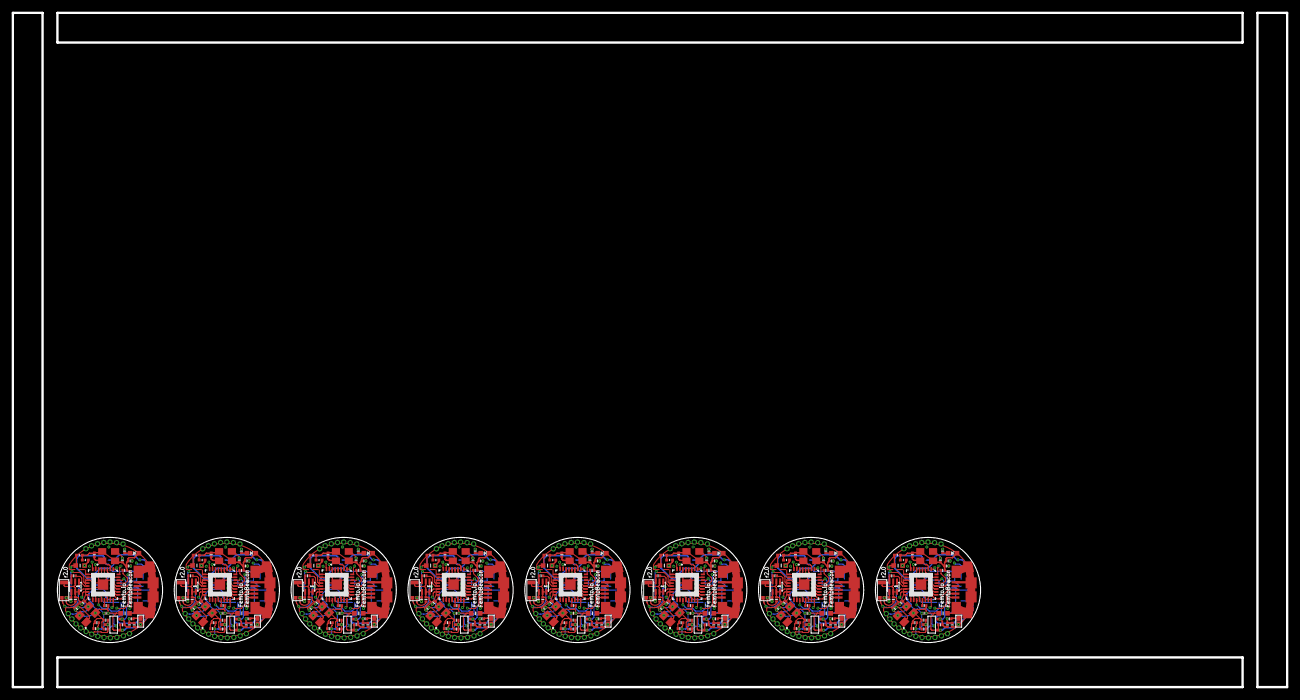
[picture p71: board panelized_oshpark_femtoBeacon_r2.0.0.brd from above]

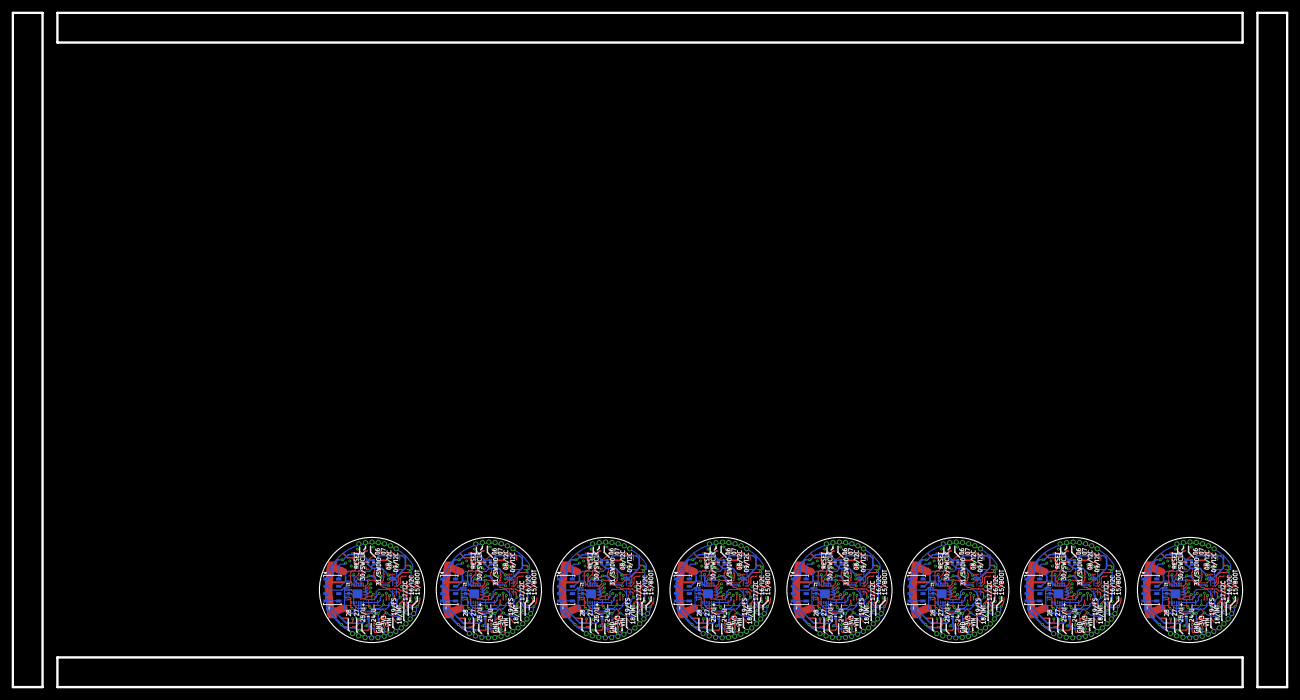
[picture p72: board panelized_oshpark_femtoBeacon_r2.0.0.brd from below]

Board: 4 copper layers, 218.1 x 115.4 mm, 480 parts (56 on the bottom side), 288 nets.

Parts:
ANT1, ANT2, ANT3, ANT4, ANT5, ANT6, ANT7, ANT8: PULSE_ANT_2.4GHZ; ANT_BAR
BTN, BTN1, BTN2, BTN3, BTN4, BTN5, BTN6, BTN7: DNP; SPST_SMD
C1, C2, C8, C9, C10, C16, C17, C18, C19, C25, C26, C27, C28, C29, C30, C32, C33, C36, C45, C46, C47, C48, C52, C53, C54, C55, C56, C59, C68, C69, C70, C71, C75, C76, C77, C78, C79, C82, C91, C92, C93, C94, C98, C99, C100, C101, C102, C105, C114, C115, C116, C117, C121, C122, C123, C124, C125, C128, C137, C138, C139, C140, C144, C145, C146, C147, C148, C151, C160, C161, C162, C163, C167, C168, C169, C170, C171, C174, C183, C184: 0.1uF; PART
C3, C4, C37, C38, C60, C61, C83, C84, C106, C107, C129, C130, C152, C153, C175, C176: 10pF; PART
C5, C6, C20, C23, C49, C50, C72, C73, C95, C96, C118, C119, C141, C142, C164, C165: 2.2uF; PART
C7, C24, C51, C74, C97, C120, C143, C166: 0.47uF; PART
C11, C12, C39, C40, C62, C63, C85, C86, C108, C109, C131, C132, C154, C155, C177, C178: 22pF, C0G, 5%; PART
C13, C41, C64, C87, C110, C133, C156, C179: DNP; PART
C14, C15, C42, C43, C65, C66, C88, C89, C111, C112, C134, C135, C157, C158, C180, C181: 9pF; PART
C21, C22, C34, C35, C57, C58, C80, C81, C103, C104, C126, C127, C149, C150, C172, C173: 10uF; _0402MP
C31, C44, C67, C90, C113, C136, C159, C182: 10nF; PART
FB1, FB2, FB3, FB4, FB5, FB6, FB7, FB8: _0603MP
L1, L2, L3, L4, L5, L6, L7, L8: 10uH; _0603MP
LDO_VREG, LDO_VREG1, LDO_VREG2, LDO_VREG3, LDO_VREG4, LDO_VREG5, LDO_VREG6, LDO_VREG7: MCP1700T-3302E/TT
LED1, LED2, LED3, LED4, LED5, LED6, LED7, LED8: BLUE; CHIPLED_0603_NOOUTLINE
R1, R3, R4, R6, R11, R13, R16, R18, R21, R23, R26, R28, R31, R33, R36, R38: 330; PART
R2, R5, R12, R17, R22, R27, R32, R37: 10K; PART
R7, R8, R9, R10, R14, R15, R19, R20, R24, R25, R29, R30, R34, R35, R39, R40: 2.2K; PART
SER3628CT-ND, SER3628CT-ND1, SER3628CT-ND2, SER3628CT-ND3, SER3628CT-ND4, SER3628CT-ND5, SER3628CT-ND6, SER3628CT-ND7: 16MHz; TSX-3225
TSX-3225_CRYSTAL, TSX-3225_CRYSTAL1, TSX-3225_CRYSTAL2, TSX-3225_CRYSTAL3, TSX-3225_CRYSTAL4, TSX-3225_CRYSTAL5, TSX-3225_CRYSTAL6, TSX-3225_CRYSTAL7: 48MHz; TSX-3225
U$1, U$2, U$3, U$4, U$5, U$7, U$8, U$9, U$10, U$11, U$13, U$14, U$15, U$16, U$17, U$18, U$19, U$20, U$21, U$22, U$23, U$24, U$25, U$26, U$27, U$32, U$33, U$34, U$35, U$36, U$37, U$38, U$39, U$40, U$41, U$42, U$43, U$45, U$46, U$47, U$48, U$49, U$50, U$51, U$52, U$53, U$54, U$55, U$56, U$57, U$58, U$59, U$60, U$61, U$62, U$63, U$64, U$69, U$70, U$71, U$72, U$73, U$74, U$75, U$77, U$78, U$79, U$80, U$81, U$82, U$83, U$84, U$85, U$86, U$87, U$88, U$93, U$94, U$95, U$96, U$97, U$98, U$99, U$100, U$101, U$102, U$103, U$104, U$105, U$106, U$107, U$108, U$109, U$110, U$111, U$116, U$117, U$118, U$119, U$120, U$121, U$122, U$123, U$124, U$125, U$126, U$127, U$128, U$129, U$130, U$131, U$132, U$133, U$134, U$139, U$140, U$141, U$142, U$143, U$144, U$145, U$146, U$147, U$148, U$149, U$150, U$151, U$152, U$153, U$154, U$155, U$156, U$157, U$162, U$163, U$164, U$165, U$166, U$167, U$168, U$169, U$170, U$171, U$172, U$173, U$174, U$175, U$176, U$177, U$178, U$179, U$180: 1X1_ROUND
U$6, U$31, U$68, U$92, U$115, U$138, U$161, U$184: MPU-9250; QFN_3X3MM
U$12, U$30, U$67, U$91, U$114, U$137, U$160, U$183: JOHANSON_2450BM15A0015E; 0805_BALUN
U$28, U$44, U$65, U$89, U$112, U$135, U$158, U$181: MS5611-01BA03
U$29, U$66, U$76, U$90, U$113, U$136, U$159, U$182: ATSAMR21E18A-MUT; QFN32
USB, USB1, USB2, USB3, USB4, USB5, USB6, USB7: USB_MICROB; USB_MICROB_PACKAGE

Connections:
3.3V: C5.1, C10.1, C16.1, C21.2, C29.1, C30.2, C31.2, L6.1, LDO_VREG.VOUT, R2.2, R8.2, R9.2, U$5.P$1, U$6.P$1, U$6.P$8, U$6.P$13, U$6.P$22, U$44.1, U$44.2, U$76.24, U$76.30
3.3V1: C20.1, C25.1, C28.1, C34.2, C36.1, C44.2, C45.2, L1.1, LDO_VREG1.VOUT, R5.2, R7.2, R10.2, U$8.P$1, U$28.1, U$28.2, U$29.24, U$29.30, U$31.P$1, U$31.P$8, U$31.P$13, U$31.P$22
3.3V2: C49.1, C52.1, C55.1, C57.2, C59.1, C67.2, C68.2, L2.1, LDO_VREG2.VOUT, R12.2, R14.2, R15.2, U$34.P$1, U$65.1, U$65.2, U$66.24, U$66.30, U$68.P$1, U$68.P$8, U$68.P$13, U$68.P$22
3.3V3: C72.1, C75.1, C78.1, C80.2, C82.1, C90.2, C91.2, L3.1, LDO_VREG3.VOUT, R17.2, R19.2, R20.2, U$71.P$1, U$89.1, U$89.2, U$90.24, U$90.30, U$92.P$1, U$92.P$8, U$92.P$13, U$92.P$22
3.3V4: C95.1, C98.1, C101.1, C103.2, C105.1, C113.2, C114.2, L4.1, LDO_VREG4.VOUT, R22.2, R24.2, R25.2, U$95.P$1, U$112.1, U$112.2, U$113.24, U$113.30, U$115.P$1, U$115.P$8, U$115.P$13, U$115.P$22
3.3V5: C118.1, C121.1, C124.1, C126.2, C128.1, C136.2, C137.2, L5.1, LDO_VREG5.VOUT, R27.2, R29.2, R30.2, U$118.P$1, U$135.1, U$135.2, U$136.24, U$136.30, U$138.P$1, U$138.P$8, U$138.P$13, U$138.P$22
3.3V6: C141.1, C144.1, C147.1, C149.2, C151.1, C159.2, C160.2, L7.1, LDO_VREG6.VOUT, R32.2, R34.2, R35.2, U$141.P$1, U$158.1, U$158.2, U$159.24, U$159.30, U$161.P$1, U$161.P$8, U$161.P$13, U$161.P$22
3.3V7: C164.1, C167.1, C170.1, C172.2, C174.1, C182.2, C183.2, L8.1, LDO_VREG7.VOUT, R37.2, R39.2, R40.2, U$164.P$1, U$181.1, U$181.2, U$182.24, U$182.30, U$184.P$1, U$184.P$8, U$184.P$13, U$184.P$22
ANT_OUT: ANT1.1, U$12.1
ANT_OUT1: ANT2.1, U$30.1
ANT_OUT2: ANT3.1, U$67.1
ANT_OUT3: ANT4.1, U$91.1
ANT_OUT4: ANT5.1, U$114.1
ANT_OUT5: ANT6.1, U$137.1
ANT_OUT6: ANT7.1, U$160.1
ANT_OUT7: ANT8.1, U$183.1
AVDD: C17.1, U$76.5
AVDD1: C33.1, U$29.5
AVDD2: C56.1, U$66.5
AVDD3: C79.1, U$90.5
AVDD4: C102.1, U$113.5
AVDD5: C125.1, U$136.5
AVDD6: C148.1, U$159.5
AVDD7: C171.1, U$182.5
DVDD: C2.1, U$76.21
DVDD1: C19.1, U$29.21
DVDD2: C48.1, U$66.21
DVDD3: C71.1, U$90.21
DVDD4: C94.1, U$113.21
DVDD5: C117.1, U$136.21
DVDD6: C140.1, U$159.21
DVDD7: C163.1, U$182.21
GND: ANT1.3, BTN.2, C1.2, C2.2, C3.1, C4.2, C5.2, C6.2, C7.2, C8.2, C9.2, C10.2, C13.2, C14.1, C15.2, C16.2, C17.2, C21.1, C22.1, C29.2, C30.1, C31.1, C32.2, FB1.2, LDO_VREG.GND, LED2.C, SER3628CT-ND.2, SER3628CT-ND.4, TSX-3225_CRYSTAL.2, TSX-3225_CRYSTAL.4, U$2.P$1, U$6.P$20, U$12.2, U$12.5, U$12.6, U$44.3, U$44.4, U$44.5, U$76.3, U$76.6, U$76.11, U$76.14, U$76.28, U$76.33
GND1: ANT2.3, BTN1.2, C18.2, C19.2, C20.2, C23.2, C24.2, C25.2, C26.2, C27.2, C28.2, C33.2, C34.1, C35.1, C36.2, C37.1, C38.2, C41.2, C42.1, C43.2, C44.1, C45.1, C46.2, FB2.2, LDO_VREG1.GND, LED1.C, SER3628CT-ND1.2, SER3628CT-ND1.4, TSX-3225_CRYSTAL1.2, TSX-3225_CRYSTAL1.4, U$4.P$1, U$28.3, U$28.4, U$28.5, U$29.3, U$29.6, U$29.11, U$29.14, U$29.28, U$29.33, U$30.2, U$30.5, U$30.6, U$31.P$20
GND2: ANT3.3, BTN2.2, C47.2, C48.2, C49.2, C50.2, C51.2, C52.2, C53.2, C54.2, C55.2, C56.2, C57.1, C58.1, C59.2, C60.1, C61.2, C64.2, C65.1, C66.2, C67.1, C68.1, C69.2, FB3.2, LDO_VREG2.GND, LED3.C, SER3628CT-ND2.2, SER3628CT-ND2.4, TSX-3225_CRYSTAL2.2, TSX-3225_CRYSTAL2.4, U$33.P$1, U$65.3, U$65.4, U$65.5, U$66.3, U$66.6, U$66.11, U$66.14, U$66.28, U$66.33, U$67.2, U$67.5, U$67.6, U$68.P$20
GND3: ANT4.3, BTN3.2, C70.2, C71.2, C72.2, C73.2, C74.2, C75.2, C76.2, C77.2, C78.2, C79.2, C80.1, C81.1, C82.2, C83.1, C84.2, C87.2, C88.1, C89.2, C90.1, C91.1, C92.2, FB4.2, LDO_VREG3.GND, LED4.C, SER3628CT-ND3.2, SER3628CT-ND3.4, TSX-3225_CRYSTAL3.2, TSX-3225_CRYSTAL3.4, U$70.P$1, U$89.3, U$89.4, U$89.5, U$90.3, U$90.6, U$90.11, U$90.14, U$90.28, U$90.33, U$91.2, U$91.5, U$91.6, U$92.P$20
GND4: ANT5.3, BTN4.2, C93.2, C94.2, C95.2, C96.2, C97.2, C98.2, C99.2, C100.2, C101.2, C102.2, C103.1, C104.1, C105.2, C106.1, C107.2, C110.2, C111.1, C112.2, C113.1, C114.1, C115.2, FB5.2, LDO_VREG4.GND, LED5.C, SER3628CT-ND4.2, SER3628CT-ND4.4, TSX-3225_CRYSTAL4.2, TSX-3225_CRYSTAL4.4, U$94.P$1, U$112.3, U$112.4, U$112.5, U$113.3, U$113.6, U$113.11, U$113.14, U$113.28, U$113.33, U$114.2, U$114.5, U$114.6, U$115.P$20
GND5: ANT6.3, BTN5.2, C116.2, C117.2, C118.2, C119.2, C120.2, C121.2, C122.2, C123.2, C124.2, C125.2, C126.1, C127.1, C128.2, C129.1, C130.2, C133.2, C134.1, C135.2, C136.1, C137.1, C138.2, FB6.2, LDO_VREG5.GND, LED6.C, SER3628CT-ND5.2, SER3628CT-ND5.4, TSX-3225_CRYSTAL5.2, TSX-3225_CRYSTAL5.4, U$117.P$1, U$135.3, U$135.4, U$135.5, U$136.3, U$136.6, U$136.11, U$136.14, U$136.28, U$136.33, U$137.2, U$137.5, U$137.6, U$138.P$20
GND6: ANT7.3, BTN6.2, C139.2, C140.2, C141.2, C142.2, C143.2, C144.2, C145.2, C146.2, C147.2, C148.2, C149.1, C150.1, C151.2, C152.1, C153.2, C156.2, C157.1, C158.2, C159.1, C160.1, C161.2, FB7.2, LDO_VREG6.GND, LED7.C, SER3628CT-ND6.2, SER3628CT-ND6.4, TSX-3225_CRYSTAL6.2, TSX-3225_CRYSTAL6.4, U$140.P$1, U$158.3, U$158.4, U$158.5, U$159.3, U$159.6, U$159.11, U$159.14, U$159.28, U$159.33, U$160.2, U$160.5, U$160.6, U$161.P$20
GND7: ANT8.3, BTN7.2, C162.2, C163.2, C164.2, C165.2, C166.2, C167.2, C168.2, C169.2, C170.2, C171.2, C172.1, C173.1, C174.2, C175.1, C176.2, C179.2, C180.1, C181.2, C182.1, C183.1, C184.2, FB8.2, LDO_VREG7.GND, LED8.C, SER3628CT-ND7.2, SER3628CT-ND7.4, TSX-3225_CRYSTAL7.2, TSX-3225_CRYSTAL7.4, U$163.P$1, U$181.3, U$181.4, U$181.5, U$182.3, U$182.6, U$182.11, U$182.14, U$182.28, U$182.33, U$183.2, U$183.5, U$183.6, U$184.P$20
unnamed: C11.2, U$12.3
unnamed: ANT1.2, C13.1
unnamed: C12.2, U$12.4
unnamed: C32.1, U$6.P$10
unnamed: FB1.1, USB.5, USB.6, USB.7, USB.8, USB.9, USB.10, USB.11
unnamed: BTN1.1, R3.1
unnamed: LED1.A, R6.2
unnamed: C39.2, U$30.3
unnamed: C40.2, U$30.4
unnamed: ANT2.2, C41.1
unnamed: C46.1, U$31.P$10
unnamed: LED2.A, R4.2
unnamed: FB2.1, USB1.5, USB1.6, USB1.7, USB1.8, USB1.9, USB1.10, USB1.11
unnamed: BTN2.1, R11.1
unnamed: LED3.A, R13.2
unnamed: C62.2, U$67.3
unnamed: C63.2, U$67.4
unnamed: ANT3.2, C64.1
unnamed: C69.1, U$68.P$10
unnamed: FB3.1, USB2.5, USB2.6, USB2.7, USB2.8, USB2.9, USB2.10, USB2.11
unnamed: BTN3.1, R16.1
unnamed: LED4.A, R18.2
unnamed: BTN.1, R1.1
unnamed: C85.2, U$91.3
unnamed: C86.2, U$91.4
unnamed: ANT4.2, C87.1
unnamed: C92.1, U$92.P$10
unnamed: FB4.1, USB3.5, USB3.6, USB3.7, USB3.8, USB3.9, USB3.10, USB3.11
unnamed: BTN4.1, R21.1
unnamed: LED5.A, R23.2
unnamed: C108.2, U$114.3
unnamed: C109.2, U$114.4
unnamed: ANT5.2, C110.1
unnamed: C115.1, U$115.P$10
unnamed: FB5.1, USB4.5, USB4.6, USB4.7, USB4.8, USB4.9, USB4.10, USB4.11
unnamed: BTN5.1, R26.1
unnamed: LED6.A, R28.2
unnamed: C131.2, U$137.3
unnamed: C132.2, U$137.4
unnamed: ANT6.2, C133.1
unnamed: C138.1, U$138.P$10
unnamed: FB6.1, USB5.5, USB5.6, USB5.7, USB5.8, USB5.9, USB5.10, USB5.11
unnamed: BTN6.1, R31.1
unnamed: LED7.A, R33.2
unnamed: C154.2, U$160.3
unnamed: C155.2, U$160.4
unnamed: ANT7.2, C156.1
unnamed: C161.1, U$161.P$10
unnamed: FB7.1, USB6.5, USB6.6, USB6.7, USB6.8, USB6.9, USB6.10, USB6.11
unnamed: BTN7.1, R36.1
unnamed: LED8.A, R38.2
unnamed: C177.2, U$183.3
unnamed: C178.2, U$183.4
unnamed: ANT8.2, C179.1
unnamed: C184.1, U$184.P$10
unnamed: FB8.1, USB7.5, USB7.6, USB7.7, USB7.8, USB7.9, USB7.10, USB7.11
PA01: U$25.P$1, U$29.7
PA02: U$19.P$1, U$29.8
PA03: U$23.P$1, U$29.25
PA04: U$24.P$1, U$29.27
PA05: U$62.P$1, U$66.7
PA06: U$54.P$1, U$76.7
PA07: U$43.P$1, U$76.8
PA08: U$56.P$1, U$66.8
PA08/I2C: R8.1, U$6.P$24, U$42.P$1, U$44.7, U$76.9
PA08/I2C1: R7.1, U$18.P$1, U$28.7, U$29.9, U$31.P$24
PA08/I2C2: R14.1, U$55.P$1, U$65.7, U$66.9, U$68.P$24
PA08/I2C3: R19.1, U$79.P$1, U$89.7, U$90.9, U$92.P$24
PA08/I2C4: R24.1, U$102.P$1, U$112.7, U$113.9, U$115.P$24
PA08/I2C5: R29.1, U$125.P$1, U$135.7, U$136.9, U$138.P$24
PA08/I2C6: R34.1, U$148.P$1, U$158.7, U$159.9, U$161.P$24
PA08/I2C7: R39.1, U$171.P$1, U$181.7, U$182.9, U$184.P$24
PA09: U$60.P$1, U$66.25
PA09/I2C: R9.1, U$6.P$23, U$41.P$1, U$44.8, U$76.10
PA09/I2C1: R10.1, U$17.P$1, U$28.8, U$29.10, U$31.P$23
PA09/I2C2: R15.1, U$53.P$1, U$65.8, U$66.10, U$68.P$23
PA09/I2C3: R20.1, U$78.P$1, U$89.8, U$90.10, U$92.P$23
PA09/I2C4: R25.1, U$101.P$1, U$112.8, U$113.10, U$115.P$23
PA09/I2C5: R30.1, U$124.P$1, U$135.8, U$136.10, U$138.P$23
PA09/I2C6: R35.1, U$147.P$1, U$158.8, U$159.10, U$161.P$23
PA09/I2C7: R40.1, U$170.P$1, U$181.8, U$182.10, U$184.P$23
PA10: U$61.P$1, U$66.27
PA11: U$86.P$1, U$90.7
PA12: U$80.P$1, U$90.8
PA13: U$84.P$1, U$90.25
PA14: U$85.P$1, U$90.27
PA14/XIN_MC: C3.2, TSX-3225_CRYSTAL.1, U$76.15
PA14/XIN_MC1: C37.2, TSX-3225_CRYSTAL1.1, U$29.15
PA14/XIN_MC2: C60.2, TSX-3225_CRYSTAL2.1, U$66.15
PA14/XIN_MC3: C83.2, TSX-3225_CRYSTAL3.1, U$90.15
PA14/XIN_MC4: C106.2, TSX-3225_CRYSTAL4.1, U$113.15
PA14/XIN_MC5: C129.2, TSX-3225_CRYSTAL5.1, U$136.15
PA14/XIN_MC6: C152.2, TSX-3225_CRYSTAL6.1, U$159.15
PA14/XIN_MC7: C175.2, TSX-3225_CRYSTAL7.1, U$182.15
PA15: U$109.P$1, U$113.7
PA15/XOUT_MC: C4.1, TSX-3225_CRYSTAL.3, U$39.P$1, U$76.16
PA15/XOUT_MC1: C38.1, TSX-3225_CRYSTAL1.3, U$16.P$1, U$29.16
PA15/XOUT_MC2: C61.1, TSX-3225_CRYSTAL2.3, U$52.P$1, U$66.16
PA15/XOUT_MC3: C84.1, TSX-3225_CRYSTAL3.3, U$77.P$1, U$90.16
PA15/XOUT_MC4: C107.1, TSX-3225_CRYSTAL4.3, U$100.P$1, U$113.16
PA15/XOUT_MC5: C130.1, TSX-3225_CRYSTAL5.3, U$123.P$1, U$136.16
PA15/XOUT_MC6: C153.1, TSX-3225_CRYSTAL6.3, U$146.P$1, U$159.16
PA15/XOUT_MC7: C176.1, TSX-3225_CRYSTAL7.3, U$169.P$1, U$182.16
PA16: U$103.P$1, U$113.8
PA16/I2C: U$38.P$1, U$76.17
PA16/I2C1: U$15.P$1, U$29.17
PA16/I2C2: U$51.P$1, U$66.17
PA16/I2C3: U$75.P$1, U$90.17
PA16/I2C4: U$99.P$1, U$113.17
PA16/I2C5: U$122.P$1, U$136.17
PA16/I2C6: U$145.P$1, U$159.17
PA16/I2C7: U$168.P$1, U$182.17
PA17: U$107.P$1, U$113.25
PA17/I2C: U$37.P$1, U$76.18
PA17/I2C1: U$14.P$1, U$29.18
PA17/I2C2: U$50.P$1, U$66.18
PA17/I2C3: U$74.P$1, U$90.18
PA17/I2C4: U$98.P$1, U$113.18
PA17/I2C5: U$121.P$1, U$136.18
PA17/I2C6: U$144.P$1, U$159.18
PA17/I2C7: U$167.P$1, U$182.18
PA18: U$108.P$1, U$113.27
PA18/INTA: U$6.P$11, U$36.P$1, U$76.19
PA18/INTA1: U$13.P$1, U$29.19, U$31.P$11
PA18/INTA2: U$49.P$1, U$66.19, U$68.P$11
PA18/INTA3: U$73.P$1, U$90.19, U$92.P$11
PA18/INTA4: U$97.P$1, U$113.19, U$115.P$11
PA18/INTA5: U$120.P$1, U$136.19, U$138.P$11
PA18/INTA6: U$143.P$1, U$159.19, U$161.P$11
PA18/INTA7: U$166.P$1, U$182.19, U$184.P$11
PA19: U$132.P$1, U$136.7
PA19/FSYNC: U$6.P$12, U$35.P$1, U$76.20
PA19/FSYNC1: U$11.P$1, U$29.20, U$31.P$12
PA19/FSYNC2: U$40.P$1, U$66.20, U$68.P$12
PA19/FSYNC3: U$72.P$1, U$90.20, U$92.P$12
PA19/FSYNC4: U$96.P$1, U$113.20, U$115.P$12
PA19/FSYNC5: U$119.P$1, U$136.20, U$138.P$12
PA19/FSYNC6: U$142.P$1, U$159.20, U$161.P$12
PA19/FSYNC7: U$165.P$1, U$182.20, U$184.P$12
PA20: U$126.P$1, U$136.8
PA21: U$130.P$1, U$136.25
PA22: U$131.P$1, U$136.27
PA23: U$155.P$1, U$159.7
PA24: U$149.P$1, U$159.8
PA24/USBDM: U$9.P$1, U$76.22, USB.2
PA24/USBDM1: U$26.P$1, U$29.22, USB1.2
PA24/USBDM2: U$63.P$1, U$66.22, USB2.2
PA24/USBDM3: U$87.P$1, U$90.22, USB3.2
PA24/USBDM4: U$110.P$1, U$113.22, USB4.2
PA24/USBDM5: U$133.P$1, U$136.22, USB5.2
PA24/USBDM6: U$156.P$1, U$159.22, USB6.2
PA24/USBDM7: U$179.P$1, U$182.22, USB7.2
PA25: U$153.P$1, U$159.25
PA25/USBDP: U$10.P$1, U$76.23, USB.3
PA25/USBDP1: U$27.P$1, U$29.23, USB1.3
PA25/USBDP2: U$64.P$1, U$66.23, USB2.3
PA25/USBDP3: U$88.P$1, U$90.23, USB3.3
PA25/USBDP4: U$111.P$1, U$113.23, USB4.3
PA25/USBDP5: U$134.P$1, U$136.23, USB5.3
PA25/USBDP6: U$157.P$1, U$159.23, USB6.3
PA25/USBDP7: U$180.P$1, U$182.23, USB7.3
PA26: U$154.P$1, U$159.27
PA27: U$7.P$1, U$76.25
PA28: U$48.P$1, U$76.27
PA29: U$178.P$1, U$182.7
PA30: U$172.P$1, U$182.8
PA30/SWCLK: R4.1, U$46.P$1, U$76.31
PA30/SWCLK1: R6.1, U$21.P$1, U$29.31
PA30/SWCLK2: R13.1, U$58.P$1, U$66.31
PA30/SWCLK3: R18.1, U$82.P$1, U$90.31
PA30/SWCLK4: R23.1, U$105.P$1, U$113.31
PA30/SWCLK5: R28.1, U$128.P$1, U$136.31
PA30/SWCLK6: R33.1, U$151.P$1, U$159.31
PA30/SWCLK7: R38.1, U$174.P$1, U$182.31
PA31: U$176.P$1, U$182.25
PA31/SWDIO: U$47.P$1, U$76.32
PA31/SWDIO1: U$22.P$1, U$29.32
PA31/SWDIO2: U$59.P$1, U$66.32
PA31/SWDIO3: U$83.P$1, U$90.32
PA31/SWDIO4: U$106.P$1, U$113.32
PA31/SWDIO5: U$129.P$1, U$136.32
PA31/SWDIO6: U$152.P$1, U$159.32
PA31/SWDIO7: U$175.P$1, U$182.32
PA32: U$177.P$1, U$182.27
RESET: C1.1, R1.2, R2.1, U$45.P$1, U$76.26
RESET1: C18.1, R3.2, R5.1, U$20.P$1, U$29.26
RESET2: C47.1, R11.2, R12.1, U$57.P$1, U$66.26
RESET3: C70.1, R16.2, R17.1, U$81.P$1, U$90.26
RESET4: C93.1, R21.2, R22.1, U$104.P$1, U$113.26
RESET5: C116.1, R26.2, R27.1, U$127.P$1, U$136.26
RESET6: C139.1, R31.2, R32.1, U$150.P$1, U$159.26
RESET7: C162.1, R36.2, R37.1, U$173.P$1, U$182.26
RFN: C11.1, U$76.13
RFN1: C39.1, U$29.13
RFN2: C62.1, U$66.13
RFN3: C85.1, U$90.13
RFN4: C108.1, U$113.13
RFN5: C131.1, U$136.13
RFN6: C154.1, U$159.13
RFN7: C177.1, U$182.13
RFP: C12.1, U$76.12
RFP1: C40.1, U$29.12
RFP2: C63.1, U$66.12
RFP3: C86.1, U$90.12
RFP4: C109.1, U$113.12
RFP5: C132.1, U$136.12
RFP6: C155.1, U$159.12
RFP7: C178.1, U$182.12
VDDANA: C8.1, C22.2, L6.2, U$76.4
VDDANA1: C26.1, C35.2, L1.2, U$29.4
VDDANA2: C53.1, C58.2, L2.2, U$66.4
VDDANA3: C76.1, C81.2, L3.2, U$90.4
VDDANA4: C99.1, C104.2, L4.2, U$113.4
VDDANA5: C122.1, C127.2, L5.2, U$136.4
VDDANA6: C145.1, C150.2, L7.2, U$159.4
VDDANA7: C168.1, C173.2, L8.2, U$182.4
VDDCORE: C9.1, U$76.29
VDDCORE1: C27.1, U$29.29
VDDCORE2: C54.1, U$66.29
VDDCORE3: C77.1, U$90.29
VDDCORE4: C100.1, U$113.29
VDDCORE5: C123.1, U$136.29
VDDCORE6: C146.1, U$159.29
VDDCORE7: C169.1, U$182.29
VIN: C6.1, C7.1, LDO_VREG.VIN, U$1.P$1, USB.1
VIN1: C23.1, C24.1, LDO_VREG1.VIN, U$3.P$1, USB1.1
VIN2: C50.1, C51.1, LDO_VREG2.VIN, U$32.P$1, USB2.1
VIN3: C73.1, C74.1, LDO_VREG3.VIN, U$69.P$1, USB3.1
VIN4: C96.1, C97.1, LDO_VREG4.VIN, U$93.P$1, USB4.1
VIN5: C119.1, C120.1, LDO_VREG5.VIN, U$116.P$1, USB5.1
VIN6: C142.1, C143.1, LDO_VREG6.VIN, U$139.P$1, USB6.1
VIN7: C165.1, C166.1, LDO_VREG7.VIN, U$162.P$1, USB7.1
XTALIN: C14.2, SER3628CT-ND.1, U$76.2
XTALIN1: C42.2, SER3628CT-ND1.1, U$29.2
XTALIN2: C65.2, SER3628CT-ND2.1, U$66.2
XTALIN3: C88.2, SER3628CT-ND3.1, U$90.2
XTALIN4: C111.2, SER3628CT-ND4.1, U$113.2
XTALIN5: C134.2, SER3628CT-ND5.1, U$136.2
XTALIN6: C157.2, SER3628CT-ND6.1, U$159.2
XTALIN7: C180.2, SER3628CT-ND7.1, U$182.2
XTALOUT: C15.1, SER3628CT-ND.3, U$76.1
XTALOUT1: C43.1, SER3628CT-ND1.3, U$29.1
XTALOUT2: C66.1, SER3628CT-ND2.3, U$66.1
XTALOUT3: C89.1, SER3628CT-ND3.3, U$90.1
XTALOUT4: C112.1, SER3628CT-ND4.3, U$113.1
XTALOUT5: C135.1, SER3628CT-ND5.3, U$136.1
XTALOUT6: C158.1, SER3628CT-ND6.3, U$159.1
XTALOUT7: C181.1, SER3628CT-ND7.3, U$182.1
