femtoduino/femto-beacon/Eagle_Files/FemtoBeacon_r2.0.0/panel_oshpark_femtoBeacon_r2.0.0.brd

## EAGLE design Eagle_Files/FemtoBeacon_r2.0.0/panel_oshpark_femtoBeacon_r2.0.0.brd (2017-01-18)

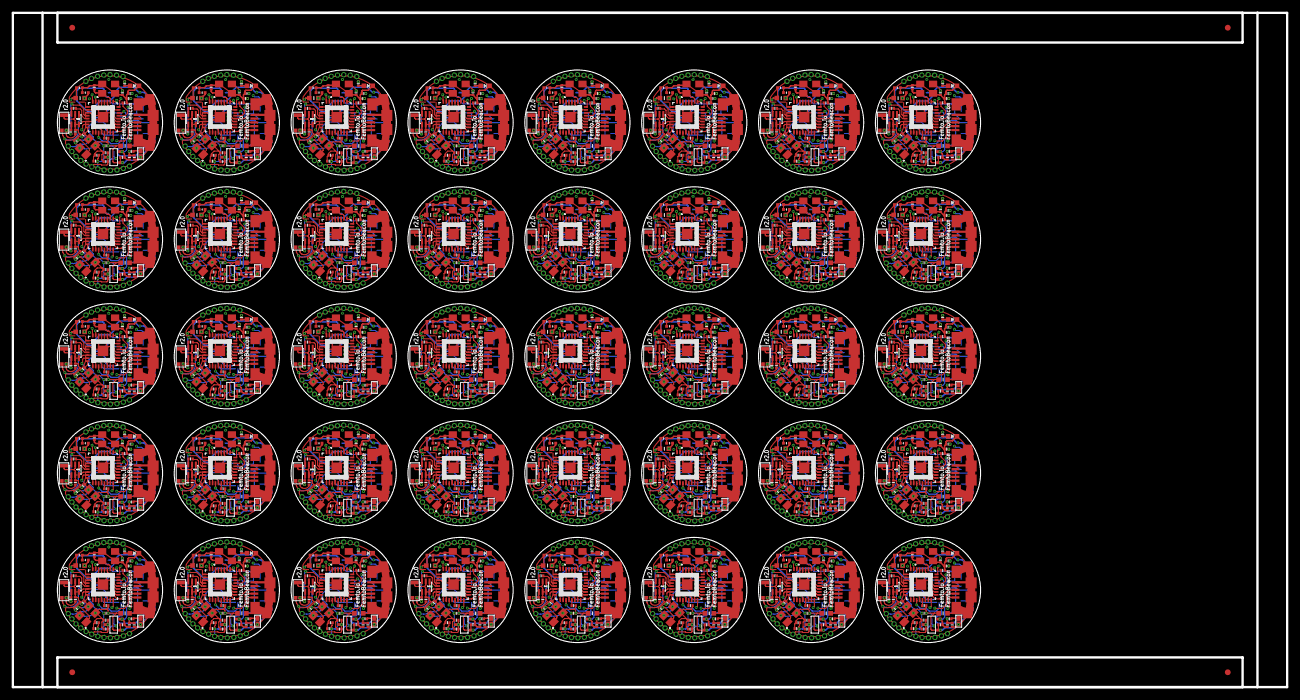
[picture p73: board panel_oshpark_femtoBeacon_r2.0.0.brd from above]

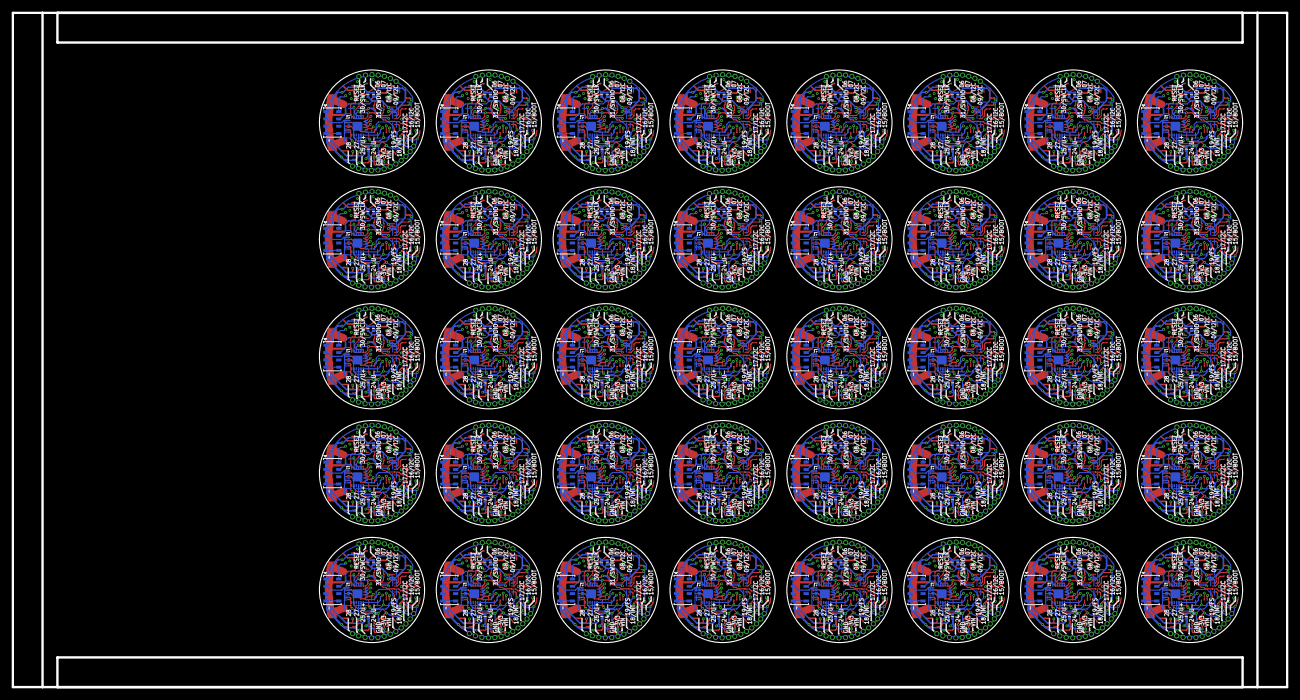
[picture p74: board panel_oshpark_femtoBeacon_r2.0.0.brd from below]

Board: 4 copper layers, 218.1 x 115.4 mm, 2404 parts (280 on the bottom side), 1440 nets.

Parts:
ANT1, ANT2, ANT3, ANT4, ANT5, ANT6, ANT7, ANT8, ANT9, ANT10, ANT11, ANT12, ANT13, ANT14, ANT15, ANT16, ANT17, ANT18, ANT19, ANT20, ANT21, ANT22, ANT23, ANT24, ANT25, ANT26, ANT27, ANT28, ANT29, ANT30, ANT31, ANT32, ANT33, ANT34, ANT35, ANT36, ANT37, ANT38, ANT39, ANT40: PULSE_ANT_2.4GHZ; ANT_BAR
BTN, BTN1, BTN2, BTN3, BTN4, BTN5, BTN6, BTN7, BTN8, BTN9, BTN10, BTN11, BTN12, BTN13, BTN14, BTN15, BTN16, BTN17, BTN18, BTN19, BTN20, BTN21, BTN22, BTN23, BTN24, BTN25, BTN26, BTN27, BTN28, BTN29, BTN30, BTN31, BTN32, BTN33, BTN34, BTN35, BTN36, BTN37, BTN38, BTN39: DNP; SPST_SMD
C1, C2, C8, C9, C10, C16, C17, C18, C19, C25, C26, C27, C28, C29, C30, C32, C33, C36, C45, C46, C47, C48, C52, C53, C54, C55, C56, C59, C68, C69, C70, C71, C75, C76, C77, C78, C79, C82, C91, C92, C93, C94, C98, C99, C100, C101, C102, C105, C114, C115, C116, C117, C121, C122, C123, C124, C125, C128, C137, C138, C139, C140, C144, C145, C146, C147, C148, C151, C160, C161, C162, C163, C167, C168, C169, C170, C171, C174, C183, C184, C185, C186, C190, C191, C192, C193, C194, C197, C206, C207, C208, C209, C213, C214, C215, C216, C217, C220, C229, C230, C231, C232, C236, C237, C238, C239, C240, C243, C252, C253, C254, C255, C259, C260, C261, C262, C263, C266, C275, C276, C277, C278, C282, C283, C284, C285, C286, C289, C298, C299, C300, C301, C305, C306, C307, C308, C309, C312, C321, C322, C323, C324, C328, C329, C330, C331, C332, C335, C344, C345, C346, C347, C351, C352, C353, C354, C355, C358, C367, C368, C369, C370, C374, C375, C376, C377, C378, C381, C390, C391, C392, C393, C397, C398, C399, C400, C401, C404, C413, C414, C415, C416, C420, C421, C422, C423, C424, C427, C436, C437, C438, C439, C443, C444, C445, C446, C447, C450, C459, C460, C461, C462, C466, C467, C468, C469, C470, C473, C482, C483, C484, C485, C489, C490, C491, C492, C493, C496, C505, C506, C507, C508, C512, C513, C514, C515, C516, C519, C528, C529, C530, C531, C535, C536, C537, C538, C539, C542, C551, C552, C553, C554, C558, C559, C560, C561, C562, C565, C574, C575, C576, C577, C581, C582, C583, C584, C585, C588, C597, C598, C599, C600, C604, C605, C606, C607, C608, C611, C620, C621, C622, C623, C627, C628, C629, C630, C631, C634, C643, C644, C645, C646, C650, C651, C652, C653, C654, C657, C666, C667, C668, C669, C673, C674, C675, C676, C677, C680, C689, C690, C691, C692, C696, C697, C698, C699, C700, C703, C712, C713, C714, C715, C719, C720, C721, C722, C723, C726, C735, C736, C737, C738, C742, C743, C744, C745, C746, C749, C758, C759, C760, C761, C765, C766, C767, C768, C769, C772, C781, C782, C783, C784, C788, C789, C790, C791, C792, C795, C804, C805, C806, C807, C811, C812, C813, C814, C815, C818, C827, C828, C829, C830, C834, C835, C836, C837, C838, C841, C850, C851, C852, C853, C857, C858, C859, C860, C861, C864, C873, C874, C875, C876, C880, C881, C882, C883, C884, C887, C896, C897, C898, C899, C903, C904, C905, C906, C907, C910, C919, C920: 0.1uF; PART
C3, C4, C37, C38, C60, C61, C83, C84, C106, C107, C129, C130, C152, C153, C175, C176, C198, C199, C221, C222, C244, C245, C267, C268, C290, C291, C313, C314, C336, C337, C359, C360, C382, C383, C405, C406, C428, C429, C451, C452, C474, C475, C497, C498, C520, C521, C543, C544, C566, C567, C589, C590, C612, C613, C635, C636, C658, C659, C681, C682, C704, C705, C727, C728, C750, C751, C773, C774, C796, C797, C819, C820, C842, C843, C865, C866, C888, C889, C911, C912: 10pF; PART
C5, C6, C20, C23, C49, C50, C72, C73, C95, C96, C118, C119, C141, C142, C164, C165, C187, C188, C210, C211, C233, C234, C256, C257, C279, C280, C302, C303, C325, C326, C348, C349, C371, C372, C394, C395, C417, C418, C440, C441, C463, C464, C486, C487, C509, C510, C532, C533, C555, C556, C578, C579, C601, C602, C624, C625, C647, C648, C670, C671, C693, C694, C716, C717, C739, C740, C762, C763, C785, C786, C808, C809, C831, C832, C854, C855, C877, C878, C900, C901: 2.2uF; PART
C7, C24, C51, C74, C97, C120, C143, C166, C189, C212, C235, C258, C281, C304, C327, C350, C373, C396, C419, C442, C465, C488, C511, C534, C557, C580, C603, C626, C649, C672, C695, C718, C741, C764, C787, C810, C833, C856, C879, C902: 0.47uF; PART
C11, C12, C39, C40, C62, C63, C85, C86, C108, C109, C131, C132, C154, C155, C177, C178, C200, C201, C223, C224, C246, C247, C269, C270, C292, C293, C315, C316, C338, C339, C361, C362, C384, C385, C407, C408, C430, C431, C453, C454, C476, C477, C499, C500, C522, C523, C545, C546, C568, C569, C591, C592, C614, C615, C637, C638, C660, C661, C683, C684, C706, C707, C729, C730, C752, C753, C775, C776, C798, C799, C821, C822, C844, C845, C867, C868, C890, C891, C913, C914: 22pF, C0G, 5%; PART
C13, C41, C64, C87, C110, C133, C156, C179, C202, C225, C248, C271, C294, C317, C340, C363, C386, C409, C432, C455, C478, C501, C524, C547, C570, C593, C616, C639, C662, C685, C708, C731, C754, C777, C800, C823, C846, C869, C892, C915: DNP; PART
C14, C15, C42, C43, C65, C66, C88, C89, C111, C112, C134, C135, C157, C158, C180, C181, C203, C204, C226, C227, C249, C250, C272, C273, C295, C296, C318, C319, C341, C342, C364, C365, C387, C388, C410, C411, C433, C434, C456, C457, C479, C480, C502, C503, C525, C526, C548, C549, C571, C572, C594, C595, C617, C618, C640, C641, C663, C664, C686, C687, C709, C710, C732, C733, C755, C756, C778, C779, C801, C802, C824, C825, C847, C848, C870, C871, C893, C894, C916, C917: 9pF; PART
C21, C22, C34, C35, C57, C58, C80, C81, C103, C104, C126, C127, C149, C150, C172, C173, C195, C196, C218, C219, C241, C242, C264, C265, C287, C288, C310, C311, C333, C334, C356, C357, C379, C380, C402, C403, C425, C426, C448, C449, C471, C472, C494, C495, C517, C518, C540, C541, C563, C564, C586, C587, C609, C610, C632, C633, C655, C656, C678, C679, C701, C702, C724, C725, C747, C748, C770, C771, C793, C794, C816, C817, C839, C840, C862, C863, C885, C886, C908, C909: 10uF; _0402MP
C31, C44, C67, C90, C113, C136, C159, C182, C205, C228, C251, C274, C297, C320, C343, C366, C389, C412, C435, C458, C481, C504, C527, C550, C573, C596, C619, C642, C665, C688, C711, C734, C757, C780, C803, C826, C849, C872, C895, C918: 10nF; PART
FB1, FB2, FB3, FB4, FB5, FB6, FB7, FB8, FB9, FB10, FB11, FB12, FB13, FB14, FB15, FB16, FB17, FB18, FB19, FB20, FB21, FB22, FB23, FB24, FB25, FB26, FB27, FB28, FB29, FB30, FB31, FB32, FB33, FB34, FB35, FB36, FB37, FB38, FB39, FB40: _0603MP
FIDUCIAL1, FIDUCIAL2, FIDUCIAL3, FIDUCIAL4: FIDUCIAL_1MM
L1, L2, L3, L4, L5, L6, L7, L8, L9, L10, L11, L12, L13, L14, L15, L16, L17, L18, L19, L20, L21, L22, L23, L24, L25, L26, L27, L28, L29, L30, L31, L32, L33, L34, L35, L36, L37, L38, L39, L40: 10uH; _0603MP
LDO_VREG, LDO_VREG1, LDO_VREG2, LDO_VREG3, LDO_VREG4, LDO_VREG5, LDO_VREG6, LDO_VREG7, LDO_VREG8, LDO_VREG9, LDO_VREG10, LDO_VREG11, LDO_VREG12, LDO_VREG13, LDO_VREG14, LDO_VREG15, LDO_VREG16, LDO_VREG17, LDO_VREG18, LDO_VREG19, LDO_VREG20, LDO_VREG21, LDO_VREG22, LDO_VREG23, LDO_VREG24, LDO_VREG25, LDO_VREG26, LDO_VREG27, LDO_VREG28, LDO_VREG29, LDO_VREG30, LDO_VREG31, LDO_VREG32, LDO_VREG33, LDO_VREG34, LDO_VREG35, LDO_VREG36, LDO_VREG37, LDO_VREG38, LDO_VREG39: MCP1700T-3302E/TT
LED1, LED2, LED3, LED4, LED5, LED6, LED7, LED8, LED9, LED10, LED11, LED12, LED13, LED14, LED15, LED16, LED17, LED18, LED19, LED20, LED21, LED22, LED23, LED24, LED25, LED26, LED27, LED28, LED29, LED30, LED31, LED32, LED33, LED34, LED35, LED36, LED37, LED38, LED39, LED40: BLUE; CHIPLED_0603_NOOUTLINE
R1, R3, R4, R6, R11, R13, R16, R18, R21, R23, R26, R28, R31, R33, R36, R38, R41, R43, R46, R48, R51, R53, R56, R58, R61, R63, R66, R68, R71, R73, R76, R78, R81, R83, R86, R88, R91, R93, R96, R98, R101, R103, R106, R108, R111, R113, R116, R118, R121, R123, R126, R128, R131, R133, R136, R138, R141, R143, R146, R148, R151, R153, R156, R158, R161, R163, R166, R168, R171, R173, R176, R178, R181, R183, R186, R188, R191, R193, R196, R198: 330; PART
R2, R5, R12, R17, R22, R27, R32, R37, R42, R47, R52, R57, R62, R67, R72, R77, R82, R87, R92, R97, R102, R107, R112, R117, R122, R127, R132, R137, R142, R147, R152, R157, R162, R167, R172, R177, R182, R187, R192, R197: 10K; PART
R7, R8, R9, R10, R14, R15, R19, R20, R24, R25, R29, R30, R34, R35, R39, R40, R44, R45, R49, R50, R54, R55, R59, R60, R64, R65, R69, R70, R74, R75, R79, R80, R84, R85, R89, R90, R94, R95, R99, R100, R104, R105, R109, R110, R114, R115, R119, R120, R124, R125, R129, R130, R134, R135, R139, R140, R144, R145, R149, R150, R154, R155, R159, R160, R164, R165, R169, R170, R174, R175, R179, R180, R184, R185, R189, R190, R194, R195, R199, R200: 2.2K; PART
SER3628CT-ND, SER3628CT-ND1, SER3628CT-ND2, SER3628CT-ND3, SER3628CT-ND4, SER3628CT-ND5, SER3628CT-ND6, SER3628CT-ND7, SER3628CT-ND8, SER3628CT-ND9, SER3628CT-ND10, SER3628CT-ND11, SER3628CT-ND12, SER3628CT-ND13, SER3628CT-ND14, SER3628CT-ND15, SER3628CT-ND16, SER3628CT-ND17, SER3628CT-ND18, SER3628CT-ND19, SER3628CT-ND20, SER3628CT-ND21, SER3628CT-ND22, SER3628CT-ND23, SER3628CT-ND24, SER3628CT-ND25, SER3628CT-ND26, SER3628CT-ND27, SER3628CT-ND28, SER3628CT-ND29, SER3628CT-ND30, SER3628CT-ND31, SER3628CT-ND32, SER3628CT-ND33, SER3628CT-ND34, SER3628CT-ND35, SER3628CT-ND36, SER3628CT-ND37, SER3628CT-ND38, SER3628CT-ND39: 16MHz; TSX-3225
TSX-3225_CRYSTAL, TSX-3225_CRYSTAL1, TSX-3225_CRYSTAL2, TSX-3225_CRYSTAL3, TSX-3225_CRYSTAL4, TSX-3225_CRYSTAL5, TSX-3225_CRYSTAL6, TSX-3225_CRYSTAL7, TSX-3225_CRYSTAL8, TSX-3225_CRYSTAL9, TSX-3225_CRYSTAL10, TSX-3225_CRYSTAL11, TSX-3225_CRYSTAL12, TSX-3225_CRYSTAL13, TSX-3225_CRYSTAL14, TSX-3225_CRYSTAL15, TSX-3225_CRYSTAL16, TSX-3225_CRYSTAL17, TSX-3225_CRYSTAL18, TSX-3225_CRYSTAL19, TSX-3225_CRYSTAL20, TSX-3225_CRYSTAL21, TSX-3225_CRYSTAL22, TSX-3225_CRYSTAL23, TSX-3225_CRYSTAL24, TSX-3225_CRYSTAL25, TSX-3225_CRYSTAL26, TSX-3225_CRYSTAL27, TSX-3225_CRYSTAL28, TSX-3225_CRYSTAL29, TSX-3225_CRYSTAL30, TSX-3225_CRYSTAL31, TSX-3225_CRYSTAL32, TSX-3225_CRYSTAL33, TSX-3225_CRYSTAL34, TSX-3225_CRYSTAL35, TSX-3225_CRYSTAL36, TSX-3225_CRYSTAL37, TSX-3225_CRYSTAL38, TSX-3225_CRYSTAL39: 48MHz; TSX-3225
U$1, U$2, U$3, U$4, U$5, U$7, U$8, U$9, U$10, U$11, U$13, U$14, U$15, U$16, U$17, U$18, U$19, U$20, U$21, U$22, U$23, U$24, U$25, U$26, U$27, U$32, U$33, U$34, U$35, U$36, U$37, U$38, U$39, U$40, U$41, U$42, U$43, U$45, U$46, U$47, U$48, U$49, U$50, U$51, U$52, U$53, U$54, U$55, U$56, U$57, U$58, U$59, U$60, U$61, U$62, U$63, U$64, U$69, U$70, U$71, U$72, U$73, U$74, U$75, U$77, U$78, U$79, U$80, U$81, U$82, U$83, U$84, U$85, U$86, U$87, U$88, U$93, U$94, U$95, U$96, U$97, U$98, U$99, U$100, U$101, U$102, U$103, U$104, U$105, U$106, U$107, U$108, U$109, U$110, U$111, U$116, U$117, U$118, U$119, U$120, U$121, U$122, U$123, U$124, U$125, U$126, U$127, U$128, U$129, U$130, U$131, U$132, U$133, U$134, U$139, U$140, U$141, U$142, U$143, U$144, U$145, U$146, U$147, U$148, U$149, U$150, U$151, U$152, U$153, U$154, U$155, U$156, U$157, U$162, U$163, U$164, U$165, U$166, U$167, U$168, U$169, U$170, U$171, U$172, U$173, U$174, U$175, U$176, U$177, U$178, U$179, U$180, U$185, U$186, U$187, U$188, U$189, U$190, U$191, U$192, U$193, U$194, U$195, U$196, U$197, U$198, U$199, U$200, U$201, U$202, U$203, U$208, U$209, U$210, U$211, U$212, U$213, U$214, U$215, U$216, U$217, U$218, U$219, U$220, U$221, U$222, U$223, U$224, U$225, U$226, U$231, U$232, U$233, U$234, U$235, U$236, U$237, U$238, U$239, U$240, U$241, U$242, U$243, U$244, U$245, U$246, U$247, U$248, U$249, U$254, U$255, U$256, U$257, U$258, U$259, U$260, U$261, U$262, U$263, U$264, U$265, U$266, U$267, U$268, U$269, U$270, U$271, U$272, U$277, U$278, U$279, U$280, U$281, U$282, U$283, U$284, U$285, U$286, U$287, U$288, U$289, U$290, U$291, U$292, U$293, U$294, U$295, U$300, U$301, U$302, U$303, U$304, U$305, U$306, U$307, U$308, U$309, U$310, U$311, U$312, U$313, U$314, U$315, U$316, U$317, U$318, U$323, U$324, U$325, U$326, U$327, U$328, U$329, U$330, U$331, U$332, U$333, U$334, U$335, U$336, U$337, U$338, U$339, U$340, U$341, U$346, U$347, U$348, U$349, U$350, U$351, U$352, U$353, U$354, U$355, U$356, U$357, U$358, U$359, U$360, U$361, U$362, U$363, U$364, U$369, U$370, U$371, U$372, U$373, U$374, U$375, U$376, U$377, U$378, U$379, U$380, U$381, U$382, U$383, U$384, U$385, U$386, U$387, U$392, U$393, U$394, U$395, U$396, U$397, U$398, U$399, U$400, U$401, U$402, U$403, U$404, U$405, U$406, U$407, U$408, U$409, U$410, U$415, U$416, U$417, U$418, U$419, U$420, U$421, U$422, U$423, U$424, U$425, U$426, U$427, U$428, U$429, U$430, U$431, U$432, U$433, U$438, U$439, U$440, U$441, U$442, U$443, U$444, U$445, U$446, U$447, U$448, U$449, U$450, U$451, U$452, U$453, U$454, U$455, U$456, U$461, U$462, U$463, U$464, U$465, U$466, U$467, U$468, U$469, U$470, U$471, U$472, U$473, U$474, U$475, U$476, U$477, U$478, U$479, U$484, U$485, U$486, U$487, U$488, U$489, U$490, U$491, U$492, U$493, U$494, U$495, U$496, U$497, U$498, U$499, U$500, U$501, U$502, U$507, U$508, U$509, U$510, U$511, U$512, U$513, U$514, U$515, U$516, U$517, U$518, U$519, U$520, U$521, U$522, U$523, U$524, U$525, U$530, U$531, U$532, U$533, U$534, U$535, U$536, U$537, U$538, U$539, U$540, U$541, U$542, U$543, U$544, U$545, U$546, U$547, U$548, U$553, U$554, U$555, U$556, U$557, U$558, U$559, U$560, U$561, U$562, U$563, U$564, U$565, U$566, U$567, U$568, U$569, U$570, U$571, U$576, U$577, U$578, U$579, U$580, U$581, U$582, U$583, U$584, U$585, U$586, U$587, U$588, U$589, U$590, U$591, U$592, U$593, U$594, U$599, U$600, U$601, U$602, U$603, U$604, U$605, U$606, U$607, U$608, U$609, U$610, U$611, U$612, U$613, U$614, U$615, U$616, U$617, U$622, U$623, U$624, U$625, U$626, U$627, U$628, U$629, U$630, U$631, U$632, U$633, U$634, U$635, U$636, U$637, U$638, U$639, U$640, U$645, U$646, U$647, U$648, U$649, U$650, U$651, U$652, U$653, U$654, U$655, U$656, U$657, U$658, U$659, U$660, U$661, U$662, U$663, U$668, U$669, U$670, U$671, U$672, U$673, U$674, U$675, U$676, U$677, U$678, U$679, U$680, U$681, U$682, U$683, U$684, U$685, U$686, U$691, U$692, U$693, U$694, U$695, U$696, U$697, U$698, U$699, U$700, U$701, U$702, U$703, U$704, U$705, U$706, U$707, U$708, U$709, U$714, U$715, U$716, U$717, U$718, U$719, U$720, U$721, U$722, U$723, U$724, U$725, U$726, U$727, U$728, U$729, U$730, U$731, U$732, U$737, U$738, U$739, U$740, U$741, U$742, U$743, U$744, U$745, U$746, U$747, U$748, U$749, U$750, U$751, U$752, U$753, U$754, U$755, U$760, U$761, U$762, U$763, U$764, U$765, U$766, U$767, U$768, U$769, U$770, U$771, U$772, U$773, U$774, U$775, U$776, U$777, U$778, U$783, U$784, U$785, U$786, U$787, U$788, U$789, U$790, U$791, U$792, U$793, U$794, U$795, U$796, U$797, U$798, U$799, U$800, U$801, U$806, U$807, U$808, U$809, U$810, U$811, U$812, U$813, U$814, U$815, U$816, U$817, U$818, U$819, U$820, U$821, U$822, U$823, U$824, U$829, U$830, U$831, U$832, U$833, U$834, U$835, U$836, U$837, U$838, U$839, U$840, U$841, U$842, U$843, U$844, U$845, U$846, U$847, U$852, U$853, U$854, U$855, U$856, U$857, U$858, U$859, U$860, U$861, U$862, U$863, U$864, U$865, U$866, U$867, U$868, U$869, U$870, U$875, U$876, U$877, U$878, U$879, U$880, U$881, U$882, U$883, U$884, U$885, U$886, U$887, U$888, U$889, U$890, U$891, U$892, U$893, U$898, U$899, U$900, U$901, U$902, U$903, U$904, U$905, U$906, U$907, U$908, U$909, U$910, U$911, U$912, U$913, U$914, U$915, U$916: 1X1_ROUND
U$6, U$31, U$68, U$92, U$115, U$138, U$161, U$184, U$207, U$230, U$253, U$276, U$299, U$322, U$345, U$368, U$391, U$414, U$437, U$460, U$483, U$506, U$529, U$552, U$575, U$598, U$621, U$644, U$667, U$690, U$713, U$736, U$759, U$782, U$805, U$828, U$851, U$874, U$897, U$920: MPU-9250; QFN_3X3MM
U$12, U$30, U$67, U$91, U$114, U$137, U$160, U$183, U$206, U$229, U$252, U$275, U$298, U$321, U$344, U$367, U$390, U$413, U$436, U$459, U$482, U$505, U$528, U$551, U$574, U$597, U$620, U$643, U$666, U$689, U$712, U$735, U$758, U$781, U$804, U$827, U$850, U$873, U$896, U$919: JOHANSON_2450BM15A0015E; 0805_BALUN
U$28, U$44, U$65, U$89, U$112, U$135, U$158, U$181, U$204, U$227, U$250, U$273, U$296, U$319, U$342, U$365, U$388, U$411, U$434, U$457, U$480, U$503, U$526, U$549, U$572, U$595, U$618, U$641, U$664, U$687, U$710, U$733, U$756, U$779, U$802, U$825, U$848, U$871, U$894, U$917: MS5611-01BA03
U$29, U$66, U$76, U$90, U$113, U$136, U$159, U$182, U$205, U$228, U$251, U$274, U$297, U$320, U$343, U$366, U$389, U$412, U$435, U$458, U$481, U$504, U$527, U$550, U$573, U$596, U$619, U$642, U$665, U$688, U$711, U$734, U$757, U$780, U$803, U$826, U$849, U$872, U$895, U$918: ATSAMR21E18A-MUT; QFN32
USB, USB1, USB2, USB3, USB4, USB5, USB6, USB7, USB8, USB9, USB10, USB11, USB12, USB13, USB14, USB15, USB16, USB17, USB18, USB19, USB20, USB21, USB22, USB23, USB24, USB25, USB26, USB27, USB28, USB29, USB30, USB31, USB32, USB33, USB34, USB35, USB36, USB37, USB38, USB39: USB_MICROB; USB_MICROB_PACKAGE

Connections:
3.3V: C5.1, C10.1, C16.1, C21.2, C29.1, C30.2, C31.2, L6.1, LDO_VREG.VOUT, R2.2, R8.2, R9.2, U$5.P$1, U$6.P$1, U$6.P$8, U$6.P$13, U$6.P$22, U$44.1, U$44.2, U$76.24, U$76.30
3.3V1: C20.1, C25.1, C28.1, C34.2, C36.1, C44.2, C45.2, L1.1, LDO_VREG1.VOUT, R5.2, R7.2, R10.2, U$8.P$1, U$28.1, U$28.2, U$29.24, U$29.30, U$31.P$1, U$31.P$8, U$31.P$13, U$31.P$22
3.3V2: C49.1, C52.1, C55.1, C57.2, C59.1, C67.2, C68.2, L2.1, LDO_VREG2.VOUT, R12.2, R14.2, R15.2, U$34.P$1, U$65.1, U$65.2, U$66.24, U$66.30, U$68.P$1, U$68.P$8, U$68.P$13, U$68.P$22
3.3V3: C72.1, C75.1, C78.1, C80.2, C82.1, C90.2, C91.2, L3.1, LDO_VREG3.VOUT, R17.2, R19.2, R20.2, U$71.P$1, U$89.1, U$89.2, U$90.24, U$90.30, U$92.P$1, U$92.P$8, U$92.P$13, U$92.P$22
3.3V4: C95.1, C98.1, C101.1, C103.2, C105.1, C113.2, C114.2, L4.1, LDO_VREG4.VOUT, R22.2, R24.2, R25.2, U$95.P$1, U$112.1, U$112.2, U$113.24, U$113.30, U$115.P$1, U$115.P$8, U$115.P$13, U$115.P$22
3.3V5: C118.1, C121.1, C124.1, C126.2, C128.1, C136.2, C137.2, L5.1, LDO_VREG5.VOUT, R27.2, R29.2, R30.2, U$118.P$1, U$135.1, U$135.2, U$136.24, U$136.30, U$138.P$1, U$138.P$8, U$138.P$13, U$138.P$22
3.3V6: C141.1, C144.1, C147.1, C149.2, C151.1, C159.2, C160.2, L7.1, LDO_VREG6.VOUT, R32.2, R34.2, R35.2, U$141.P$1, U$158.1, U$158.2, U$159.24, U$159.30, U$161.P$1, U$161.P$8, U$161.P$13, U$161.P$22
3.3V7: C164.1, C167.1, C170.1, C172.2, C174.1, C182.2, C183.2, L8.1, LDO_VREG7.VOUT, R37.2, R39.2, R40.2, U$164.P$1, U$181.1, U$181.2, U$182.24, U$182.30, U$184.P$1, U$184.P$8, U$184.P$13, U$184.P$22
3.3V8: C187.1, C190.1, C193.1, C195.2, C197.1, C205.2, C206.2, L9.1, LDO_VREG8.VOUT, R42.2, R44.2, R45.2, U$187.P$1, U$204.1, U$204.2, U$205.24, U$205.30, U$207.P$1, U$207.P$8, U$207.P$13, U$207.P$22
3.3V9: C210.1, C213.1, C216.1, C218.2, C220.1, C228.2, C229.2, L10.1, LDO_VREG9.VOUT, R47.2, R49.2, R50.2, U$210.P$1, U$227.1, U$227.2, U$228.24, U$228.30, U$230.P$1, U$230.P$8, U$230.P$13, U$230.P$22
3.3V10: C233.1, C236.1, C239.1, C241.2, C243.1, C251.2, C252.2, L11.1, LDO_VREG10.VOUT, R52.2, R54.2, R55.2, U$233.P$1, U$250.1, U$250.2, U$251.24, U$251.30, U$253.P$1, U$253.P$8, U$253.P$13, U$253.P$22
3.3V11: C256.1, C259.1, C262.1, C264.2, C266.1, C274.2, C275.2, L12.1, LDO_VREG11.VOUT, R57.2, R59.2, R60.2, U$256.P$1, U$273.1, U$273.2, U$274.24, U$274.30, U$276.P$1, U$276.P$8, U$276.P$13, U$276.P$22
3.3V12: C279.1, C282.1, C285.1, C287.2, C289.1, C297.2, C298.2, L13.1, LDO_VREG12.VOUT, R62.2, R64.2, R65.2, U$279.P$1, U$296.1, U$296.2, U$297.24, U$297.30, U$299.P$1, U$299.P$8, U$299.P$13, U$299.P$22
3.3V13: C302.1, C305.1, C308.1, C310.2, C312.1, C320.2, C321.2, L14.1, LDO_VREG13.VOUT, R67.2, R69.2, R70.2, U$302.P$1, U$319.1, U$319.2, U$320.24, U$320.30, U$322.P$1, U$322.P$8, U$322.P$13, U$322.P$22
3.3V14: C325.1, C328.1, C331.1, C333.2, C335.1, C343.2, C344.2, L15.1, LDO_VREG14.VOUT, R72.2, R74.2, R75.2, U$325.P$1, U$342.1, U$342.2, U$343.24, U$343.30, U$345.P$1, U$345.P$8, U$345.P$13, U$345.P$22
3.3V15: C348.1, C351.1, C354.1, C356.2, C358.1, C366.2, C367.2, L16.1, LDO_VREG15.VOUT, R77.2, R79.2, R80.2, U$348.P$1, U$365.1, U$365.2, U$366.24, U$366.30, U$368.P$1, U$368.P$8, U$368.P$13, U$368.P$22
3.3V16: C371.1, C374.1, C377.1, C379.2, C381.1, C389.2, C390.2, L17.1, LDO_VREG16.VOUT, R82.2, R84.2, R85.2, U$371.P$1, U$388.1, U$388.2, U$389.24, U$389.30, U$391.P$1, U$391.P$8, U$391.P$13, U$391.P$22
3.3V17: C394.1, C397.1, C400.1, C402.2, C404.1, C412.2, C413.2, L18.1, LDO_VREG17.VOUT, R87.2, R89.2, R90.2, U$394.P$1, U$411.1, U$411.2, U$412.24, U$412.30, U$414.P$1, U$414.P$8, U$414.P$13, U$414.P$22
3.3V18: C417.1, C420.1, C423.1, C425.2, C427.1, C435.2, C436.2, L19.1, LDO_VREG18.VOUT, R92.2, R94.2, R95.2, U$417.P$1, U$434.1, U$434.2, U$435.24, U$435.30, U$437.P$1, U$437.P$8, U$437.P$13, U$437.P$22
3.3V19: C440.1, C443.1, C446.1, C448.2, C450.1, C458.2, C459.2, L20.1, LDO_VREG19.VOUT, R97.2, R99.2, R100.2, U$440.P$1, U$457.1, U$457.2, U$458.24, U$458.30, U$460.P$1, U$460.P$8, U$460.P$13, U$460.P$22
3.3V20: C463.1, C466.1, C469.1, C471.2, C473.1, C481.2, C482.2, L21.1, LDO_VREG20.VOUT, R102.2, R104.2, R105.2, U$463.P$1, U$480.1, U$480.2, U$481.24, U$481.30, U$483.P$1, U$483.P$8, U$483.P$13, U$483.P$22
3.3V21: C486.1, C489.1, C492.1, C494.2, C496.1, C504.2, C505.2, L22.1, LDO_VREG21.VOUT, R107.2, R109.2, R110.2, U$486.P$1, U$503.1, U$503.2, U$504.24, U$504.30, U$506.P$1, U$506.P$8, U$506.P$13, U$506.P$22
3.3V22: C509.1, C512.1, C515.1, C517.2, C519.1, C527.2, C528.2, L23.1, LDO_VREG22.VOUT, R112.2, R114.2, R115.2, U$509.P$1, U$526.1, U$526.2, U$527.24, U$527.30, U$529.P$1, U$529.P$8, U$529.P$13, U$529.P$22
3.3V23: C532.1, C535.1, C538.1, C540.2, C542.1, C550.2, C551.2, L24.1, LDO_VREG23.VOUT, R117.2, R119.2, R120.2, U$532.P$1, U$549.1, U$549.2, U$550.24, U$550.30, U$552.P$1, U$552.P$8, U$552.P$13, U$552.P$22
3.3V24: C555.1, C558.1, C561.1, C563.2, C565.1, C573.2, C574.2, L25.1, LDO_VREG24.VOUT, R122.2, R124.2, R125.2, U$555.P$1, U$572.1, U$572.2, U$573.24, U$573.30, U$575.P$1, U$575.P$8, U$575.P$13, U$575.P$22
3.3V25: C578.1, C581.1, C584.1, C586.2, C588.1, C596.2, C597.2, L26.1, LDO_VREG25.VOUT, R127.2, R129.2, R130.2, U$578.P$1, U$595.1, U$595.2, U$596.24, U$596.30, U$598.P$1, U$598.P$8, U$598.P$13, U$598.P$22
3.3V26: C601.1, C604.1, C607.1, C609.2, C611.1, C619.2, C620.2, L27.1, LDO_VREG26.VOUT, R132.2, R134.2, R135.2, U$601.P$1, U$618.1, U$618.2, U$619.24, U$619.30, U$621.P$1, U$621.P$8, U$621.P$13, U$621.P$22
3.3V27: C624.1, C627.1, C630.1, C632.2, C634.1, C642.2, C643.2, L28.1, LDO_VREG27.VOUT, R137.2, R139.2, R140.2, U$624.P$1, U$641.1, U$641.2, U$642.24, U$642.30, U$644.P$1, U$644.P$8, U$644.P$13, U$644.P$22
3.3V28: C647.1, C650.1, C653.1, C655.2, C657.1, C665.2, C666.2, L29.1, LDO_VREG28.VOUT, R142.2, R144.2, R145.2, U$647.P$1, U$664.1, U$664.2, U$665.24, U$665.30, U$667.P$1, U$667.P$8, U$667.P$13, U$667.P$22
3.3V29: C670.1, C673.1, C676.1, C678.2, C680.1, C688.2, C689.2, L30.1, LDO_VREG29.VOUT, R147.2, R149.2, R150.2, U$670.P$1, U$687.1, U$687.2, U$688.24, U$688.30, U$690.P$1, U$690.P$8, U$690.P$13, U$690.P$22
3.3V30: C693.1, C696.1, C699.1, C701.2, C703.1, C711.2, C712.2, L31.1, LDO_VREG30.VOUT, R152.2, R154.2, R155.2, U$693.P$1, U$710.1, U$710.2, U$711.24, U$711.30, U$713.P$1, U$713.P$8, U$713.P$13, U$713.P$22
3.3V31: C716.1, C719.1, C722.1, C724.2, C726.1, C734.2, C735.2, L32.1, LDO_VREG31.VOUT, R157.2, R159.2, R160.2, U$716.P$1, U$733.1, U$733.2, U$734.24, U$734.30, U$736.P$1, U$736.P$8, U$736.P$13, U$736.P$22
3.3V32: C739.1, C742.1, C745.1, C747.2, C749.1, C757.2, C758.2, L33.1, LDO_VREG32.VOUT, R162.2, R164.2, R165.2, U$739.P$1, U$756.1, U$756.2, U$757.24, U$757.30, U$759.P$1, U$759.P$8, U$759.P$13, U$759.P$22
3.3V33: C762.1, C765.1, C768.1, C770.2, C772.1, C780.2, C781.2, L34.1, LDO_VREG33.VOUT, R167.2, R169.2, R170.2, U$762.P$1, U$779.1, U$779.2, U$780.24, U$780.30, U$782.P$1, U$782.P$8, U$782.P$13, U$782.P$22
3.3V34: C785.1, C788.1, C791.1, C793.2, C795.1, C803.2, C804.2, L35.1, LDO_VREG34.VOUT, R172.2, R174.2, R175.2, U$785.P$1, U$802.1, U$802.2, U$803.24, U$803.30, U$805.P$1, U$805.P$8, U$805.P$13, U$805.P$22
3.3V35: C808.1, C811.1, C814.1, C816.2, C818.1, C826.2, C827.2, L36.1, LDO_VREG35.VOUT, R177.2, R179.2, R180.2, U$808.P$1, U$825.1, U$825.2, U$826.24, U$826.30, U$828.P$1, U$828.P$8, U$828.P$13, U$828.P$22
3.3V36: C831.1, C834.1, C837.1, C839.2, C841.1, C849.2, C850.2, L37.1, LDO_VREG36.VOUT, R182.2, R184.2, R185.2, U$831.P$1, U$848.1, U$848.2, U$849.24, U$849.30, U$851.P$1, U$851.P$8, U$851.P$13, U$851.P$22
3.3V37: C854.1, C857.1, C860.1, C862.2, C864.1, C872.2, C873.2, L38.1, LDO_VREG37.VOUT, R187.2, R189.2, R190.2, U$854.P$1, U$871.1, U$871.2, U$872.24, U$872.30, U$874.P$1, U$874.P$8, U$874.P$13, U$874.P$22
3.3V38: C877.1, C880.1, C883.1, C885.2, C887.1, C895.2, C896.2, L39.1, LDO_VREG38.VOUT, R192.2, R194.2, R195.2, U$877.P$1, U$894.1, U$894.2, U$895.24, U$895.30, U$897.P$1, U$897.P$8, U$897.P$13, U$897.P$22
3.3V39: C900.1, C903.1, C906.1, C908.2, C910.1, C918.2, C919.2, L40.1, LDO_VREG39.VOUT, R197.2, R199.2, R200.2, U$900.P$1, U$917.1, U$917.2, U$918.24, U$918.30, U$920.P$1, U$920.P$8, U$920.P$13, U$920.P$22
ANT_OUT: ANT1.1, U$12.1
ANT_OUT1: ANT2.1, U$30.1
ANT_OUT2: ANT3.1, U$67.1
ANT_OUT3: ANT4.1, U$91.1
ANT_OUT4: ANT5.1, U$114.1
ANT_OUT5: ANT6.1, U$137.1
ANT_OUT6: ANT7.1, U$160.1
ANT_OUT7: ANT8.1, U$183.1
ANT_OUT8: ANT9.1, U$206.1
ANT_OUT9: ANT10.1, U$229.1
ANT_OUT10: ANT11.1, U$252.1
ANT_OUT11: ANT12.1, U$275.1
ANT_OUT12: ANT13.1, U$298.1
ANT_OUT13: ANT14.1, U$321.1
ANT_OUT14: ANT15.1, U$344.1
ANT_OUT15: ANT16.1, U$367.1
ANT_OUT16: ANT17.1, U$390.1
ANT_OUT17: ANT18.1, U$413.1
ANT_OUT18: ANT19.1, U$436.1
ANT_OUT19: ANT20.1, U$459.1
ANT_OUT20: ANT21.1, U$482.1
ANT_OUT21: ANT22.1, U$505.1
ANT_OUT22: ANT23.1, U$528.1
ANT_OUT23: ANT24.1, U$551.1
ANT_OUT24: ANT25.1, U$574.1
ANT_OUT25: ANT26.1, U$597.1
ANT_OUT26: ANT27.1, U$620.1
ANT_OUT27: ANT28.1, U$643.1
ANT_OUT28: ANT29.1, U$666.1
ANT_OUT29: ANT30.1, U$689.1
ANT_OUT30: ANT31.1, U$712.1
ANT_OUT31: ANT32.1, U$735.1
ANT_OUT32: ANT33.1, U$758.1
ANT_OUT33: ANT34.1, U$781.1
ANT_OUT34: ANT35.1, U$804.1
ANT_OUT35: ANT36.1, U$827.1
ANT_OUT36: ANT37.1, U$850.1
ANT_OUT37: ANT38.1, U$873.1
ANT_OUT38: ANT39.1, U$896.1
ANT_OUT39: ANT40.1, U$919.1
AVDD: C17.1, U$76.5
AVDD1: C33.1, U$29.5
AVDD2: C56.1, U$66.5
AVDD3: C79.1, U$90.5
AVDD4: C102.1, U$113.5
AVDD5: C125.1, U$136.5
AVDD6: C148.1, U$159.5
AVDD7: C171.1, U$182.5
AVDD8: C194.1, U$205.5
AVDD9: C217.1, U$228.5
AVDD10: C240.1, U$251.5
AVDD11: C263.1, U$274.5
AVDD12: C286.1, U$297.5
AVDD13: C309.1, U$320.5
AVDD14: C332.1, U$343.5
AVDD15: C355.1, U$366.5
AVDD16: C378.1, U$389.5
AVDD17: C401.1, U$412.5
AVDD18: C424.1, U$435.5
AVDD19: C447.1, U$458.5
AVDD20: C470.1, U$481.5
AVDD21: C493.1, U$504.5
AVDD22: C516.1, U$527.5
AVDD23: C539.1, U$550.5
AVDD24: C562.1, U$573.5
AVDD25: C585.1, U$596.5
AVDD26: C608.1, U$619.5
AVDD27: C631.1, U$642.5
AVDD28: C654.1, U$665.5
AVDD29: C677.1, U$688.5
AVDD30: C700.1, U$711.5
AVDD31: C723.1, U$734.5
AVDD32: C746.1, U$757.5
AVDD33: C769.1, U$780.5
AVDD34: C792.1, U$803.5
AVDD35: C815.1, U$826.5
AVDD36: C838.1, U$849.5
AVDD37: C861.1, U$872.5
AVDD38: C884.1, U$895.5
AVDD39: C907.1, U$918.5
DVDD: C2.1, U$76.21
DVDD1: C19.1, U$29.21
DVDD2: C48.1, U$66.21
DVDD3: C71.1, U$90.21
DVDD4: C94.1, U$113.21
DVDD5: C117.1, U$136.21
DVDD6: C140.1, U$159.21
DVDD7: C163.1, U$182.21
DVDD8: C186.1, U$205.21
DVDD9: C209.1, U$228.21
DVDD10: C232.1, U$251.21
DVDD11: C255.1, U$274.21
DVDD12: C278.1, U$297.21
DVDD13: C301.1, U$320.21
DVDD14: C324.1, U$343.21
DVDD15: C347.1, U$366.21
DVDD16: C370.1, U$389.21
DVDD17: C393.1, U$412.21
DVDD18: C416.1, U$435.21
DVDD19: C439.1, U$458.21
DVDD20: C462.1, U$481.21
DVDD21: C485.1, U$504.21
DVDD22: C508.1, U$527.21
DVDD23: C531.1, U$550.21
DVDD24: C554.1, U$573.21
DVDD25: C577.1, U$596.21
DVDD26: C600.1, U$619.21
DVDD27: C623.1, U$642.21
DVDD28: C646.1, U$665.21
DVDD29: C669.1, U$688.21
DVDD30: C692.1, U$711.21
DVDD31: C715.1, U$734.21
DVDD32: C738.1, U$757.21
DVDD33: C761.1, U$780.21
DVDD34: C784.1, U$803.21
DVDD35: C807.1, U$826.21
DVDD36: C830.1, U$849.21
DVDD37: C853.1, U$872.21
DVDD38: C876.1, U$895.21
DVDD39: C899.1, U$918.21
GND: ANT1.3, BTN.2, C1.2, C2.2, C3.1, C4.2, C5.2, C6.2, C7.2, C8.2, C9.2, C10.2, C13.2, C14.1, C15.2, C16.2, C17.2, C21.1, C22.1, C29.2, C30.1, C31.1, C32.2, FB1.2, LDO_VREG.GND, LED2.C, SER3628CT-ND.2, SER3628CT-ND.4, TSX-3225_CRYSTAL.2, TSX-3225_CRYSTAL.4, U$2.P$1, U$6.P$20, U$12.2, U$12.5, U$12.6, U$44.3, U$44.4, U$44.5, U$76.3, U$76.6, U$76.11, U$76.14, U$76.28, U$76.33
GND1: ANT2.3, BTN1.2, C18.2, C19.2, C20.2, C23.2, C24.2, C25.2, C26.2, C27.2, C28.2, C33.2, C34.1, C35.1, C36.2, C37.1, C38.2, C41.2, C42.1, C43.2, C44.1, C45.1, C46.2, FB2.2, LDO_VREG1.GND, LED1.C, SER3628CT-ND1.2, SER3628CT-ND1.4, TSX-3225_CRYSTAL1.2, TSX-3225_CRYSTAL1.4, U$4.P$1, U$28.3, U$28.4, U$28.5, U$29.3, U$29.6, U$29.11, U$29.14, U$29.28, U$29.33, U$30.2, U$30.5, U$30.6, U$31.P$20
GND2: ANT3.3, BTN2.2, C47.2, C48.2, C49.2, C50.2, C51.2, C52.2, C53.2, C54.2, C55.2, C56.2, C57.1, C58.1, C59.2, C60.1, C61.2, C64.2, C65.1, C66.2, C67.1, C68.1, C69.2, FB3.2, LDO_VREG2.GND, LED3.C, SER3628CT-ND2.2, SER3628CT-ND2.4, TSX-3225_CRYSTAL2.2, TSX-3225_CRYSTAL2.4, U$33.P$1, U$65.3, U$65.4, U$65.5, U$66.3, U$66.6, U$66.11, U$66.14, U$66.28, U$66.33, U$67.2, U$67.5, U$67.6, U$68.P$20
GND3: ANT4.3, BTN3.2, C70.2, C71.2, C72.2, C73.2, C74.2, C75.2, C76.2, C77.2, C78.2, C79.2, C80.1, C81.1, C82.2, C83.1, C84.2, C87.2, C88.1, C89.2, C90.1, C91.1, C92.2, FB4.2, LDO_VREG3.GND, LED4.C, SER3628CT-ND3.2, SER3628CT-ND3.4, TSX-3225_CRYSTAL3.2, TSX-3225_CRYSTAL3.4, U$70.P$1, U$89.3, U$89.4, U$89.5, U$90.3, U$90.6, U$90.11, U$90.14, U$90.28, U$90.33, U$91.2, U$91.5, U$91.6, U$92.P$20
GND4: ANT5.3, BTN4.2, C93.2, C94.2, C95.2, C96.2, C97.2, C98.2, C99.2, C100.2, C101.2, C102.2, C103.1, C104.1, C105.2, C106.1, C107.2, C110.2, C111.1, C112.2, C113.1, C114.1, C115.2, FB5.2, LDO_VREG4.GND, LED5.C, SER3628CT-ND4.2, SER3628CT-ND4.4, TSX-3225_CRYSTAL4.2, TSX-3225_CRYSTAL4.4, U$94.P$1, U$112.3, U$112.4, U$112.5, U$113.3, U$113.6, U$113.11, U$113.14, U$113.28, U$113.33, U$114.2, U$114.5, U$114.6, U$115.P$20
GND5: ANT6.3, BTN5.2, C116.2, C117.2, C118.2, C119.2, C120.2, C121.2, C122.2, C123.2, C124.2, C125.2, C126.1, C127.1, C128.2, C129.1, C130.2, C133.2, C134.1, C135.2, C136.1, C137.1, C138.2, FB6.2, LDO_VREG5.GND, LED6.C, SER3628CT-ND5.2, SER3628CT-ND5.4, TSX-3225_CRYSTAL5.2, TSX-3225_CRYSTAL5.4, U$117.P$1, U$135.3, U$135.4, U$135.5, U$136.3, U$136.6, U$136.11, U$136.14, U$136.28, U$136.33, U$137.2, U$137.5, U$137.6, U$138.P$20
GND6: ANT7.3, BTN6.2, C139.2, C140.2, C141.2, C142.2, C143.2, C144.2, C145.2, C146.2, C147.2, C148.2, C149.1, C150.1, C151.2, C152.1, C153.2, C156.2, C157.1, C158.2, C159.1, C160.1, C161.2, FB7.2, LDO_VREG6.GND, LED7.C, SER3628CT-ND6.2, SER3628CT-ND6.4, TSX-3225_CRYSTAL6.2, TSX-3225_CRYSTAL6.4, U$140.P$1, U$158.3, U$158.4, U$158.5, U$159.3, U$159.6, U$159.11, U$159.14, U$159.28, U$159.33, U$160.2, U$160.5, U$160.6, U$161.P$20
GND7: ANT8.3, BTN7.2, C162.2, C163.2, C164.2, C165.2, C166.2, C167.2, C168.2, C169.2, C170.2, C171.2, C172.1, C173.1, C174.2, C175.1, C176.2, C179.2, C180.1, C181.2, C182.1, C183.1, C184.2, FB8.2, LDO_VREG7.GND, LED8.C, SER3628CT-ND7.2, SER3628CT-ND7.4, TSX-3225_CRYSTAL7.2, TSX-3225_CRYSTAL7.4, U$163.P$1, U$181.3, U$181.4, U$181.5, U$182.3, U$182.6, U$182.11, U$182.14, U$182.28, U$182.33, U$183.2, U$183.5, U$183.6, U$184.P$20
GND8: ANT9.3, BTN8.2, C185.2, C186.2, C187.2, C188.2, C189.2, C190.2, C191.2, C192.2, C193.2, C194.2, C195.1, C196.1, C197.2, C198.1, C199.2, C202.2, C203.1, C204.2, C205.1, C206.1, C207.2, FB9.2, LDO_VREG8.GND, LED9.C, SER3628CT-ND8.2, SER3628CT-ND8.4, TSX-3225_CRYSTAL8.2, TSX-3225_CRYSTAL8.4, U$186.P$1, U$204.3, U$204.4, U$204.5, U$205.3, U$205.6, U$205.11, U$205.14, U$205.28, U$205.33, U$206.2, U$206.5, U$206.6, U$207.P$20
GND9: ANT10.3, BTN9.2, C208.2, C209.2, C210.2, C211.2, C212.2, C213.2, C214.2, C215.2, C216.2, C217.2, C218.1, C219.1, C220.2, C221.1, C222.2, C225.2, C226.1, C227.2, C228.1, C229.1, C230.2, FB10.2, LDO_VREG9.GND, LED10.C, SER3628CT-ND9.2, SER3628CT-ND9.4, TSX-3225_CRYSTAL9.2, TSX-3225_CRYSTAL9.4, U$209.P$1, U$227.3, U$227.4, U$227.5, U$228.3, U$228.6, U$228.11, U$228.14, U$228.28, U$228.33, U$229.2, U$229.5, U$229.6, U$230.P$20
GND10: ANT11.3, BTN10.2, C231.2, C232.2, C233.2, C234.2, C235.2, C236.2, C237.2, C238.2, C239.2, C240.2, C241.1, C242.1, C243.2, C244.1, C245.2, C248.2, C249.1, C250.2, C251.1, C252.1, C253.2, FB11.2, LDO_VREG10.GND, LED11.C, SER3628CT-ND10.2, SER3628CT-ND10.4, TSX-3225_CRYSTAL10.2, TSX-3225_CRYSTAL10.4, U$232.P$1, U$250.3, U$250.4, U$250.5, U$251.3, U$251.6, U$251.11, U$251.14, U$251.28, U$251.33, U$252.2, U$252.5, U$252.6, U$253.P$20
GND11: ANT12.3, BTN11.2, C254.2, C255.2, C256.2, C257.2, C258.2, C259.2, C260.2, C261.2, C262.2, C263.2, C264.1, C265.1, C266.2, C267.1, C268.2, C271.2, C272.1, C273.2, C274.1, C275.1, C276.2, FB12.2, LDO_VREG11.GND, LED12.C, SER3628CT-ND11.2, SER3628CT-ND11.4, TSX-3225_CRYSTAL11.2, TSX-3225_CRYSTAL11.4, U$255.P$1, U$273.3, U$273.4, U$273.5, U$274.3, U$274.6, U$274.11, U$274.14, U$274.28, U$274.33, U$275.2, U$275.5, U$275.6, U$276.P$20
GND12: ANT13.3, BTN12.2, C277.2, C278.2, C279.2, C280.2, C281.2, C282.2, C283.2, C284.2, C285.2, C286.2, C287.1, C288.1, C289.2, C290.1, C291.2, C294.2, C295.1, C296.2, C297.1, C298.1, C299.2, FB13.2, LDO_VREG12.GND, LED13.C, SER3628CT-ND12.2, SER3628CT-ND12.4, TSX-3225_CRYSTAL12.2, TSX-3225_CRYSTAL12.4, U$278.P$1, U$296.3, U$296.4, U$296.5, U$297.3, U$297.6, U$297.11, U$297.14, U$297.28, U$297.33, U$298.2, U$298.5, U$298.6, U$299.P$20
GND13: ANT14.3, BTN13.2, C300.2, C301.2, C302.2, C303.2, C304.2, C305.2, C306.2, C307.2, C308.2, C309.2, C310.1, C311.1, C312.2, C313.1, C314.2, C317.2, C318.1, C319.2, C320.1, C321.1, C322.2, FB14.2, LDO_VREG13.GND, LED14.C, SER3628CT-ND13.2, SER3628CT-ND13.4, TSX-3225_CRYSTAL13.2, TSX-3225_CRYSTAL13.4, U$301.P$1, U$319.3, U$319.4, U$319.5, U$320.3, U$320.6, U$320.11, U$320.14, U$320.28, U$320.33, U$321.2, U$321.5, U$321.6, U$322.P$20
GND14: ANT15.3, BTN14.2, C323.2, C324.2, C325.2, C326.2, C327.2, C328.2, C329.2, C330.2, C331.2, C332.2, C333.1, C334.1, C335.2, C336.1, C337.2, C340.2, C341.1, C342.2, C343.1, C344.1, C345.2, FB15.2, LDO_VREG14.GND, LED15.C, SER3628CT-ND14.2, SER3628CT-ND14.4, TSX-3225_CRYSTAL14.2, TSX-3225_CRYSTAL14.4, U$324.P$1, U$342.3, U$342.4, U$342.5, U$343.3, U$343.6, U$343.11, U$343.14, U$343.28, U$343.33, U$344.2, U$344.5, U$344.6, U$345.P$20
GND15: ANT16.3, BTN15.2, C346.2, C347.2, C348.2, C349.2, C350.2, C351.2, C352.2, C353.2, C354.2, C355.2, C356.1, C357.1, C358.2, C359.1, C360.2, C363.2, C364.1, C365.2, C366.1, C367.1, C368.2, FB16.2, LDO_VREG15.GND, LED16.C, SER3628CT-ND15.2, SER3628CT-ND15.4, TSX-3225_CRYSTAL15.2, TSX-3225_CRYSTAL15.4, U$347.P$1, U$365.3, U$365.4, U$365.5, U$366.3, U$366.6, U$366.11, U$366.14, U$366.28, U$366.33, U$367.2, U$367.5, U$367.6, U$368.P$20
GND16: ANT17.3, BTN16.2, C369.2, C370.2, C371.2, C372.2, C373.2, C374.2, C375.2, C376.2, C377.2, C378.2, C379.1, C380.1, C381.2, C382.1, C383.2, C386.2, C387.1, C388.2, C389.1, C390.1, C391.2, FB17.2, LDO_VREG16.GND, LED17.C, SER3628CT-ND16.2, SER3628CT-ND16.4, TSX-3225_CRYSTAL16.2, TSX-3225_CRYSTAL16.4, U$370.P$1, U$388.3, U$388.4, U$388.5, U$389.3, U$389.6, U$389.11, U$389.14, U$389.28, U$389.33, U$390.2, U$390.5, U$390.6, U$391.P$20
GND17: ANT18.3, BTN17.2, C392.2, C393.2, C394.2, C395.2, C396.2, C397.2, C398.2, C399.2, C400.2, C401.2, C402.1, C403.1, C404.2, C405.1, C406.2, C409.2, C410.1, C411.2, C412.1, C413.1, C414.2, FB18.2, LDO_VREG17.GND, LED18.C, SER3628CT-ND17.2, SER3628CT-ND17.4, TSX-3225_CRYSTAL17.2, TSX-3225_CRYSTAL17.4, U$393.P$1, U$411.3, U$411.4, U$411.5, U$412.3, U$412.6, U$412.11, U$412.14, U$412.28, U$412.33, U$413.2, U$413.5, U$413.6, U$414.P$20
GND18: ANT19.3, BTN18.2, C415.2, C416.2, C417.2, C418.2, C419.2, C420.2, C421.2, C422.2, C423.2, C424.2, C425.1, C426.1, C427.2, C428.1, C429.2, C432.2, C433.1, C434.2, C435.1, C436.1, C437.2, FB19.2, LDO_VREG18.GND, LED19.C, SER3628CT-ND18.2, SER3628CT-ND18.4, TSX-3225_CRYSTAL18.2, TSX-3225_CRYSTAL18.4, U$416.P$1, U$434.3, U$434.4, U$434.5, U$435.3, U$435.6, U$435.11, U$435.14, U$435.28, U$435.33, U$436.2, U$436.5, U$436.6, U$437.P$20
GND19: ANT20.3, BTN19.2, C438.2, C439.2, C440.2, C441.2, C442.2, C443.2, C444.2, C445.2, C446.2, C447.2, C448.1, C449.1, C450.2, C451.1, C452.2, C455.2, C456.1, C457.2, C458.1, C459.1, C460.2, FB20.2, LDO_VREG19.GND, LED20.C, SER3628CT-ND19.2, SER3628CT-ND19.4, TSX-3225_CRYSTAL19.2, TSX-3225_CRYSTAL19.4, U$439.P$1, U$457.3, U$457.4, U$457.5, U$458.3, U$458.6, U$458.11, U$458.14, U$458.28, U$458.33, U$459.2, U$459.5, U$459.6, U$460.P$20
GND20: ANT21.3, BTN20.2, C461.2, C462.2, C463.2, C464.2, C465.2, C466.2, C467.2, C468.2, C469.2, C470.2, C471.1, C472.1, C473.2, C474.1, C475.2, C478.2, C479.1, C480.2, C481.1, C482.1, C483.2, FB21.2, LDO_VREG20.GND, LED21.C, SER3628CT-ND20.2, SER3628CT-ND20.4, TSX-3225_CRYSTAL20.2, TSX-3225_CRYSTAL20.4, U$462.P$1, U$480.3, U$480.4, U$480.5, U$481.3, U$481.6, U$481.11, U$481.14, U$481.28, U$481.33, U$482.2, U$482.5, U$482.6, U$483.P$20
GND21: ANT22.3, BTN21.2, C484.2, C485.2, C486.2, C487.2, C488.2, C489.2, C490.2, C491.2, C492.2, C493.2, C494.1, C495.1, C496.2, C497.1, C498.2, C501.2, C502.1, C503.2, C504.1, C505.1, C506.2, FB22.2, LDO_VREG21.GND, LED22.C, SER3628CT-ND21.2, SER3628CT-ND21.4, TSX-3225_CRYSTAL21.2, TSX-3225_CRYSTAL21.4, U$485.P$1, U$503.3, U$503.4, U$503.5, U$504.3, U$504.6, U$504.11, U$504.14, U$504.28, U$504.33, U$505.2, U$505.5, U$505.6, U$506.P$20
GND22: ANT23.3, BTN22.2, C507.2, C508.2, C509.2, C510.2, C511.2, C512.2, C513.2, C514.2, C515.2, C516.2, C517.1, C518.1, C519.2, C520.1, C521.2, C524.2, C525.1, C526.2, C527.1, C528.1, C529.2, FB23.2, LDO_VREG22.GND, LED23.C, SER3628CT-ND22.2, SER3628CT-ND22.4, TSX-3225_CRYSTAL22.2, TSX-3225_CRYSTAL22.4, U$508.P$1, U$526.3, U$526.4, U$526.5, U$527.3, U$527.6, U$527.11, U$527.14, U$527.28, U$527.33, U$528.2, U$528.5, U$528.6, U$529.P$20
GND23: ANT24.3, BTN23.2, C530.2, C531.2, C532.2, C533.2, C534.2, C535.2, C536.2, C537.2, C538.2, C539.2, C540.1, C541.1, C542.2, C543.1, C544.2, C547.2, C548.1, C549.2, C550.1, C551.1, C552.2, FB24.2, LDO_VREG23.GND, LED24.C, SER3628CT-ND23.2, SER3628CT-ND23.4, TSX-3225_CRYSTAL23.2, TSX-3225_CRYSTAL23.4, U$531.P$1, U$549.3, U$549.4, U$549.5, U$550.3, U$550.6, U$550.11, U$550.14, U$550.28, U$550.33, U$551.2, U$551.5, U$551.6, U$552.P$20
GND24: ANT25.3, BTN24.2, C553.2, C554.2, C555.2, C556.2, C557.2, C558.2, C559.2, C560.2, C561.2, C562.2, C563.1, C564.1, C565.2, C566.1, C567.2, C570.2, C571.1, C572.2, C573.1, C574.1, C575.2, FB25.2, LDO_VREG24.GND, LED25.C, SER3628CT-ND24.2, SER3628CT-ND24.4, TSX-3225_CRYSTAL24.2, TSX-3225_CRYSTAL24.4, U$554.P$1, U$572.3, U$572.4, U$572.5, U$573.3, U$573.6, U$573.11, U$573.14, U$573.28, U$573.33, U$574.2, U$574.5, U$574.6, U$575.P$20
GND25: ANT26.3, BTN25.2, C576.2, C577.2, C578.2, C579.2, C580.2, C581.2, C582.2, C583.2, C584.2, C585.2, C586.1, C587.1, C588.2, C589.1, C590.2, C593.2, C594.1, C595.2, C596.1, C597.1, C598.2, FB26.2, LDO_VREG25.GND, LED26.C, SER3628CT-ND25.2, SER3628CT-ND25.4, TSX-3225_CRYSTAL25.2, TSX-3225_CRYSTAL25.4, U$577.P$1, U$595.3, U$595.4, U$595.5, U$596.3, U$596.6, U$596.11, U$596.14, U$596.28, U$596.33, U$597.2, U$597.5, U$597.6, U$598.P$20
GND26: ANT27.3, BTN26.2, C599.2, C600.2, C601.2, C602.2, C603.2, C604.2, C605.2, C606.2, C607.2, C608.2, C609.1, C610.1, C611.2, C612.1, C613.2, C616.2, C617.1, C618.2, C619.1, C620.1, C621.2, FB27.2, LDO_VREG26.GND, LED27.C, SER3628CT-ND26.2, SER3628CT-ND26.4, TSX-3225_CRYSTAL26.2, TSX-3225_CRYSTAL26.4, U$600.P$1, U$618.3, U$618.4, U$618.5, U$619.3, U$619.6, U$619.11, U$619.14, U$619.28, U$619.33, U$620.2, U$620.5, U$620.6, U$621.P$20
GND27: ANT28.3, BTN27.2, C622.2, C623.2, C624.2, C625.2, C626.2, C627.2, C628.2, C629.2, C630.2, C631.2, C632.1, C633.1, C634.2, C635.1, C636.2, C639.2, C640.1, C641.2, C642.1, C643.1, C644.2, FB28.2, LDO_VREG27.GND, LED28.C, SER3628CT-ND27.2, SER3628CT-ND27.4, TSX-3225_CRYSTAL27.2, TSX-3225_CRYSTAL27.4, U$623.P$1, U$641.3, U$641.4, U$641.5, U$642.3, U$642.6, U$642.11, U$642.14, U$642.28, U$642.33, U$643.2, U$643.5, U$643.6, U$644.P$20
GND28: ANT29.3, BTN28.2, C645.2, C646.2, C647.2, C648.2, C649.2, C650.2, C651.2, C652.2, C653.2, C654.2, C655.1, C656.1, C657.2, C658.1, C659.2, C662.2, C663.1, C664.2, C665.1, C666.1, C667.2, FB29.2, LDO_VREG28.GND, LED29.C, SER3628CT-ND28.2, SER3628CT-ND28.4, TSX-3225_CRYSTAL28.2, TSX-3225_CRYSTAL28.4, U$646.P$1, U$664.3, U$664.4, U$664.5, U$665.3, U$665.6, U$665.11, U$665.14, U$665.28, U$665.33, U$666.2, U$666.5, U$666.6, U$667.P$20
GND29: ANT30.3, BTN29.2, C668.2, C669.2, C670.2, C671.2, C672.2, C673.2, C674.2, C675.2, C676.2, C677.2, C678.1, C679.1, C680.2, C681.1, C682.2, C685.2, C686.1, C687.2, C688.1, C689.1, C690.2, FB30.2, LDO_VREG29.GND, LED30.C, SER3628CT-ND29.2, SER3628CT-ND29.4, TSX-3225_CRYSTAL29.2, TSX-3225_CRYSTAL29.4, U$669.P$1, U$687.3, U$687.4, U$687.5, U$688.3, U$688.6, U$688.11, U$688.14, U$688.28, U$688.33, U$689.2, U$689.5, U$689.6, U$690.P$20
GND30: ANT31.3, BTN30.2, C691.2, C692.2, C693.2, C694.2, C695.2, C696.2, C697.2, C698.2, C699.2, C700.2, C701.1, C702.1, C703.2, C704.1, C705.2, C708.2, C709.1, C710.2, C711.1, C712.1, C713.2, FB31.2, LDO_VREG30.GND, LED31.C, SER3628CT-ND30.2, SER3628CT-ND30.4, TSX-3225_CRYSTAL30.2, TSX-3225_CRYSTAL30.4, U$692.P$1, U$710.3, U$710.4, U$710.5, U$711.3, U$711.6, U$711.11, U$711.14, U$711.28, U$711.33, U$712.2, U$712.5, U$712.6, U$713.P$20
GND31: ANT32.3, BTN31.2, C714.2, C715.2, C716.2, C717.2, C718.2, C719.2, C720.2, C721.2, C722.2, C723.2, C724.1, C725.1, C726.2, C727.1, C728.2, C731.2, C732.1, C733.2, C734.1, C735.1, C736.2, FB32.2, LDO_VREG31.GND, LED32.C, SER3628CT-ND31.2, SER3628CT-ND31.4, TSX-3225_CRYSTAL31.2, TSX-3225_CRYSTAL31.4, U$715.P$1, U$733.3, U$733.4, U$733.5, U$734.3, U$734.6, U$734.11, U$734.14, U$734.28, U$734.33, U$735.2, U$735.5, U$735.6, U$736.P$20
GND32: ANT33.3, BTN32.2, C737.2, C738.2, C739.2, C740.2, C741.2, C742.2, C743.2, C744.2, C745.2, C746.2, C747.1, C748.1, C749.2, C750.1, C751.2, C754.2, C755.1, C756.2, C757.1, C758.1, C759.2, FB33.2, LDO_VREG32.GND, LED33.C, SER3628CT-ND32.2, SER3628CT-ND32.4, TSX-3225_CRYSTAL32.2, TSX-3225_CRYSTAL32.4, U$738.P$1, U$756.3, U$756.4, U$756.5, U$757.3, U$757.6, U$757.11, U$757.14, U$757.28, U$757.33, U$758.2, U$758.5, U$758.6, U$759.P$20
GND33: ANT34.3, BTN33.2, C760.2, C761.2, C762.2, C763.2, C764.2, C765.2, C766.2, C767.2, C768.2, C769.2, C770.1, C771.1, C772.2, C773.1, C774.2, C777.2, C778.1, C779.2, C780.1, C781.1, C782.2, FB34.2, LDO_VREG33.GND, LED34.C, SER3628CT-ND33.2, SER3628CT-ND33.4, TSX-3225_CRYSTAL33.2, TSX-3225_CRYSTAL33.4, U$761.P$1, U$779.3, U$779.4, U$779.5, U$780.3, U$780.6, U$780.11, U$780.14, U$780.28, U$780.33, U$781.2, U$781.5, U$781.6, U$782.P$20
GND34: ANT35.3, BTN34.2, C783.2, C784.2, C785.2, C786.2, C787.2, C788.2, C789.2, C790.2, C791.2, C792.2, C793.1, C794.1, C795.2, C796.1, C797.2, C800.2, C801.1, C802.2, C803.1, C804.1, C805.2, FB35.2, LDO_VREG34.GND, LED35.C, SER3628CT-ND34.2, SER3628CT-ND34.4, TSX-3225_CRYSTAL34.2, TSX-3225_CRYSTAL34.4, U$784.P$1, U$802.3, U$802.4, U$802.5, U$803.3, U$803.6, U$803.11, U$803.14, U$803.28, U$803.33, U$804.2, U$804.5, U$804.6, U$805.P$20
GND35: ANT36.3, BTN35.2, C806.2, C807.2, C808.2, C809.2, C810.2, C811.2, C812.2, C813.2, C814.2, C815.2, C816.1, C817.1, C818.2, C819.1, C820.2, C823.2, C824.1, C825.2, C826.1, C827.1, C828.2, FB36.2, LDO_VREG35.GND, LED36.C, SER3628CT-ND35.2, SER3628CT-ND35.4, TSX-3225_CRYSTAL35.2, TSX-3225_CRYSTAL35.4, U$807.P$1, U$825.3, U$825.4, U$825.5, U$826.3, U$826.6, U$826.11, U$826.14, U$826.28, U$826.33, U$827.2, U$827.5, U$827.6, U$828.P$20
GND36: ANT37.3, BTN36.2, C829.2, C830.2, C831.2, C832.2, C833.2, C834.2, C835.2, C836.2, C837.2, C838.2, C839.1, C840.1, C841.2, C842.1, C843.2, C846.2, C847.1, C848.2, C849.1, C850.1, C851.2, FB37.2, LDO_VREG36.GND, LED37.C, SER3628CT-ND36.2, SER3628CT-ND36.4, TSX-3225_CRYSTAL36.2, TSX-3225_CRYSTAL36.4, U$830.P$1, U$848.3, U$848.4, U$848.5, U$849.3, U$849.6, U$849.11, U$849.14, U$849.28, U$849.33, U$850.2, U$850.5, U$850.6, U$851.P$20
GND37: ANT38.3, BTN37.2, C852.2, C853.2, C854.2, C855.2, C856.2, C857.2, C858.2, C859.2, C860.2, C861.2, C862.1, C863.1, C864.2, C865.1, C866.2, C869.2, C870.1, C871.2, C872.1, C873.1, C874.2, FB38.2, LDO_VREG37.GND, LED38.C, SER3628CT-ND37.2, SER3628CT-ND37.4, TSX-3225_CRYSTAL37.2, TSX-3225_CRYSTAL37.4, U$853.P$1, U$871.3, U$871.4, U$871.5, U$872.3, U$872.6, U$872.11, U$872.14, U$872.28, U$872.33, U$873.2, U$873.5, U$873.6, U$874.P$20
GND38: ANT39.3, BTN38.2, C875.2, C876.2, C877.2, C878.2, C879.2, C880.2, C881.2, C882.2, C883.2, C884.2, C885.1, C886.1, C887.2, C888.1, C889.2, C892.2, C893.1, C894.2, C895.1, C896.1, C897.2, FB39.2, LDO_VREG38.GND, LED39.C, SER3628CT-ND38.2, SER3628CT-ND38.4, TSX-3225_CRYSTAL38.2, TSX-3225_CRYSTAL38.4, U$876.P$1, U$894.3, U$894.4, U$894.5, U$895.3, U$895.6, U$895.11, U$895.14, U$895.28, U$895.33, U$896.2, U$896.5, U$896.6, U$897.P$20
GND39: ANT40.3, BTN39.2, C898.2, C899.2, C900.2, C901.2, C902.2, C903.2, C904.2, C905.2, C906.2, C907.2, C908.1, C909.1, C910.2, C911.1, C912.2, C915.2, C916.1, C917.2, C918.1, C919.1, C920.2, FB40.2, LDO_VREG39.GND, LED40.C, SER3628CT-ND39.2, SER3628CT-ND39.4, TSX-3225_CRYSTAL39.2, TSX-3225_CRYSTAL39.4, U$899.P$1, U$917.3, U$917.4, U$917.5, U$918.3, U$918.6, U$918.11, U$918.14, U$918.28, U$918.33, U$919.2, U$919.5, U$919.6, U$920.P$20
unnamed: C11.2, U$12.3
unnamed: ANT1.2, C13.1
unnamed: C12.2, U$12.4
unnamed: C32.1, U$6.P$10
unnamed: FB1.1, USB.5, USB.6, USB.7, USB.8, USB.9, USB.10, USB.11
unnamed: BTN1.1, R3.1
unnamed: LED1.A, R6.2
unnamed: C39.2, U$30.3
unnamed: C40.2, U$30.4
unnamed: ANT2.2, C41.1
unnamed: C46.1, U$31.P$10
unnamed: LED2.A, R4.2
unnamed: FB2.1, USB1.5, USB1.6, USB1.7, USB1.8, USB1.9, USB1.10, USB1.11
unnamed: BTN2.1, R11.1
unnamed: LED3.A, R13.2
unnamed: C62.2, U$67.3
unnamed: C63.2, U$67.4
unnamed: ANT3.2, C64.1
unnamed: C69.1, U$68.P$10
unnamed: FB3.1, USB2.5, USB2.6, USB2.7, USB2.8, USB2.9, USB2.10, USB2.11
unnamed: BTN3.1, R16.1
unnamed: LED4.A, R18.2
unnamed: BTN.1, R1.1
unnamed: C85.2, U$91.3
unnamed: C86.2, U$91.4
unnamed: ANT4.2, C87.1
unnamed: C92.1, U$92.P$10
unnamed: FB4.1, USB3.5, USB3.6, USB3.7, USB3.8, USB3.9, USB3.10, USB3.11
unnamed: BTN4.1, R21.1
unnamed: LED5.A, R23.2
unnamed: C108.2, U$114.3
unnamed: C109.2, U$114.4
unnamed: ANT5.2, C110.1
unnamed: C115.1, U$115.P$10
unnamed: FB5.1, USB4.5, USB4.6, USB4.7, USB4.8, USB4.9, USB4.10, USB4.11
unnamed: BTN5.1, R26.1
unnamed: LED6.A, R28.2
unnamed: C131.2, U$137.3
unnamed: C132.2, U$137.4
unnamed: ANT6.2, C133.1
unnamed: C138.1, U$138.P$10
unnamed: FB6.1, USB5.5, USB5.6, USB5.7, USB5.8, USB5.9, USB5.10, USB5.11
unnamed: BTN6.1, R31.1
unnamed: LED7.A, R33.2
unnamed: C154.2, U$160.3
unnamed: C155.2, U$160.4
unnamed: ANT7.2, C156.1
unnamed: C161.1, U$161.P$10
unnamed: FB7.1, USB6.5, USB6.6, USB6.7, USB6.8, USB6.9, USB6.10, USB6.11
unnamed: BTN7.1, R36.1
unnamed: LED8.A, R38.2
unnamed: C177.2, U$183.3
unnamed: C178.2, U$183.4
unnamed: ANT8.2, C179.1
unnamed: C184.1, U$184.P$10
unnamed: FB8.1, USB7.5, USB7.6, USB7.7, USB7.8, USB7.9, USB7.10, USB7.11
unnamed: BTN8.1, R41.1
unnamed: LED9.A, R43.2
unnamed: C200.2, U$206.3
unnamed: C201.2, U$206.4
unnamed: ANT9.2, C202.1
unnamed: C207.1, U$207.P$10
unnamed: FB9.1, USB8.5, USB8.6, USB8.7, USB8.8, USB8.9, USB8.10, USB8.11
unnamed: BTN9.1, R46.1
unnamed: LED10.A, R48.2
unnamed: C223.2, U$229.3
unnamed: C224.2, U$229.4
unnamed: ANT10.2, C225.1
unnamed: C230.1, U$230.P$10
unnamed: FB10.1, USB9.5, USB9.6, USB9.7, USB9.8, USB9.9, USB9.10, USB9.11
unnamed: BTN10.1, R51.1
unnamed: LED11.A, R53.2
unnamed: C246.2, U$252.3
unnamed: C247.2, U$252.4
unnamed: ANT11.2, C248.1
unnamed: C253.1, U$253.P$10
unnamed: FB11.1, USB10.5, USB10.6, USB10.7, USB10.8, USB10.9, USB10.10, USB10.11
unnamed: BTN11.1, R56.1
unnamed: LED12.A, R58.2
unnamed: C269.2, U$275.3
unnamed: C270.2, U$275.4
unnamed: ANT12.2, C271.1
unnamed: C276.1, U$276.P$10
unnamed: FB12.1, USB11.5, USB11.6, USB11.7, USB11.8, USB11.9, USB11.10, USB11.11
unnamed: BTN12.1, R61.1
unnamed: LED13.A, R63.2
unnamed: C292.2, U$298.3
unnamed: C293.2, U$298.4
unnamed: ANT13.2, C294.1
unnamed: C299.1, U$299.P$10
unnamed: FB13.1, USB12.5, USB12.6, USB12.7, USB12.8, USB12.9, USB12.10, USB12.11
unnamed: BTN13.1, R66.1
unnamed: LED14.A, R68.2
unnamed: C315.2, U$321.3
unnamed: C316.2, U$321.4
unnamed: ANT14.2, C317.1
unnamed: C322.1, U$322.P$10
unnamed: FB14.1, USB13.5, USB13.6, USB13.7, USB13.8, USB13.9, USB13.10, USB13.11
unnamed: BTN14.1, R71.1
unnamed: LED15.A, R73.2
unnamed: C338.2, U$344.3
unnamed: C339.2, U$344.4
unnamed: ANT15.2, C340.1
unnamed: C345.1, U$345.P$10
unnamed: FB15.1, USB14.5, USB14.6, USB14.7, USB14.8, USB14.9, USB14.10, USB14.11
unnamed: BTN15.1, R76.1
unnamed: LED16.A, R78.2
unnamed: C361.2, U$367.3
unnamed: C362.2, U$367.4
unnamed: ANT16.2, C363.1
unnamed: C368.1, U$368.P$10
unnamed: FB16.1, USB15.5, USB15.6, USB15.7, USB15.8, USB15.9, USB15.10, USB15.11
unnamed: BTN16.1, R81.1
unnamed: LED17.A, R83.2
unnamed: C384.2, U$390.3
unnamed: C385.2, U$390.4
unnamed: ANT17.2, C386.1
unnamed: C391.1, U$391.P$10
unnamed: FB17.1, USB16.5, USB16.6, USB16.7, USB16.8, USB16.9, USB16.10, USB16.11
unnamed: BTN17.1, R86.1
unnamed: LED18.A, R88.2
unnamed: C407.2, U$413.3
unnamed: C408.2, U$413.4
unnamed: ANT18.2, C409.1
unnamed: C414.1, U$414.P$10
unnamed: FB18.1, USB17.5, USB17.6, USB17.7, USB17.8, USB17.9, USB17.10, USB17.11
unnamed: BTN18.1, R91.1
unnamed: LED19.A, R93.2
unnamed: C430.2, U$436.3
unnamed: C431.2, U$436.4
unnamed: ANT19.2, C432.1
unnamed: C437.1, U$437.P$10
unnamed: FB19.1, USB18.5, USB18.6, USB18.7, USB18.8, USB18.9, USB18.10, USB18.11
unnamed: BTN19.1, R96.1
unnamed: LED20.A, R98.2
unnamed: C453.2, U$459.3
unnamed: C454.2, U$459.4
unnamed: ANT20.2, C455.1
unnamed: C460.1, U$460.P$10
unnamed: FB20.1, USB19.5, USB19.6, USB19.7, USB19.8, USB19.9, USB19.10, USB19.11
unnamed: BTN20.1, R101.1
unnamed: LED21.A, R103.2
unnamed: C476.2, U$482.3
unnamed: C477.2, U$482.4
unnamed: ANT21.2, C478.1
unnamed: C483.1, U$483.P$10
unnamed: FB21.1, USB20.5, USB20.6, USB20.7, USB20.8, USB20.9, USB20.10, USB20.11
unnamed: BTN21.1, R106.1
unnamed: LED22.A, R108.2
unnamed: C499.2, U$505.3
unnamed: C500.2, U$505.4
unnamed: ANT22.2, C501.1
unnamed: C506.1, U$506.P$10
unnamed: FB22.1, USB21.5, USB21.6, USB21.7, USB21.8, USB21.9, USB21.10, USB21.11
unnamed: BTN22.1, R111.1
unnamed: LED23.A, R113.2
unnamed: C522.2, U$528.3
unnamed: C523.2, U$528.4
unnamed: ANT23.2, C524.1
unnamed: C529.1, U$529.P$10
unnamed: FB23.1, USB22.5, USB22.6, USB22.7, USB22.8, USB22.9, USB22.10, USB22.11
unnamed: BTN23.1, R116.1
unnamed: LED24.A, R118.2
unnamed: C545.2, U$551.3
unnamed: C546.2, U$551.4
unnamed: ANT24.2, C547.1
unnamed: C552.1, U$552.P$10
unnamed: FB24.1, USB23.5, USB23.6, USB23.7, USB23.8, USB23.9, USB23.10, USB23.11
unnamed: BTN24.1, R121.1
unnamed: LED25.A, R123.2
unnamed: C568.2, U$574.3
unnamed: C569.2, U$574.4
unnamed: ANT25.2, C570.1
unnamed: C575.1, U$575.P$10
unnamed: FB25.1, USB24.5, USB24.6, USB24.7, USB24.8, USB24.9, USB24.10, USB24.11
unnamed: BTN25.1, R126.1
unnamed: LED26.A, R128.2
unnamed: C591.2, U$597.3
unnamed: C592.2, U$597.4
unnamed: ANT26.2, C593.1
unnamed: C598.1, U$598.P$10
unnamed: FB26.1, USB25.5, USB25.6, USB25.7, USB25.8, USB25.9, USB25.10, USB25.11
unnamed: BTN26.1, R131.1
unnamed: LED27.A, R133.2
unnamed: C614.2, U$620.3
unnamed: C615.2, U$620.4
unnamed: ANT27.2, C616.1
unnamed: C621.1, U$621.P$10
unnamed: FB27.1, USB26.5, USB26.6, USB26.7, USB26.8, USB26.9, USB26.10, USB26.11
unnamed: BTN27.1, R136.1
unnamed: LED28.A, R138.2
unnamed: C637.2, U$643.3
unnamed: C638.2, U$643.4
unnamed: ANT28.2, C639.1
unnamed: C644.1, U$644.P$10
unnamed: FB28.1, USB27.5, USB27.6, USB27.7, USB27.8, USB27.9, USB27.10, USB27.11
unnamed: BTN28.1, R141.1
unnamed: LED29.A, R143.2
unnamed: C660.2, U$666.3
unnamed: C661.2, U$666.4
unnamed: ANT29.2, C662.1
unnamed: C667.1, U$667.P$10
unnamed: FB29.1, USB28.5, USB28.6, USB28.7, USB28.8, USB28.9, USB28.10, USB28.11
unnamed: BTN29.1, R146.1
unnamed: LED30.A, R148.2
unnamed: C683.2, U$689.3
unnamed: C684.2, U$689.4
unnamed: ANT30.2, C685.1
unnamed: C690.1, U$690.P$10
unnamed: FB30.1, USB29.5, USB29.6, USB29.7, USB29.8, USB29.9, USB29.10, USB29.11
unnamed: BTN30.1, R151.1
unnamed: LED31.A, R153.2
unnamed: C706.2, U$712.3
unnamed: C707.2, U$712.4
unnamed: ANT31.2, C708.1
unnamed: C713.1, U$713.P$10
unnamed: FB31.1, USB30.5, USB30.6, USB30.7, USB30.8, USB30.9, USB30.10, USB30.11
unnamed: BTN31.1, R156.1
unnamed: LED32.A, R158.2
unnamed: C729.2, U$735.3
unnamed: C730.2, U$735.4
unnamed: ANT32.2, C731.1
unnamed: C736.1, U$736.P$10
unnamed: FB32.1, USB31.5, USB31.6, USB31.7, USB31.8, USB31.9, USB31.10, USB31.11
unnamed: BTN32.1, R161.1
unnamed: LED33.A, R163.2
unnamed: C752.2, U$758.3
unnamed: C753.2, U$758.4
unnamed: ANT33.2, C754.1
unnamed: C759.1, U$759.P$10
unnamed: FB33.1, USB32.5, USB32.6, USB32.7, USB32.8, USB32.9, USB32.10, USB32.11
unnamed: BTN33.1, R166.1
unnamed: LED34.A, R168.2
unnamed: C775.2, U$781.3
unnamed: C776.2, U$781.4
unnamed: ANT34.2, C777.1
unnamed: C782.1, U$782.P$10
unnamed: FB34.1, USB33.5, USB33.6, USB33.7, USB33.8, USB33.9, USB33.10, USB33.11
unnamed: BTN34.1, R171.1
unnamed: LED35.A, R173.2
unnamed: C798.2, U$804.3
unnamed: C799.2, U$804.4
unnamed: ANT35.2, C800.1
unnamed: C805.1, U$805.P$10
unnamed: FB35.1, USB34.5, USB34.6, USB34.7, USB34.8, USB34.9, USB34.10, USB34.11
unnamed: BTN35.1, R176.1
unnamed: LED36.A, R178.2
unnamed: C821.2, U$827.3
unnamed: C822.2, U$827.4
unnamed: ANT36.2, C823.1
unnamed: C828.1, U$828.P$10
unnamed: FB36.1, USB35.5, USB35.6, USB35.7, USB35.8, USB35.9, USB35.10, USB35.11
unnamed: BTN36.1, R181.1
unnamed: LED37.A, R183.2
unnamed: C844.2, U$850.3
unnamed: C845.2, U$850.4
unnamed: ANT37.2, C846.1
unnamed: C851.1, U$851.P$10
unnamed: FB37.1, USB36.5, USB36.6, USB36.7, USB36.8, USB36.9, USB36.10, USB36.11
unnamed: BTN37.1, R186.1
unnamed: LED38.A, R188.2
unnamed: C867.2, U$873.3
unnamed: C868.2, U$873.4
unnamed: ANT38.2, C869.1
unnamed: C874.1, U$874.P$10
unnamed: FB38.1, USB37.5, USB37.6, USB37.7, USB37.8, USB37.9, USB37.10, USB37.11
unnamed: BTN38.1, R191.1
unnamed: LED39.A, R193.2
unnamed: C890.2, U$896.3
unnamed: C891.2, U$896.4
unnamed: ANT39.2, C892.1
unnamed: C897.1, U$897.P$10
unnamed: FB39.1, USB38.5, USB38.6, USB38.7, USB38.8, USB38.9, USB38.10, USB38.11
unnamed: BTN39.1, R196.1
unnamed: LED40.A, R198.2
unnamed: C913.2, U$919.3
unnamed: C914.2, U$919.4
unnamed: ANT40.2, C915.1
unnamed: C920.1, U$920.P$10
unnamed: FB40.1, USB39.5, USB39.6, USB39.7, USB39.8, USB39.9, USB39.10, USB39.11
PA01: U$25.P$1, U$29.7
PA02: U$19.P$1, U$29.8
PA03: U$23.P$1, U$29.25
PA04: U$24.P$1, U$29.27
PA05: U$62.P$1, U$66.7
PA06: U$54.P$1, U$76.7
PA07: U$43.P$1, U$76.8
PA08: U$56.P$1, U$66.8
PA08/I2C: R8.1, U$6.P$24, U$42.P$1, U$44.7, U$76.9
PA08/I2C1: R7.1, U$18.P$1, U$28.7, U$29.9, U$31.P$24
PA08/I2C2: R14.1, U$55.P$1, U$65.7, U$66.9, U$68.P$24
PA08/I2C3: R19.1, U$79.P$1, U$89.7, U$90.9, U$92.P$24
PA08/I2C4: R24.1, U$102.P$1, U$112.7, U$113.9, U$115.P$24
PA08/I2C5: R29.1, U$125.P$1, U$135.7, U$136.9, U$138.P$24
PA08/I2C6: R34.1, U$148.P$1, U$158.7, U$159.9, U$161.P$24
PA08/I2C7: R39.1, U$171.P$1, U$181.7, U$182.9, U$184.P$24
PA08/I2C8: R44.1, U$194.P$1, U$204.7, U$205.9, U$207.P$24
PA08/I2C9: R49.1, U$217.P$1, U$227.7, U$228.9, U$230.P$24
PA08/I2C10: R54.1, U$240.P$1, U$250.7, U$251.9, U$253.P$24
PA08/I2C11: R59.1, U$263.P$1, U$273.7, U$274.9, U$276.P$24
PA08/I2C12: R64.1, U$286.P$1, U$296.7, U$297.9, U$299.P$24
PA08/I2C13: R69.1, U$309.P$1, U$319.7, U$320.9, U$322.P$24
PA08/I2C14: R74.1, U$332.P$1, U$342.7, U$343.9, U$345.P$24
PA08/I2C15: R79.1, U$355.P$1, U$365.7, U$366.9, U$368.P$24
PA08/I2C16: R84.1, U$378.P$1, U$388.7, U$389.9, U$391.P$24
PA08/I2C17: R89.1, U$401.P$1, U$411.7, U$412.9, U$414.P$24
PA08/I2C18: R94.1, U$424.P$1, U$434.7, U$435.9, U$437.P$24
PA08/I2C19: R99.1, U$447.P$1, U$457.7, U$458.9, U$460.P$24
PA08/I2C20: R104.1, U$470.P$1, U$480.7, U$481.9, U$483.P$24
PA08/I2C21: R109.1, U$493.P$1, U$503.7, U$504.9, U$506.P$24
PA08/I2C22: R114.1, U$516.P$1, U$526.7, U$527.9, U$529.P$24
PA08/I2C23: R119.1, U$539.P$1, U$549.7, U$550.9, U$552.P$24
PA08/I2C24: R124.1, U$562.P$1, U$572.7, U$573.9, U$575.P$24
PA08/I2C25: R129.1, U$585.P$1, U$595.7, U$596.9, U$598.P$24
PA08/I2C26: R134.1, U$608.P$1, U$618.7, U$619.9, U$621.P$24
PA08/I2C27: R139.1, U$631.P$1, U$641.7, U$642.9, U$644.P$24
PA08/I2C28: R144.1, U$654.P$1, U$664.7, U$665.9, U$667.P$24
PA08/I2C29: R149.1, U$677.P$1, U$687.7, U$688.9, U$690.P$24
PA08/I2C30: R154.1, U$700.P$1, U$710.7, U$711.9, U$713.P$24
PA08/I2C31: R159.1, U$723.P$1, U$733.7, U$734.9, U$736.P$24
PA08/I2C32: R164.1, U$746.P$1, U$756.7, U$757.9, U$759.P$24
PA08/I2C33: R169.1, U$769.P$1, U$779.7, U$780.9, U$782.P$24
PA08/I2C34: R174.1, U$792.P$1, U$802.7, U$803.9, U$805.P$24
PA08/I2C35: R179.1, U$815.P$1, U$825.7, U$826.9, U$828.P$24
PA08/I2C36: R184.1, U$838.P$1, U$848.7, U$849.9, U$851.P$24
PA08/I2C37: R189.1, U$861.P$1, U$871.7, U$872.9, U$874.P$24
PA08/I2C38: R194.1, U$884.P$1, U$894.7, U$895.9, U$897.P$24
PA08/I2C39: R199.1, U$907.P$1, U$917.7, U$918.9, U$920.P$24
PA09: U$60.P$1, U$66.25
PA09/I2C: R9.1, U$6.P$23, U$41.P$1, U$44.8, U$76.10
PA09/I2C1: R10.1, U$17.P$1, U$28.8, U$29.10, U$31.P$23
PA09/I2C2: R15.1, U$53.P$1, U$65.8, U$66.10, U$68.P$23
PA09/I2C3: R20.1, U$78.P$1, U$89.8, U$90.10, U$92.P$23
PA09/I2C4: R25.1, U$101.P$1, U$112.8, U$113.10, U$115.P$23
PA09/I2C5: R30.1, U$124.P$1, U$135.8, U$136.10, U$138.P$23
PA09/I2C6: R35.1, U$147.P$1, U$158.8, U$159.10, U$161.P$23
PA09/I2C7: R40.1, U$170.P$1, U$181.8, U$182.10, U$184.P$23
PA09/I2C8: R45.1, U$193.P$1, U$204.8, U$205.10, U$207.P$23
PA09/I2C9: R50.1, U$216.P$1, U$227.8, U$228.10, U$230.P$23
PA09/I2C10: R55.1, U$239.P$1, U$250.8, U$251.10, U$253.P$23
PA09/I2C11: R60.1, U$262.P$1, U$273.8, U$274.10, U$276.P$23
PA09/I2C12: R65.1, U$285.P$1, U$296.8, U$297.10, U$299.P$23
PA09/I2C13: R70.1, U$308.P$1, U$319.8, U$320.10, U$322.P$23
PA09/I2C14: R75.1, U$331.P$1, U$342.8, U$343.10, U$345.P$23
PA09/I2C15: R80.1, U$354.P$1, U$365.8, U$366.10, U$368.P$23
PA09/I2C16: R85.1, U$377.P$1, U$388.8, U$389.10, U$391.P$23
PA09/I2C17: R90.1, U$400.P$1, U$411.8, U$412.10, U$414.P$23
PA09/I2C18: R95.1, U$423.P$1, U$434.8, U$435.10, U$437.P$23
PA09/I2C19: R100.1, U$446.P$1, U$457.8, U$458.10, U$460.P$23
PA09/I2C20: R105.1, U$469.P$1, U$480.8, U$481.10, U$483.P$23
PA09/I2C21: R110.1, U$492.P$1, U$503.8, U$504.10, U$506.P$23
PA09/I2C22: R115.1, U$515.P$1, U$526.8, U$527.10, U$529.P$23
PA09/I2C23: R120.1, U$538.P$1, U$549.8, U$550.10, U$552.P$23
PA09/I2C24: R125.1, U$561.P$1, U$572.8, U$573.10, U$575.P$23
PA09/I2C25: R130.1, U$584.P$1, U$595.8, U$596.10, U$598.P$23
PA09/I2C26: R135.1, U$607.P$1, U$618.8, U$619.10, U$621.P$23
PA09/I2C27: R140.1, U$630.P$1, U$641.8, U$642.10, U$644.P$23
PA09/I2C28: R145.1, U$653.P$1, U$664.8, U$665.10, U$667.P$23
PA09/I2C29: R150.1, U$676.P$1, U$687.8, U$688.10, U$690.P$23
PA09/I2C30: R155.1, U$699.P$1, U$710.8, U$711.10, U$713.P$23
PA09/I2C31: R160.1, U$722.P$1, U$733.8, U$734.10, U$736.P$23
PA09/I2C32: R165.1, U$745.P$1, U$756.8, U$757.10, U$759.P$23
PA09/I2C33: R170.1, U$768.P$1, U$779.8, U$780.10, U$782.P$23
PA09/I2C34: R175.1, U$791.P$1, U$802.8, U$803.10, U$805.P$23
PA09/I2C35: R180.1, U$814.P$1, U$825.8, U$826.10, U$828.P$23
PA09/I2C36: R185.1, U$837.P$1, U$848.8, U$849.10, U$851.P$23
PA09/I2C37: R190.1, U$860.P$1, U$871.8, U$872.10, U$874.P$23
PA09/I2C38: R195.1, U$883.P$1, U$894.8, U$895.10, U$897.P$23
PA09/I2C39: R200.1, U$906.P$1, U$917.8, U$918.10, U$920.P$23
PA10: U$61.P$1, U$66.27
PA11: U$86.P$1, U$90.7
PA12: U$80.P$1, U$90.8
PA13: U$84.P$1, U$90.25
PA14: U$85.P$1, U$90.27
PA14/XIN_MC: C3.2, TSX-3225_CRYSTAL.1, U$76.15
PA14/XIN_MC1: C37.2, TSX-3225_CRYSTAL1.1, U$29.15
PA14/XIN_MC2: C60.2, TSX-3225_CRYSTAL2.1, U$66.15
PA14/XIN_MC3: C83.2, TSX-3225_CRYSTAL3.1, U$90.15
PA14/XIN_MC4: C106.2, TSX-3225_CRYSTAL4.1, U$113.15
PA14/XIN_MC5: C129.2, TSX-3225_CRYSTAL5.1, U$136.15
PA14/XIN_MC6: C152.2, TSX-3225_CRYSTAL6.1, U$159.15
PA14/XIN_MC7: C175.2, TSX-3225_CRYSTAL7.1, U$182.15
PA14/XIN_MC8: C198.2, TSX-3225_CRYSTAL8.1, U$205.15
PA14/XIN_MC9: C221.2, TSX-3225_CRYSTAL9.1, U$228.15
PA14/XIN_MC10: C244.2, TSX-3225_CRYSTAL10.1, U$251.15
PA14/XIN_MC11: C267.2, TSX-3225_CRYSTAL11.1, U$274.15
PA14/XIN_MC12: C290.2, TSX-3225_CRYSTAL12.1, U$297.15
PA14/XIN_MC13: C313.2, TSX-3225_CRYSTAL13.1, U$320.15
PA14/XIN_MC14: C336.2, TSX-3225_CRYSTAL14.1, U$343.15
PA14/XIN_MC15: C359.2, TSX-3225_CRYSTAL15.1, U$366.15
PA14/XIN_MC16: C382.2, TSX-3225_CRYSTAL16.1, U$389.15
PA14/XIN_MC17: C405.2, TSX-3225_CRYSTAL17.1, U$412.15
PA14/XIN_MC18: C428.2, TSX-3225_CRYSTAL18.1, U$435.15
PA14/XIN_MC19: C451.2, TSX-3225_CRYSTAL19.1, U$458.15
PA14/XIN_MC20: C474.2, TSX-3225_CRYSTAL20.1, U$481.15
PA14/XIN_MC21: C497.2, TSX-3225_CRYSTAL21.1, U$504.15
PA14/XIN_MC22: C520.2, TSX-3225_CRYSTAL22.1, U$527.15
PA14/XIN_MC23: C543.2, TSX-3225_CRYSTAL23.1, U$550.15
PA14/XIN_MC24: C566.2, TSX-3225_CRYSTAL24.1, U$573.15
PA14/XIN_MC25: C589.2, TSX-3225_CRYSTAL25.1, U$596.15
PA14/XIN_MC26: C612.2, TSX-3225_CRYSTAL26.1, U$619.15
PA14/XIN_MC27: C635.2, TSX-3225_CRYSTAL27.1, U$642.15
PA14/XIN_MC28: C658.2, TSX-3225_CRYSTAL28.1, U$665.15
PA14/XIN_MC29: C681.2, TSX-3225_CRYSTAL29.1, U$688.15
PA14/XIN_MC30: C704.2, TSX-3225_CRYSTAL30.1, U$711.15
PA14/XIN_MC31: C727.2, TSX-3225_CRYSTAL31.1, U$734.15
PA14/XIN_MC32: C750.2, TSX-3225_CRYSTAL32.1, U$757.15
PA14/XIN_MC33: C773.2, TSX-3225_CRYSTAL33.1, U$780.15
PA14/XIN_MC34: C796.2, TSX-3225_CRYSTAL34.1, U$803.15
PA14/XIN_MC35: C819.2, TSX-3225_CRYSTAL35.1, U$826.15
PA14/XIN_MC36: C842.2, TSX-3225_CRYSTAL36.1, U$849.15
PA14/XIN_MC37: C865.2, TSX-3225_CRYSTAL37.1, U$872.15
PA14/XIN_MC38: C888.2, TSX-3225_CRYSTAL38.1, U$895.15
PA14/XIN_MC39: C911.2, TSX-3225_CRYSTAL39.1, U$918.15
PA15: U$109.P$1, U$113.7
PA15/XOUT_MC: C4.1, TSX-3225_CRYSTAL.3, U$39.P$1, U$76.16
PA15/XOUT_MC1: C38.1, TSX-3225_CRYSTAL1.3, U$16.P$1, U$29.16
PA15/XOUT_MC2: C61.1, TSX-3225_CRYSTAL2.3, U$52.P$1, U$66.16
PA15/XOUT_MC3: C84.1, TSX-3225_CRYSTAL3.3, U$77.P$1, U$90.16
PA15/XOUT_MC4: C107.1, TSX-3225_CRYSTAL4.3, U$100.P$1, U$113.16
PA15/XOUT_MC5: C130.1, TSX-3225_CRYSTAL5.3, U$123.P$1, U$136.16
PA15/XOUT_MC6: C153.1, TSX-3225_CRYSTAL6.3, U$146.P$1, U$159.16
PA15/XOUT_MC7: C176.1, TSX-3225_CRYSTAL7.3, U$169.P$1, U$182.16
PA15/XOUT_MC8: C199.1, TSX-3225_CRYSTAL8.3, U$192.P$1, U$205.16
PA15/XOUT_MC9: C222.1, TSX-3225_CRYSTAL9.3, U$215.P$1, U$228.16
PA15/XOUT_MC10: C245.1, TSX-3225_CRYSTAL10.3, U$238.P$1, U$251.16
PA15/XOUT_MC11: C268.1, TSX-3225_CRYSTAL11.3, U$261.P$1, U$274.16
PA15/XOUT_MC12: C291.1, TSX-3225_CRYSTAL12.3, U$284.P$1, U$297.16
PA15/XOUT_MC13: C314.1, TSX-3225_CRYSTAL13.3, U$307.P$1, U$320.16
PA15/XOUT_MC14: C337.1, TSX-3225_CRYSTAL14.3, U$330.P$1, U$343.16
PA15/XOUT_MC15: C360.1, TSX-3225_CRYSTAL15.3, U$353.P$1, U$366.16
PA15/XOUT_MC16: C383.1, TSX-3225_CRYSTAL16.3, U$376.P$1, U$389.16
PA15/XOUT_MC17: C406.1, TSX-3225_CRYSTAL17.3, U$399.P$1, U$412.16
PA15/XOUT_MC18: C429.1, TSX-3225_CRYSTAL18.3, U$422.P$1, U$435.16
PA15/XOUT_MC19: C452.1, TSX-3225_CRYSTAL19.3, U$445.P$1, U$458.16
PA15/XOUT_MC20: C475.1, TSX-3225_CRYSTAL20.3, U$468.P$1, U$481.16
PA15/XOUT_MC21: C498.1, TSX-3225_CRYSTAL21.3, U$491.P$1, U$504.16
PA15/XOUT_MC22: C521.1, TSX-3225_CRYSTAL22.3, U$514.P$1, U$527.16
PA15/XOUT_MC23: C544.1, TSX-3225_CRYSTAL23.3, U$537.P$1, U$550.16
PA15/XOUT_MC24: C567.1, TSX-3225_CRYSTAL24.3, U$560.P$1, U$573.16
PA15/XOUT_MC25: C590.1, TSX-3225_CRYSTAL25.3, U$583.P$1, U$596.16
PA15/XOUT_MC26: C613.1, TSX-3225_CRYSTAL26.3, U$606.P$1, U$619.16
PA15/XOUT_MC27: C636.1, TSX-3225_CRYSTAL27.3, U$629.P$1, U$642.16
PA15/XOUT_MC28: C659.1, TSX-3225_CRYSTAL28.3, U$652.P$1, U$665.16
PA15/XOUT_MC29: C682.1, TSX-3225_CRYSTAL29.3, U$675.P$1, U$688.16
PA15/XOUT_MC30: C705.1, TSX-3225_CRYSTAL30.3, U$698.P$1, U$711.16
PA15/XOUT_MC31: C728.1, TSX-3225_CRYSTAL31.3, U$721.P$1, U$734.16
PA15/XOUT_MC32: C751.1, TSX-3225_CRYSTAL32.3, U$744.P$1, U$757.16
PA15/XOUT_MC33: C774.1, TSX-3225_CRYSTAL33.3, U$767.P$1, U$780.16
PA15/XOUT_MC34: C797.1, TSX-3225_CRYSTAL34.3, U$790.P$1, U$803.16
PA15/XOUT_MC35: C820.1, TSX-3225_CRYSTAL35.3, U$813.P$1, U$826.16
PA15/XOUT_MC36: C843.1, TSX-3225_CRYSTAL36.3, U$836.P$1, U$849.16
PA15/XOUT_MC37: C866.1, TSX-3225_CRYSTAL37.3, U$859.P$1, U$872.16
PA15/XOUT_MC38: C889.1, TSX-3225_CRYSTAL38.3, U$882.P$1, U$895.16
PA15/XOUT_MC39: C912.1, TSX-3225_CRYSTAL39.3, U$905.P$1, U$918.16
PA16: U$103.P$1, U$113.8
PA16/I2C: U$38.P$1, U$76.17
PA16/I2C1: U$15.P$1, U$29.17
PA16/I2C2: U$51.P$1, U$66.17
PA16/I2C3: U$75.P$1, U$90.17
PA16/I2C4: U$99.P$1, U$113.17
PA16/I2C5: U$122.P$1, U$136.17
PA16/I2C6: U$145.P$1, U$159.17
PA16/I2C7: U$168.P$1, U$182.17
PA16/I2C8: U$191.P$1, U$205.17
PA16/I2C9: U$214.P$1, U$228.17
PA16/I2C10: U$237.P$1, U$251.17
PA16/I2C11: U$260.P$1, U$274.17
PA16/I2C12: U$283.P$1, U$297.17
PA16/I2C13: U$306.P$1, U$320.17
PA16/I2C14: U$329.P$1, U$343.17
PA16/I2C15: U$352.P$1, U$366.17
PA16/I2C16: U$375.P$1, U$389.17
PA16/I2C17: U$398.P$1, U$412.17
PA16/I2C18: U$421.P$1, U$435.17
PA16/I2C19: U$444.P$1, U$458.17
PA16/I2C20: U$467.P$1, U$481.17
PA16/I2C21: U$490.P$1, U$504.17
PA16/I2C22: U$513.P$1, U$527.17
PA16/I2C23: U$536.P$1, U$550.17
PA16/I2C24: U$559.P$1, U$573.17
PA16/I2C25: U$582.P$1, U$596.17
PA16/I2C26: U$605.P$1, U$619.17
PA16/I2C27: U$628.P$1, U$642.17
PA16/I2C28: U$651.P$1, U$665.17
PA16/I2C29: U$674.P$1, U$688.17
PA16/I2C30: U$697.P$1, U$711.17
PA16/I2C31: U$720.P$1, U$734.17
PA16/I2C32: U$743.P$1, U$757.17
PA16/I2C33: U$766.P$1, U$780.17
PA16/I2C34: U$789.P$1, U$803.17
PA16/I2C35: U$812.P$1, U$826.17
PA16/I2C36: U$835.P$1, U$849.17
PA16/I2C37: U$858.P$1, U$872.17
PA16/I2C38: U$881.P$1, U$895.17
PA16/I2C39: U$904.P$1, U$918.17
PA17: U$107.P$1, U$113.25
PA17/I2C: U$37.P$1, U$76.18
PA17/I2C1: U$14.P$1, U$29.18
PA17/I2C2: U$50.P$1, U$66.18
PA17/I2C3: U$74.P$1, U$90.18
PA17/I2C4: U$98.P$1, U$113.18
PA17/I2C5: U$121.P$1, U$136.18
PA17/I2C6: U$144.P$1, U$159.18
PA17/I2C7: U$167.P$1, U$182.18
PA17/I2C8: U$190.P$1, U$205.18
PA17/I2C9: U$213.P$1, U$228.18
PA17/I2C10: U$236.P$1, U$251.18
PA17/I2C11: U$259.P$1, U$274.18
PA17/I2C12: U$282.P$1, U$297.18
PA17/I2C13: U$305.P$1, U$320.18
PA17/I2C14: U$328.P$1, U$343.18
PA17/I2C15: U$351.P$1, U$366.18
PA17/I2C16: U$374.P$1, U$389.18
PA17/I2C17: U$397.P$1, U$412.18
PA17/I2C18: U$420.P$1, U$435.18
PA17/I2C19: U$443.P$1, U$458.18
PA17/I2C20: U$466.P$1, U$481.18
PA17/I2C21: U$489.P$1, U$504.18
PA17/I2C22: U$512.P$1, U$527.18
PA17/I2C23: U$535.P$1, U$550.18
PA17/I2C24: U$558.P$1, U$573.18
PA17/I2C25: U$581.P$1, U$596.18
PA17/I2C26: U$604.P$1, U$619.18
PA17/I2C27: U$627.P$1, U$642.18
PA17/I2C28: U$650.P$1, U$665.18
PA17/I2C29: U$673.P$1, U$688.18
PA17/I2C30: U$696.P$1, U$711.18
PA17/I2C31: U$719.P$1, U$734.18
PA17/I2C32: U$742.P$1, U$757.18
PA17/I2C33: U$765.P$1, U$780.18
PA17/I2C34: U$788.P$1, U$803.18
PA17/I2C35: U$811.P$1, U$826.18
PA17/I2C36: U$834.P$1, U$849.18
PA17/I2C37: U$857.P$1, U$872.18
PA17/I2C38: U$880.P$1, U$895.18
PA17/I2C39: U$903.P$1, U$918.18
PA18: U$108.P$1, U$113.27
PA18/INTA: U$6.P$11, U$36.P$1, U$76.19
PA18/INTA1: U$13.P$1, U$29.19, U$31.P$11
PA18/INTA2: U$49.P$1, U$66.19, U$68.P$11
PA18/INTA3: U$73.P$1, U$90.19, U$92.P$11
PA18/INTA4: U$97.P$1, U$113.19, U$115.P$11
PA18/INTA5: U$120.P$1, U$136.19, U$138.P$11
PA18/INTA6: U$143.P$1, U$159.19, U$161.P$11
PA18/INTA7: U$166.P$1, U$182.19, U$184.P$11
PA18/INTA8: U$189.P$1, U$205.19, U$207.P$11
PA18/INTA9: U$212.P$1, U$228.19, U$230.P$11
PA18/INTA10: U$235.P$1, U$251.19, U$253.P$11
PA18/INTA11: U$258.P$1, U$274.19, U$276.P$11
PA18/INTA12: U$281.P$1, U$297.19, U$299.P$11
PA18/INTA13: U$304.P$1, U$320.19, U$322.P$11
PA18/INTA14: U$327.P$1, U$343.19, U$345.P$11
PA18/INTA15: U$350.P$1, U$366.19, U$368.P$11
PA18/INTA16: U$373.P$1, U$389.19, U$391.P$11
PA18/INTA17: U$396.P$1, U$412.19, U$414.P$11
PA18/INTA18: U$419.P$1, U$435.19, U$437.P$11
PA18/INTA19: U$442.P$1, U$458.19, U$460.P$11
PA18/INTA20: U$465.P$1, U$481.19, U$483.P$11
PA18/INTA21: U$488.P$1, U$504.19, U$506.P$11
PA18/INTA22: U$511.P$1, U$527.19, U$529.P$11
PA18/INTA23: U$534.P$1, U$550.19, U$552.P$11
PA18/INTA24: U$557.P$1, U$573.19, U$575.P$11
PA18/INTA25: U$580.P$1, U$596.19, U$598.P$11
PA18/INTA26: U$603.P$1, U$619.19, U$621.P$11
PA18/INTA27: U$626.P$1, U$642.19, U$644.P$11
PA18/INTA28: U$649.P$1, U$665.19, U$667.P$11
PA18/INTA29: U$672.P$1, U$688.19, U$690.P$11
PA18/INTA30: U$695.P$1, U$711.19, U$713.P$11
PA18/INTA31: U$718.P$1, U$734.19, U$736.P$11
PA18/INTA32: U$741.P$1, U$757.19, U$759.P$11
PA18/INTA33: U$764.P$1, U$780.19, U$782.P$11
PA18/INTA34: U$787.P$1, U$803.19, U$805.P$11
PA18/INTA35: U$810.P$1, U$826.19, U$828.P$11
PA18/INTA36: U$833.P$1, U$849.19, U$851.P$11
PA18/INTA37: U$856.P$1, U$872.19, U$874.P$11
PA18/INTA38: U$879.P$1, U$895.19, U$897.P$11
PA18/INTA39: U$902.P$1, U$918.19, U$920.P$11
PA19: U$132.P$1, U$136.7
PA19/FSYNC: U$6.P$12, U$35.P$1, U$76.20
PA19/FSYNC1: U$11.P$1, U$29.20, U$31.P$12
PA19/FSYNC2: U$40.P$1, U$66.20, U$68.P$12
PA19/FSYNC3: U$72.P$1, U$90.20, U$92.P$12
PA19/FSYNC4: U$96.P$1, U$113.20, U$115.P$12
PA19/FSYNC5: U$119.P$1, U$136.20, U$138.P$12
PA19/FSYNC6: U$142.P$1, U$159.20, U$161.P$12
PA19/FSYNC7: U$165.P$1, U$182.20, U$184.P$12
PA19/FSYNC8: U$188.P$1, U$205.20, U$207.P$12
PA19/FSYNC9: U$211.P$1, U$228.20, U$230.P$12
PA19/FSYNC10: U$234.P$1, U$251.20, U$253.P$12
PA19/FSYNC11: U$257.P$1, U$274.20, U$276.P$12
PA19/FSYNC12: U$280.P$1, U$297.20, U$299.P$12
PA19/FSYNC13: U$303.P$1, U$320.20, U$322.P$12
PA19/FSYNC14: U$326.P$1, U$343.20, U$345.P$12
PA19/FSYNC15: U$349.P$1, U$366.20, U$368.P$12
PA19/FSYNC16: U$372.P$1, U$389.20, U$391.P$12
PA19/FSYNC17: U$395.P$1, U$412.20, U$414.P$12
PA19/FSYNC18: U$418.P$1, U$435.20, U$437.P$12
PA19/FSYNC19: U$441.P$1, U$458.20, U$460.P$12
PA19/FSYNC20: U$464.P$1, U$481.20, U$483.P$12
PA19/FSYNC21: U$487.P$1, U$504.20, U$506.P$12
PA19/FSYNC22: U$510.P$1, U$527.20, U$529.P$12
PA19/FSYNC23: U$533.P$1, U$550.20, U$552.P$12
PA19/FSYNC24: U$556.P$1, U$573.20, U$575.P$12
PA19/FSYNC25: U$579.P$1, U$596.20, U$598.P$12
PA19/FSYNC26: U$602.P$1, U$619.20, U$621.P$12
PA19/FSYNC27: U$625.P$1, U$642.20, U$644.P$12
PA19/FSYNC28: U$648.P$1, U$665.20, U$667.P$12
PA19/FSYNC29: U$671.P$1, U$688.20, U$690.P$12
PA19/FSYNC30: U$694.P$1, U$711.20, U$713.P$12
PA19/FSYNC31: U$717.P$1, U$734.20, U$736.P$12
PA19/FSYNC32: U$740.P$1, U$757.20, U$759.P$12
PA19/FSYNC33: U$763.P$1, U$780.20, U$782.P$12
PA19/FSYNC34: U$786.P$1, U$803.20, U$805.P$12
PA19/FSYNC35: U$809.P$1, U$826.20, U$828.P$12
PA19/FSYNC36: U$832.P$1, U$849.20, U$851.P$12
PA19/FSYNC37: U$855.P$1, U$872.20, U$874.P$12
PA19/FSYNC38: U$878.P$1, U$895.20, U$897.P$12
PA19/FSYNC39: U$901.P$1, U$918.20, U$920.P$12
PA20: U$126.P$1, U$136.8
PA21: U$130.P$1, U$136.25
PA22: U$131.P$1, U$136.27
PA23: U$155.P$1, U$159.7
PA24: U$149.P$1, U$159.8
PA24/USBDM: U$9.P$1, U$76.22, USB.2
PA24/USBDM1: U$26.P$1, U$29.22, USB1.2
PA24/USBDM2: U$63.P$1, U$66.22, USB2.2
PA24/USBDM3: U$87.P$1, U$90.22, USB3.2
PA24/USBDM4: U$110.P$1, U$113.22, USB4.2
PA24/USBDM5: U$133.P$1, U$136.22, USB5.2
PA24/USBDM6: U$156.P$1, U$159.22, USB6.2
PA24/USBDM7: U$179.P$1, U$182.22, USB7.2
PA24/USBDM8: U$202.P$1, U$205.22, USB8.2
PA24/USBDM9: U$225.P$1, U$228.22, USB9.2
PA24/USBDM10: U$248.P$1, U$251.22, USB10.2
PA24/USBDM11: U$271.P$1, U$274.22, USB11.2
PA24/USBDM12: U$294.P$1, U$297.22, USB12.2
PA24/USBDM13: U$317.P$1, U$320.22, USB13.2
PA24/USBDM14: U$340.P$1, U$343.22, USB14.2
PA24/USBDM15: U$363.P$1, U$366.22, USB15.2
PA24/USBDM16: U$386.P$1, U$389.22, USB16.2
PA24/USBDM17: U$409.P$1, U$412.22, USB17.2
PA24/USBDM18: U$432.P$1, U$435.22, USB18.2
PA24/USBDM19: U$455.P$1, U$458.22, USB19.2
PA24/USBDM20: U$478.P$1, U$481.22, USB20.2
PA24/USBDM21: U$501.P$1, U$504.22, USB21.2
PA24/USBDM22: U$524.P$1, U$527.22, USB22.2
PA24/USBDM23: U$547.P$1, U$550.22, USB23.2
PA24/USBDM24: U$570.P$1, U$573.22, USB24.2
PA24/USBDM25: U$593.P$1, U$596.22, USB25.2
PA24/USBDM26: U$616.P$1, U$619.22, USB26.2
PA24/USBDM27: U$639.P$1, U$642.22, USB27.2
PA24/USBDM28: U$662.P$1, U$665.22, USB28.2
PA24/USBDM29: U$685.P$1, U$688.22, USB29.2
PA24/USBDM30: U$708.P$1, U$711.22, USB30.2
PA24/USBDM31: U$731.P$1, U$734.22, USB31.2
PA24/USBDM32: U$754.P$1, U$757.22, USB32.2
PA24/USBDM33: U$777.P$1, U$780.22, USB33.2
PA24/USBDM34: U$800.P$1, U$803.22, USB34.2
PA24/USBDM35: U$823.P$1, U$826.22, USB35.2
PA24/USBDM36: U$846.P$1, U$849.22, USB36.2
PA24/USBDM37: U$869.P$1, U$872.22, USB37.2
PA24/USBDM38: U$892.P$1, U$895.22, USB38.2
PA24/USBDM39: U$915.P$1, U$918.22, USB39.2
PA25: U$153.P$1, U$159.25
PA25/USBDP: U$10.P$1, U$76.23, USB.3
PA25/USBDP1: U$27.P$1, U$29.23, USB1.3
PA25/USBDP2: U$64.P$1, U$66.23, USB2.3
PA25/USBDP3: U$88.P$1, U$90.23, USB3.3
PA25/USBDP4: U$111.P$1, U$113.23, USB4.3
PA25/USBDP5: U$134.P$1, U$136.23, USB5.3
PA25/USBDP6: U$157.P$1, U$159.23, USB6.3
PA25/USBDP7: U$180.P$1, U$182.23, USB7.3
PA25/USBDP8: U$203.P$1, U$205.23, USB8.3
PA25/USBDP9: U$226.P$1, U$228.23, USB9.3
PA25/USBDP10: U$249.P$1, U$251.23, USB10.3
PA25/USBDP11: U$272.P$1, U$274.23, USB11.3
PA25/USBDP12: U$295.P$1, U$297.23, USB12.3
PA25/USBDP13: U$318.P$1, U$320.23, USB13.3
PA25/USBDP14: U$341.P$1, U$343.23, USB14.3
PA25/USBDP15: U$364.P$1, U$366.23, USB15.3
PA25/USBDP16: U$387.P$1, U$389.23, USB16.3
PA25/USBDP17: U$410.P$1, U$412.23, USB17.3
PA25/USBDP18: U$433.P$1, U$435.23, USB18.3
PA25/USBDP19: U$456.P$1, U$458.23, USB19.3
PA25/USBDP20: U$479.P$1, U$481.23, USB20.3
PA25/USBDP21: U$502.P$1, U$504.23, USB21.3
PA25/USBDP22: U$525.P$1, U$527.23, USB22.3
PA25/USBDP23: U$548.P$1, U$550.23, USB23.3
PA25/USBDP24: U$571.P$1, U$573.23, USB24.3
PA25/USBDP25: U$594.P$1, U$596.23, USB25.3
PA25/USBDP26: U$617.P$1, U$619.23, USB26.3
PA25/USBDP27: U$640.P$1, U$642.23, USB27.3
PA25/USBDP28: U$663.P$1, U$665.23, USB28.3
PA25/USBDP29: U$686.P$1, U$688.23, USB29.3
PA25/USBDP30: U$709.P$1, U$711.23, USB30.3
PA25/USBDP31: U$732.P$1, U$734.23, USB31.3
PA25/USBDP32: U$755.P$1, U$757.23, USB32.3
PA25/USBDP33: U$778.P$1, U$780.23, USB33.3
PA25/USBDP34: U$801.P$1, U$803.23, USB34.3
PA25/USBDP35: U$824.P$1, U$826.23, USB35.3
PA25/USBDP36: U$847.P$1, U$849.23, USB36.3
PA25/USBDP37: U$870.P$1, U$872.23, USB37.3
PA25/USBDP38: U$893.P$1, U$895.23, USB38.3
PA25/USBDP39: U$916.P$1, U$918.23, USB39.3
PA26: U$154.P$1, U$159.27
PA27: U$7.P$1, U$76.25
PA28: U$48.P$1, U$76.27
PA29: U$178.P$1, U$182.7
PA30: U$172.P$1, U$182.8
PA30/SWCLK: R4.1, U$46.P$1, U$76.31
PA30/SWCLK1: R6.1, U$21.P$1, U$29.31
PA30/SWCLK2: R13.1, U$58.P$1, U$66.31
PA30/SWCLK3: R18.1, U$82.P$1, U$90.31
PA30/SWCLK4: R23.1, U$105.P$1, U$113.31
PA30/SWCLK5: R28.1, U$128.P$1, U$136.31
PA30/SWCLK6: R33.1, U$151.P$1, U$159.31
PA30/SWCLK7: R38.1, U$174.P$1, U$182.31
PA30/SWCLK8: R43.1, U$197.P$1, U$205.31
PA30/SWCLK9: R48.1, U$220.P$1, U$228.31
PA30/SWCLK10: R53.1, U$243.P$1, U$251.31
PA30/SWCLK11: R58.1, U$266.P$1, U$274.31
PA30/SWCLK12: R63.1, U$289.P$1, U$297.31
PA30/SWCLK13: R68.1, U$312.P$1, U$320.31
PA30/SWCLK14: R73.1, U$335.P$1, U$343.31
PA30/SWCLK15: R78.1, U$358.P$1, U$366.31
PA30/SWCLK16: R83.1, U$381.P$1, U$389.31
PA30/SWCLK17: R88.1, U$404.P$1, U$412.31
PA30/SWCLK18: R93.1, U$427.P$1, U$435.31
PA30/SWCLK19: R98.1, U$450.P$1, U$458.31
PA30/SWCLK20: R103.1, U$473.P$1, U$481.31
PA30/SWCLK21: R108.1, U$496.P$1, U$504.31
PA30/SWCLK22: R113.1, U$519.P$1, U$527.31
PA30/SWCLK23: R118.1, U$542.P$1, U$550.31
PA30/SWCLK24: R123.1, U$565.P$1, U$573.31
PA30/SWCLK25: R128.1, U$588.P$1, U$596.31
PA30/SWCLK26: R133.1, U$611.P$1, U$619.31
PA30/SWCLK27: R138.1, U$634.P$1, U$642.31
PA30/SWCLK28: R143.1, U$657.P$1, U$665.31
PA30/SWCLK29: R148.1, U$680.P$1, U$688.31
PA30/SWCLK30: R153.1, U$703.P$1, U$711.31
PA30/SWCLK31: R158.1, U$726.P$1, U$734.31
PA30/SWCLK32: R163.1, U$749.P$1, U$757.31
PA30/SWCLK33: R168.1, U$772.P$1, U$780.31
PA30/SWCLK34: R173.1, U$795.P$1, U$803.31
PA30/SWCLK35: R178.1, U$818.P$1, U$826.31
PA30/SWCLK36: R183.1, U$841.P$1, U$849.31
PA30/SWCLK37: R188.1, U$864.P$1, U$872.31
PA30/SWCLK38: R193.1, U$887.P$1, U$895.31
PA30/SWCLK39: R198.1, U$910.P$1, U$918.31
PA31: U$176.P$1, U$182.25
PA31/SWDIO: U$47.P$1, U$76.32
PA31/SWDIO1: U$22.P$1, U$29.32
PA31/SWDIO2: U$59.P$1, U$66.32
PA31/SWDIO3: U$83.P$1, U$90.32
PA31/SWDIO4: U$106.P$1, U$113.32
PA31/SWDIO5: U$129.P$1, U$136.32
PA31/SWDIO6: U$152.P$1, U$159.32
PA31/SWDIO7: U$175.P$1, U$182.32
PA31/SWDIO8: U$198.P$1, U$205.32
PA31/SWDIO9: U$221.P$1, U$228.32
PA31/SWDIO10: U$244.P$1, U$251.32
PA31/SWDIO11: U$267.P$1, U$274.32
PA31/SWDIO12: U$290.P$1, U$297.32
PA31/SWDIO13: U$313.P$1, U$320.32
PA31/SWDIO14: U$336.P$1, U$343.32
PA31/SWDIO15: U$359.P$1, U$366.32
PA31/SWDIO16: U$382.P$1, U$389.32
PA31/SWDIO17: U$405.P$1, U$412.32
PA31/SWDIO18: U$428.P$1, U$435.32
PA31/SWDIO19: U$451.P$1, U$458.32
PA31/SWDIO20: U$474.P$1, U$481.32
PA31/SWDIO21: U$497.P$1, U$504.32
PA31/SWDIO22: U$520.P$1, U$527.32
PA31/SWDIO23: U$543.P$1, U$550.32
PA31/SWDIO24: U$566.P$1, U$573.32
PA31/SWDIO25: U$589.P$1, U$596.32
PA31/SWDIO26: U$612.P$1, U$619.32
PA31/SWDIO27: U$635.P$1, U$642.32
PA31/SWDIO28: U$658.P$1, U$665.32
PA31/SWDIO29: U$681.P$1, U$688.32
PA31/SWDIO30: U$704.P$1, U$711.32
PA31/SWDIO31: U$727.P$1, U$734.32
PA31/SWDIO32: U$750.P$1, U$757.32
PA31/SWDIO33: U$773.P$1, U$780.32
PA31/SWDIO34: U$796.P$1, U$803.32
PA31/SWDIO35: U$819.P$1, U$826.32
PA31/SWDIO36: U$842.P$1, U$849.32
PA31/SWDIO37: U$865.P$1, U$872.32
PA31/SWDIO38: U$888.P$1, U$895.32
PA31/SWDIO39: U$911.P$1, U$918.32
PA32: U$177.P$1, U$182.27
PA33: U$201.P$1, U$205.7
PA34: U$195.P$1, U$205.8
PA35: U$199.P$1, U$205.25
PA36: U$200.P$1, U$205.27
PA37: U$224.P$1, U$228.7
PA38: U$218.P$1, U$228.8
PA39: U$222.P$1, U$228.25
PA40: U$223.P$1, U$228.27
PA41: U$247.P$1, U$251.7
PA42: U$241.P$1, U$251.8
PA43: U$245.P$1, U$251.25
PA44: U$246.P$1, U$251.27
PA45: U$270.P$1, U$274.7
PA46: U$264.P$1, U$274.8
PA47: U$268.P$1, U$274.25
PA48: U$269.P$1, U$274.27
PA49: U$293.P$1, U$297.7
PA50: U$287.P$1, U$297.8
PA51: U$291.P$1, U$297.25
PA52: U$292.P$1, U$297.27
PA53: U$316.P$1, U$320.7
PA54: U$310.P$1, U$320.8
PA55: U$314.P$1, U$320.25
PA56: U$315.P$1, U$320.27
PA57: U$339.P$1, U$343.7
PA58: U$333.P$1, U$343.8
PA59: U$337.P$1, U$343.25
PA60: U$338.P$1, U$343.27
PA61: U$362.P$1, U$366.7
PA62: U$356.P$1, U$366.8
PA63: U$360.P$1, U$366.25
PA64: U$361.P$1, U$366.27
PA65: U$385.P$1, U$389.7
PA66: U$379.P$1, U$389.8
PA67: U$383.P$1, U$389.25
PA68: U$384.P$1, U$389.27
PA69: U$408.P$1, U$412.7
PA70: U$402.P$1, U$412.8
PA71: U$406.P$1, U$412.25
PA72: U$407.P$1, U$412.27
PA73: U$431.P$1, U$435.7
PA74: U$425.P$1, U$435.8
PA75: U$429.P$1, U$435.25
PA76: U$430.P$1, U$435.27
PA77: U$454.P$1, U$458.7
PA78: U$448.P$1, U$458.8
PA79: U$452.P$1, U$458.25
PA80: U$453.P$1, U$458.27
PA81: U$477.P$1, U$481.7
PA82: U$471.P$1, U$481.8
PA83: U$475.P$1, U$481.25
PA84: U$476.P$1, U$481.27
PA85: U$500.P$1, U$504.7
PA86: U$494.P$1, U$504.8
PA87: U$498.P$1, U$504.25
PA88: U$499.P$1, U$504.27
PA89: U$523.P$1, U$527.7
PA90: U$517.P$1, U$527.8
PA91: U$521.P$1, U$527.25
PA92: U$522.P$1, U$527.27
PA93: U$546.P$1, U$550.7
PA94: U$540.P$1, U$550.8
PA95: U$544.P$1, U$550.25
PA96: U$545.P$1, U$550.27
PA97: U$569.P$1, U$573.7
PA98: U$563.P$1, U$573.8
PA99: U$567.P$1, U$573.25
PA100: U$568.P$1, U$573.27
PA101: U$592.P$1, U$596.7
PA102: U$586.P$1, U$596.8
PA103: U$590.P$1, U$596.25
PA104: U$591.P$1, U$596.27
PA105: U$615.P$1, U$619.7
PA106: U$609.P$1, U$619.8
PA107: U$613.P$1, U$619.25
PA108: U$614.P$1, U$619.27
PA109: U$638.P$1, U$642.7
PA110: U$632.P$1, U$642.8
PA111: U$636.P$1, U$642.25
PA112: U$637.P$1, U$642.27
PA113: U$661.P$1, U$665.7
PA114: U$655.P$1, U$665.8
PA115: U$659.P$1, U$665.25
PA116: U$660.P$1, U$665.27
PA117: U$684.P$1, U$688.7
PA118: U$678.P$1, U$688.8
PA119: U$682.P$1, U$688.25
PA120: U$683.P$1, U$688.27
PA121: U$707.P$1, U$711.7
PA122: U$701.P$1, U$711.8
PA123: U$705.P$1, U$711.25
PA124: U$706.P$1, U$711.27
PA125: U$730.P$1, U$734.7
PA126: U$724.P$1, U$734.8
PA127: U$728.P$1, U$734.25
PA128: U$729.P$1, U$734.27
PA129: U$753.P$1, U$757.7
PA130: U$747.P$1, U$757.8
PA131: U$751.P$1, U$757.25
PA132: U$752.P$1, U$757.27
PA133: U$776.P$1, U$780.7
PA134: U$770.P$1, U$780.8
PA135: U$774.P$1, U$780.25
PA136: U$775.P$1, U$780.27
PA137: U$799.P$1, U$803.7
PA138: U$793.P$1, U$803.8
PA139: U$797.P$1, U$803.25
PA140: U$798.P$1, U$803.27
PA141: U$822.P$1, U$826.7
PA142: U$816.P$1, U$826.8
PA143: U$820.P$1, U$826.25
PA144: U$821.P$1, U$826.27
PA145: U$845.P$1, U$849.7
PA146: U$839.P$1, U$849.8
PA147: U$843.P$1, U$849.25
PA148: U$844.P$1, U$849.27
PA149: U$868.P$1, U$872.7
PA150: U$862.P$1, U$872.8
PA151: U$866.P$1, U$872.25
PA152: U$867.P$1, U$872.27
PA153: U$891.P$1, U$895.7
PA154: U$885.P$1, U$895.8
PA155: U$889.P$1, U$895.25
PA156: U$890.P$1, U$895.27
PA157: U$914.P$1, U$918.7
PA158: U$908.P$1, U$918.8
PA159: U$912.P$1, U$918.25
PA160: U$913.P$1, U$918.27
RESET: C1.1, R1.2, R2.1, U$45.P$1, U$76.26
RESET1: C18.1, R3.2, R5.1, U$20.P$1, U$29.26
RESET2: C47.1, R11.2, R12.1, U$57.P$1, U$66.26
RESET3: C70.1, R16.2, R17.1, U$81.P$1, U$90.26
RESET4: C93.1, R21.2, R22.1, U$104.P$1, U$113.26
RESET5: C116.1, R26.2, R27.1, U$127.P$1, U$136.26
RESET6: C139.1, R31.2, R32.1, U$150.P$1, U$159.26
RESET7: C162.1, R36.2, R37.1, U$173.P$1, U$182.26
RESET8: C185.1, R41.2, R42.1, U$196.P$1, U$205.26
RESET9: C208.1, R46.2, R47.1, U$219.P$1, U$228.26
RESET10: C231.1, R51.2, R52.1, U$242.P$1, U$251.26
RESET11: C254.1, R56.2, R57.1, U$265.P$1, U$274.26
RESET12: C277.1, R61.2, R62.1, U$288.P$1, U$297.26
RESET13: C300.1, R66.2, R67.1, U$311.P$1, U$320.26
RESET14: C323.1, R71.2, R72.1, U$334.P$1, U$343.26
RESET15: C346.1, R76.2, R77.1, U$357.P$1, U$366.26
RESET16: C369.1, R81.2, R82.1, U$380.P$1, U$389.26
RESET17: C392.1, R86.2, R87.1, U$403.P$1, U$412.26
RESET18: C415.1, R91.2, R92.1, U$426.P$1, U$435.26
RESET19: C438.1, R96.2, R97.1, U$449.P$1, U$458.26
RESET20: C461.1, R101.2, R102.1, U$472.P$1, U$481.26
RESET21: C484.1, R106.2, R107.1, U$495.P$1, U$504.26
RESET22: C507.1, R111.2, R112.1, U$518.P$1, U$527.26
RESET23: C530.1, R116.2, R117.1, U$541.P$1, U$550.26
RESET24: C553.1, R121.2, R122.1, U$564.P$1, U$573.26
RESET25: C576.1, R126.2, R127.1, U$587.P$1, U$596.26
RESET26: C599.1, R131.2, R132.1, U$610.P$1, U$619.26
RESET27: C622.1, R136.2, R137.1, U$633.P$1, U$642.26
RESET28: C645.1, R141.2, R142.1, U$656.P$1, U$665.26
RESET29: C668.1, R146.2, R147.1, U$679.P$1, U$688.26
RESET30: C691.1, R151.2, R152.1, U$702.P$1, U$711.26
RESET31: C714.1, R156.2, R157.1, U$725.P$1, U$734.26
RESET32: C737.1, R161.2, R162.1, U$748.P$1, U$757.26
RESET33: C760.1, R166.2, R167.1, U$771.P$1, U$780.26
RESET34: C783.1, R171.2, R172.1, U$794.P$1, U$803.26
RESET35: C806.1, R176.2, R177.1, U$817.P$1, U$826.26
RESET36: C829.1, R181.2, R182.1, U$840.P$1, U$849.26
RESET37: C852.1, R186.2, R187.1, U$863.P$1, U$872.26
RESET38: C875.1, R191.2, R192.1, U$886.P$1, U$895.26
RESET39: C898.1, R196.2, R197.1, U$909.P$1, U$918.26
RFN: C11.1, U$76.13
RFN1: C39.1, U$29.13
RFN2: C62.1, U$66.13
RFN3: C85.1, U$90.13
RFN4: C108.1, U$113.13
RFN5: C131.1, U$136.13
RFN6: C154.1, U$159.13
RFN7: C177.1, U$182.13
RFN8: C200.1, U$205.13
RFN9: C223.1, U$228.13
RFN10: C246.1, U$251.13
RFN11: C269.1, U$274.13
RFN12: C292.1, U$297.13
RFN13: C315.1, U$320.13
RFN14: C338.1, U$343.13
RFN15: C361.1, U$366.13
RFN16: C384.1, U$389.13
RFN17: C407.1, U$412.13
RFN18: C430.1, U$435.13
RFN19: C453.1, U$458.13
RFN20: C476.1, U$481.13
RFN21: C499.1, U$504.13
RFN22: C522.1, U$527.13
RFN23: C545.1, U$550.13
RFN24: C568.1, U$573.13
RFN25: C591.1, U$596.13
RFN26: C614.1, U$619.13
RFN27: C637.1, U$642.13
RFN28: C660.1, U$665.13
RFN29: C683.1, U$688.13
RFN30: C706.1, U$711.13
RFN31: C729.1, U$734.13
RFN32: C752.1, U$757.13
RFN33: C775.1, U$780.13
RFN34: C798.1, U$803.13
RFN35: C821.1, U$826.13
RFN36: C844.1, U$849.13
RFN37: C867.1, U$872.13
RFN38: C890.1, U$895.13
RFN39: C913.1, U$918.13
RFP: C12.1, U$76.12
RFP1: C40.1, U$29.12
RFP2: C63.1, U$66.12
RFP3: C86.1, U$90.12
RFP4: C109.1, U$113.12
RFP5: C132.1, U$136.12
RFP6: C155.1, U$159.12
RFP7: C178.1, U$182.12
RFP8: C201.1, U$205.12
RFP9: C224.1, U$228.12
RFP10: C247.1, U$251.12
RFP11: C270.1, U$274.12
RFP12: C293.1, U$297.12
RFP13: C316.1, U$320.12
RFP14: C339.1, U$343.12
RFP15: C362.1, U$366.12
RFP16: C385.1, U$389.12
RFP17: C408.1, U$412.12
RFP18: C431.1, U$435.12
RFP19: C454.1, U$458.12
RFP20: C477.1, U$481.12
RFP21: C500.1, U$504.12
RFP22: C523.1, U$527.12
RFP23: C546.1, U$550.12
RFP24: C569.1, U$573.12
RFP25: C592.1, U$596.12
RFP26: C615.1, U$619.12
RFP27: C638.1, U$642.12
RFP28: C661.1, U$665.12
RFP29: C684.1, U$688.12
RFP30: C707.1, U$711.12
RFP31: C730.1, U$734.12
RFP32: C753.1, U$757.12
RFP33: C776.1, U$780.12
RFP34: C799.1, U$803.12
RFP35: C822.1, U$826.12
RFP36: C845.1, U$849.12
RFP37: C868.1, U$872.12
RFP38: C891.1, U$895.12
RFP39: C914.1, U$918.12
VDDANA: C8.1, C22.2, L6.2, U$76.4
VDDANA1: C26.1, C35.2, L1.2, U$29.4
VDDANA2: C53.1, C58.2, L2.2, U$66.4
VDDANA3: C76.1, C81.2, L3.2, U$90.4
VDDANA4: C99.1, C104.2, L4.2, U$113.4
VDDANA5: C122.1, C127.2, L5.2, U$136.4
VDDANA6: C145.1, C150.2, L7.2, U$159.4
VDDANA7: C168.1, C173.2, L8.2, U$182.4
VDDANA8: C191.1, C196.2, L9.2, U$205.4
VDDANA9: C214.1, C219.2, L10.2, U$228.4
VDDANA10: C237.1, C242.2, L11.2, U$251.4
VDDANA11: C260.1, C265.2, L12.2, U$274.4
VDDANA12: C283.1, C288.2, L13.2, U$297.4
VDDANA13: C306.1, C311.2, L14.2, U$320.4
VDDANA14: C329.1, C334.2, L15.2, U$343.4
VDDANA15: C352.1, C357.2, L16.2, U$366.4
VDDANA16: C375.1, C380.2, L17.2, U$389.4
VDDANA17: C398.1, C403.2, L18.2, U$412.4
VDDANA18: C421.1, C426.2, L19.2, U$435.4
VDDANA19: C444.1, C449.2, L20.2, U$458.4
VDDANA20: C467.1, C472.2, L21.2, U$481.4
VDDANA21: C490.1, C495.2, L22.2, U$504.4
VDDANA22: C513.1, C518.2, L23.2, U$527.4
VDDANA23: C536.1, C541.2, L24.2, U$550.4
VDDANA24: C559.1, C564.2, L25.2, U$573.4
VDDANA25: C582.1, C587.2, L26.2, U$596.4
VDDANA26: C605.1, C610.2, L27.2, U$619.4
VDDANA27: C628.1, C633.2, L28.2, U$642.4
VDDANA28: C651.1, C656.2, L29.2, U$665.4
VDDANA29: C674.1, C679.2, L30.2, U$688.4
VDDANA30: C697.1, C702.2, L31.2, U$711.4
VDDANA31: C720.1, C725.2, L32.2, U$734.4
VDDANA32: C743.1, C748.2, L33.2, U$757.4
VDDANA33: C766.1, C771.2, L34.2, U$780.4
VDDANA34: C789.1, C794.2, L35.2, U$803.4
VDDANA35: C812.1, C817.2, L36.2, U$826.4
VDDANA36: C835.1, C840.2, L37.2, U$849.4
VDDANA37: C858.1, C863.2, L38.2, U$872.4
VDDANA38: C881.1, C886.2, L39.2, U$895.4
VDDANA39: C904.1, C909.2, L40.2, U$918.4
VDDCORE: C9.1, U$76.29
VDDCORE1: C27.1, U$29.29
VDDCORE2: C54.1, U$66.29
VDDCORE3: C77.1, U$90.29
VDDCORE4: C100.1, U$113.29
VDDCORE5: C123.1, U$136.29
VDDCORE6: C146.1, U$159.29
VDDCORE7: C169.1, U$182.29
VDDCORE8: C192.1, U$205.29
VDDCORE9: C215.1, U$228.29
VDDCORE10: C238.1, U$251.29
VDDCORE11: C261.1, U$274.29
VDDCORE12: C284.1, U$297.29
VDDCORE13: C307.1, U$320.29
VDDCORE14: C330.1, U$343.29
VDDCORE15: C353.1, U$366.29
VDDCORE16: C376.1, U$389.29
VDDCORE17: C399.1, U$412.29
VDDCORE18: C422.1, U$435.29
VDDCORE19: C445.1, U$458.29
VDDCORE20: C468.1, U$481.29
VDDCORE21: C491.1, U$504.29
VDDCORE22: C514.1, U$527.29
VDDCORE23: C537.1, U$550.29
VDDCORE24: C560.1, U$573.29
VDDCORE25: C583.1, U$596.29
VDDCORE26: C606.1, U$619.29
VDDCORE27: C629.1, U$642.29
VDDCORE28: C652.1, U$665.29
VDDCORE29: C675.1, U$688.29
VDDCORE30: C698.1, U$711.29
VDDCORE31: C721.1, U$734.29
VDDCORE32: C744.1, U$757.29
VDDCORE33: C767.1, U$780.29
VDDCORE34: C790.1, U$803.29
VDDCORE35: C813.1, U$826.29
VDDCORE36: C836.1, U$849.29
VDDCORE37: C859.1, U$872.29
VDDCORE38: C882.1, U$895.29
VDDCORE39: C905.1, U$918.29
VIN: C6.1, C7.1, LDO_VREG.VIN, U$1.P$1, USB.1
VIN1: C23.1, C24.1, LDO_VREG1.VIN, U$3.P$1, USB1.1
VIN2: C50.1, C51.1, LDO_VREG2.VIN, U$32.P$1, USB2.1
VIN3: C73.1, C74.1, LDO_VREG3.VIN, U$69.P$1, USB3.1
VIN4: C96.1, C97.1, LDO_VREG4.VIN, U$93.P$1, USB4.1
VIN5: C119.1, C120.1, LDO_VREG5.VIN, U$116.P$1, USB5.1
VIN6: C142.1, C143.1, LDO_VREG6.VIN, U$139.P$1, USB6.1
VIN7: C165.1, C166.1, LDO_VREG7.VIN, U$162.P$1, USB7.1
VIN8: C188.1, C189.1, LDO_VREG8.VIN, U$185.P$1, USB8.1
VIN9: C211.1, C212.1, LDO_VREG9.VIN, U$208.P$1, USB9.1
VIN10: C234.1, C235.1, LDO_VREG10.VIN, U$231.P$1, USB10.1
VIN11: C257.1, C258.1, LDO_VREG11.VIN, U$254.P$1, USB11.1
VIN12: C280.1, C281.1, LDO_VREG12.VIN, U$277.P$1, USB12.1
VIN13: C303.1, C304.1, LDO_VREG13.VIN, U$300.P$1, USB13.1
VIN14: C326.1, C327.1, LDO_VREG14.VIN, U$323.P$1, USB14.1
VIN15: C349.1, C350.1, LDO_VREG15.VIN, U$346.P$1, USB15.1
VIN16: C372.1, C373.1, LDO_VREG16.VIN, U$369.P$1, USB16.1
VIN17: C395.1, C396.1, LDO_VREG17.VIN, U$392.P$1, USB17.1
VIN18: C418.1, C419.1, LDO_VREG18.VIN, U$415.P$1, USB18.1
VIN19: C441.1, C442.1, LDO_VREG19.VIN, U$438.P$1, USB19.1
VIN20: C464.1, C465.1, LDO_VREG20.VIN, U$461.P$1, USB20.1
VIN21: C487.1, C488.1, LDO_VREG21.VIN, U$484.P$1, USB21.1
VIN22: C510.1, C511.1, LDO_VREG22.VIN, U$507.P$1, USB22.1
VIN23: C533.1, C534.1, LDO_VREG23.VIN, U$530.P$1, USB23.1
VIN24: C556.1, C557.1, LDO_VREG24.VIN, U$553.P$1, USB24.1
VIN25: C579.1, C580.1, LDO_VREG25.VIN, U$576.P$1, USB25.1
VIN26: C602.1, C603.1, LDO_VREG26.VIN, U$599.P$1, USB26.1
VIN27: C625.1, C626.1, LDO_VREG27.VIN, U$622.P$1, USB27.1
VIN28: C648.1, C649.1, LDO_VREG28.VIN, U$645.P$1, USB28.1
VIN29: C671.1, C672.1, LDO_VREG29.VIN, U$668.P$1, USB29.1
VIN30: C694.1, C695.1, LDO_VREG30.VIN, U$691.P$1, USB30.1
VIN31: C717.1, C718.1, LDO_VREG31.VIN, U$714.P$1, USB31.1
VIN32: C740.1, C741.1, LDO_VREG32.VIN, U$737.P$1, USB32.1
VIN33: C763.1, C764.1, LDO_VREG33.VIN, U$760.P$1, USB33.1
VIN34: C786.1, C787.1, LDO_VREG34.VIN, U$783.P$1, USB34.1
VIN35: C809.1, C810.1, LDO_VREG35.VIN, U$806.P$1, USB35.1
VIN36: C832.1, C833.1, LDO_VREG36.VIN, U$829.P$1, USB36.1
VIN37: C855.1, C856.1, LDO_VREG37.VIN, U$852.P$1, USB37.1
VIN38: C878.1, C879.1, LDO_VREG38.VIN, U$875.P$1, USB38.1
VIN39: C901.1, C902.1, LDO_VREG39.VIN, U$898.P$1, USB39.1
XTALIN: C14.2, SER3628CT-ND.1, U$76.2
XTALIN1: C42.2, SER3628CT-ND1.1, U$29.2
XTALIN2: C65.2, SER3628CT-ND2.1, U$66.2
XTALIN3: C88.2, SER3628CT-ND3.1, U$90.2
XTALIN4: C111.2, SER3628CT-ND4.1, U$113.2
XTALIN5: C134.2, SER3628CT-ND5.1, U$136.2
XTALIN6: C157.2, SER3628CT-ND6.1, U$159.2
XTALIN7: C180.2, SER3628CT-ND7.1, U$182.2
XTALIN8: C203.2, SER3628CT-ND8.1, U$205.2
XTALIN9: C226.2, SER3628CT-ND9.1, U$228.2
XTALIN10: C249.2, SER3628CT-ND10.1, U$251.2
XTALIN11: C272.2, SER3628CT-ND11.1, U$274.2
XTALIN12: C295.2, SER3628CT-ND12.1, U$297.2
XTALIN13: C318.2, SER3628CT-ND13.1, U$320.2
XTALIN14: C341.2, SER3628CT-ND14.1, U$343.2
XTALIN15: C364.2, SER3628CT-ND15.1, U$366.2
XTALIN16: C387.2, SER3628CT-ND16.1, U$389.2
XTALIN17: C410.2, SER3628CT-ND17.1, U$412.2
XTALIN18: C433.2, SER3628CT-ND18.1, U$435.2
XTALIN19: C456.2, SER3628CT-ND19.1, U$458.2
XTALIN20: C479.2, SER3628CT-ND20.1, U$481.2
XTALIN21: C502.2, SER3628CT-ND21.1, U$504.2
XTALIN22: C525.2, SER3628CT-ND22.1, U$527.2
XTALIN23: C548.2, SER3628CT-ND23.1, U$550.2
XTALIN24: C571.2, SER3628CT-ND24.1, U$573.2
XTALIN25: C594.2, SER3628CT-ND25.1, U$596.2
XTALIN26: C617.2, SER3628CT-ND26.1, U$619.2
XTALIN27: C640.2, SER3628CT-ND27.1, U$642.2
XTALIN28: C663.2, SER3628CT-ND28.1, U$665.2
XTALIN29: C686.2, SER3628CT-ND29.1, U$688.2
XTALIN30: C709.2, SER3628CT-ND30.1, U$711.2
XTALIN31: C732.2, SER3628CT-ND31.1, U$734.2
XTALIN32: C755.2, SER3628CT-ND32.1, U$757.2
XTALIN33: C778.2, SER3628CT-ND33.1, U$780.2
XTALIN34: C801.2, SER3628CT-ND34.1, U$803.2
XTALIN35: C824.2, SER3628CT-ND35.1, U$826.2
XTALIN36: C847.2, SER3628CT-ND36.1, U$849.2
XTALIN37: C870.2, SER3628CT-ND37.1, U$872.2
XTALIN38: C893.2, SER3628CT-ND38.1, U$895.2
XTALIN39: C916.2, SER3628CT-ND39.1, U$918.2
XTALOUT: C15.1, SER3628CT-ND.3, U$76.1
XTALOUT1: C43.1, SER3628CT-ND1.3, U$29.1
XTALOUT2: C66.1, SER3628CT-ND2.3, U$66.1
XTALOUT3: C89.1, SER3628CT-ND3.3, U$90.1
XTALOUT4: C112.1, SER3628CT-ND4.3, U$113.1
XTALOUT5: C135.1, SER3628CT-ND5.3, U$136.1
XTALOUT6: C158.1, SER3628CT-ND6.3, U$159.1
XTALOUT7: C181.1, SER3628CT-ND7.3, U$182.1
XTALOUT8: C204.1, SER3628CT-ND8.3, U$205.1
XTALOUT9: C227.1, SER3628CT-ND9.3, U$228.1
XTALOUT10: C250.1, SER3628CT-ND10.3, U$251.1
XTALOUT11: C273.1, SER3628CT-ND11.3, U$274.1
XTALOUT12: C296.1, SER3628CT-ND12.3, U$297.1
XTALOUT13: C319.1, SER3628CT-ND13.3, U$320.1
XTALOUT14: C342.1, SER3628CT-ND14.3, U$343.1
XTALOUT15: C365.1, SER3628CT-ND15.3, U$366.1
XTALOUT16: C388.1, SER3628CT-ND16.3, U$389.1
XTALOUT17: C411.1, SER3628CT-ND17.3, U$412.1
XTALOUT18: C434.1, SER3628CT-ND18.3, U$435.1
XTALOUT19: C457.1, SER3628CT-ND19.3, U$458.1
XTALOUT20: C480.1, SER3628CT-ND20.3, U$481.1
XTALOUT21: C503.1, SER3628CT-ND21.3, U$504.1
XTALOUT22: C526.1, SER3628CT-ND22.3, U$527.1
XTALOUT23: C549.1, SER3628CT-ND23.3, U$550.1
XTALOUT24: C572.1, SER3628CT-ND24.3, U$573.1
XTALOUT25: C595.1, SER3628CT-ND25.3, U$596.1
XTALOUT26: C618.1, SER3628CT-ND26.3, U$619.1
XTALOUT27: C641.1, SER3628CT-ND27.3, U$642.1
XTALOUT28: C664.1, SER3628CT-ND28.3, U$665.1
XTALOUT29: C687.1, SER3628CT-ND29.3, U$688.1
XTALOUT30: C710.1, SER3628CT-ND30.3, U$711.1
XTALOUT31: C733.1, SER3628CT-ND31.3, U$734.1
XTALOUT32: C756.1, SER3628CT-ND32.3, U$757.1
XTALOUT33: C779.1, SER3628CT-ND33.3, U$780.1
XTALOUT34: C802.1, SER3628CT-ND34.3, U$803.1
XTALOUT35: C825.1, SER3628CT-ND35.3, U$826.1
XTALOUT36: C848.1, SER3628CT-ND36.3, U$849.1
XTALOUT37: C871.1, SER3628CT-ND37.3, U$872.1
XTALOUT38: C894.1, SER3628CT-ND38.3, U$895.1
XTALOUT39: C917.1, SER3628CT-ND39.3, U$918.1
