femtoduino/femto-beacon/Nordic_Files/nRF5x_MDK_8_5_0_GCC/nrf51802_peripherals.h

/* Copyright (c) 2015, Nordic Semiconductor ASA
 * All rights reserved.
 *
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
 *   * Neither the name of Nordic Semiconductor ASA nor the names of its
 *     contributors may be used to endorse or promote products derived from
 *     this software without specific prior written permission.
 *
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
 */

#ifndef _NRF51802_PERIPHERALS_H
#define _NRF51802_PERIPHERALS_H


/* Software Interrupts */
#define SWI_PRESENT
#define SWI_COUNT 6

/* Radio */
#define RADIO_PRESENT
#define RADIO_COUNT 1

/* Peripheral to Peripheral Interconnect */
#define PPI_PRESENT
#define PPI_COUNT 1

#define PPI_CH_NUM 16
#define PPI_GROUP_NUM 4

/* Timer/Counter */
#define TIMER_PRESENT
#define TIMER_COUNT 3

#define TIMER0_MAX_SIZE 32
#define TIMER1_MAX_SIZE 16
#define TIMER2_MAX_SIZE 16

#define TIMER0_CC_NUM 4
#define TIMER1_CC_NUM 4
#define TIMER2_CC_NUM 4

/* Real Time Counter */
#define RTC_PRESENT
#define RTC_COUNT 2

#define RTC0_CC_NUM 3
#define RTC1_CC_NUM 4

/* RNG */
#define RNG_PRESENT
#define RNG_COUNT 1

/* Watchdog Timer */
#define WDT_PRESENT
#define WDT_COUNT 1

/* Temperature Sensor */
#define TEMP_PRESENT
#define TEMP_COUNT 1

/* Serial Peripheral Interface Master */
#define SPI_PRESENT
#define SPI_COUNT 2

/* Serial Peripheral Interface Slave with DMA */
#define SPIS_PRESENT
#define SPIS_COUNT 1

/* Two Wire Interface Master */
#define TWI_PRESENT
#define TWI_COUNT 2

/* Universal Asynchronous Receiver-Transmitter */
#define UART_PRESENT
#define UART_COUNT 1

/* Quadrature Decoder */
#define QDEC_PRESENT
#define QDEC_COUNT 1

/* Analog to Digital Converter */
#define ADC_PRESENT
#define ADC_COUNT 1

/* GPIO Tasks and Events */
#define GPIOTE_PRESENT
#define GPIOTE_COUNT 1

#define GPIOTE_CH_NUM 4

/* Low Power Comparator */
#define LPCOMP_PRESENT
#define LPCOMP_COUNT 1


#endif      // _NRF51802_PERIPHERALS_H
