femtoduino/femto-beacon/Eagle_Files/FemtoBeacon_r2.0.0/Atmel_files/Atmel-8390-WIRELESS-AVR2054-Serial-Bootloader_v2_2_0/Embedded_Bootloader_src/application/avr/src/rf4ceFlash.c

/****************************************************************************//**
  \file rf4ceFlash.c

  \brief Implementation function for RF4CE OTAU.

  \author
    Atmel Corporation: http://www.atmel.com \n
    Support email: avr@atmel.com

  Copyright (c) 2008-2013, Atmel Corporation. All rights reserved.
  Licensed under Atmel's Limited License Agreement (BitCloudTM).

  \internal
  History:
    12/01/11 A. Khromykh - Created
*******************************************************************************/
/******************************************************************************
                   Includes section
******************************************************************************/
#if defined (INCLUDE_RF4CE_FUNCTIONS)

#include <types.h>
#include <bootStructure.h>
#include <sp_driver.h>
#include <flashLoader.h>
#include <rf4ceFlash.h>

/******************************************************************************
                   Define(s) section
******************************************************************************/
/** This macro saves the global interrupt status. */
#define ENTER_CRITICAL_REGION()         {uint8_t sreg = SREG; cli()
/** This macro restores the global interrupt status. */
#define LEAVE_CRITICAL_REGION()         SREG = sreg;}
#define EEPROM_BUSY_WAIT()              do{}while(EECR & (1 << EEPE))

/******************************************************************************
                   Types section
******************************************************************************/
typedef void (* AccessPoint_t)(void);

/******************************************************************************
                   Prototypes section
******************************************************************************/
#if defined(__ICCAVR__)
_Pragma("location=\"RF4CE_SECT\"") static void flash_fill_page_buffer(fill_page_buffer_req_t *param);
_Pragma("location=\"RF4CE_SECT\"") static void flash_program_page(program_page_req_t *param);
_Pragma("location=\"RF4CE_SECT\"") __noreturn static void flash_swap(swap_images_req_t *param);
_Pragma("location=\"RF4CE_SECT\"") static void flash_boot_request_handler(void);
_Pragma("location=\"RF4CE_SECT\"") static void flash_erase_page(erase_page_req_t *param);
_Pragma("location=\"RF4CE_SECT\"") static void flash_write_page(write_page_req_t *param);
#elif defined(__GNUC__)
static void flash_fill_page_buffer(fill_page_buffer_req_t *param) __attribute__((section(".rf4ce")));
static void flash_program_page(program_page_req_t *param) __attribute__((section(".rf4ce")));
static void flash_swap(swap_images_req_t *param) __attribute__((section(".rf4ce"))) __attribute__((__noreturn__));
static void flash_boot_request_handler(void) __attribute__((section(".rf4ce")));
static void flash_erase_page(erase_page_req_t *param) __attribute__((section(".rf4ce")));
static void flash_write_page(write_page_req_t *param) __attribute__((section(".rf4ce")));
#else
  #error 'Unsupported compiler.'
#endif

/******************************************************************************
                   Global variables section
******************************************************************************/
#if defined(__ICCAVR__)
__root const __farflash AccessPoint_t access_point @ (FLASHEND + 1ul - sizeof(AccessPoint_t)) = flash_boot_request_handler;
#elif defined(__GNUC__)
__attribute__((section(".access_sect"))) AccessPoint_t access_point = flash_boot_request_handler;
#ifdef ATMEGA256RFR2
__attribute__((section(".far_addr_padding_sect"))) uint8_t padding = 0x01;
#endif
#endif
/******************************************************************************
                    Implementation section
******************************************************************************/
/**************************************************************************//**
\brief Enter point to bootloader function
******************************************************************************/
static void flash_boot_request_handler(void)
{
  rf4ce_boot_req_t *request_address;
  uint16_t temp_value;

  temp_value = GPIOR1;
  temp_value <<= 8;
  temp_value |= GPIOR0;
  request_address = (rf4ce_boot_req_t *)temp_value;

  switch (request_address->request_type)
  {
    case FILL_PAGE_BUFFER:
      flash_fill_page_buffer(&request_address->common_boot_req.fill_page_buffer_req);
      break;
    case PROGRAM_PAGE:
      flash_program_page(&request_address->common_boot_req.program_page_req);
      break;
    case SWAP_IMAGE:
      flash_swap(&request_address->common_boot_req.swap_images_req);
      break;
    case ERASE_PAGE:
      flash_erase_page(&request_address->common_boot_req.erase_page_req);
      break;
    case WRITE_PAGE:
      flash_write_page(&request_address->common_boot_req.write_page_req);
      break;
    default:
      break;
  }
}

/**************************************************************************//**
\brief Fill flash buffer

\param[in] param - pointer to request parameters for page buffer filling.
******************************************************************************/
static void flash_fill_page_buffer(fill_page_buffer_req_t *param)
{
  uint16_t addr;

  for (addr = param->start_offset; addr < param->length + param->start_offset; addr += sizeof(uint16_t), param->data += sizeof(uint16_t))
  {
    // Perform word load.
    SP_LoadFlashWord(addr, *(uint16_t *)param->data);
    // Wait for SPM to finish.
    flashWaitForSPM();
  }
}

/**************************************************************************//**
\brief Store data from flash buffer to flash page

\param[in] param - pointer to request parameters for page programing.
******************************************************************************/
static void flash_program_page(program_page_req_t *param)
{
  ENTER_CRITICAL_REGION();

  EEPROM_BUSY_WAIT();
  // Perform page erase.
  SP_EraseApplicationPage(param->page_start_addr);
  // Wait for SPM to finish.
  flashWaitForSPM();
  // Perform page write.
  SP_WriteApplicationPage(param->page_start_addr);
  // Wait for SPM to finish.
  flashWaitForSPM();
  // enable rww section
  SP_RWWSectionEnable();
  // Wait for SPM to finish.
  flashWaitForSPM();

  LEAVE_CRITICAL_REGION();
}

/**************************************************************************//**
\brief Swap flash data from additional area to general area.

\param[in] param - pointer to request parameters for image swapping.
******************************************************************************/
#ifndef DISABLE_FLASH_SWAP_RF4CE_FUNCTION
static void flash_swap(swap_images_req_t *param)
{
  uint16_t current_page_number = param->image_start_addr >> PAGE_NUMBER_SHIFT;
  uint16_t data_page_number = current_page_number;
  common_boot_req_t common_boot_req;
  uint32_t page_start_addr;
  uint16_t saving_page_number = 0;
  uint8_t  data_byte[sizeof(uint16_t)];

  cli();  // Disable global interrupts

  EEPROM_BUSY_WAIT();

  while (param->image_size)
  {
    data_page_number = param->image_start_addr >> PAGE_NUMBER_SHIFT;

    if (data_page_number != current_page_number)
    {
      /* Store data from flash buffer to flash page */
      common_boot_req.program_page_req.page_start_addr = (uint32_t)saving_page_number << PAGE_NUMBER_SHIFT;
      flash_program_page(&common_boot_req.program_page_req);
      current_page_number = data_page_number;
      saving_page_number++;
    }

    page_start_addr = param->image_start_addr & PAGE_POSITION_OFFSET_MASK;
    data_byte[0] = SP_ReadInternalFlash(param->image_start_addr);
    data_byte[1] = SP_ReadInternalFlash(param->image_start_addr + 1);
    /* Fill temporary page buffer */
    common_boot_req.fill_page_buffer_req.start_offset = page_start_addr;
    common_boot_req.fill_page_buffer_req.length = sizeof(data_byte);
    common_boot_req.fill_page_buffer_req.data = data_byte;
    flash_fill_page_buffer(&common_boot_req.fill_page_buffer_req);

    param->image_start_addr += sizeof(data_byte);
    param->image_size -= sizeof(data_byte);
  }

  /* flush last page into flash */
  common_boot_req.program_page_req.page_start_addr = (uint32_t)saving_page_number << PAGE_NUMBER_SHIFT;
  flash_program_page(&common_boot_req.program_page_req);

  /* Start wdt on 16 ms and reset mcu */
  wdt_reset();
  WDTCSR |= (1 << WDCE) | (1 << WDE);
  WDTCSR = (1 << WDE);
  while(1);
}
#else
static void flash_swap(swap_images_req_t *param)
{
  (void)param;
}
#endif // DISABLE_FLASH_SWAP_RF4CE_FUNCTION

static void flash_erase_page(erase_page_req_t *param)
{
    ENTER_CRITICAL_REGION();

    EEPROM_BUSY_WAIT();

    SP_EraseApplicationPage(param->page_start_addr);
    flashWaitForSPM();  // Wait until the memory is erased.

    // Reenable RWW-section again. We need this if we want to jump back
    // to the application after bootloading.
    SP_RWWSectionEnable();
    flashWaitForSPM();

    LEAVE_CRITICAL_REGION();
}

static void flash_write_page(write_page_req_t *param)
{
    ENTER_CRITICAL_REGION();

    EEPROM_BUSY_WAIT();

    SP_WriteApplicationPage(param->page_start_addr);  // Store buffer in flash page.
    flashWaitForSPM();  // Wait until the memory is written.

    // Reenable RWW-section again. We need this if we want to jump back
    // to the application after bootloading.
    SP_RWWSectionEnable();
    flashWaitForSPM();

    LEAVE_CRITICAL_REGION();
}

#endif // defined (INCLUDE_RF4CE_FUNCTIONS)

// eof rf4ceFlash.c
