femtoduino/femto-beacon/Eagle_Files/FemtoBeacon_r2.0.0/Atmel_files/AT02430/Embedded_Bootloader_src/application/cortexm3/include/descriptors.h

/****************************************************************************//**
  \file descriptors.h

  \brief Declaration of descriptors structures.

  \author
    Atmel Corporation: http://www.atmel.com \n
    Support email: avr@atmel.com

  Copyright (c) 2008-2011, Atmel Corporation. All rights reserved.
  Licensed under Atmel's Limited License Agreement (BitCloudTM).

  \internal
  History:
    05.09.11 A. Khromykh - Created
*******************************************************************************/
#ifndef _DESCRIPTORS_H
#define _DESCRIPTORS_H

/******************************************************************************
                   Includes section
******************************************************************************/
#include <types.h>

/******************************************************************************
                   Define(s) section
******************************************************************************/
// Descriptor's type definitions.
#define DESCRIPTOR_TYPE_DEVICE           0x01
#define DESCRIPTOR_TYPE_CONFIGURATION    0x02
#define DESCRIPTOR_TYPE_INTERFACE        0x04
#define DESCRIPTOR_TYPE_DFU_FUNCTIONAL   0x21
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
